lyusupov/SoftRF/software/firmware/binaries/RP2040/README.md

```

$ picotool info -a SoftRF-firmware-v1.0-RP2040.uf2 
File SoftRF-firmware-v1.0-RP2040.uf2:

Program Information
 name:          SoftRF
 version:       1.0
 web site:      https://github.com/lyusupov/SoftRF
 description:   Multifunctional, compatible DIY general aviation proximity awareness system
 binary start:  0x10000000
 binary end:    0x100292c8

Fixed Pin Information
 0:   Console TX
 1:   Console RX
 2:   I2C SDA
 3:   I2C SCL
 4:   GNSS TX
 5:   GNSS RX
 6:   GNSS PPS
 10:  SX1262 SCK
 11:  SX1262 MOSI
 12:  SX1262 MISO
 13:  SX1262 SS
 14:  SX1262 RST
 15:  SX1262 BUSY
 22:  GNSS RST
 25:  RF ANT PWR
 29:  SX1262 DIO1

Build Information
 build date:  Mar 16 2022

```
