lyusupov/SoftRF/software/firmware/binaries/nRF52840/SoftRF/MassStorage/README.md

Suffix|Notes
---|---
.uf2| use this file in conjunction with genuine [**SoftRF Badge** enclosure](https://github.com/lyusupov/SoftRF/tree/master/case/Badge)
-180.uf2| the screen is rotated 180 degrees to fit the LilyGO case for the T-Echo board
