lyusupov/SoftRF/documents/images/2p_xcs_map.jpg

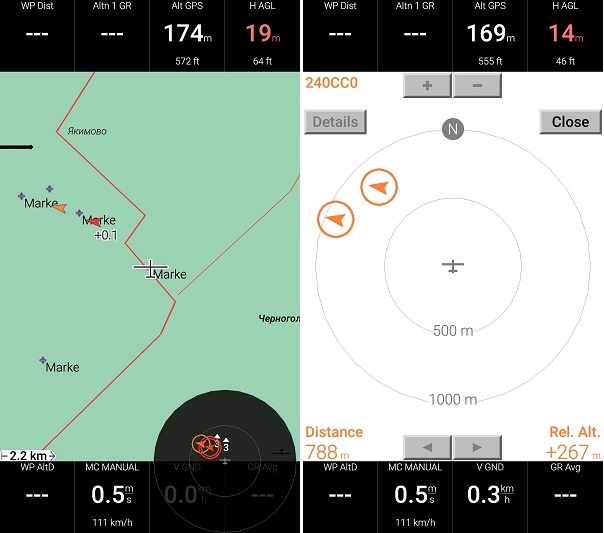
documents/images/2p_xcs_map.jpg
