lyusupov/SoftRF/documents/images/2p_xcs_monitor.jpg

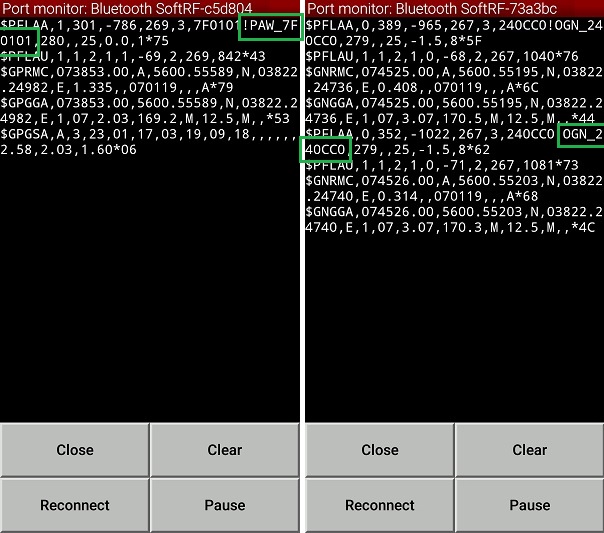
documents/images/2p_xcs_monitor.jpg
