lyusupov/SoftRF/documents/images/2p_xcs_traffic.jpg

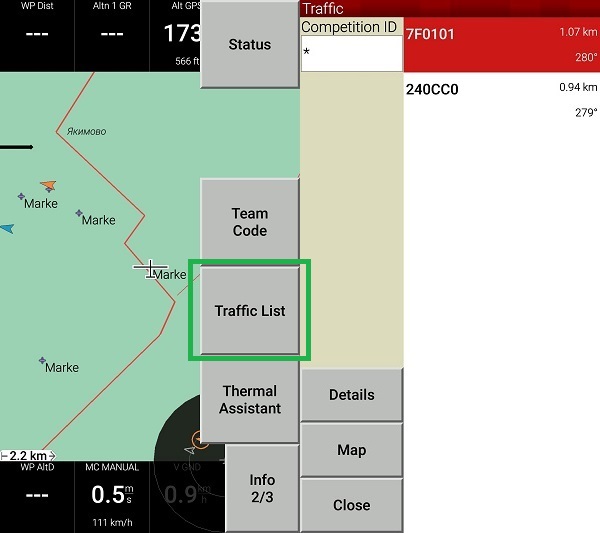
documents/images/2p_xcs_traffic.jpg
