lyusupov/SoftRF/documents/images/Airventure-1.jpg

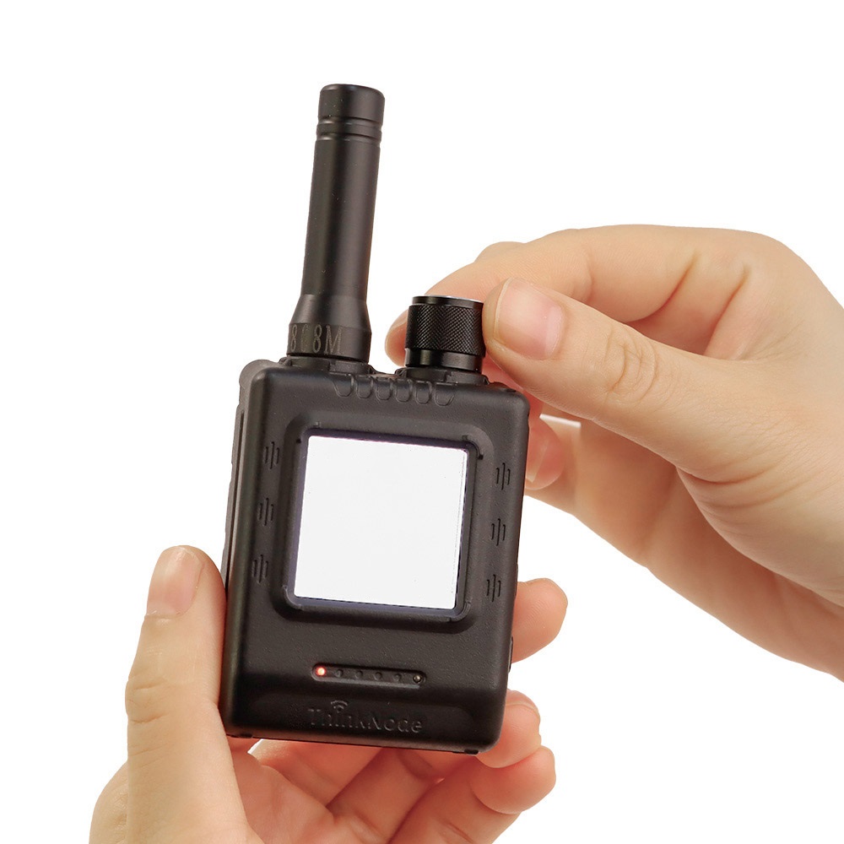
documents/images/Airventure-1.jpg
