lyusupov/SoftRF/documents/images/Airventure-2.jpg

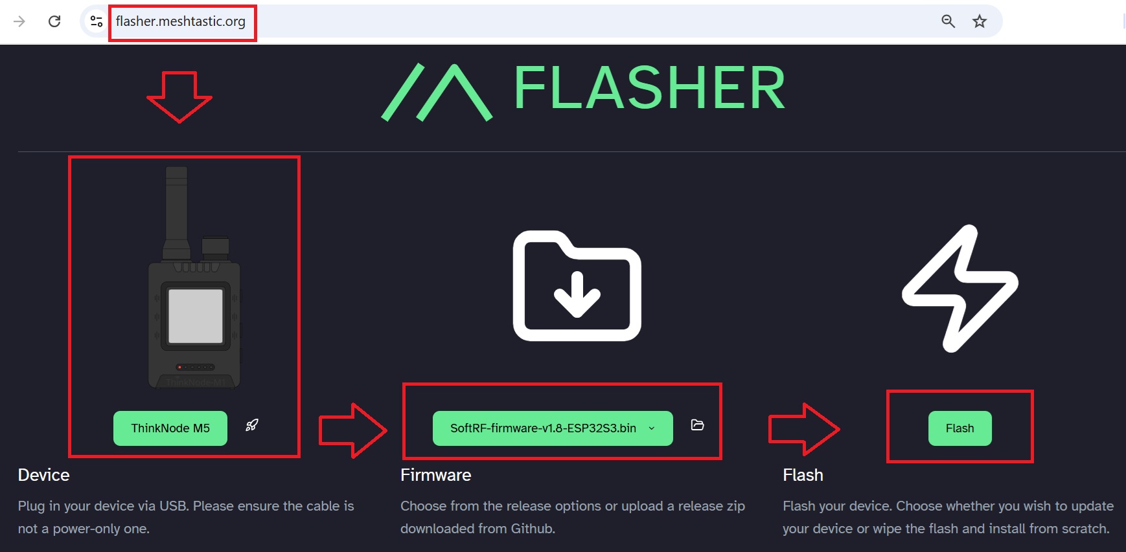
documents/images/Airventure-2.jpg
