lyusupov/SoftRF/documents/images/ant_1.jpg

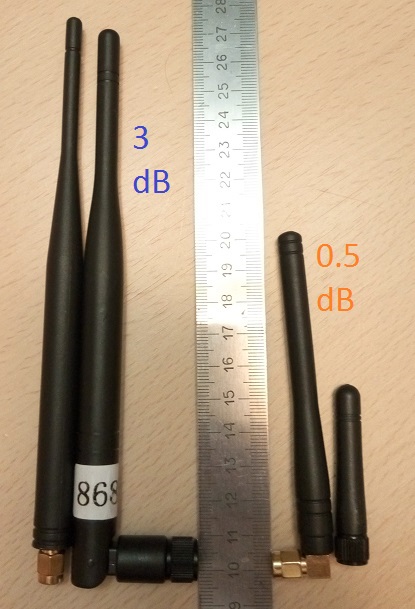
documents/images/ant_1.jpg
