lyusupov/SoftRF/documents/images/ant_2.jpg

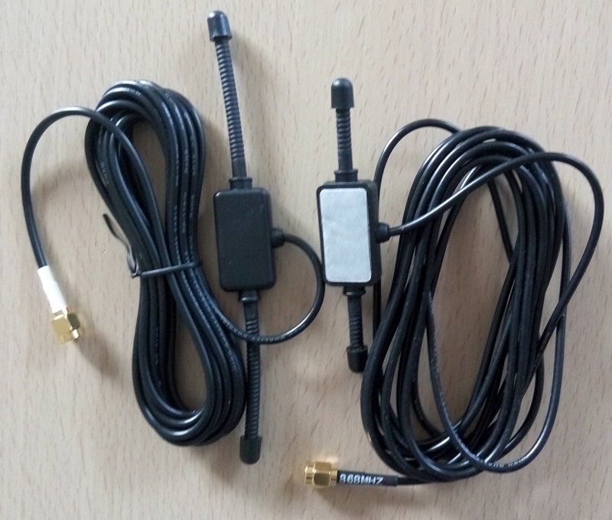
documents/images/ant_2.jpg
