lyusupov/SoftRF/documents/images/aw-snapshot.JPG

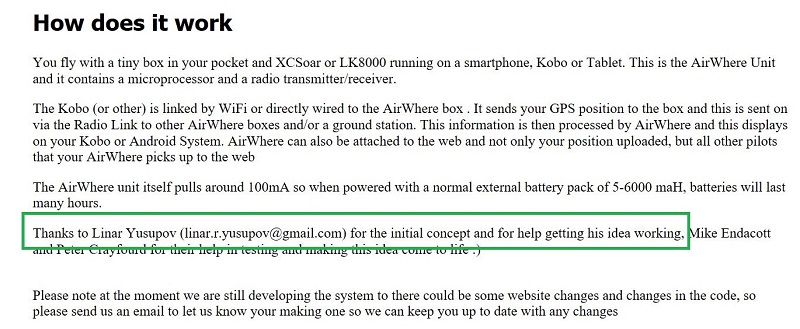
documents/images/aw-snapshot.JPG
