lyusupov/SoftRF/documents/images/BFF-1.jpg

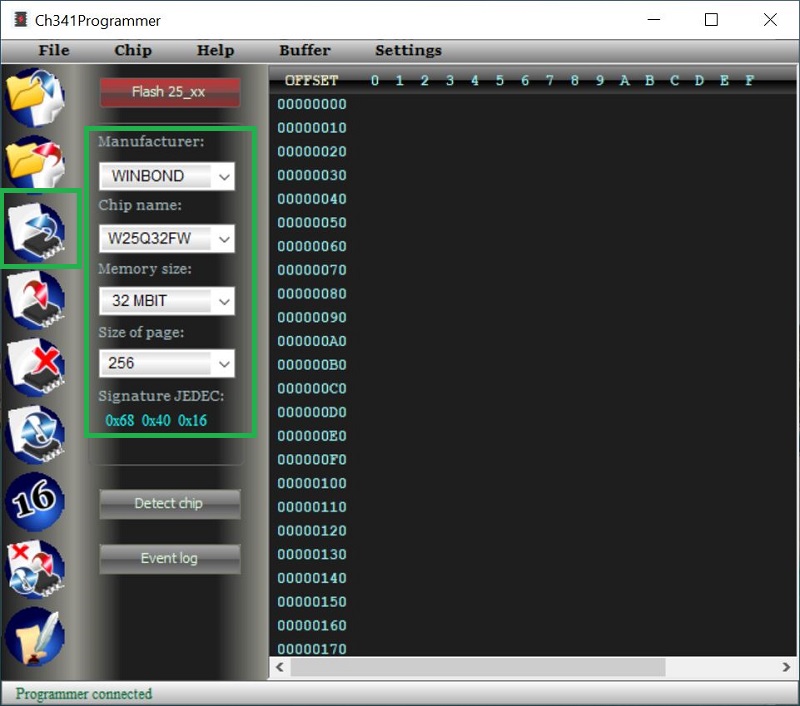
documents/images/BFF-1.jpg
