lyusupov/SoftRF/documents/images/BFF-3.jpg

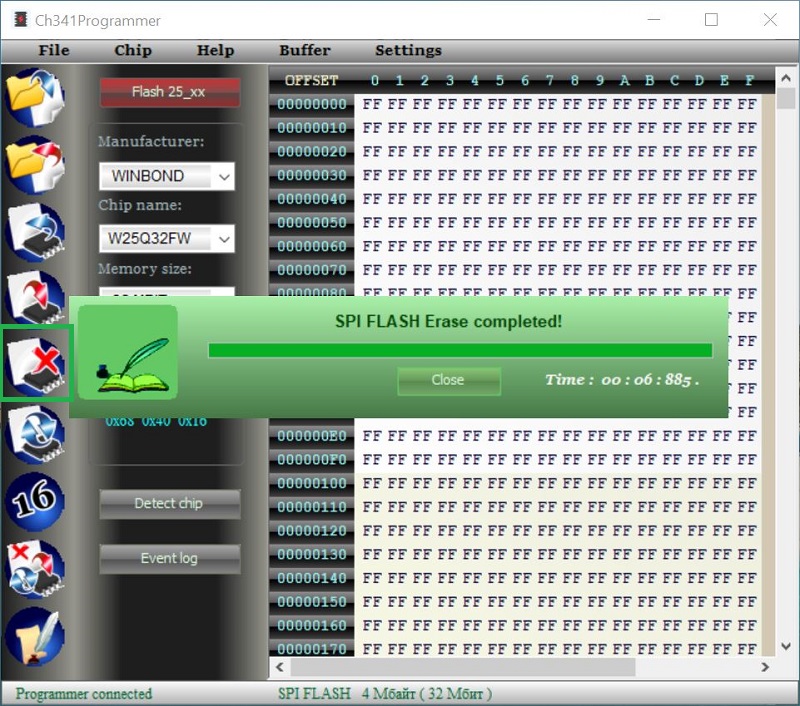
documents/images/BFF-3.jpg
