lyusupov/SoftRF/documents/images/BFF-4.jpg

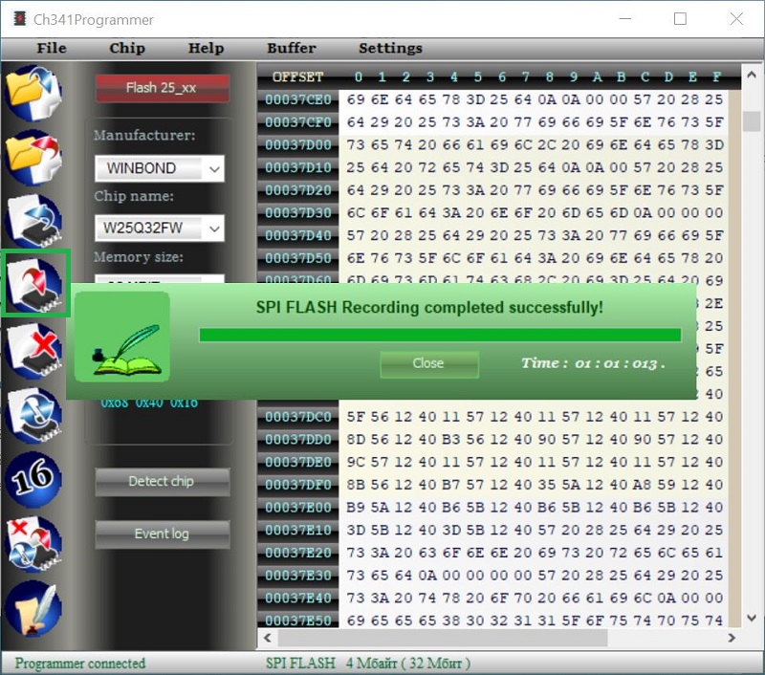
documents/images/BFF-4.jpg
