lyusupov/SoftRF/documents/images/BFF-6.jpg

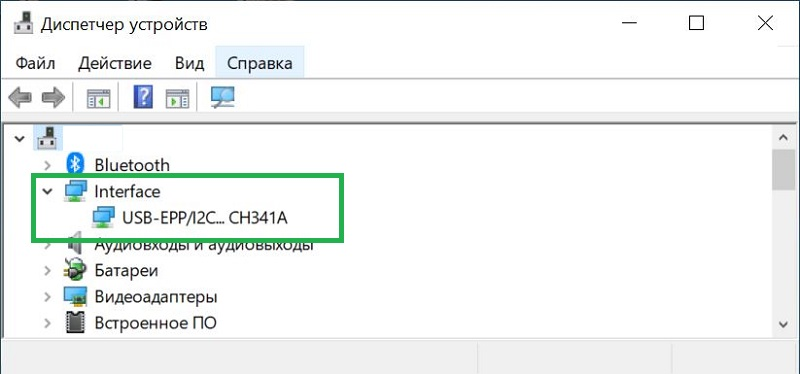
documents/images/BFF-6.jpg
