lyusupov/SoftRF/documents/images/BFF-7.jpg

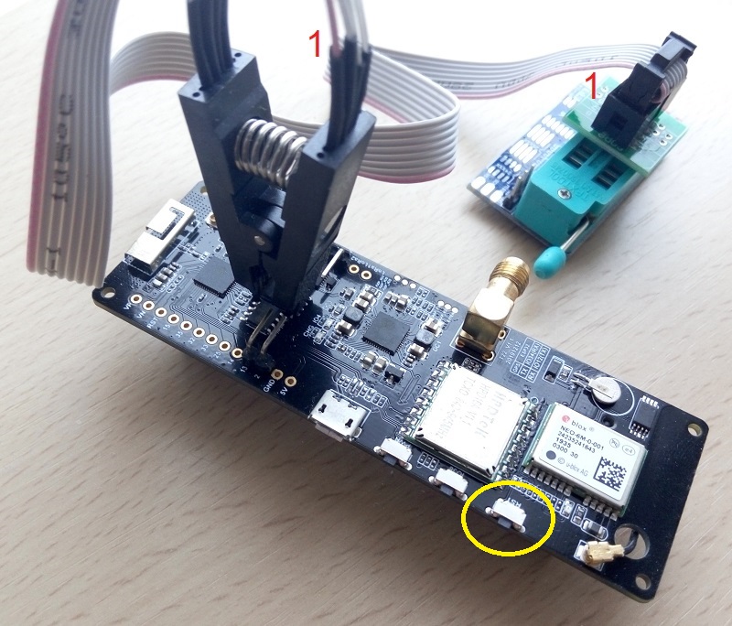
documents/images/BFF-7.jpg
