lyusupov/SoftRF/documents/images/bom/epaper-hat.jpg

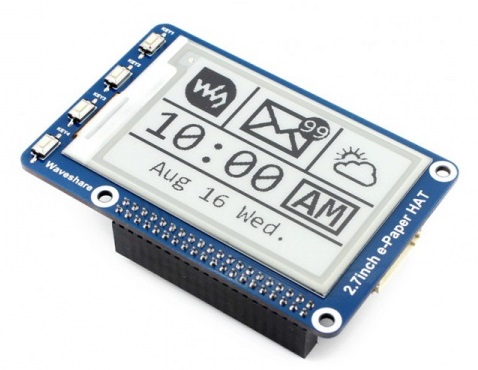
documents/images/bom/epaper-hat.jpg
