lyusupov/SoftRF/documents/images/bom/wspicoepaper27.jpg

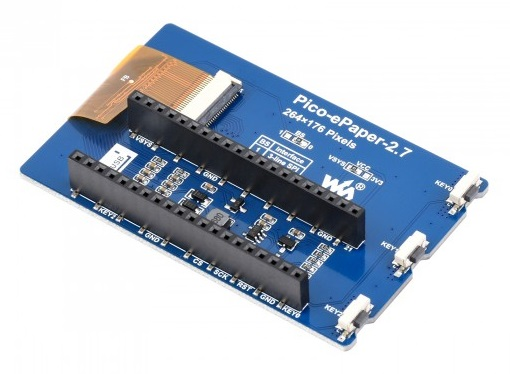
documents/images/bom/wspicoepaper27.jpg
