lyusupov/SoftRF/documents/images/Bracelet-4.jpg

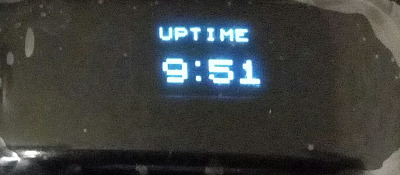
documents/images/Bracelet-4.jpg
