lyusupov/SoftRF/documents/images/Card3-2.jpg

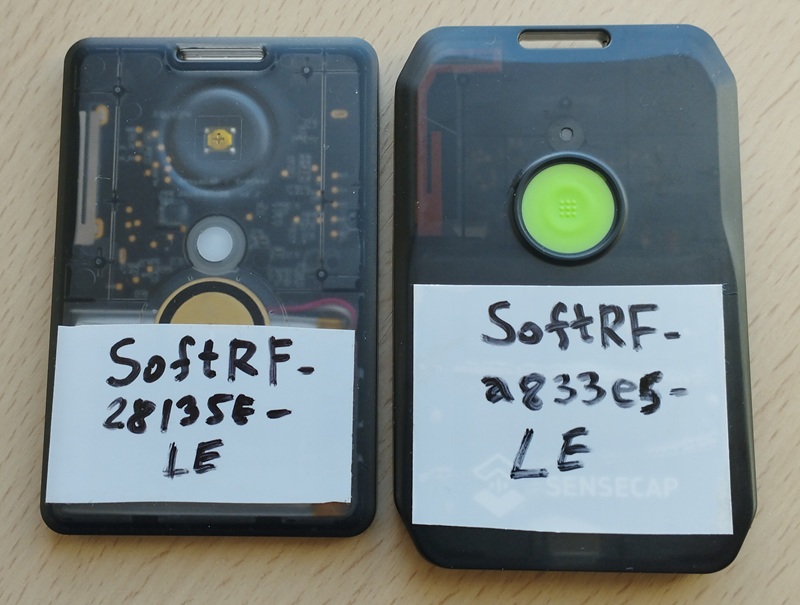
documents/images/Card3-2.jpg
