lyusupov/SoftRF/documents/images/Card3-3.jpg

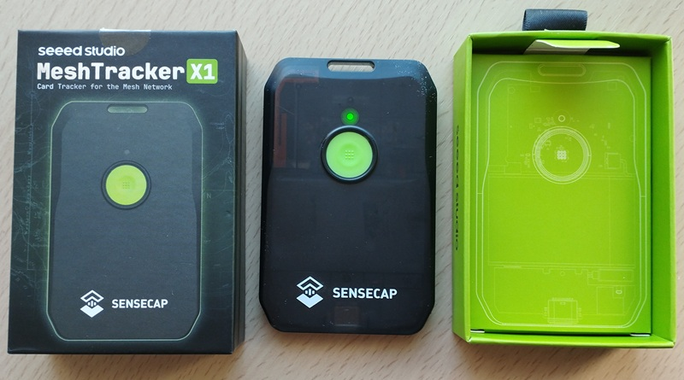
documents/images/Card3-3.jpg
