lyusupov/SoftRF/documents/images/Card-2.png

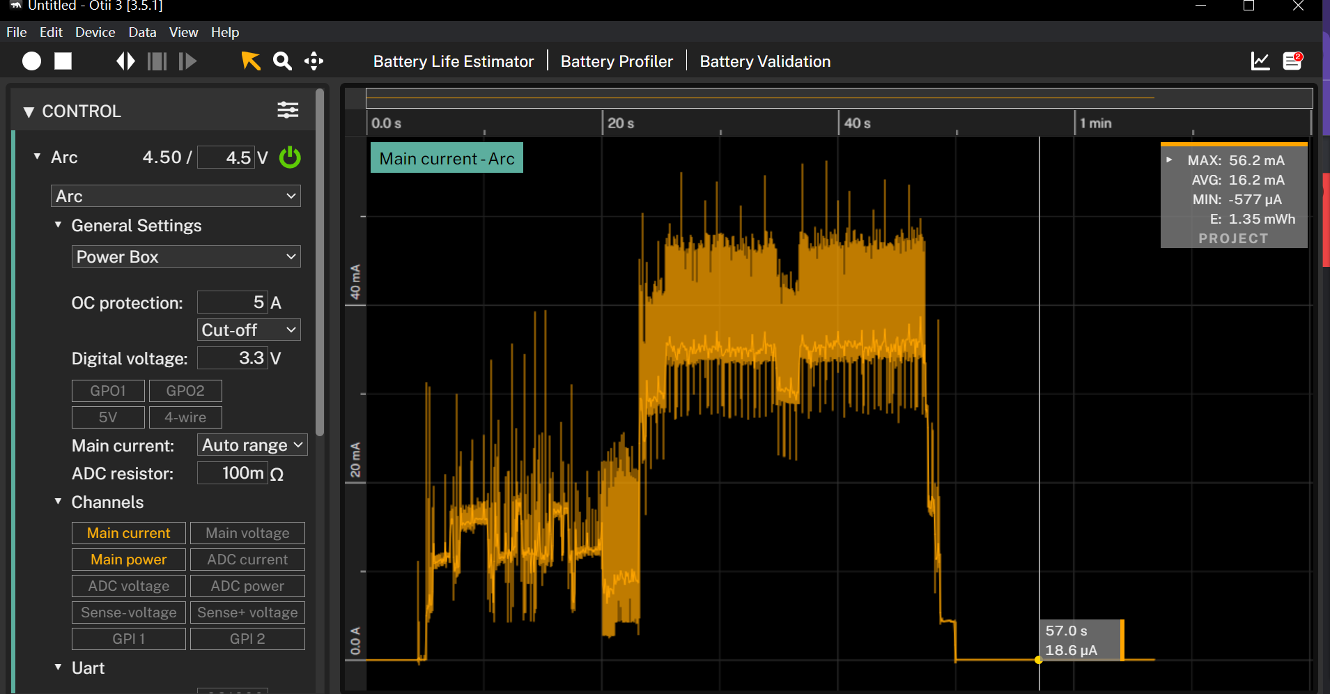
documents/images/Card-2.png
