lyusupov/SoftRF/documents/images/Card-3.jpg

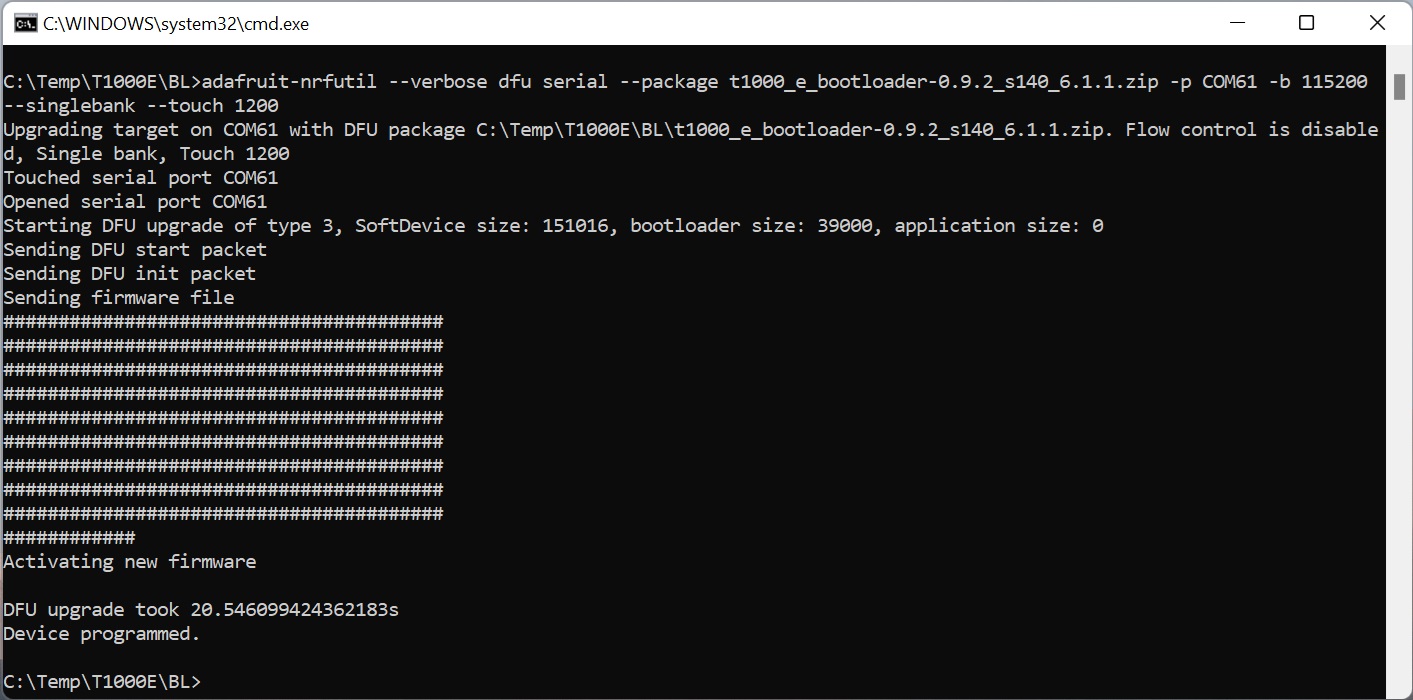
documents/images/Card-3.jpg
