lyusupov/SoftRF/documents/images/Card-7.jpg

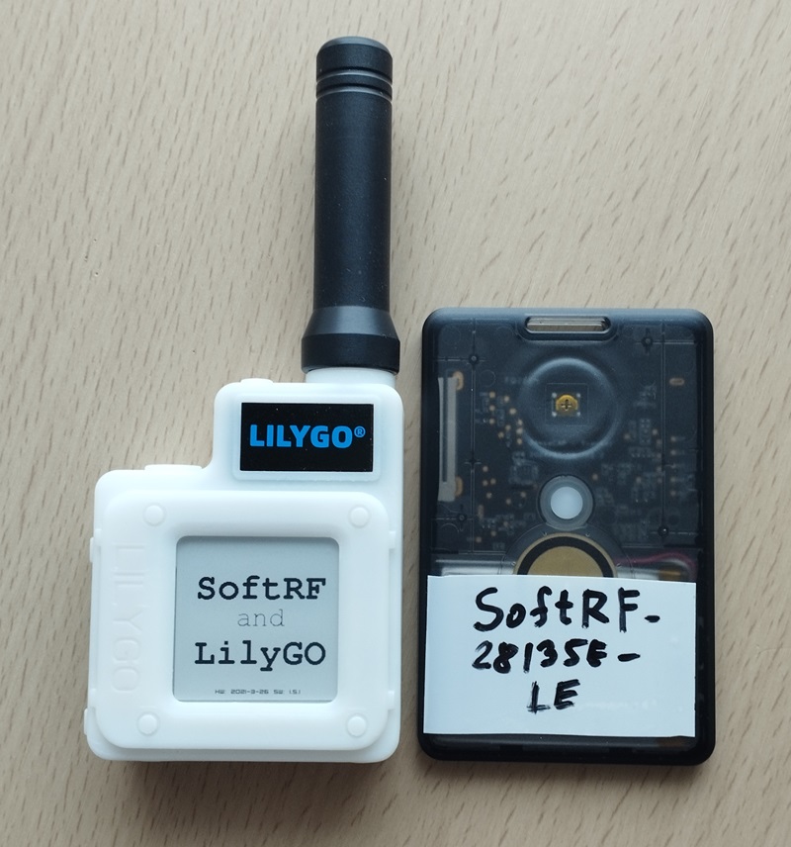
documents/images/Card-7.jpg
