lyusupov/SoftRF/documents/images/Card-8.jpg

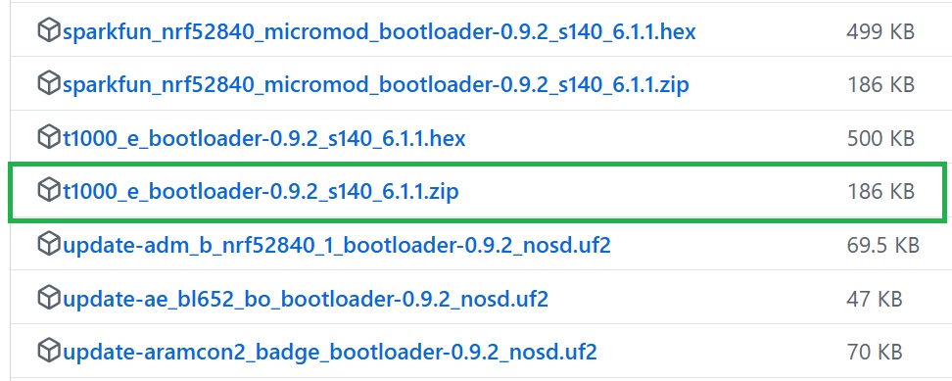
documents/images/Card-8.jpg
