lyusupov/SoftRF/documents/images/Card-10.jpg

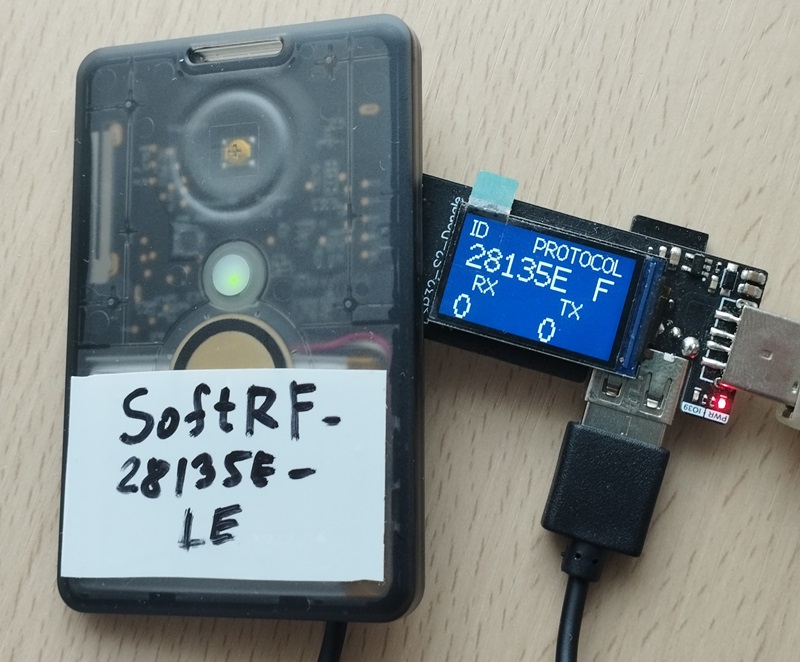
documents/images/Card-10.jpg
