lyusupov/SoftRF/documents/images/Cozy-4.jpg

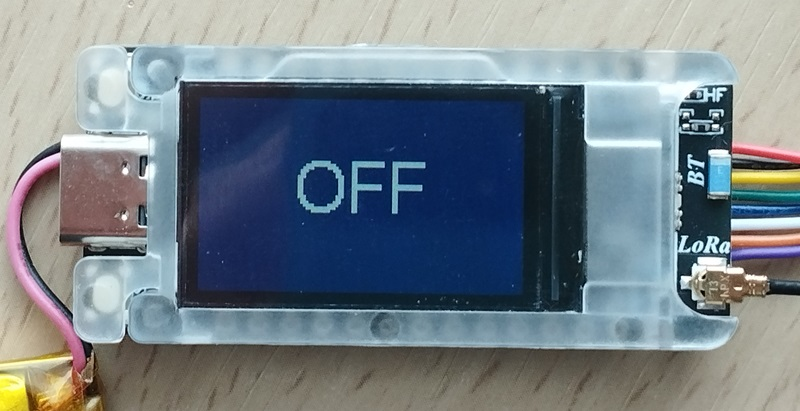
documents/images/Cozy-4.jpg
