lyusupov/SoftRF/documents/images/dump1090_TXTUI.JPG

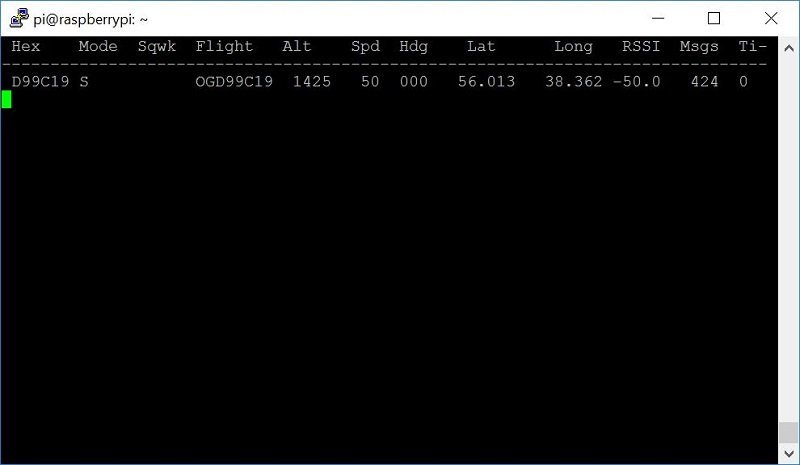
documents/images/dump1090_TXTUI.JPG
