lyusupov/SoftRF/documents/images/duo-1.jpg

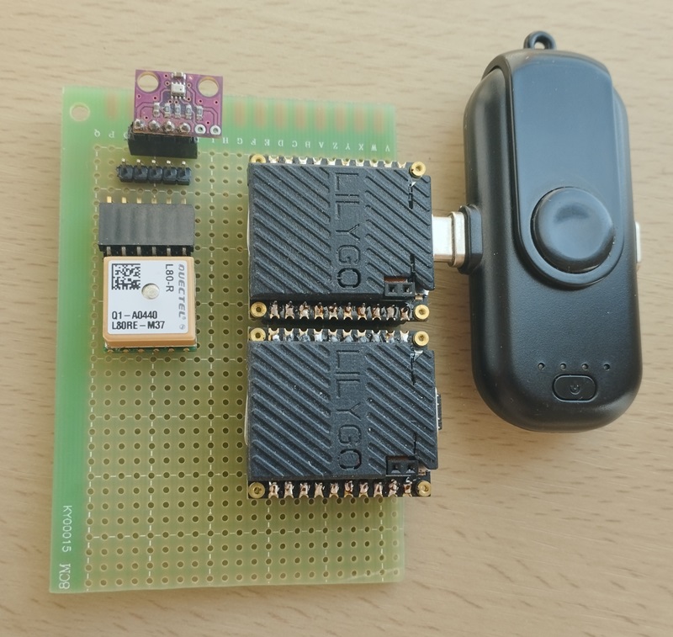
documents/images/duo-1.jpg
