lyusupov/SoftRF/documents/images/duo-4.jpg

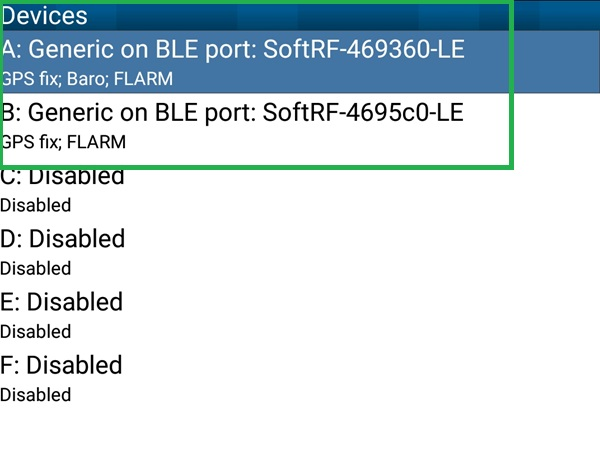
documents/images/duo-4.jpg
