lyusupov/SoftRF/documents/images/ES-10.jpg

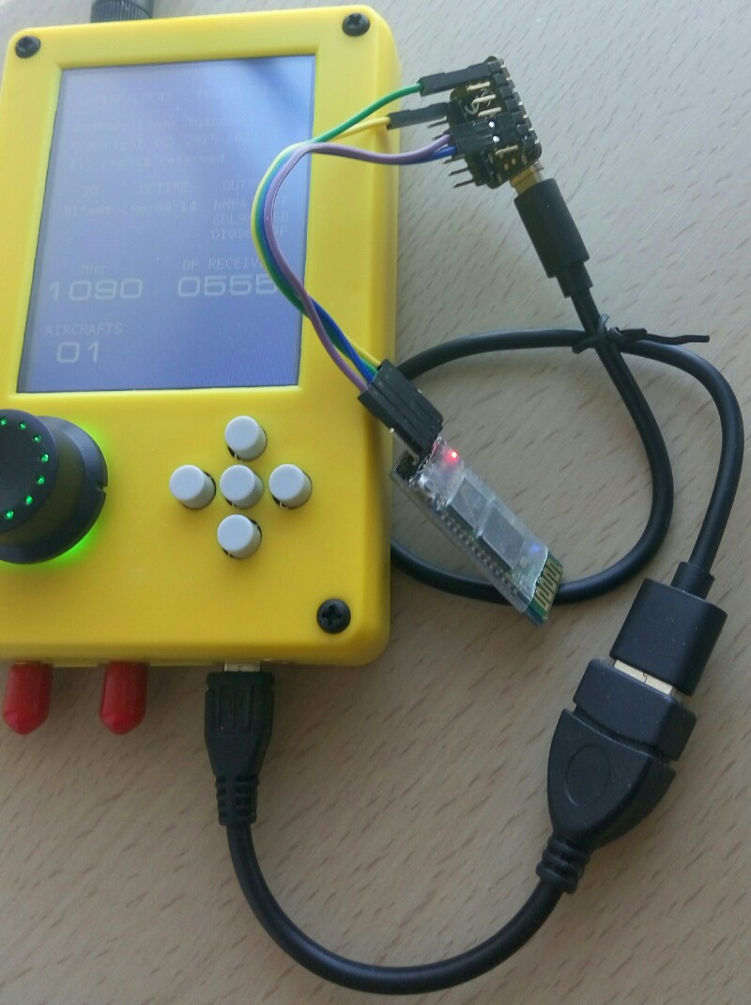
documents/images/ES-10.jpg
