lyusupov/SoftRF/documents/images/ES-11.jpg

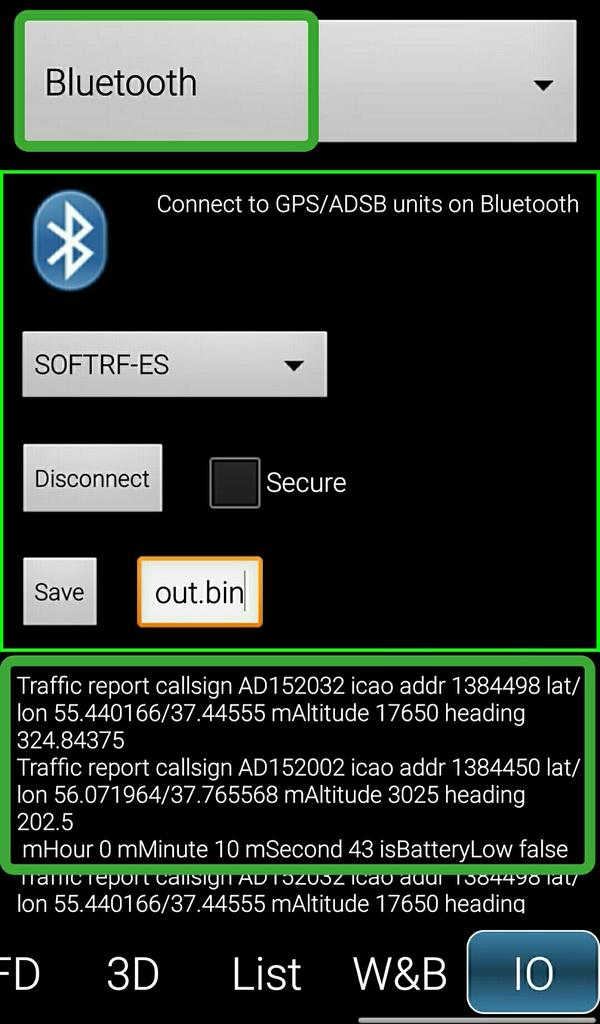
documents/images/ES-11.jpg
