lyusupov/SoftRF/documents/images/ES-12.jpg

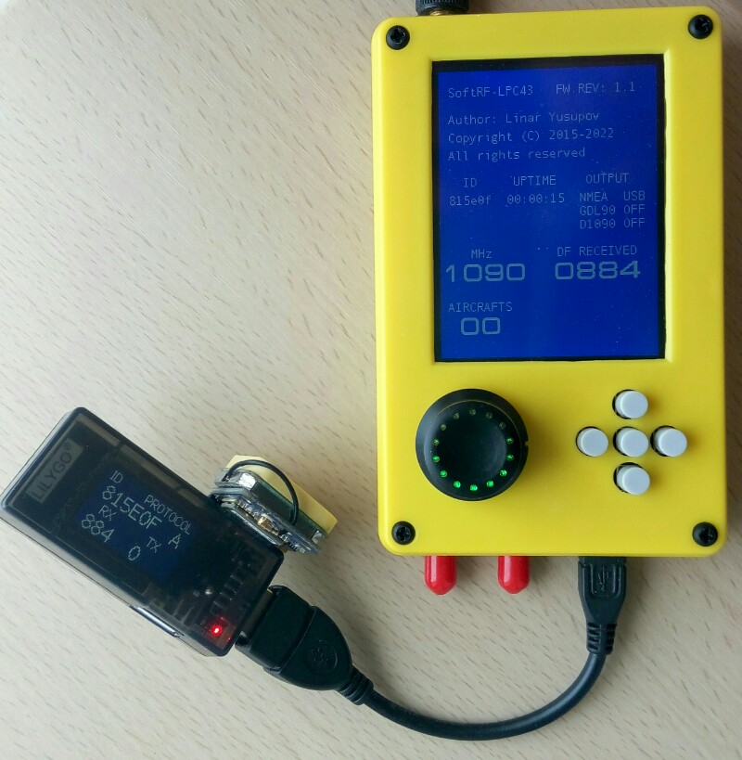
documents/images/ES-12.jpg
