lyusupov/SoftRF/documents/images/ESP32-NODEMCU-ADAPTER-1.jpg

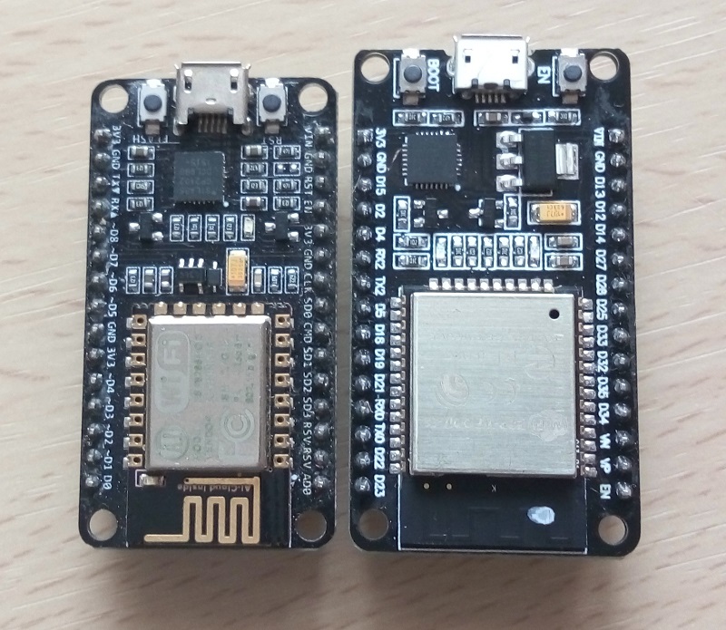
documents/images/ESP32-NODEMCU-ADAPTER-1.jpg
