lyusupov/SoftRF/documents/images/ESP32-NODEMCU-ADAPTER-5.jpg

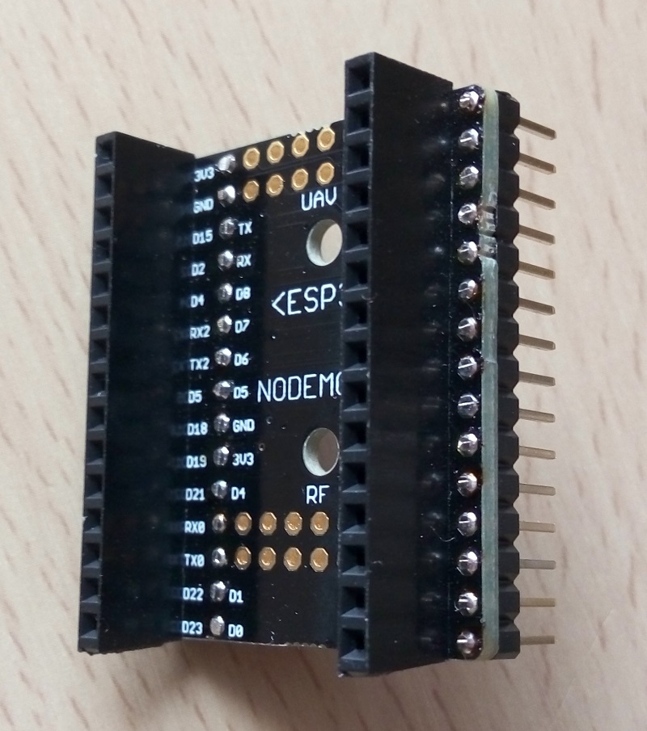
documents/images/ESP32-NODEMCU-ADAPTER-5.jpg
