lyusupov/SoftRF/documents/images/ESP32-NODEMCU-ADAPTER-6.jpg

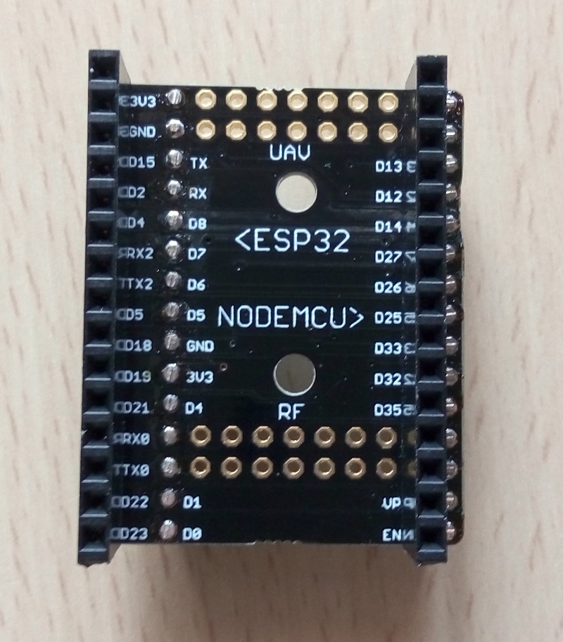
documents/images/ESP32-NODEMCU-ADAPTER-6.jpg
