lyusupov/SoftRF/documents/images/ESP32-NODEMCU-ADAPTER-13.jpg

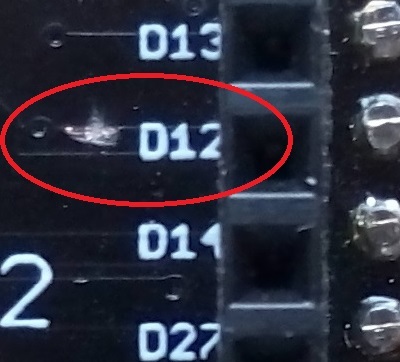
documents/images/ESP32-NODEMCU-ADAPTER-13.jpg
