lyusupov/SoftRF/documents/images/ESP32-NODEMCU-ADAPTER-14.jpg

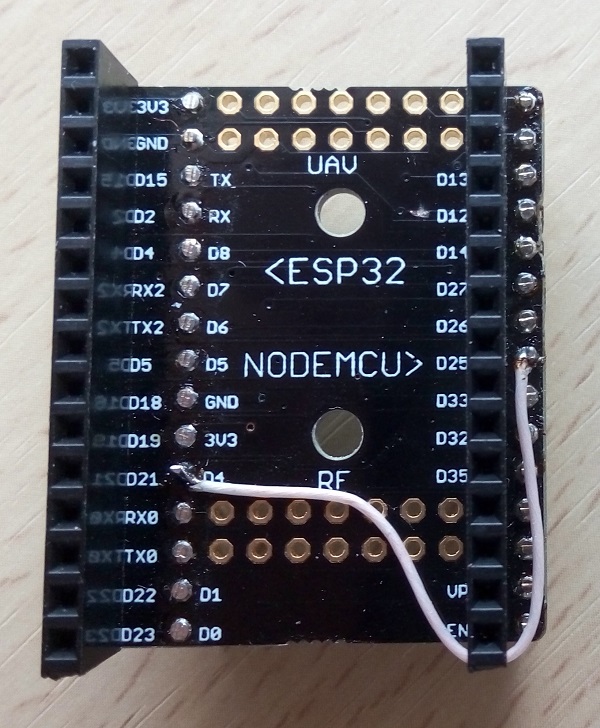
documents/images/ESP32-NODEMCU-ADAPTER-14.jpg
