lyusupov/SoftRF/documents/images/ESP32-NODEMCU-ADAPTER-16.jpg

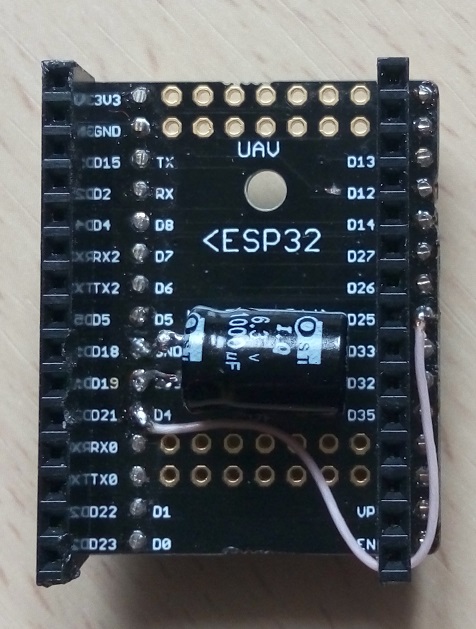
documents/images/ESP32-NODEMCU-ADAPTER-16.jpg
