lyusupov/SoftRF/documents/images/ESP32-NODEMCU-ADAPTER-PCB.JPG

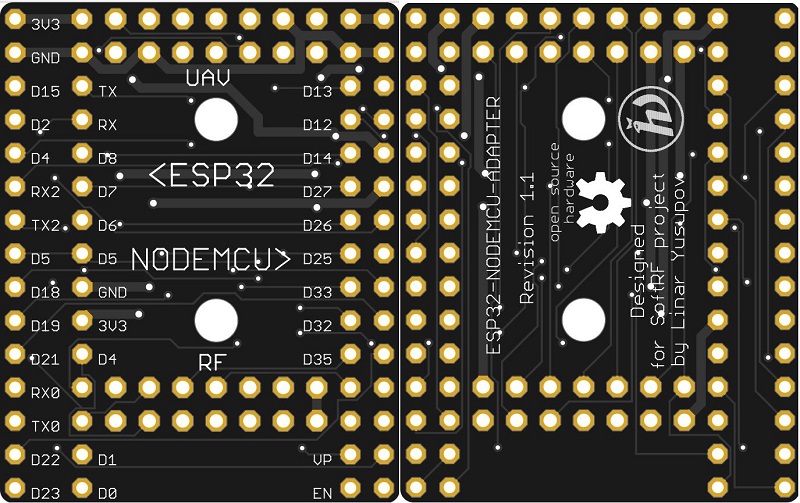
documents/images/ESP32-NODEMCU-ADAPTER-PCB.JPG
