lyusupov/SoftRF/documents/images/ESP32_WIFI_CALIB.jpg

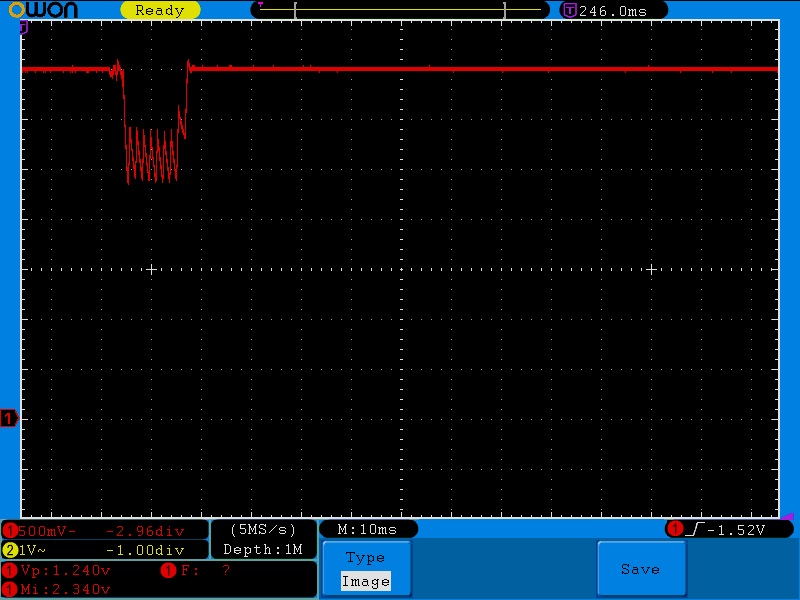
documents/images/ESP32_WIFI_CALIB.jpg
