lyusupov/SoftRF/documents/images/frontview_camera.jpg

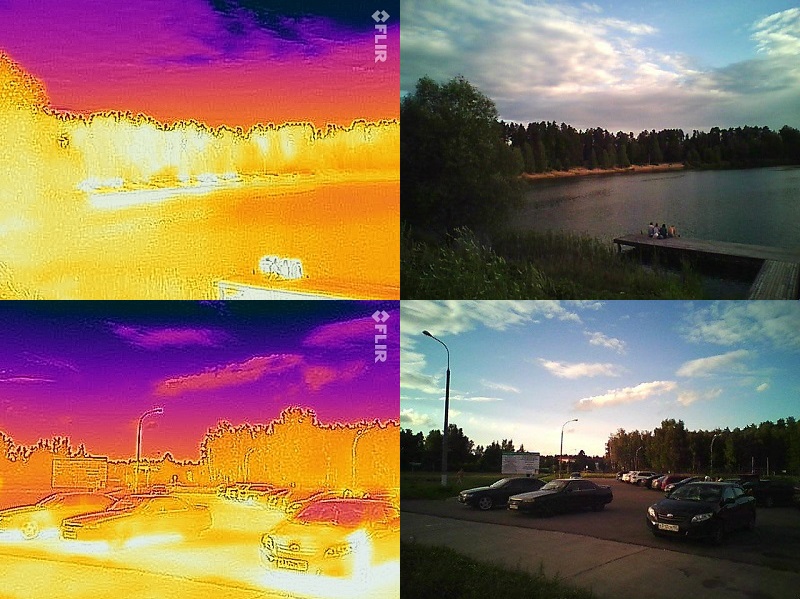
documents/images/frontview_camera.jpg
