lyusupov/SoftRF/documents/images/Gizmo-3.jpg

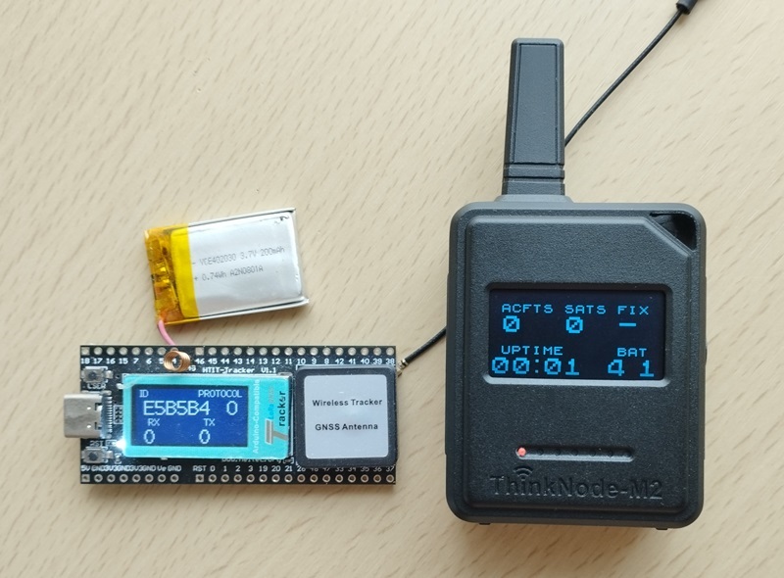
documents/images/Gizmo-3.jpg
