lyusupov/SoftRF/documents/images/GKRCH-868.JPG

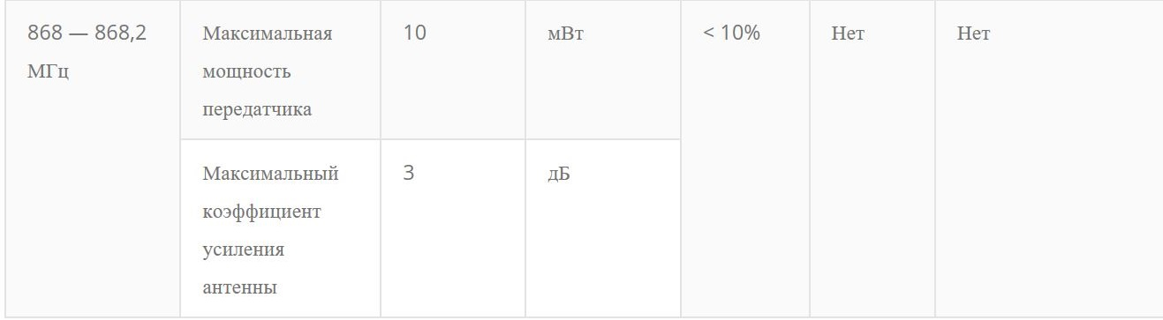
documents/images/GKRCH-868.JPG
