lyusupov/SoftRF/documents/images/ham-2.jpg

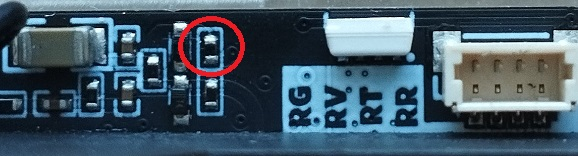
documents/images/ham-2.jpg
