lyusupov/SoftRF/documents/images/ham-4.jpg

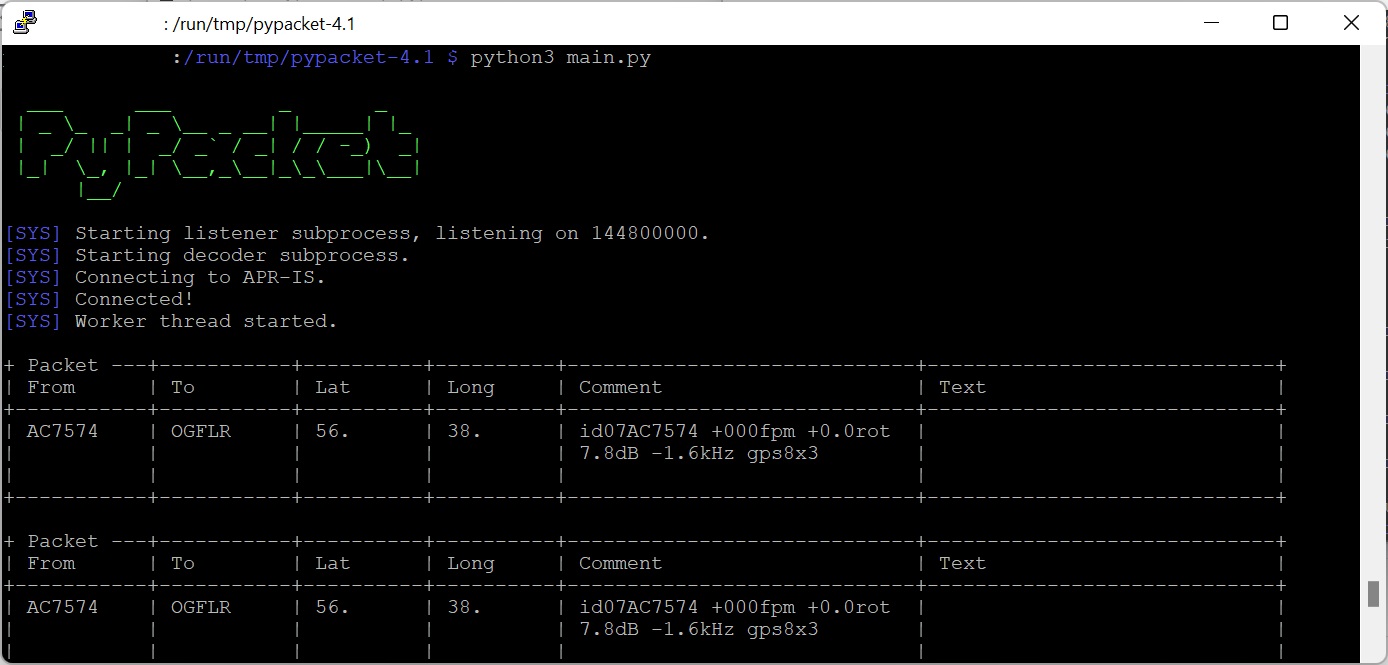
documents/images/ham-4.jpg
