lyusupov/SoftRF/documents/images/ham-5.jpg

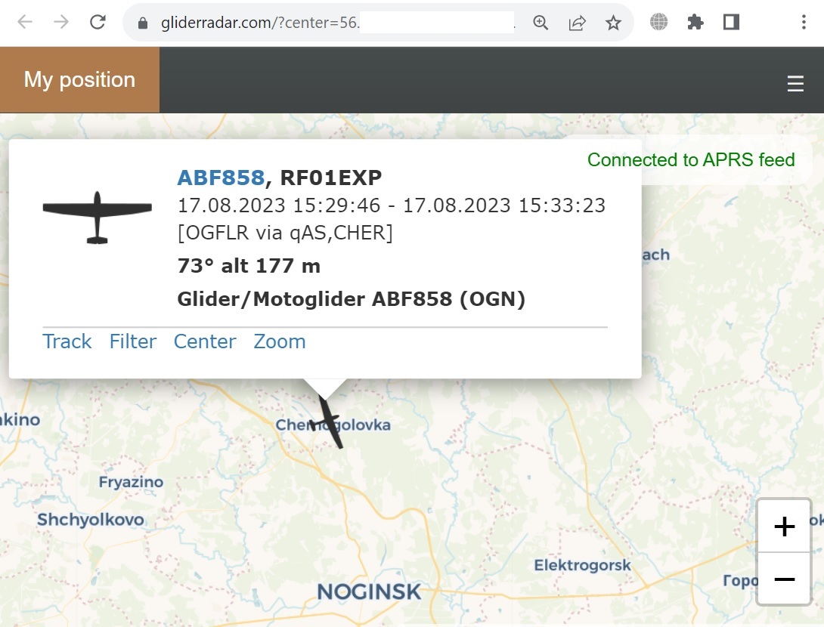
documents/images/ham-5.jpg
