lyusupov/SoftRF/documents/images/ham-10.jpg

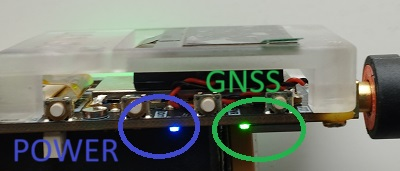
documents/images/ham-10.jpg
