lyusupov/SoftRF/documents/images/ham-12.jpg

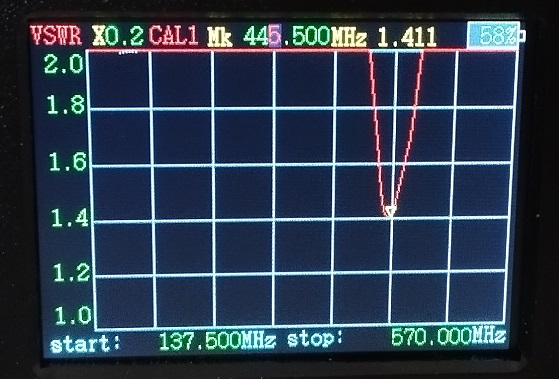
documents/images/ham-12.jpg
