lyusupov/SoftRF/documents/images/ham-20.jpg

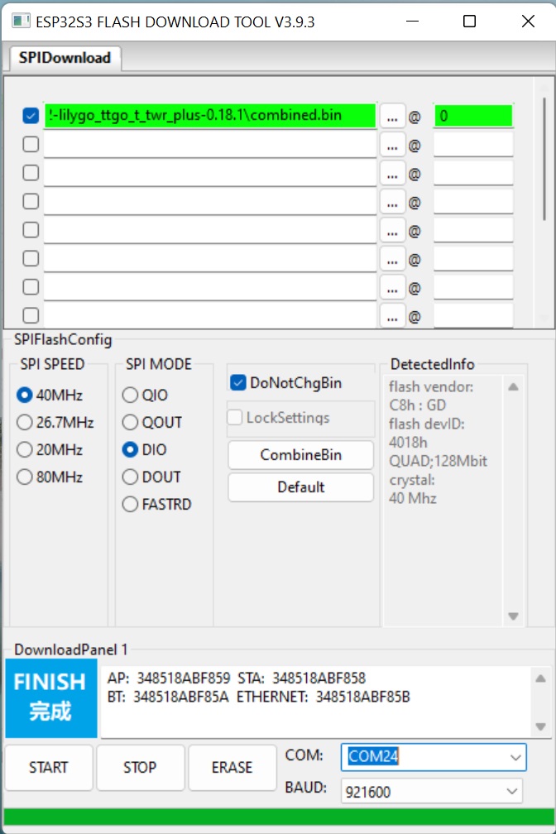
documents/images/ham-20.jpg
