lyusupov/SoftRF/documents/images/ham-29.jpg

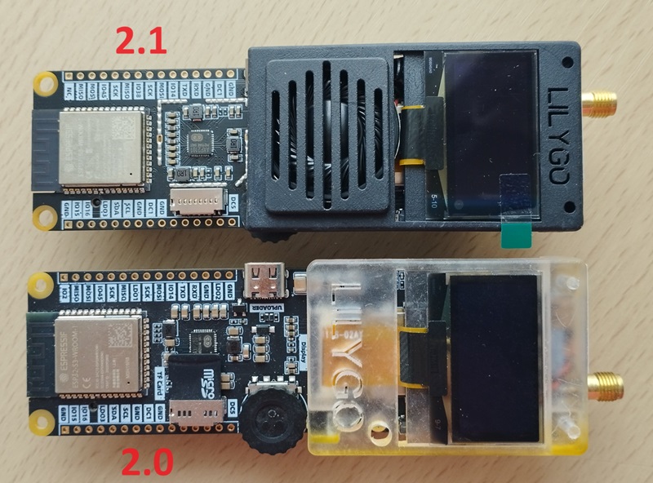
documents/images/ham-29.jpg
