lyusupov/SoftRF/documents/images/Handheld-1.jpg

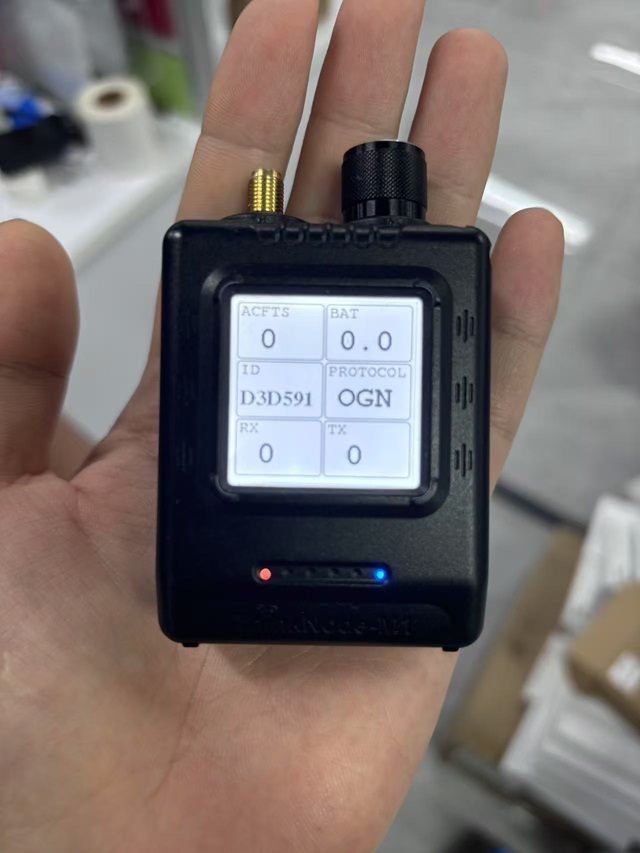
documents/images/Handheld-1.jpg
