lyusupov/SoftRF/documents/images/Handheld-2.jpg

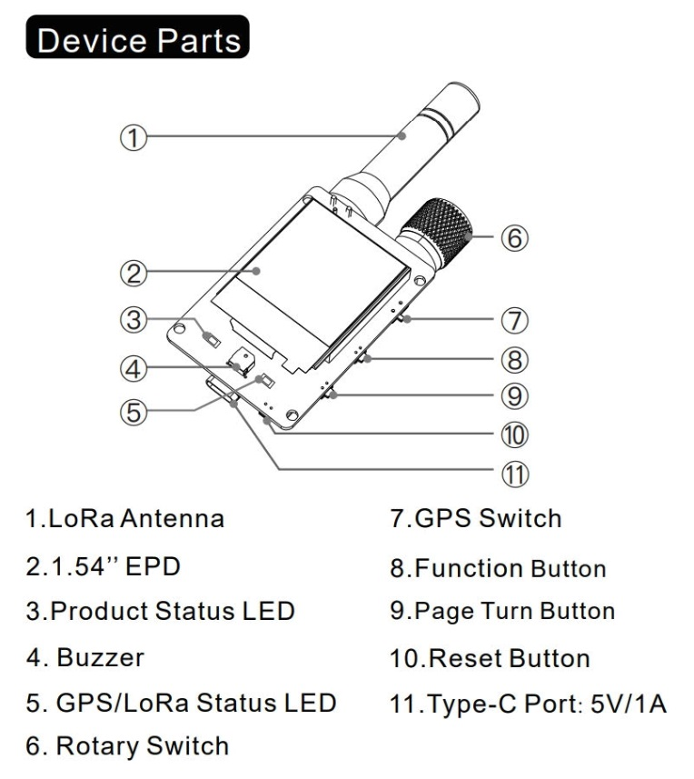
documents/images/Handheld-2.jpg
