lyusupov/SoftRF/documents/images/Handheld-6.jpg

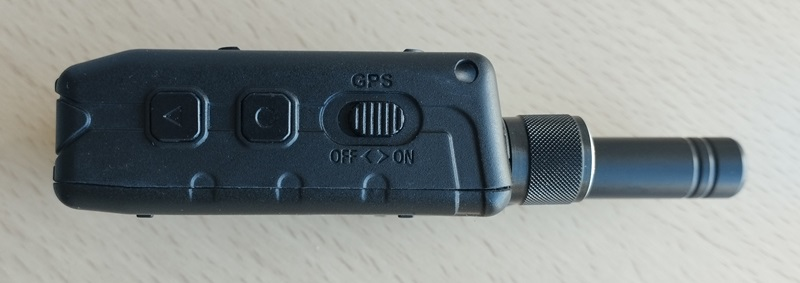
documents/images/Handheld-6.jpg
