lyusupov/SoftRF/documents/images/Labubu-1.jpg

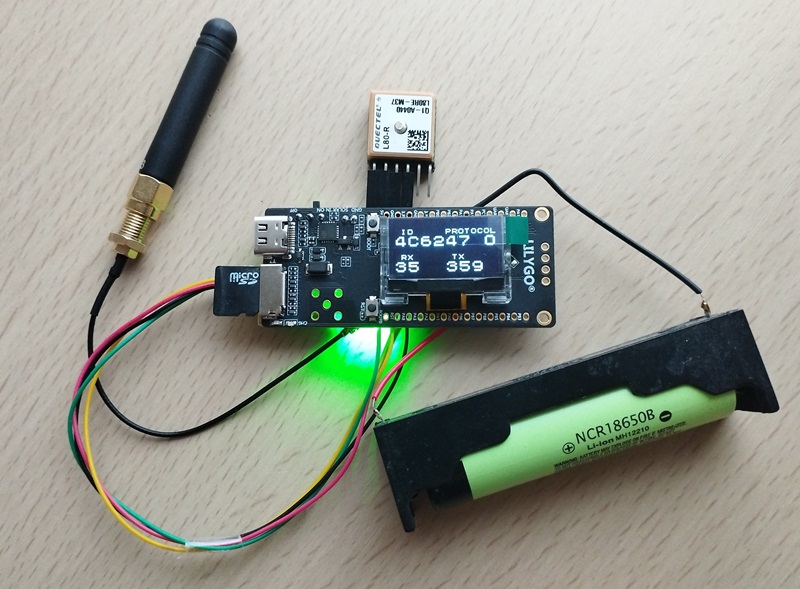
documents/images/Labubu-1.jpg
