lyusupov/SoftRF/documents/images/Lego-2.png

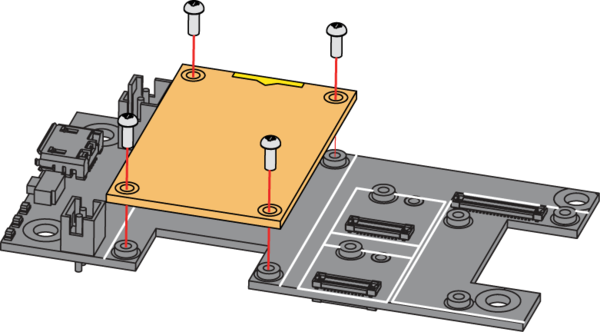
documents/images/Lego-2.png
