lyusupov/SoftRF/documents/images/Lego-4.png

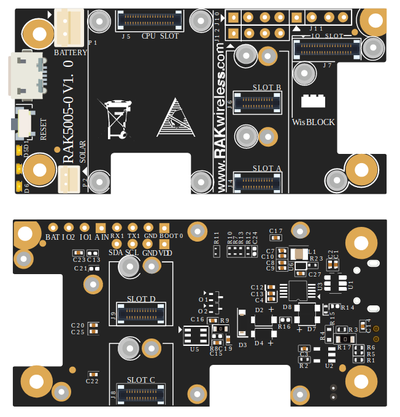
documents/images/Lego-4.png
