lyusupov/SoftRF/documents/images/lk8000.gif

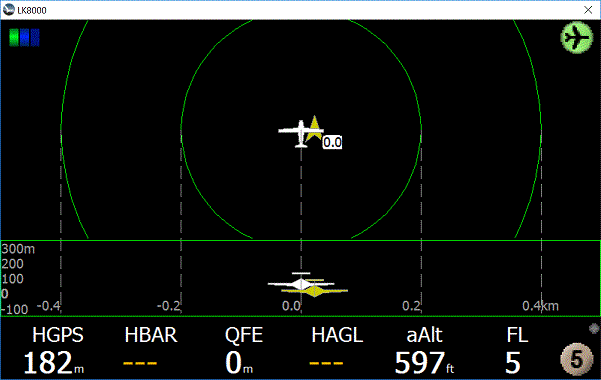
documents/images/lk8000.gif
