lyusupov/SoftRF/documents/images/midi-5.jpg

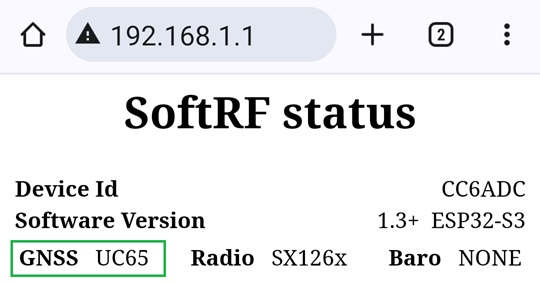
documents/images/midi-5.jpg
