lyusupov/SoftRF/documents/images/midi-7.jpg

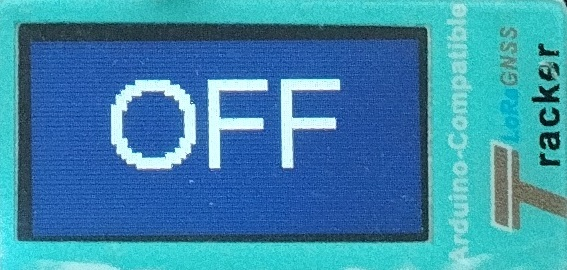
documents/images/midi-7.jpg
