lyusupov/SoftRF/documents/images/Mini-8.jpg

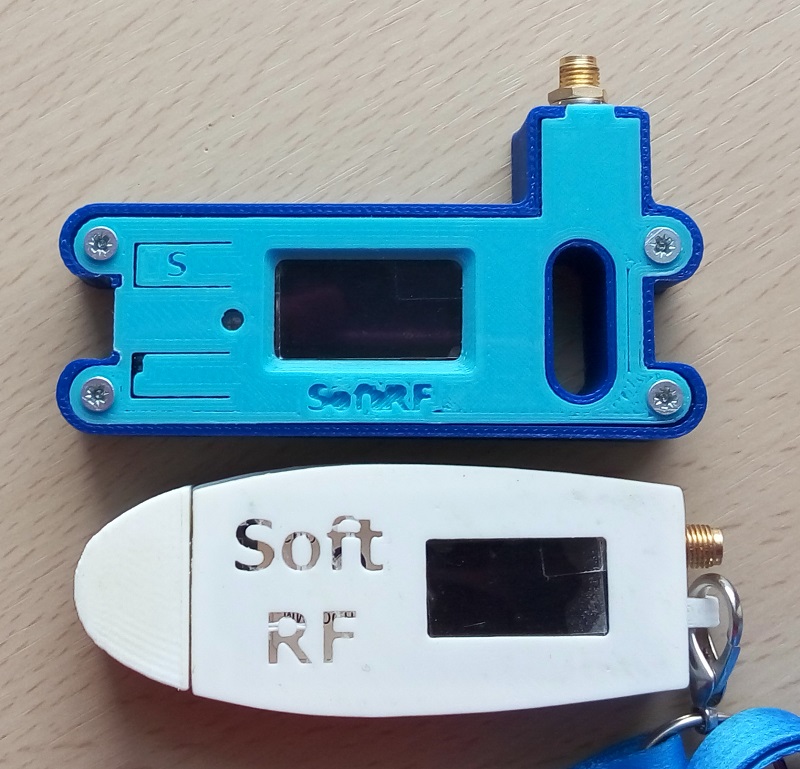
documents/images/Mini-8.jpg
