lyusupov/SoftRF/documents/images/Nano-5.jpg

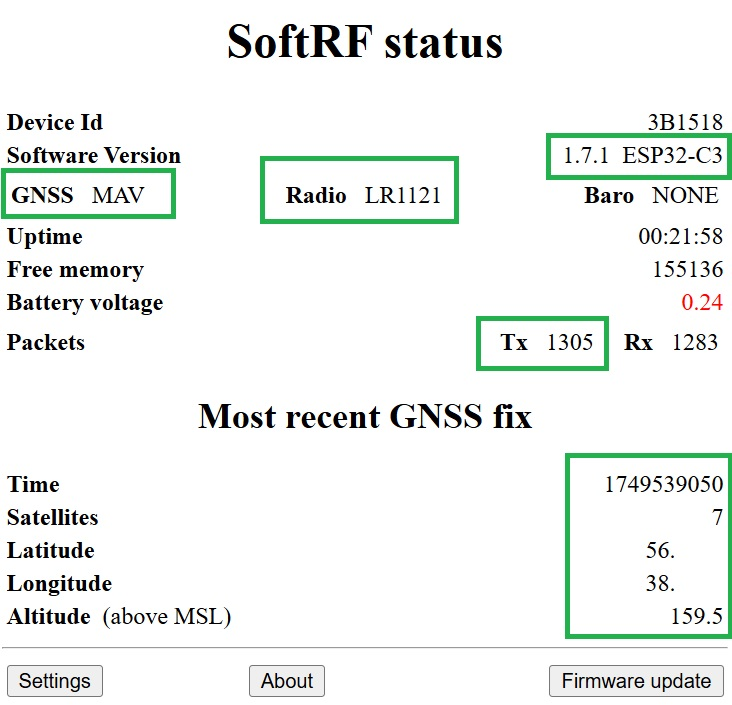
documents/images/Nano-5.jpg
