lyusupov/SoftRF/documents/images/Octave-3.jpg

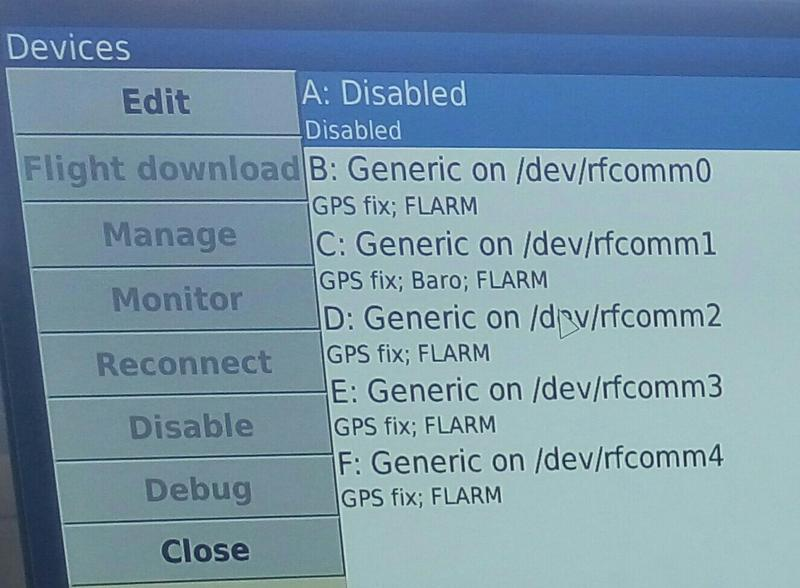
documents/images/Octave-3.jpg
