lyusupov/SoftRF/documents/images/ogn_3.jpg

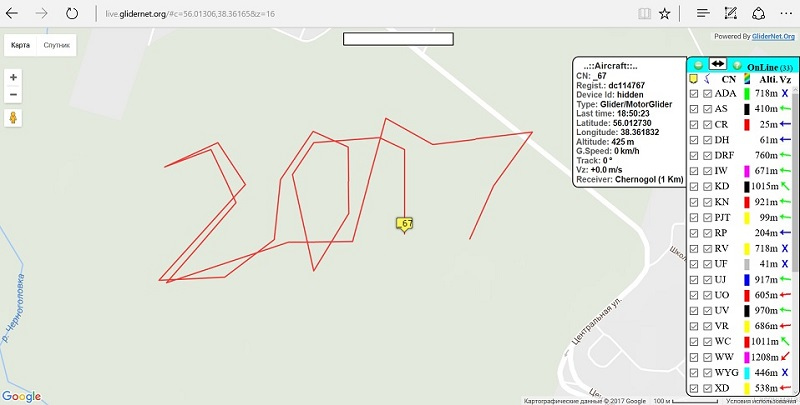
documents/images/ogn_3.jpg
