lyusupov/SoftRF/documents/images/pcb_2.jpg

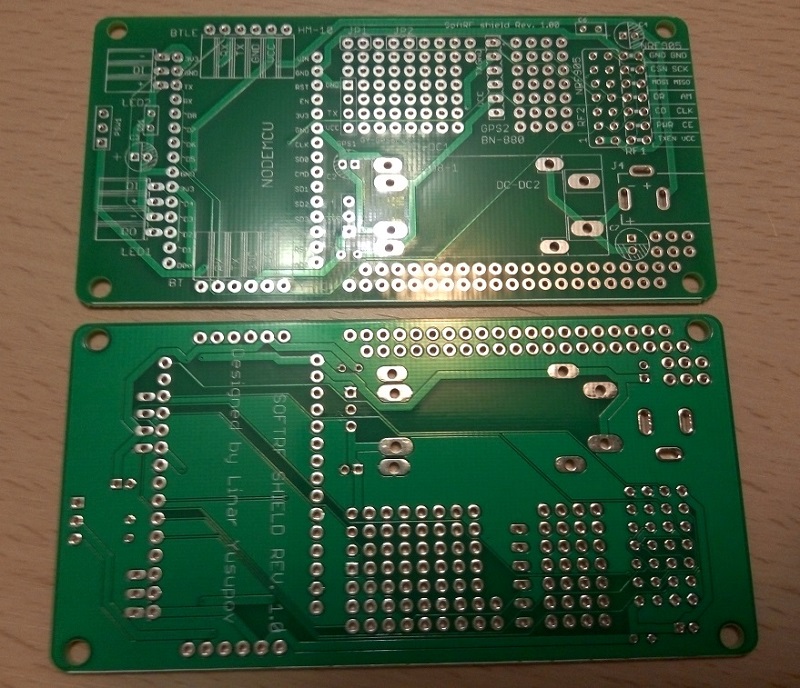
documents/images/pcb_2.jpg
