lyusupov/SoftRF/documents/images/poligon_1.gif

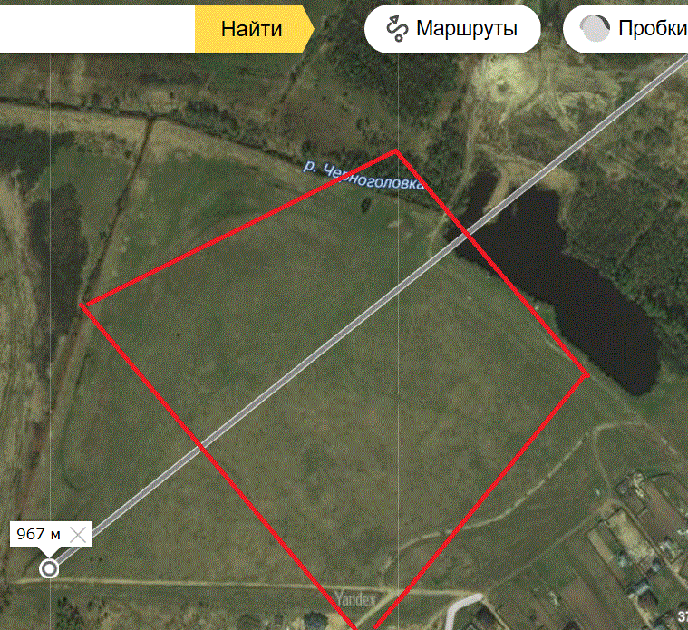
documents/images/poligon_1.gif
