lyusupov/SoftRF/documents/images/Prime2_fsgp2019_2.jpg

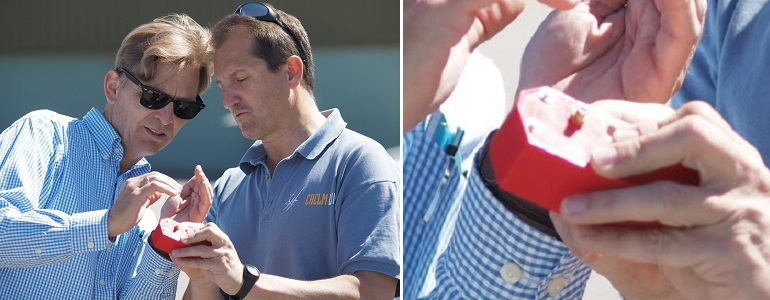
documents/images/Prime2_fsgp2019_2.jpg
