lyusupov/SoftRF/documents/images/Prime2_LR2021_2.jpg

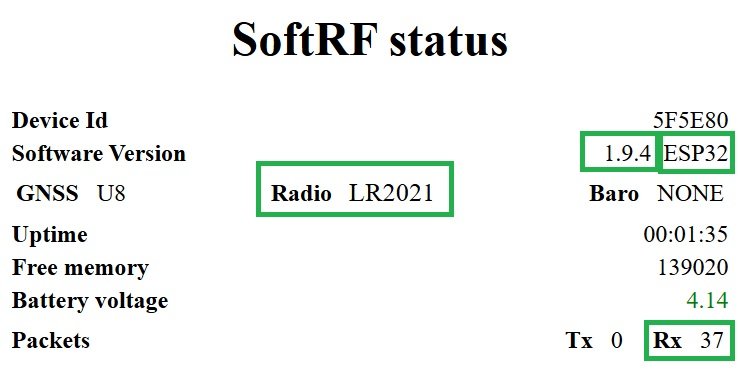
documents/images/Prime2_LR2021_2.jpg
