lyusupov/SoftRF/documents/images/Prime3-7.jpg

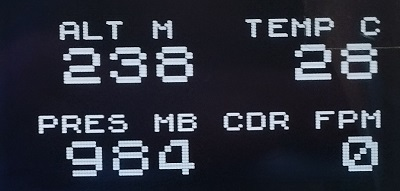
documents/images/Prime3-7.jpg
