lyusupov/SoftRF/documents/images/Prime3-8.jpg

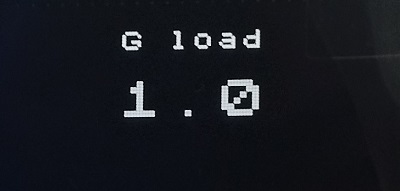
documents/images/Prime3-8.jpg
