lyusupov/SoftRF/documents/images/Prime3-10.jpg

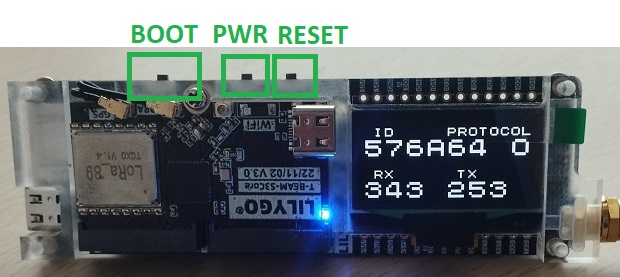
documents/images/Prime3-10.jpg
