lyusupov/SoftRF/documents/images/Prime3-11.jpg

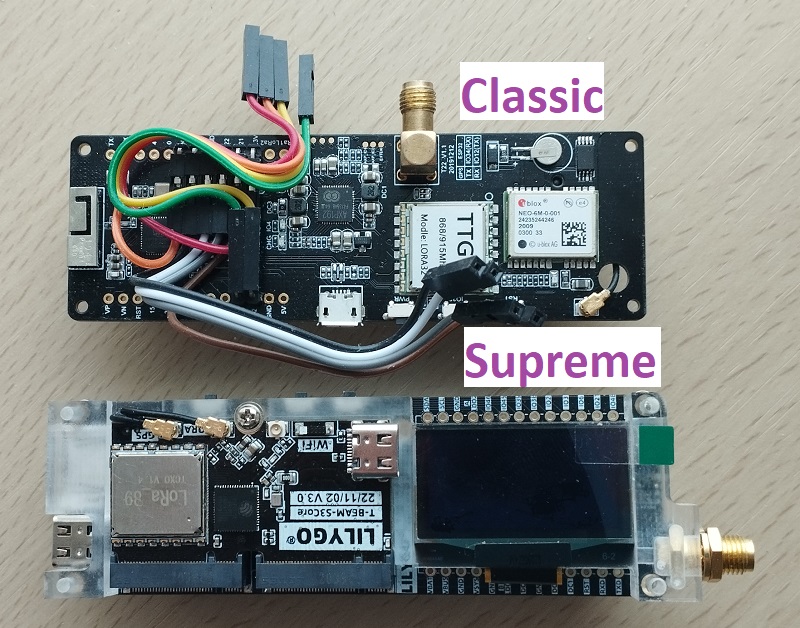
documents/images/Prime3-11.jpg
