lyusupov/SoftRF/documents/images/Prime3-16.jpg

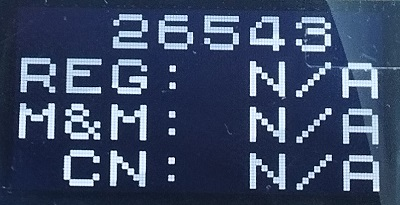
documents/images/Prime3-16.jpg
