lyusupov/SoftRF/documents/images/Prime3-19.jpg

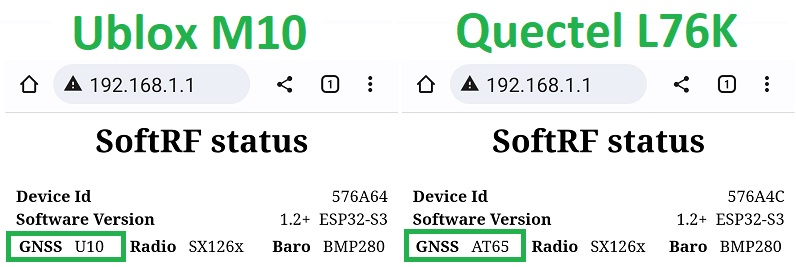
documents/images/Prime3-19.jpg
