lyusupov/SoftRF/documents/images/Prime3-20.jpg

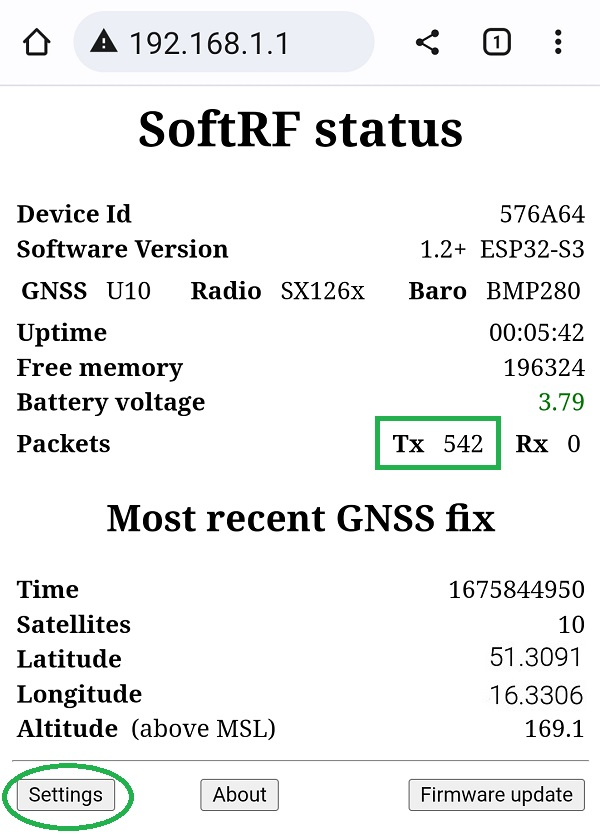
documents/images/Prime3-20.jpg
