lyusupov/SoftRF/documents/images/Prime3-28.jpg

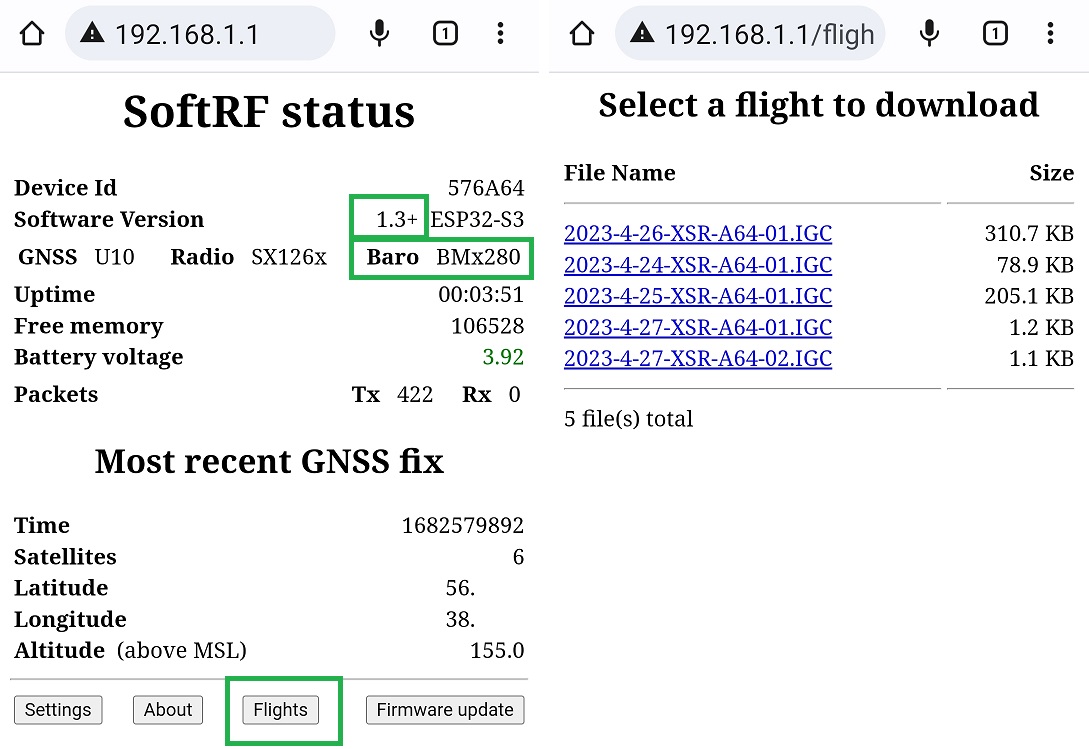
documents/images/Prime3-28.jpg
