lyusupov/SoftRF/documents/images/Prime3-32.jpg

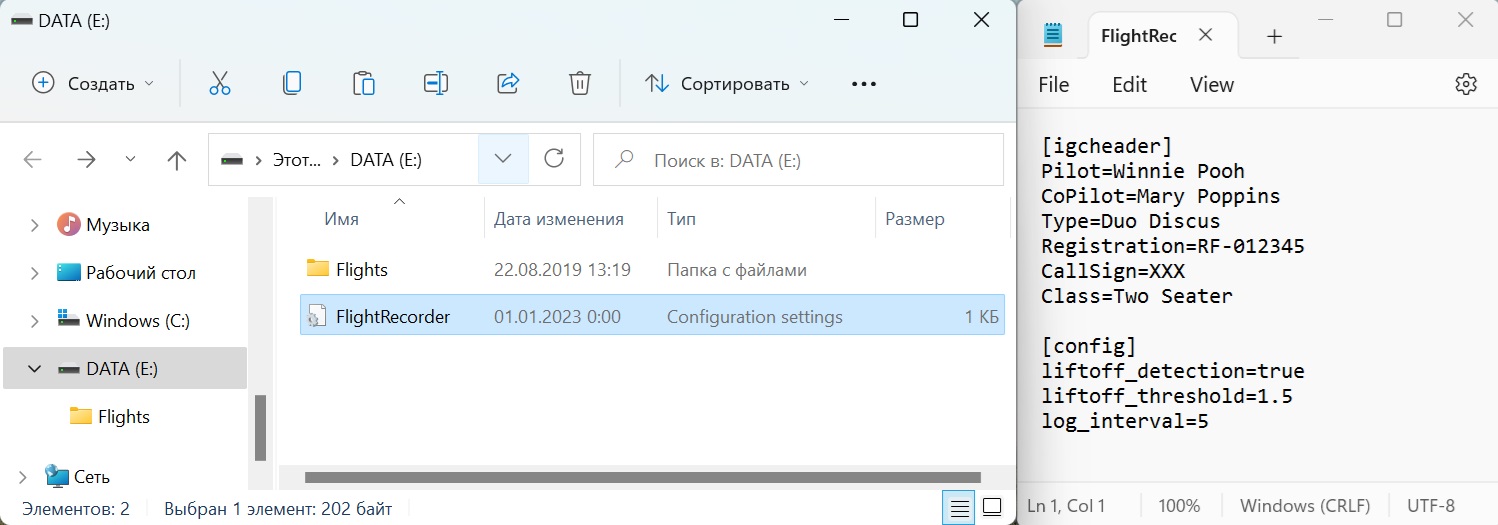
documents/images/Prime3-32.jpg
