lyusupov/SoftRF/documents/images/Retro2-4.jpg

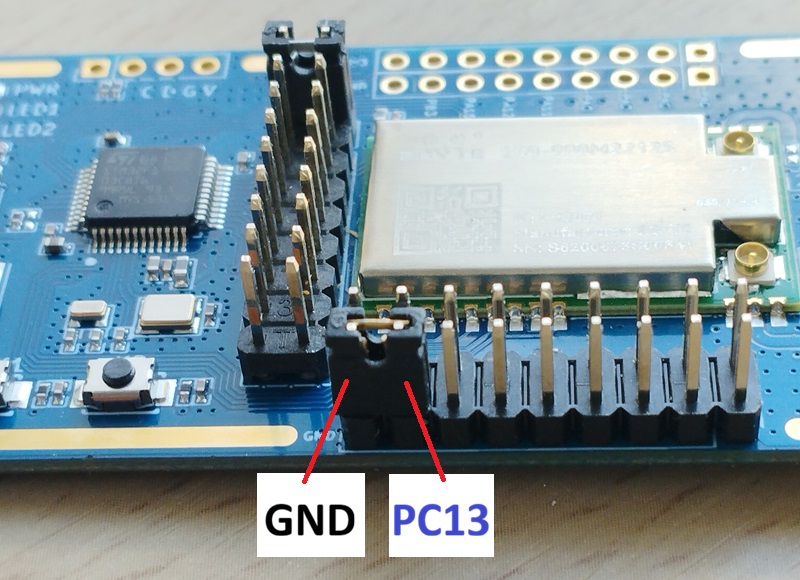
documents/images/Retro2-4.jpg
