lyusupov/SoftRF/documents/images/Retro2-5.jpg

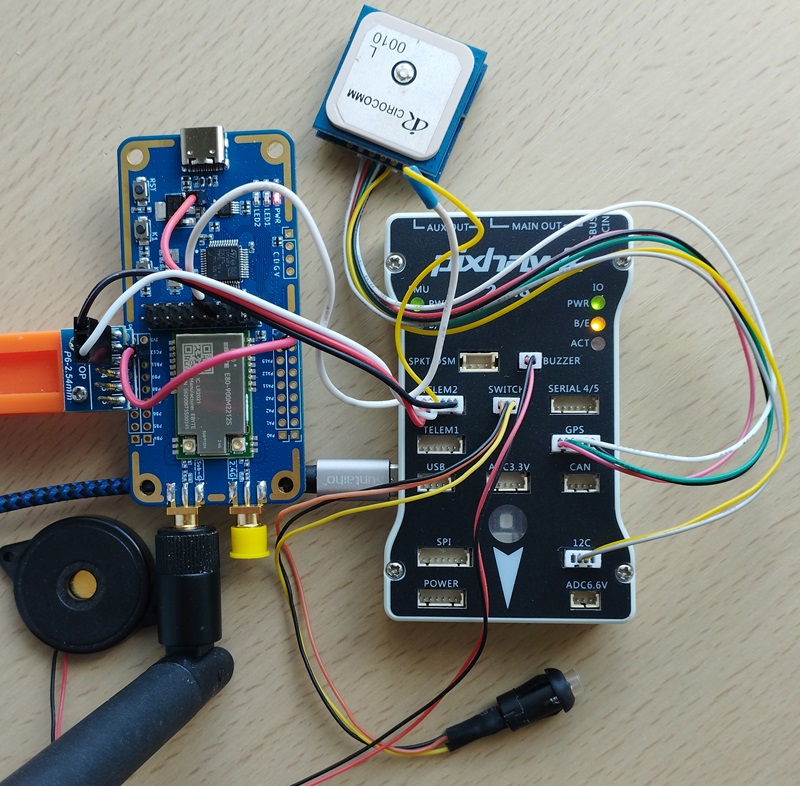
documents/images/Retro2-5.jpg
