lyusupov/SoftRF/documents/images/Retro2-9.jpg

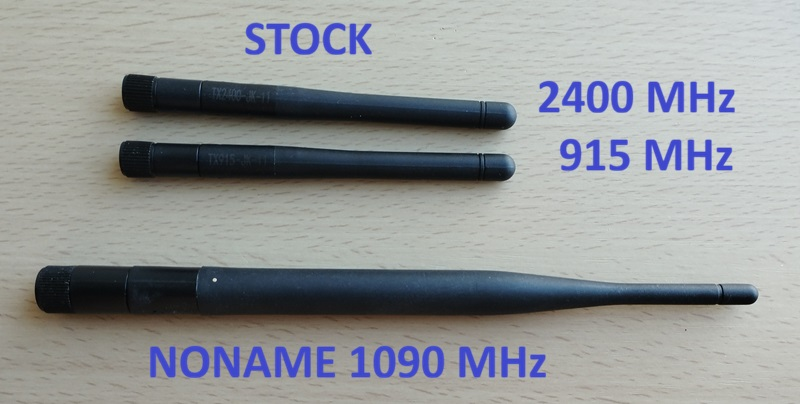
documents/images/Retro2-9.jpg
