lyusupov/SoftRF/documents/images/Retro2-12.jpg

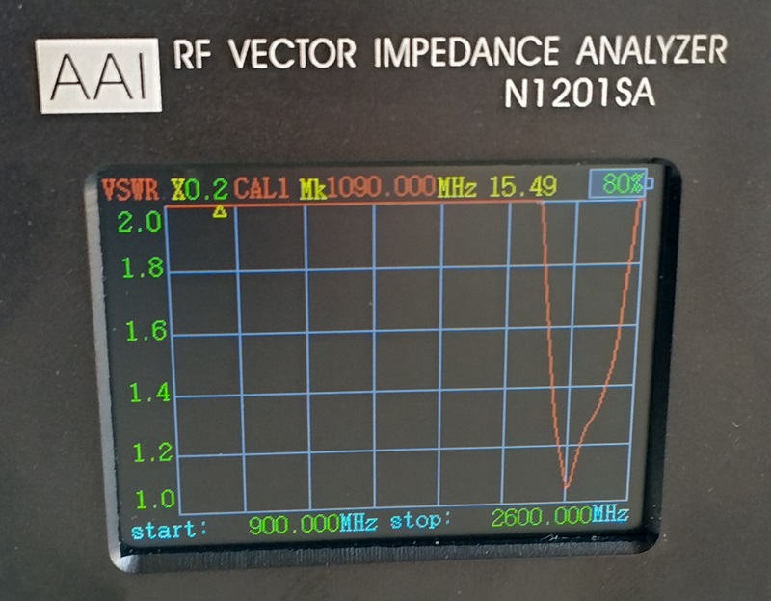
documents/images/Retro2-12.jpg
