lyusupov/SoftRF/documents/images/RPI_SPI.jpg

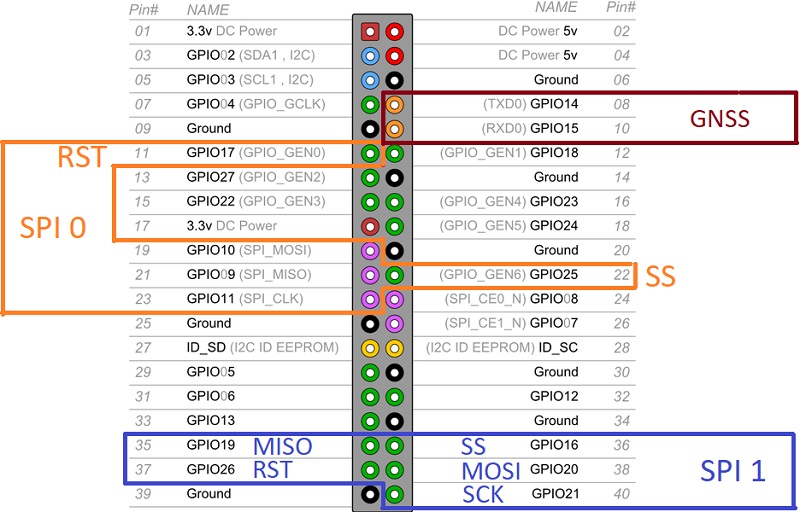
documents/images/RPI_SPI.jpg
