lyusupov/SoftRF/documents/images/Skytraxx_2_fanet.jpg

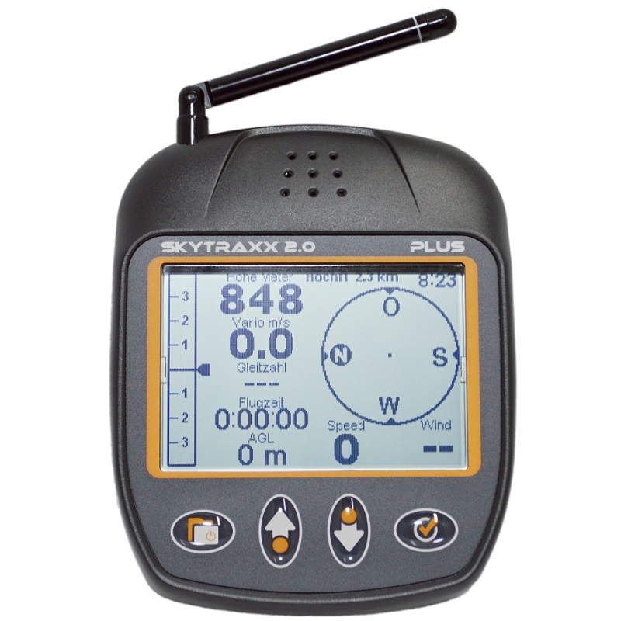
documents/images/Skytraxx_2_fanet.jpg
