lyusupov/SoftRF/documents/images/skyview-2-t5s.jpg

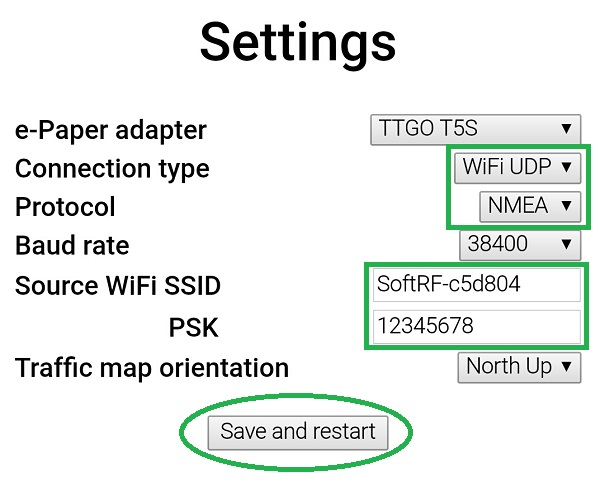
documents/images/skyview-2-t5s.jpg
