lyusupov/SoftRF/documents/images/skyview-11.jpg

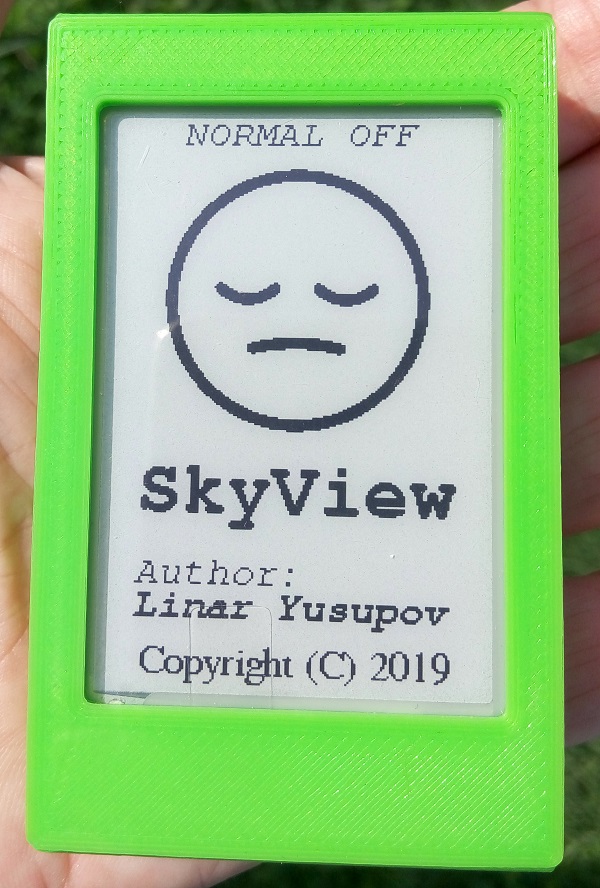
documents/images/skyview-11.jpg
