lyusupov/SoftRF/documents/images/skyview-35.jpg

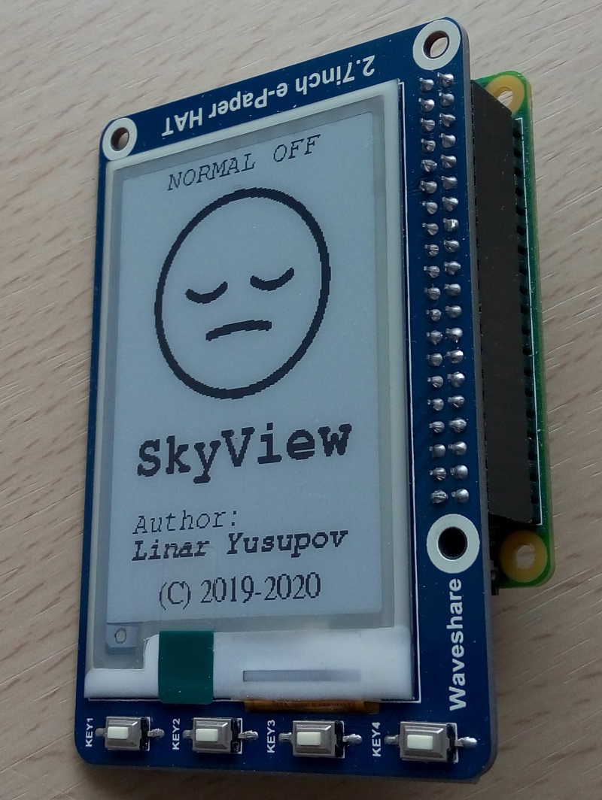
documents/images/skyview-35.jpg
