lyusupov/SoftRF/documents/images/skyview-44.jpg

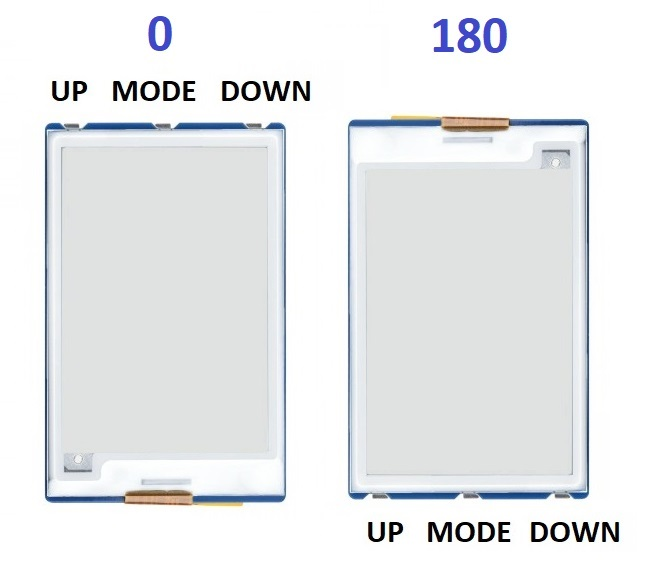
documents/images/skyview-44.jpg
