lyusupov/SoftRF/documents/images/skyview-51.jpg

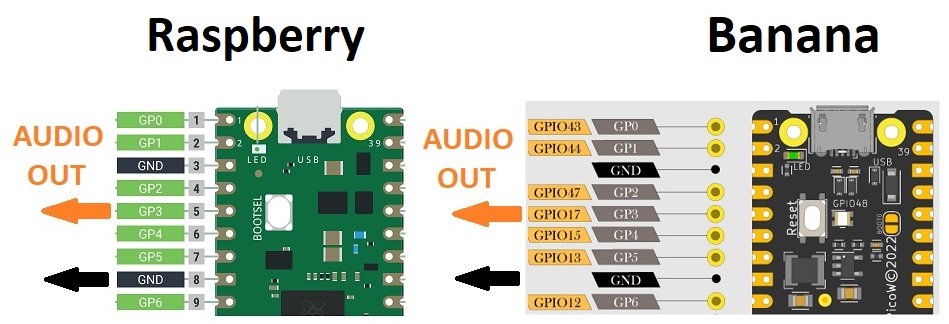
documents/images/skyview-51.jpg
