lyusupov/SoftRF/documents/images/skyview-53.jpg

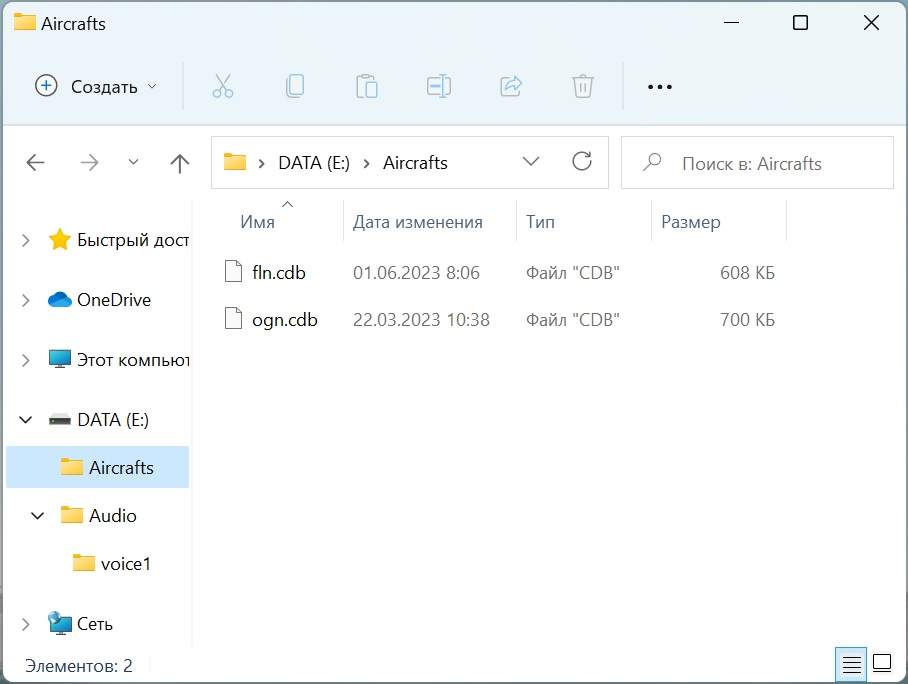
documents/images/skyview-53.jpg
