lyusupov/SoftRF/documents/images/skywatch-1.jpg

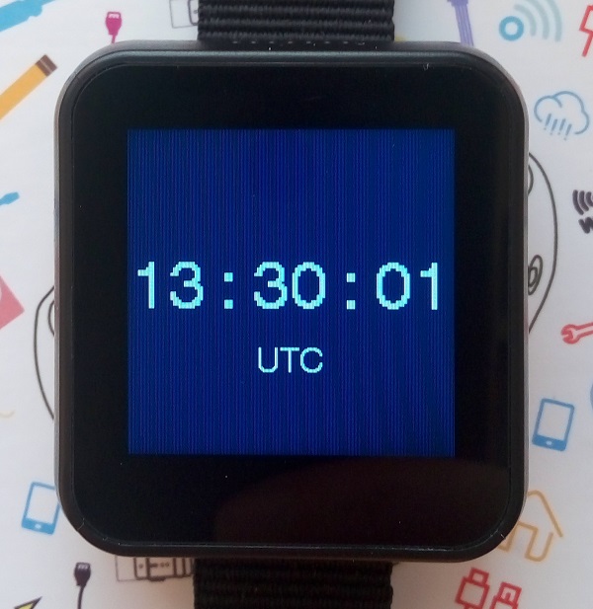
documents/images/skywatch-1.jpg
