lyusupov/SoftRF/documents/images/SoftRF-Case-v5-Exterior-3dBi.jpg

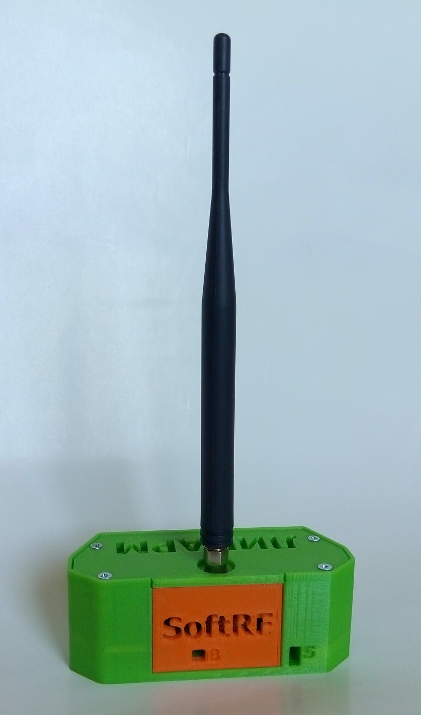
documents/images/SoftRF-Case-v5-Exterior-3dBi.jpg
