lyusupov/SoftRF/documents/images/SoftRF-LoRa-upgrade-1.jpg

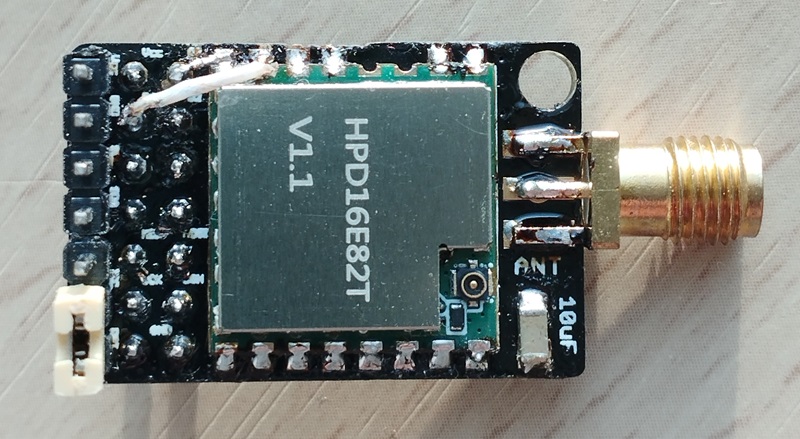
documents/images/SoftRF-LoRa-upgrade-1.jpg
