lyusupov/SoftRF/documents/images/SoftRF-UAT-4.jpg

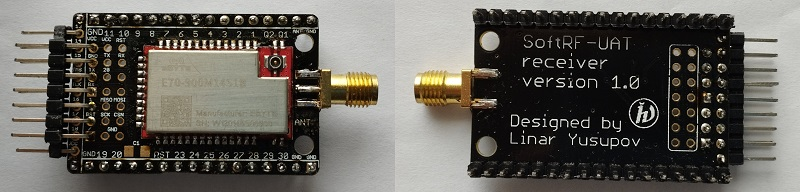
documents/images/SoftRF-UAT-4.jpg
