lyusupov/SoftRF/documents/images/softrf_prime_Philip_Döring_screenshot.png

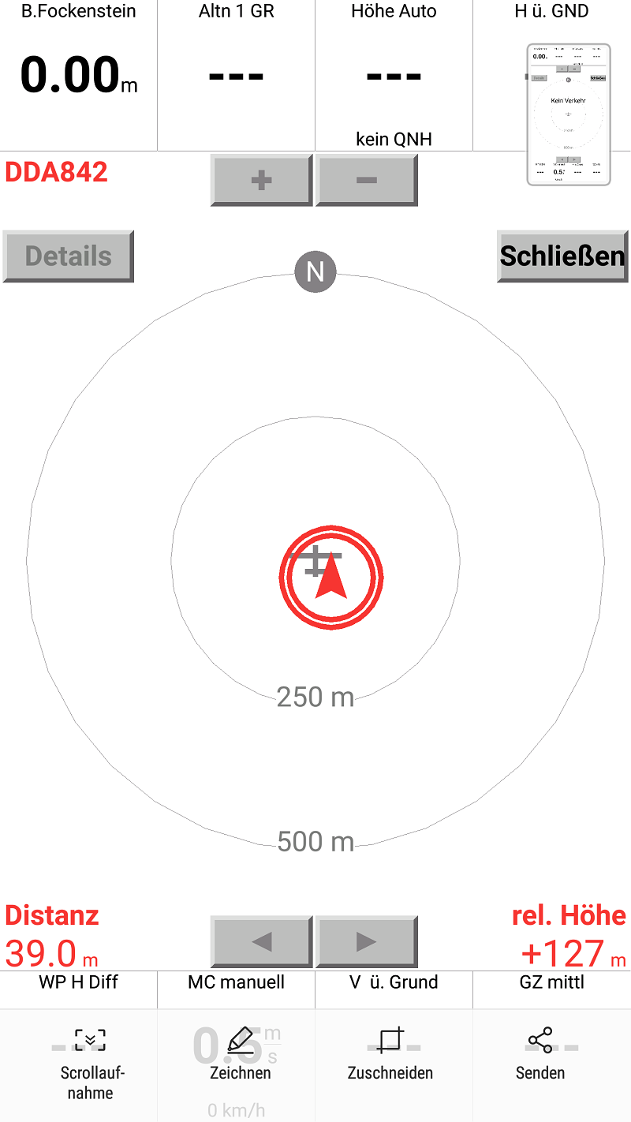
documents/images/softrf_prime_Philip_Döring_screenshot.png
