lyusupov/SoftRF/documents/images/SoftRF_Tool-1.jpg

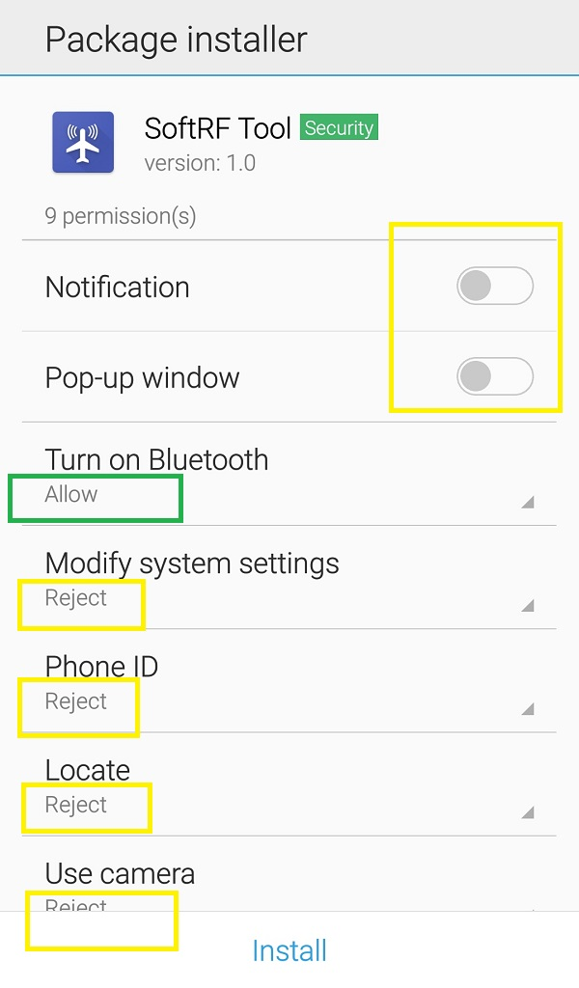
documents/images/SoftRF_Tool-1.jpg
