lyusupov/SoftRF/documents/images/SoftRF_Tool-5.jpg

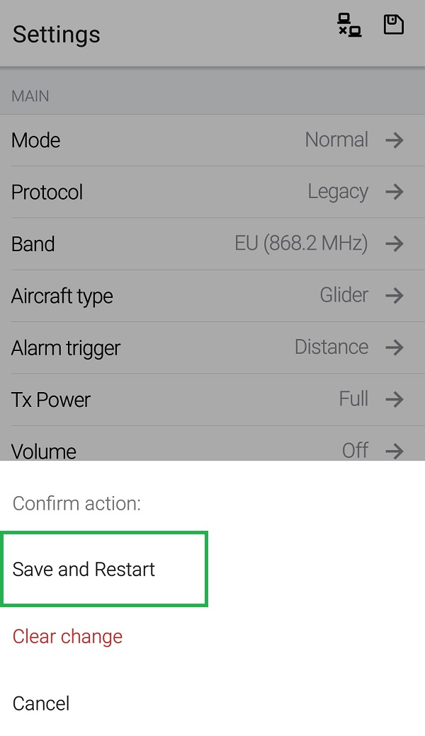
documents/images/SoftRF_Tool-5.jpg
