lyusupov/SoftRF/documents/images/software-mix.jpg

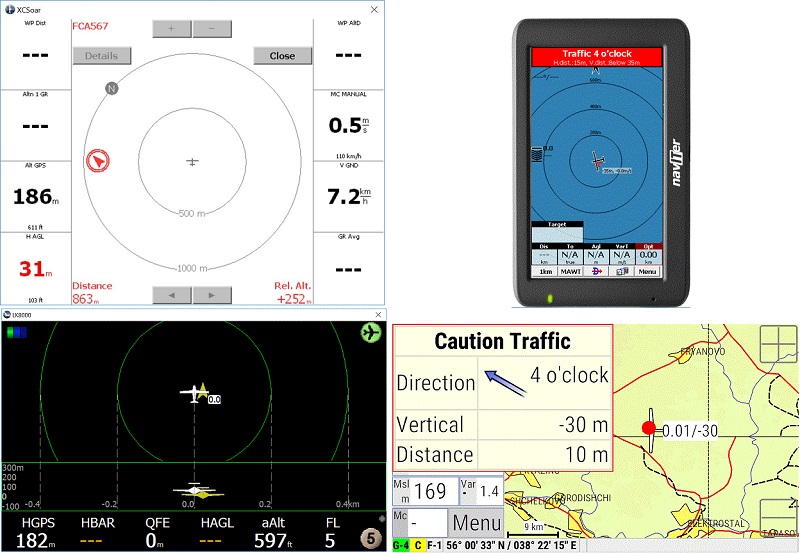
documents/images/software-mix.jpg
