lyusupov/SoftRF/documents/images/Solaris-1.jpg

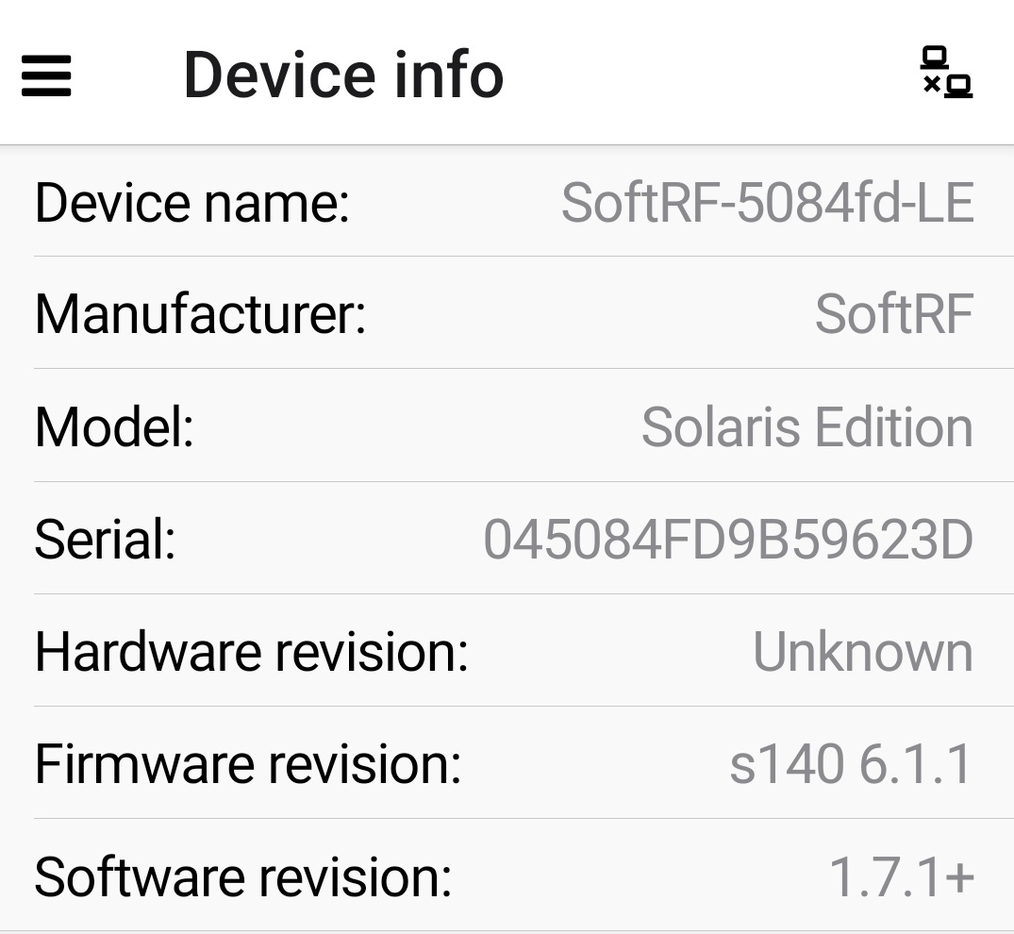
documents/images/Solaris-1.jpg
