lyusupov/SoftRF/documents/images/Standalone-ESP32P4-1.jpg

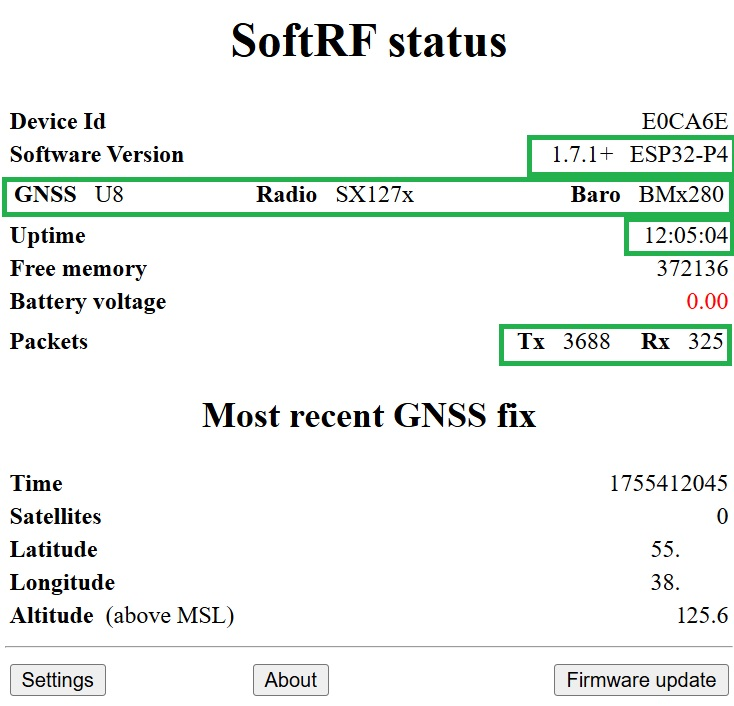
documents/images/Standalone-ESP32P4-1.jpg
