lyusupov/SoftRF/documents/images/Standalone-ESP32P4-2.jpg

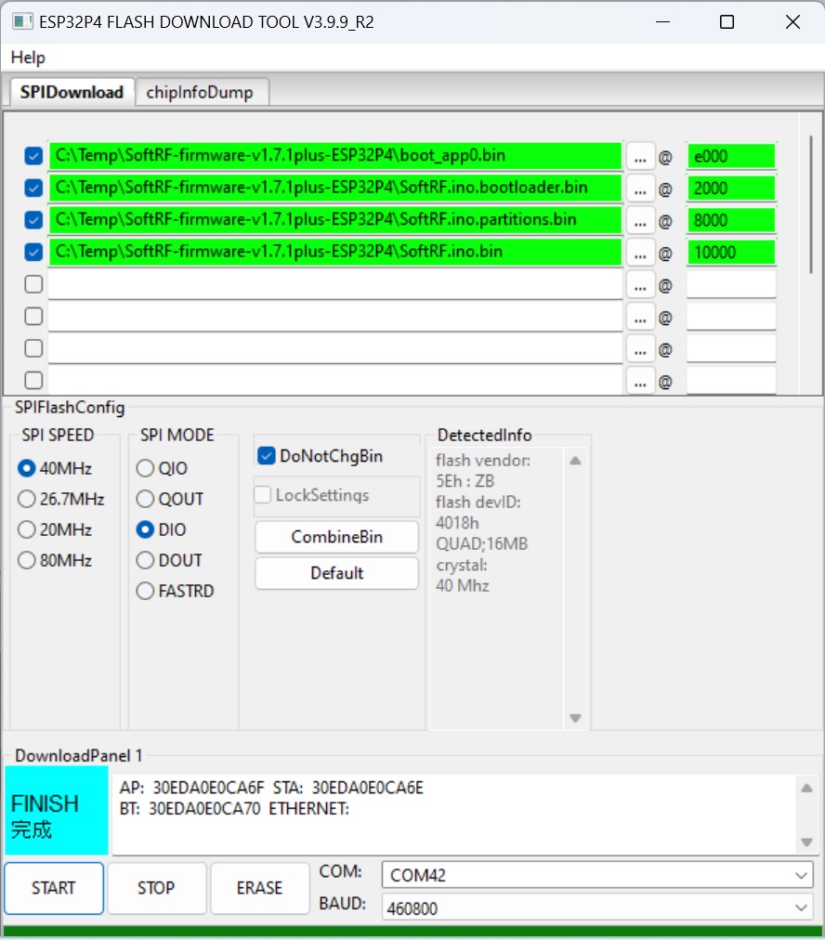
documents/images/Standalone-ESP32P4-2.jpg
