lyusupov/SoftRF/documents/images/stratux-1.jpg

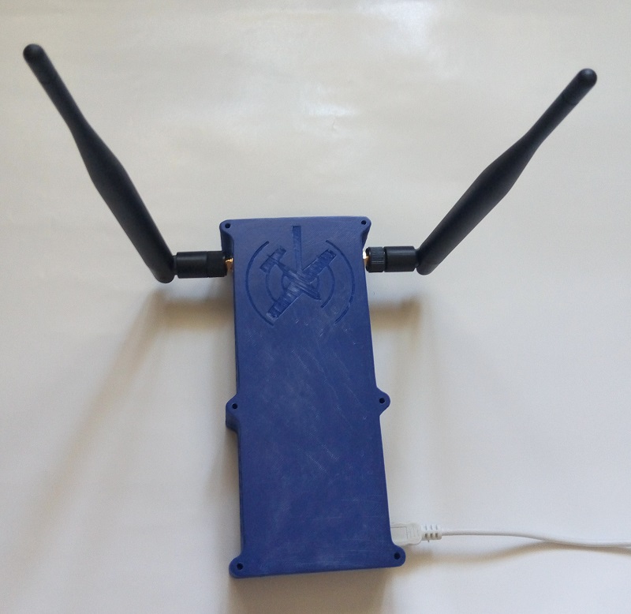
documents/images/stratux-1.jpg
