lyusupov/SoftRF/documents/images/t-echo-ant-1.jpg

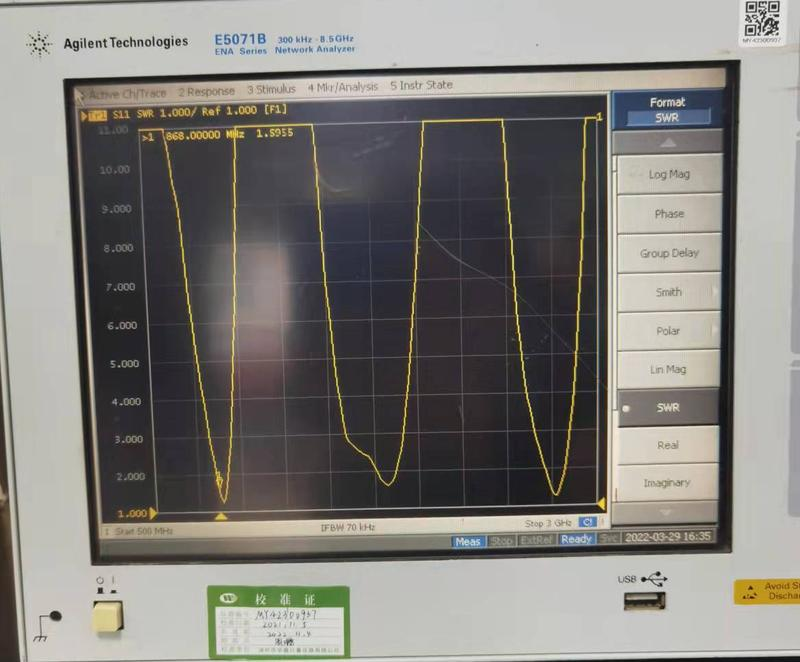
documents/images/t-echo-ant-1.jpg
