lyusupov/SoftRF/documents/images/t-echo-ant-2.jpg

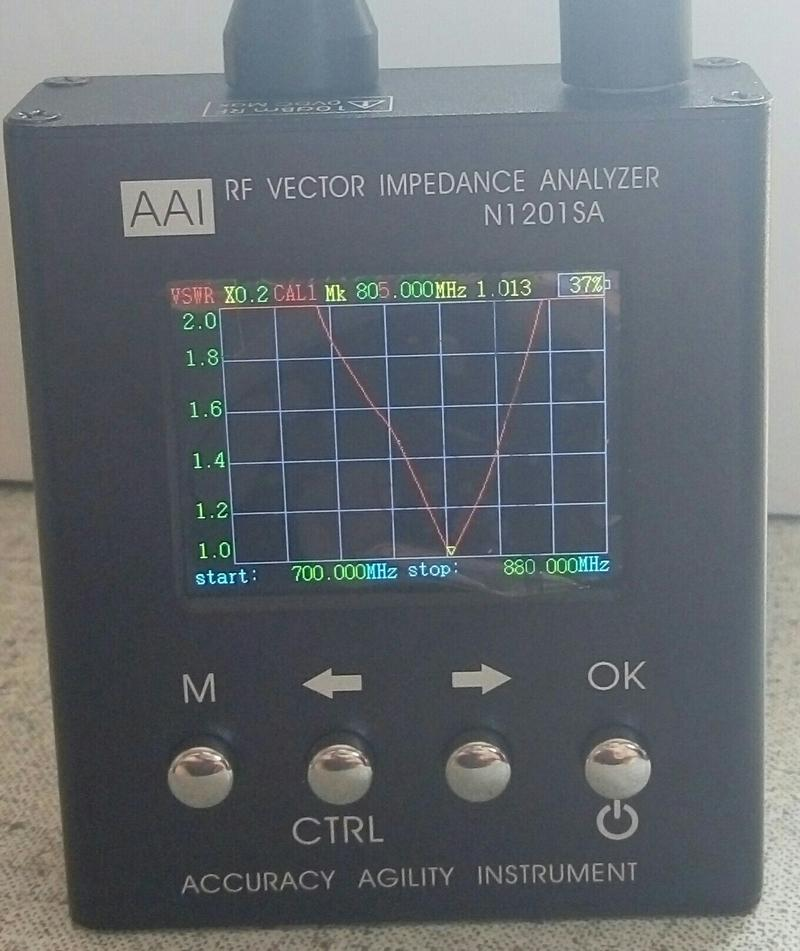
documents/images/t-echo-ant-2.jpg
