lyusupov/SoftRF/documents/images/t-motion-15.jpg

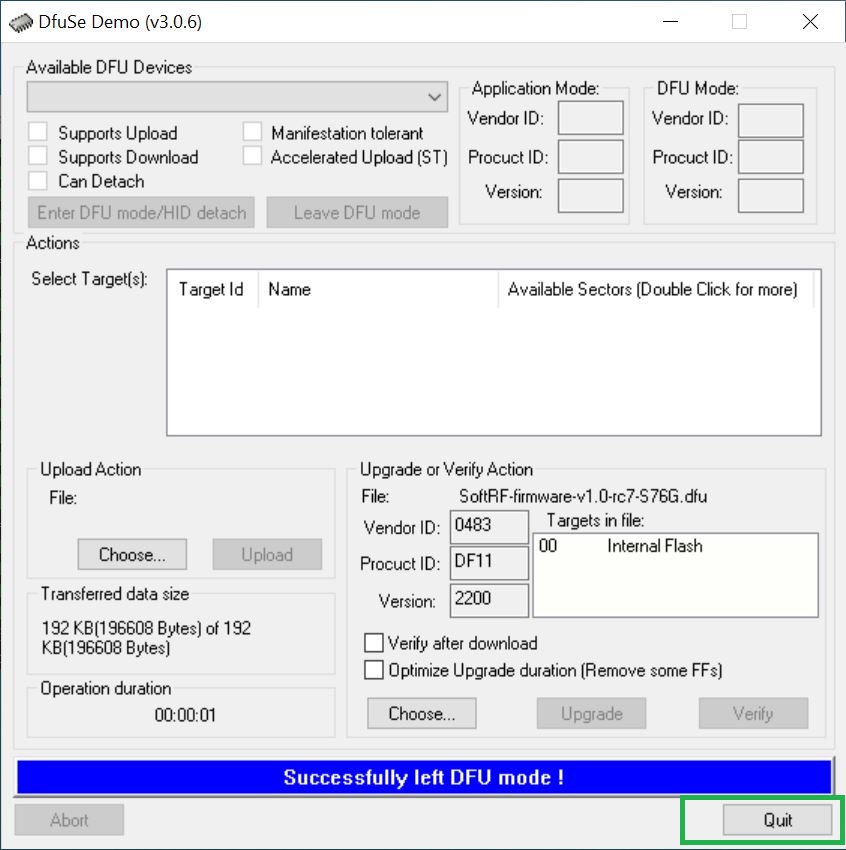
documents/images/t-motion-15.jpg
