lyusupov/SoftRF/documents/images/T-SX-1262.jpg

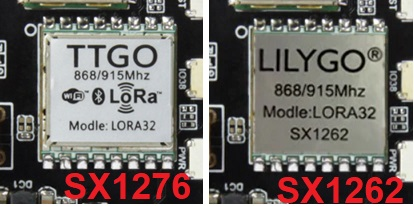
documents/images/T-SX-1262.jpg
