lyusupov/SoftRF/documents/images/ttgo-t5s-rear.jpg

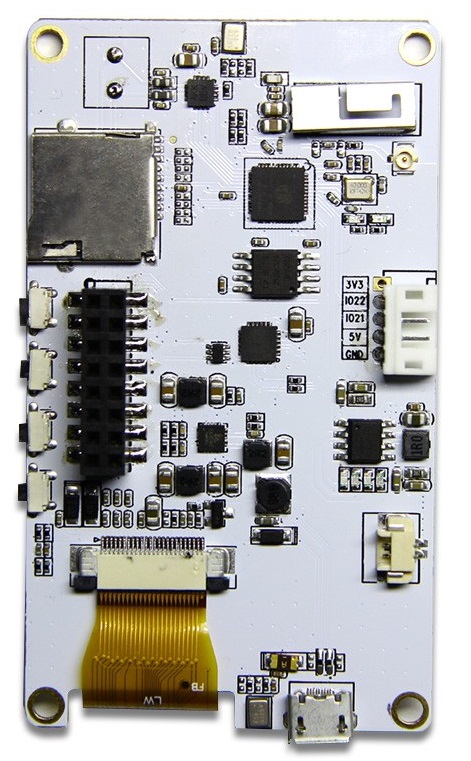
documents/images/ttgo-t5s-rear.jpg
