lyusupov/SoftRF/documents/images/TTGO_TBeam_1.jpg

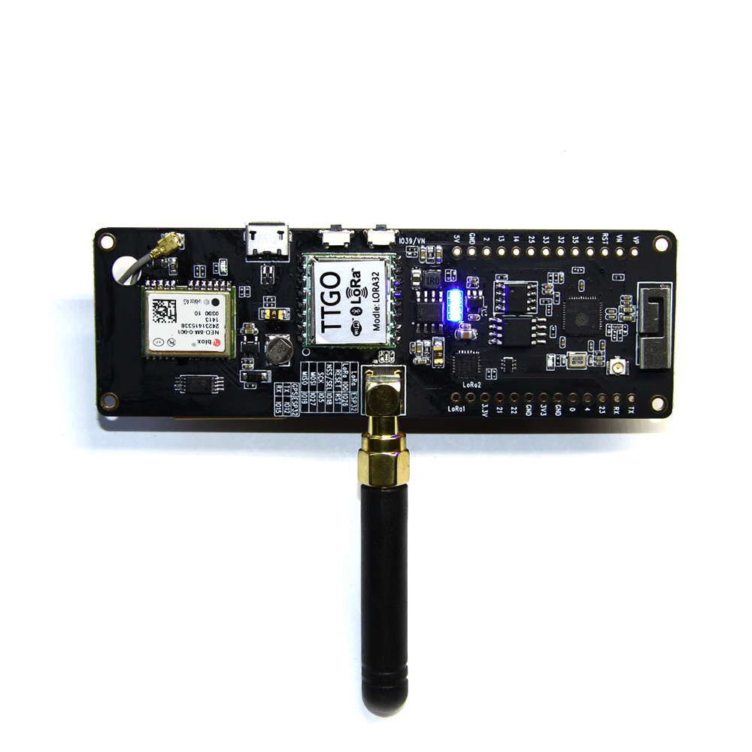
documents/images/TTGO_TBeam_1.jpg
