lyusupov/SoftRF/documents/images/TTGO_TBeam_2_sm.jpg

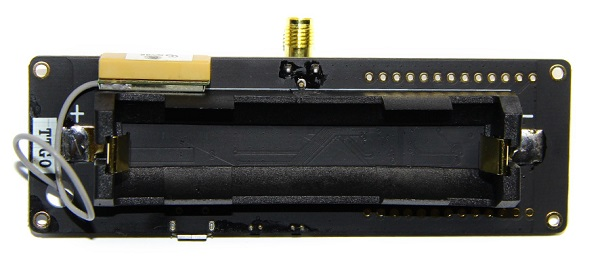
documents/images/TTGO_TBeam_2_sm.jpg
