lyusupov/SoftRF/documents/images/uat-normal-3.jpg

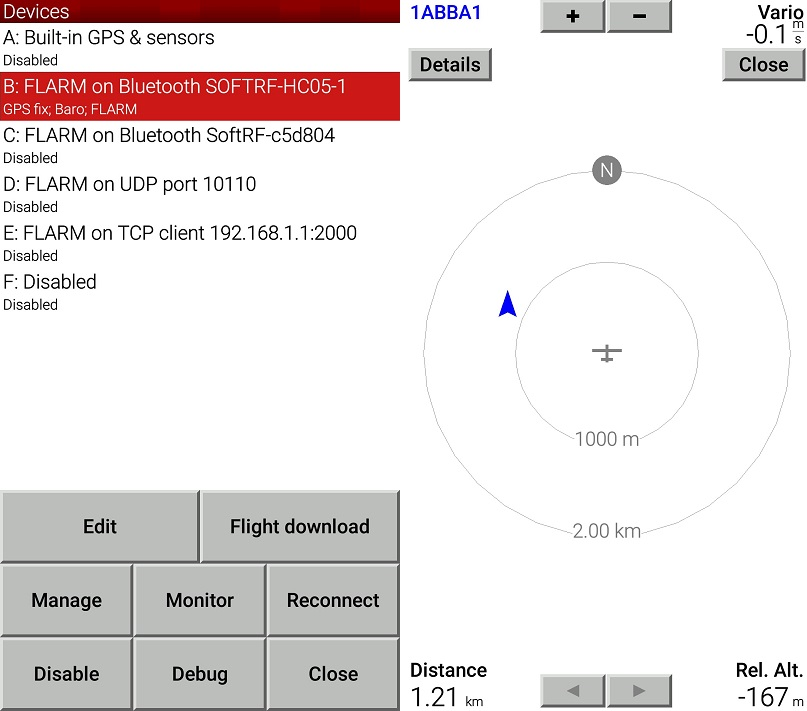
documents/images/uat-normal-3.jpg
