lyusupov/SoftRF/documents/images/uat-normal-4.jpg

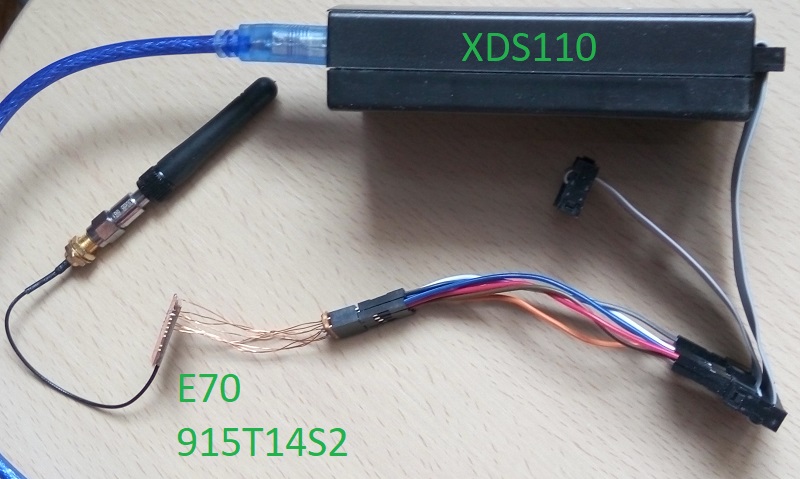
documents/images/uat-normal-4.jpg
