lyusupov/SoftRF/documents/images/Uni-fw-1.jpg

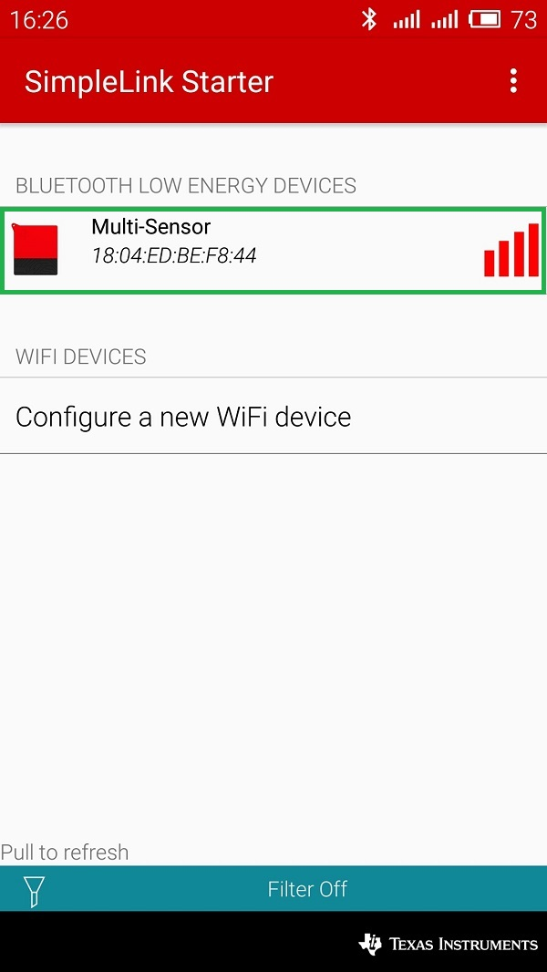
documents/images/Uni-fw-1.jpg
