lyusupov/SoftRF/documents/images/Uni-fw-7.jpg

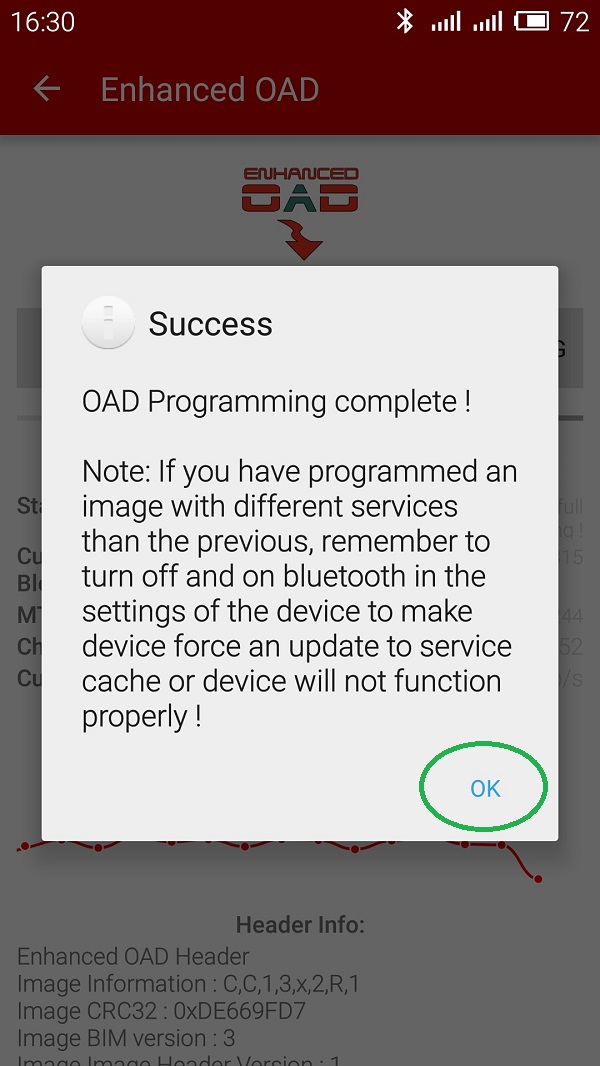
documents/images/Uni-fw-7.jpg
