lyusupov/SoftRF/documents/images/Uni-gnss-2.jpg

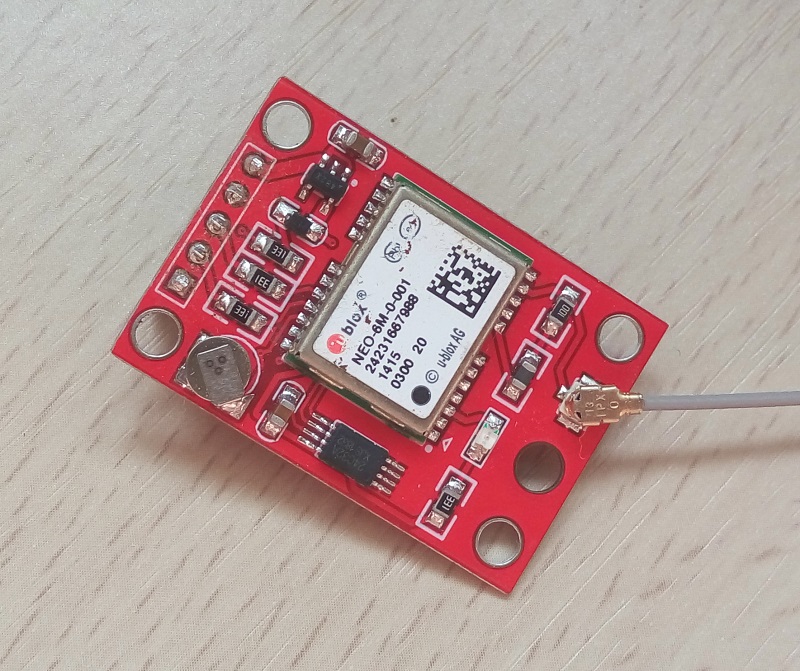
documents/images/Uni-gnss-2.jpg
