lyusupov/SoftRF/documents/images/Uni-gnss-4.jpg

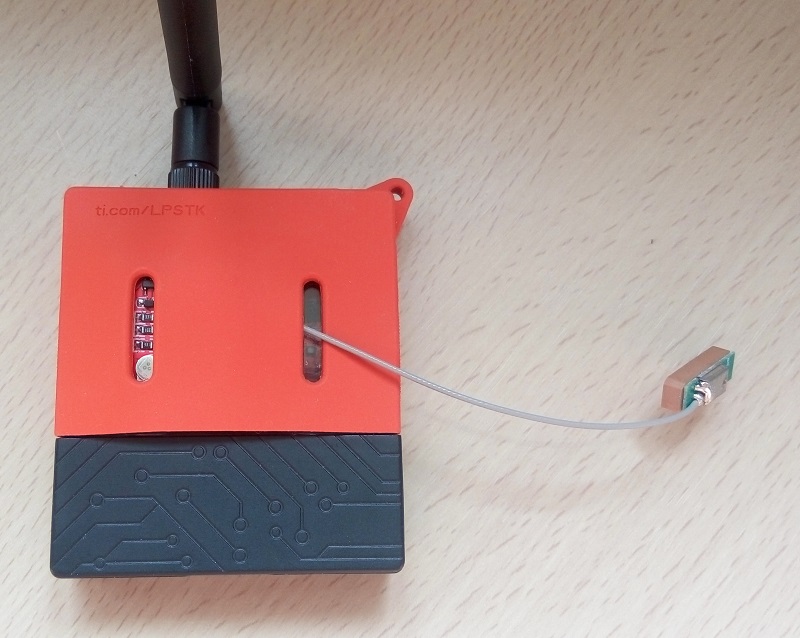
documents/images/Uni-gnss-4.jpg
