lyusupov/SoftRF/documents/images/Uni-gnss-7.jpg

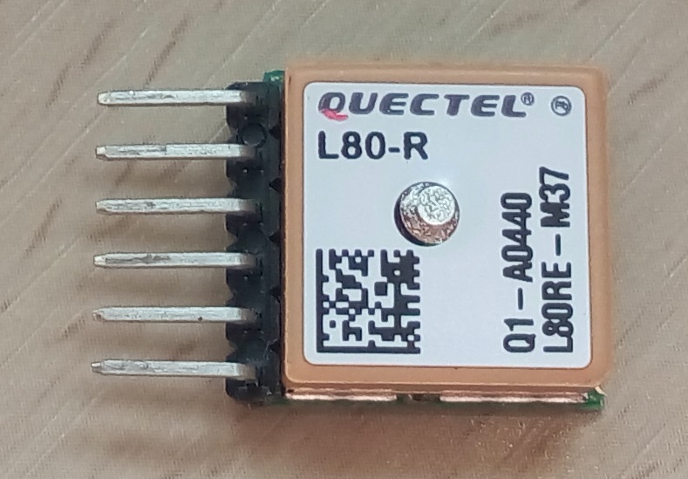
documents/images/Uni-gnss-7.jpg
