lyusupov/SoftRF/documents/images/Uni-gnss-10.jpg

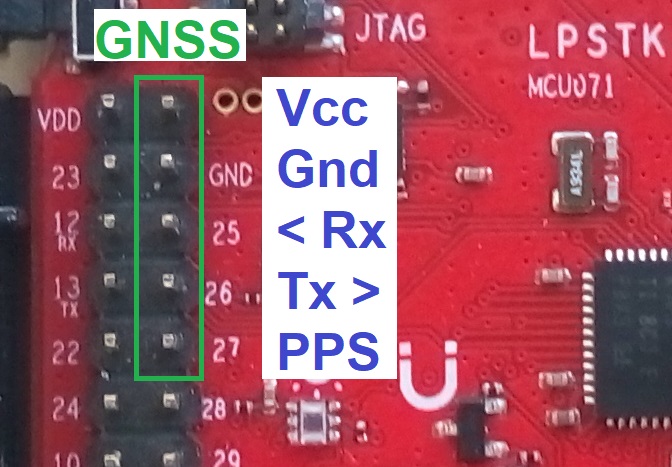
documents/images/Uni-gnss-10.jpg
