lyusupov/SoftRF/documents/images/Uni-LED-rgb.jpg

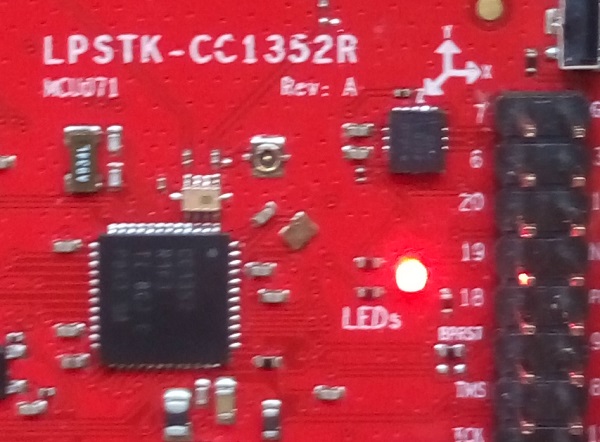
documents/images/Uni-LED-rgb.jpg
