lyusupov/SoftRF/documents/images/Uni-wires-1.jpg

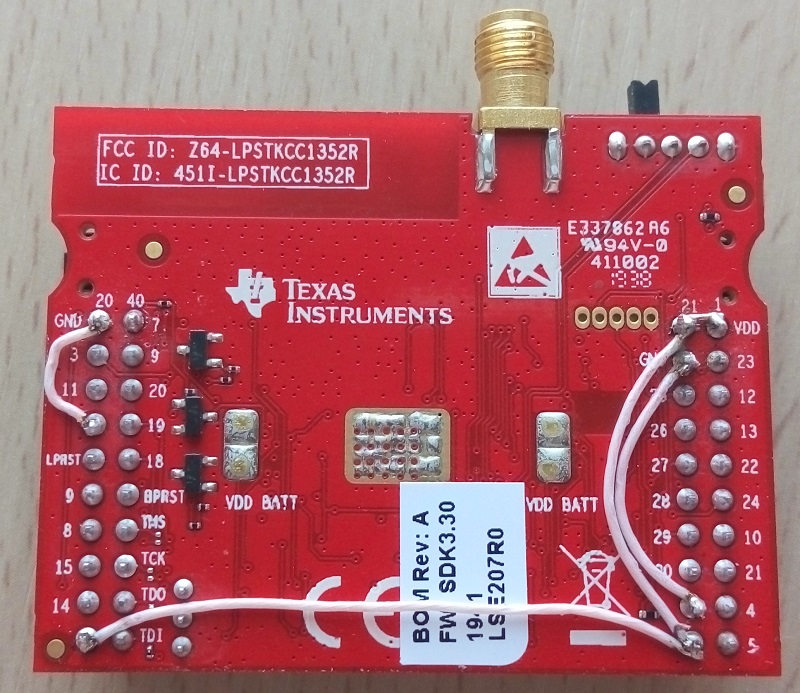
documents/images/Uni-wires-1.jpg
