lyusupov/SoftRF/documents/images/USB-Bluetooth-1.jpg

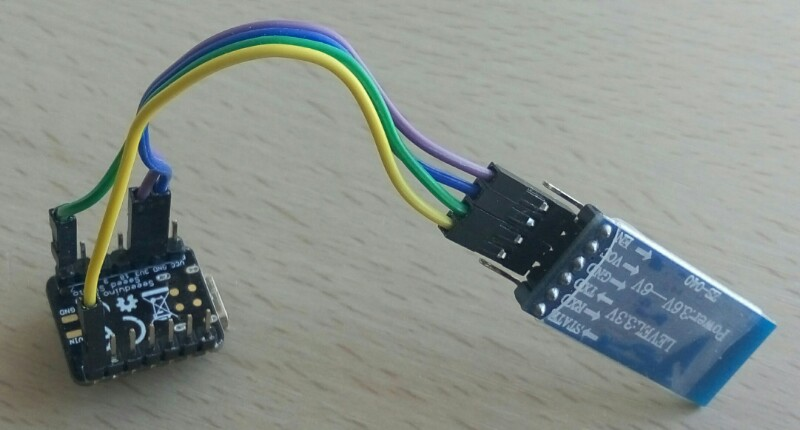
documents/images/USB-Bluetooth-1.jpg
