lyusupov/SoftRF/documents/images/WebTop-4.jpg

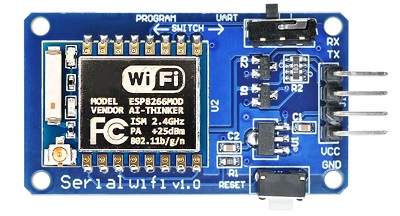
documents/images/WebTop-4.jpg
