lyusupov/SoftRF/documents/images/WebTop-14.jpg

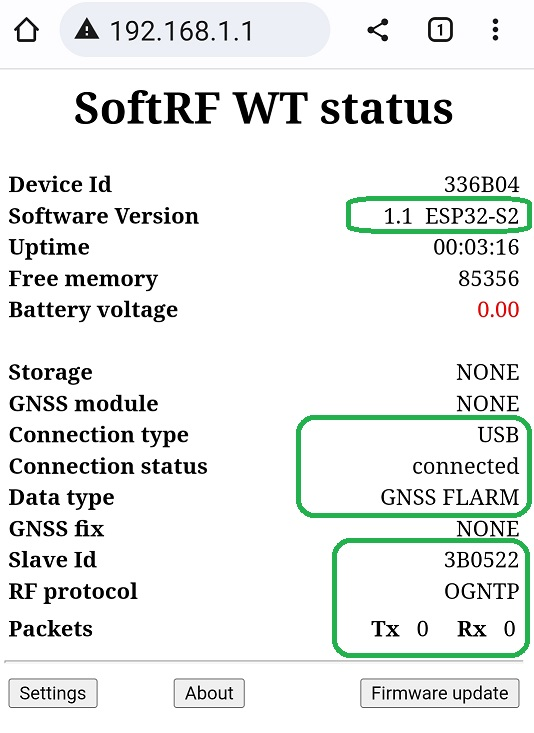
documents/images/WebTop-14.jpg
