lyusupov/SoftRF/documents/images/WebTop-16.jpg

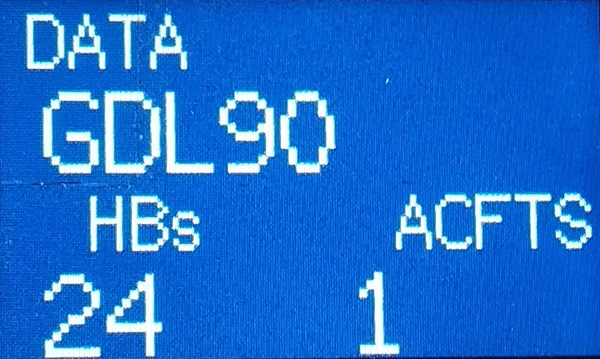
documents/images/WebTop-16.jpg
