lyusupov/SoftRF/documents/images/webupdate-10.jpg

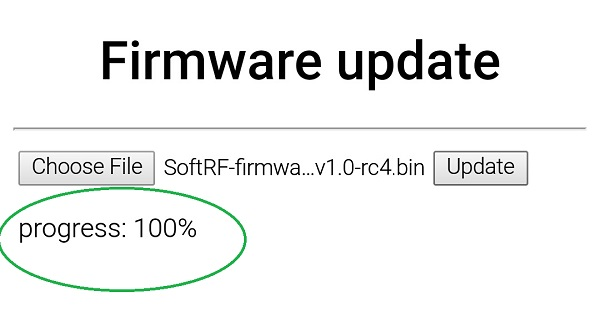
documents/images/webupdate-10.jpg
