lyusupov/SoftRF/hardware/SoftRF-LoRa-schematics-rev1.1.png

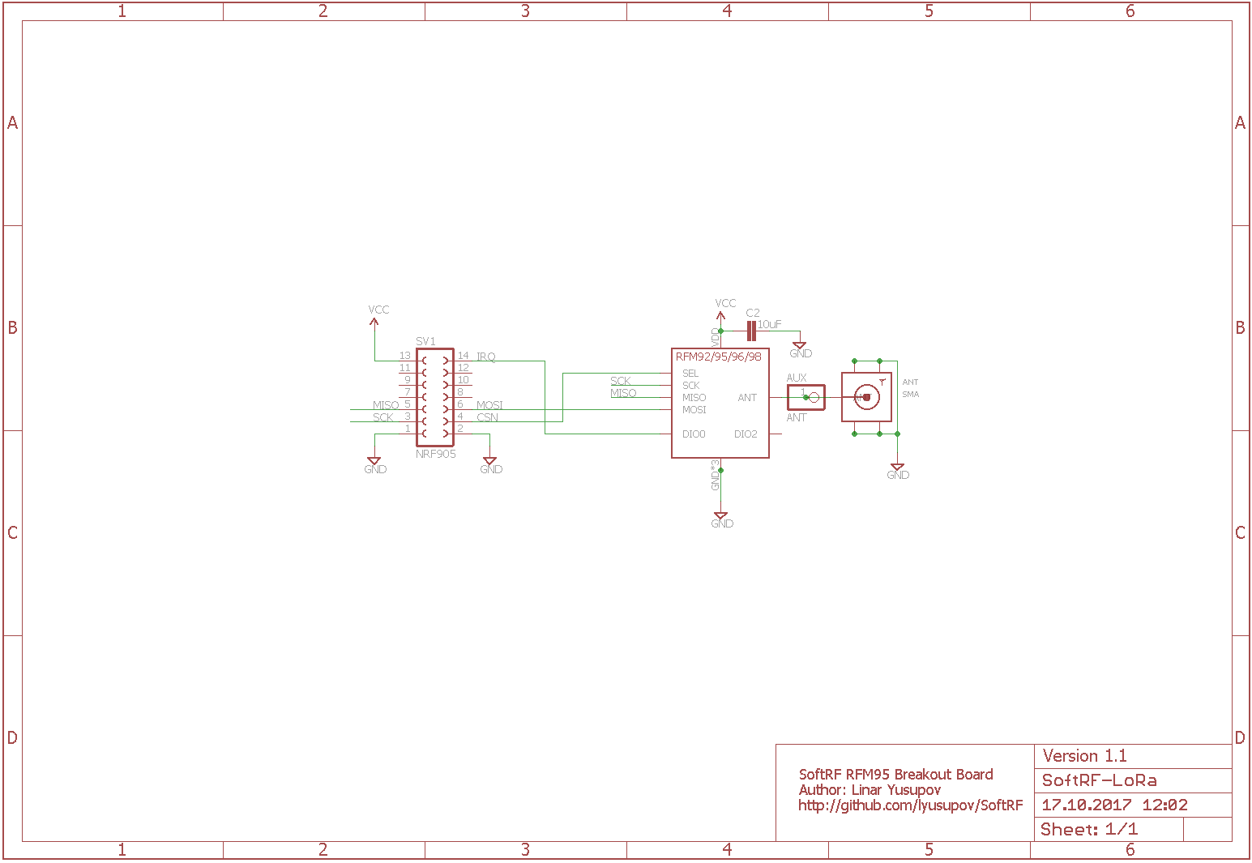
hardware/SoftRF-LoRa-schematics-rev1.1.png
