lyusupov/SoftRF/hardware/SoftRF-LoRa-schematics-rev1.2.png

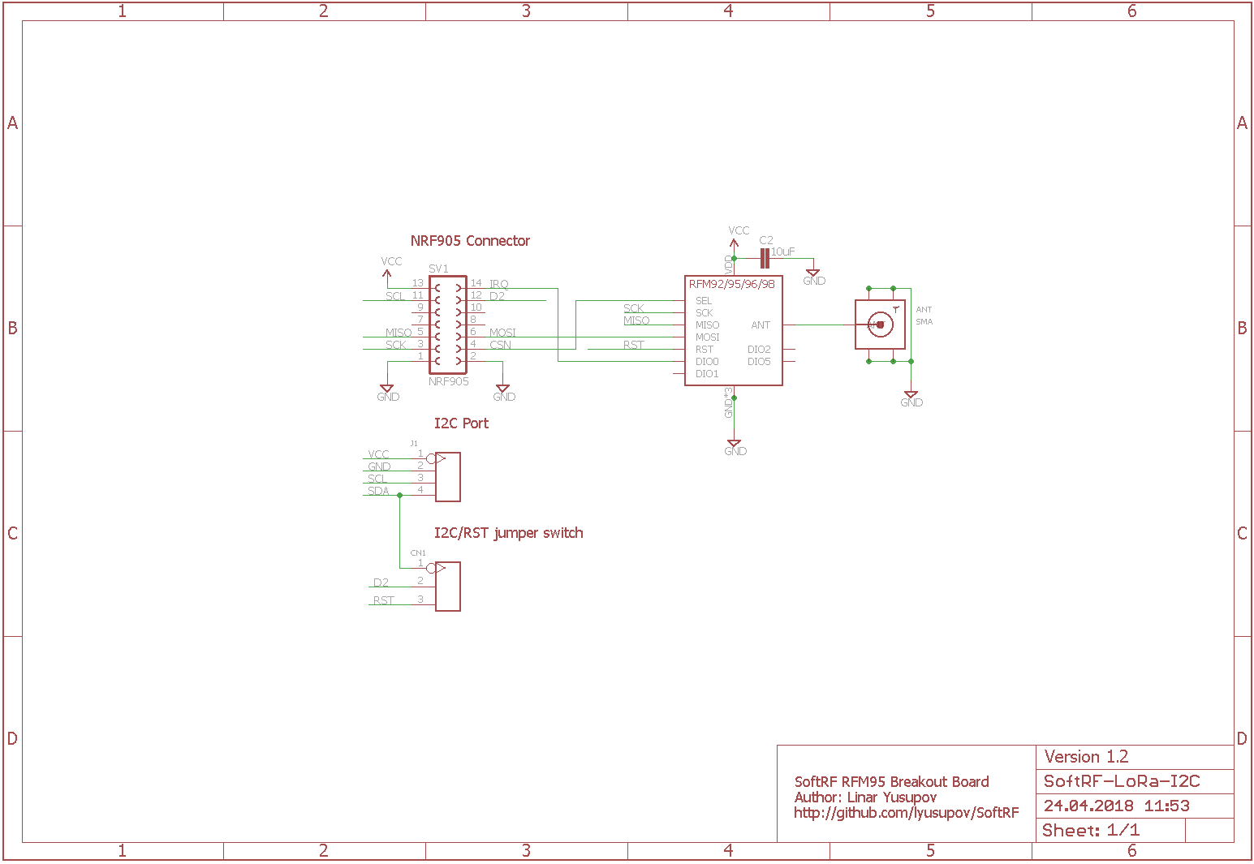
hardware/SoftRF-LoRa-schematics-rev1.2.png
