lyusupov/SoftRF/documents/images/bom/4ph1mm254mm.jpg

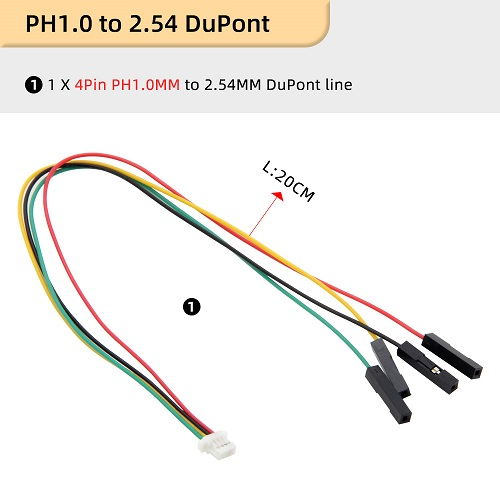
documents/images/bom/4ph1mm254mm.jpg
