lyusupov/SoftRF/documents/images/bom/8led.jpg

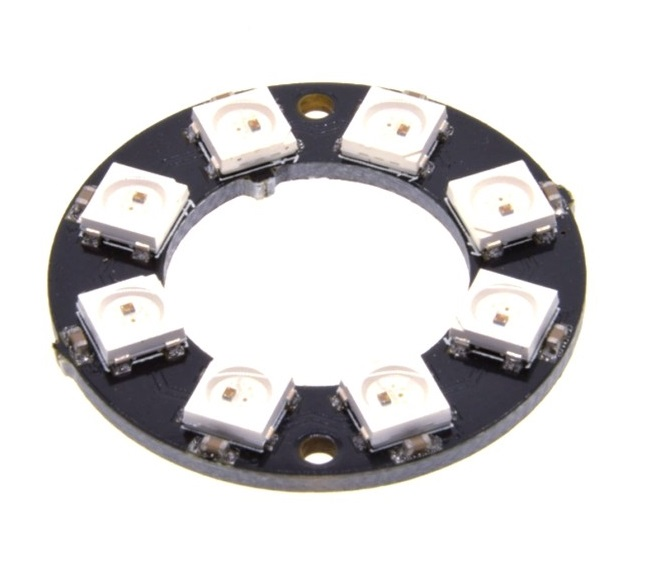
documents/images/bom/8led.jpg
