lyusupov/SoftRF/documents/images/bom/10led.jpg

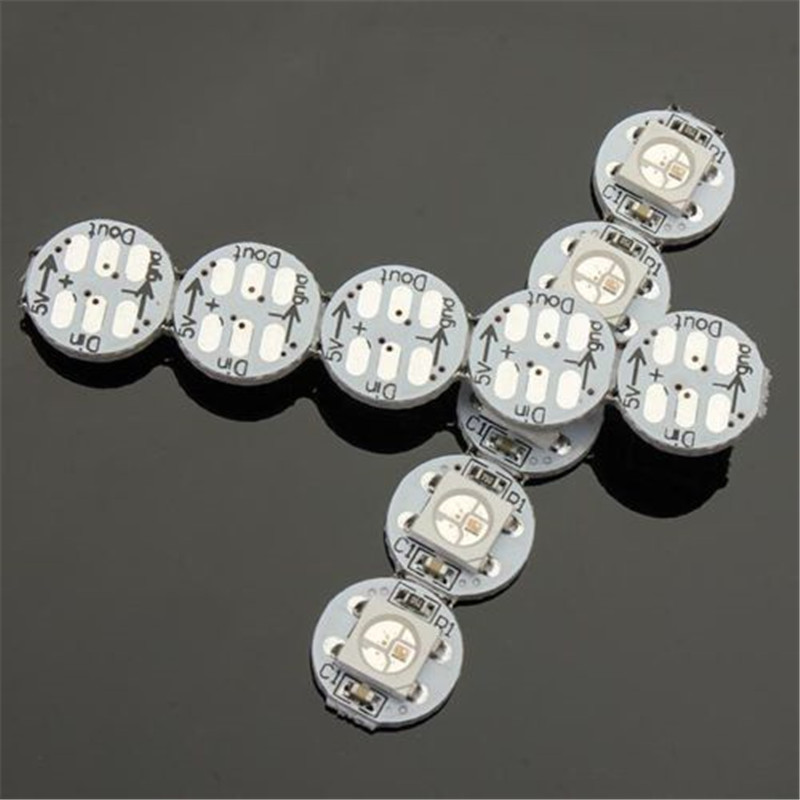
documents/images/bom/10led.jpg
