lyusupov/SoftRF/documents/images/bom/40DuPont.jpg

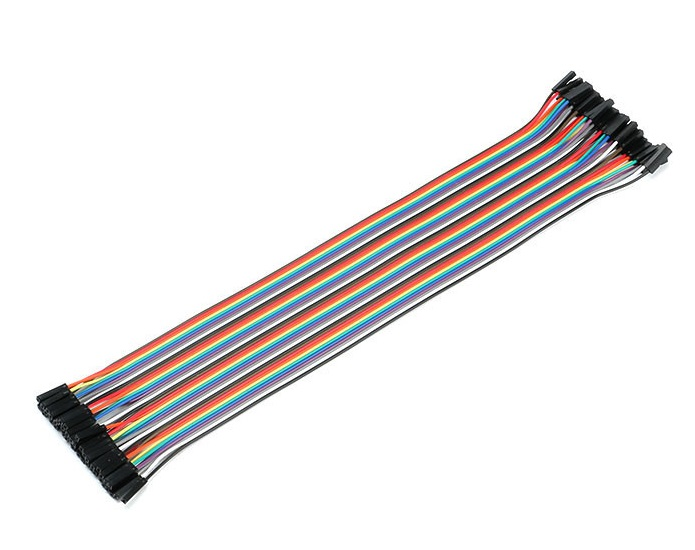
documents/images/bom/40DuPont.jpg
