lyusupov/SoftRF/documents/images/bom/ant1.jpg

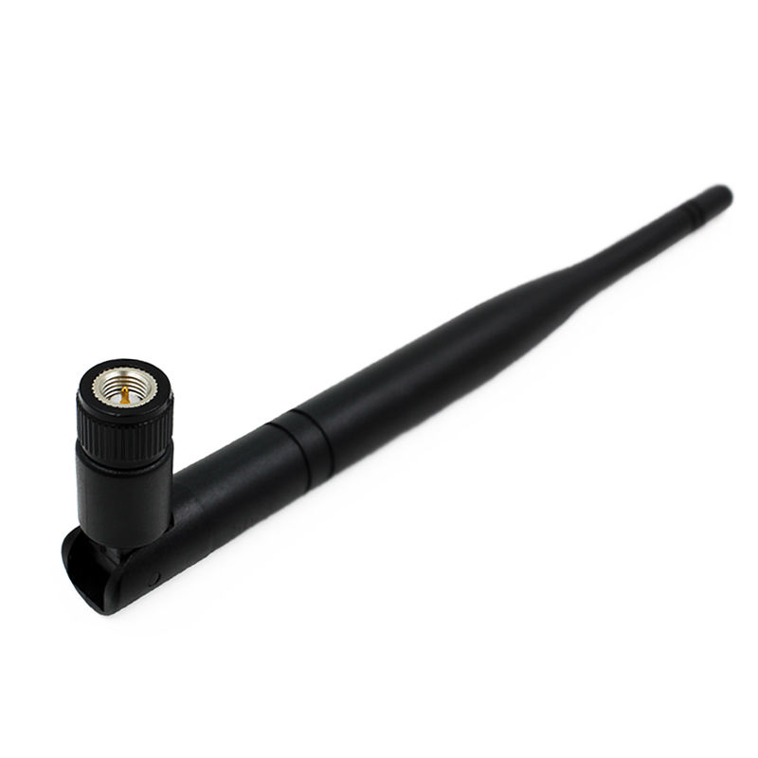
documents/images/bom/ant1.jpg
