lyusupov/SoftRF/documents/images/bom/ant2.jpg

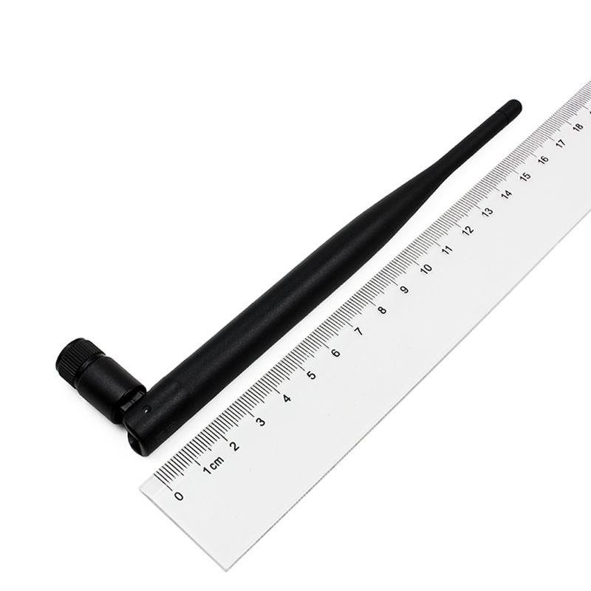
documents/images/bom/ant2.jpg
