lyusupov/SoftRF/documents/images/bom/ant_868_2.jpg

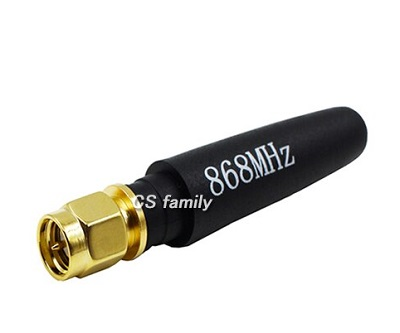
documents/images/bom/ant_868_2.jpg
