lyusupov/SoftRF/documents/images/bom/arduino_m0.jpg

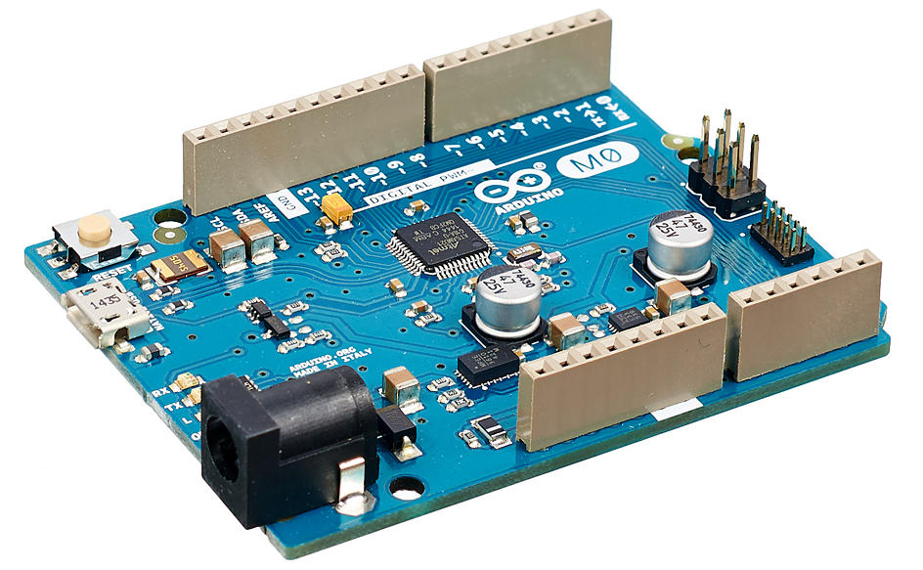
documents/images/bom/arduino_m0.jpg
