lyusupov/SoftRF/documents/images/bom/bathold.jpg

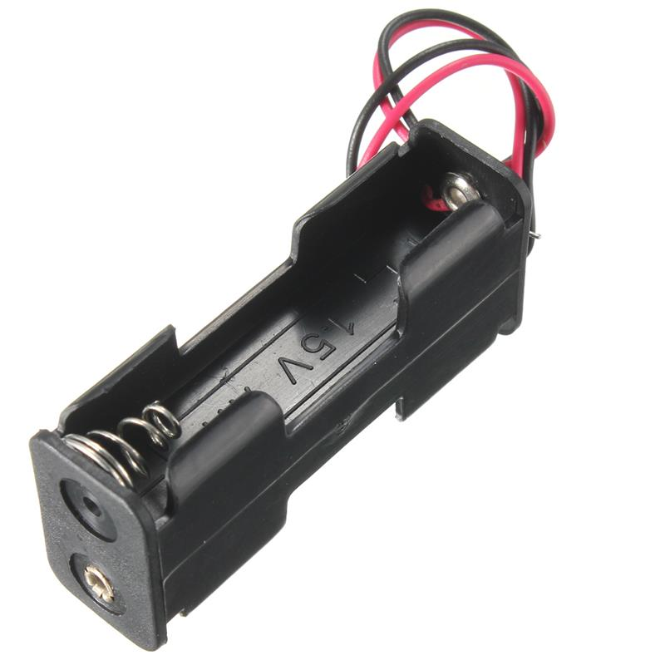
documents/images/bom/bathold.jpg
