lyusupov/SoftRF/documents/images/bom/bmp-280.jpg

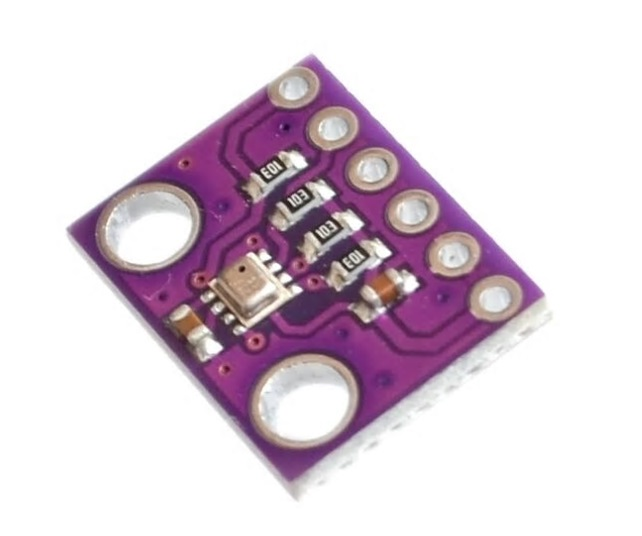
documents/images/bom/bmp-280.jpg
