lyusupov/SoftRF/documents/images/bom/bn880.jpg

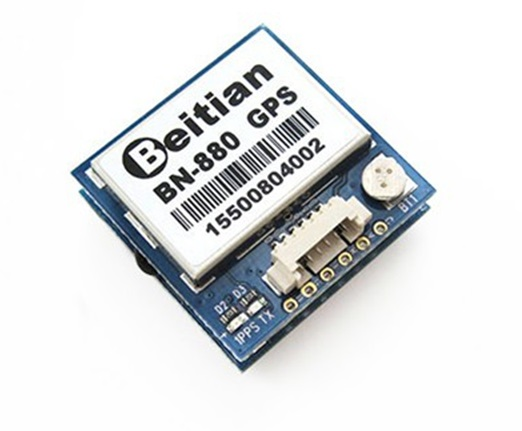
documents/images/bom/bn880.jpg
