lyusupov/SoftRF/documents/images/bom/BPI-PicoW-S3.jpg

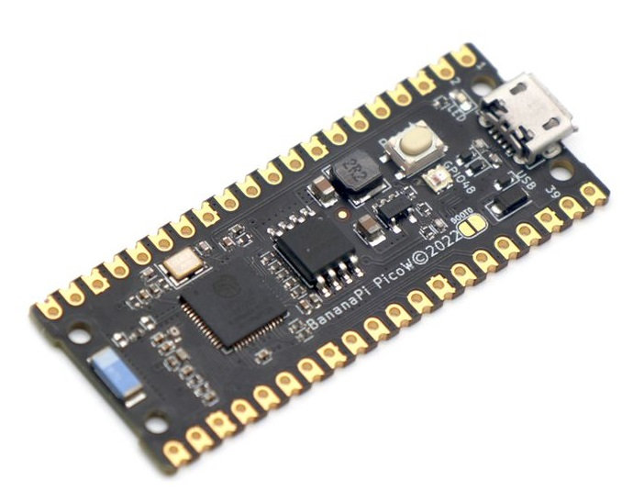
documents/images/bom/BPI-PicoW-S3.jpg
