lyusupov/SoftRF/documents/images/bom/buzzer.jpg

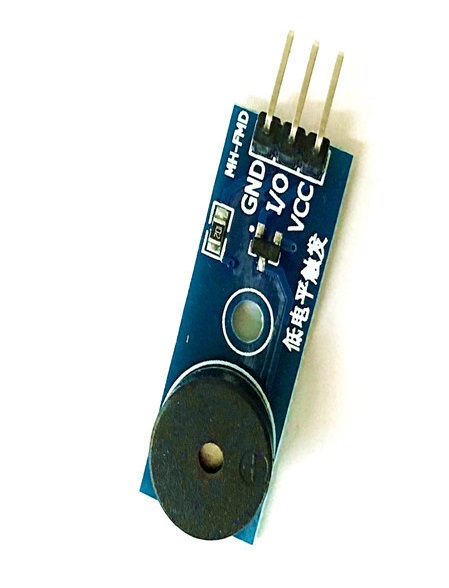
documents/images/bom/buzzer.jpg
