lyusupov/SoftRF/documents/images/bom/C22.jpg

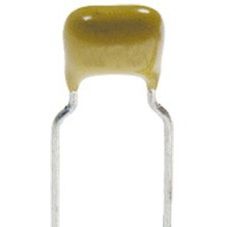
documents/images/bom/C22.jpg
