lyusupov/SoftRF/documents/images/bom/C100.jpg

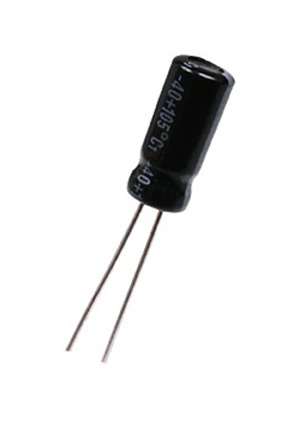
documents/images/bom/C100.jpg
