lyusupov/SoftRF/documents/images/bom/ch341a-clip.jpg

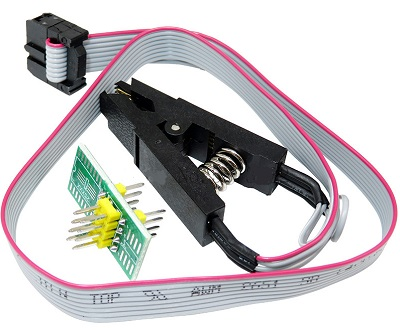
documents/images/bom/ch341a-clip.jpg
