lyusupov/SoftRF/documents/images/bom/ch341a.jpg

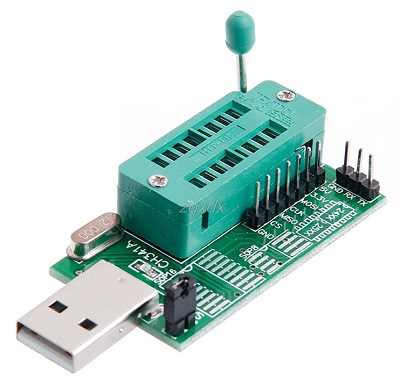
documents/images/bom/ch341a.jpg
