lyusupov/SoftRF/documents/images/bom/cp2102-2.jpg

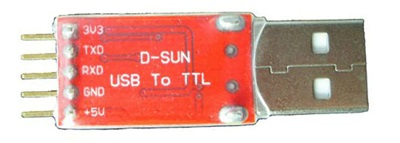
documents/images/bom/cp2102-2.jpg
