lyusupov/SoftRF/documents/images/bom/cp2102.jpg

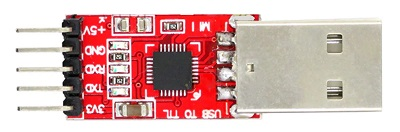
documents/images/bom/cp2102.jpg
