lyusupov/SoftRF/documents/images/bom/CubeCell-GPS.jpg

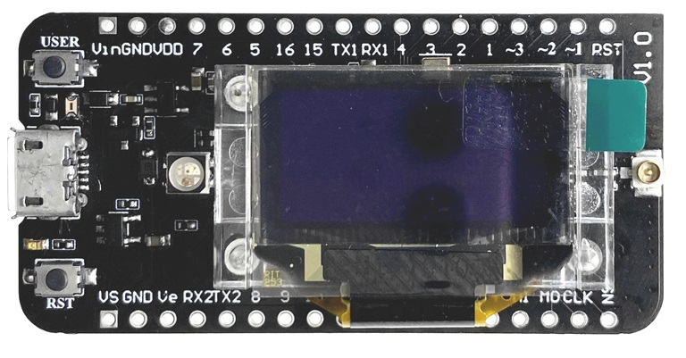
documents/images/bom/CubeCell-GPS.jpg
