lyusupov/SoftRF/documents/images/bom/dcjack.jpg

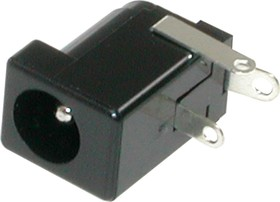
documents/images/bom/dcjack.jpg
