lyusupov/SoftRF/documents/images/bom/decoupler-mount.jpg

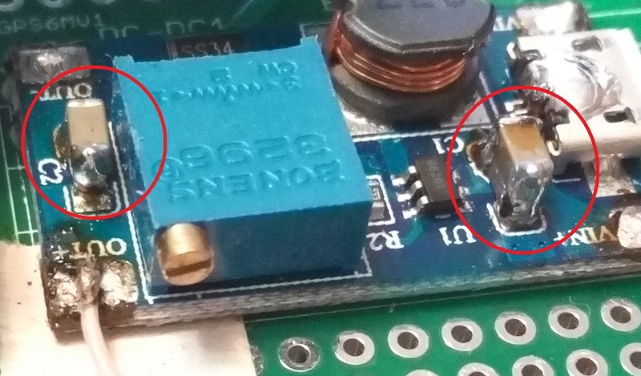
documents/images/bom/decoupler-mount.jpg
