lyusupov/SoftRF/documents/images/bom/esp-01.jpg

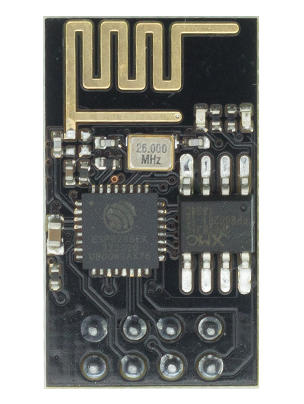
documents/images/bom/esp-01.jpg
