lyusupov/SoftRF/documents/images/bom/esp-c3-12f.jpg

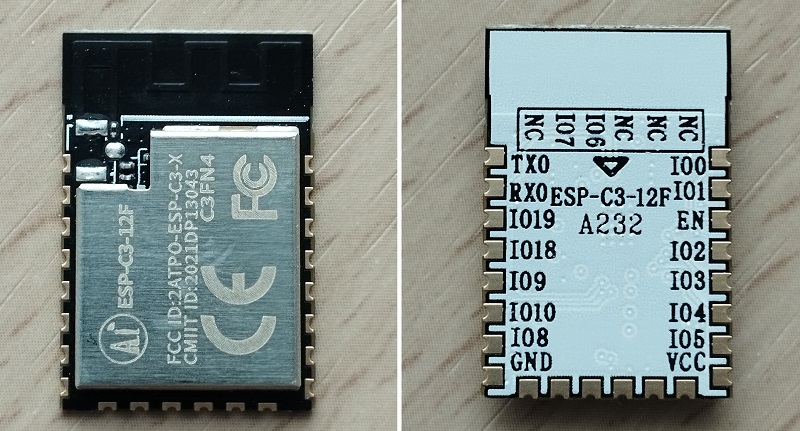
documents/images/bom/esp-c3-12f.jpg
