lyusupov/SoftRF/documents/images/bom/f1x4.jpg

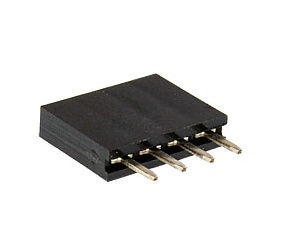
documents/images/bom/f1x4.jpg
