lyusupov/SoftRF/documents/images/bom/f1x6.jpg

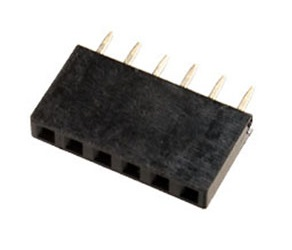
documents/images/bom/f1x6.jpg
