lyusupov/SoftRF/documents/images/bom/f2x7.jpg

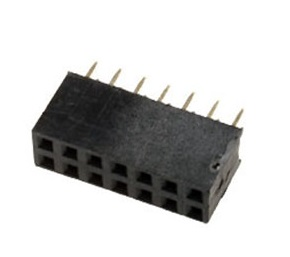
documents/images/bom/f2x7.jpg
