lyusupov/SoftRF/documents/images/bom/fa1x3.jpg

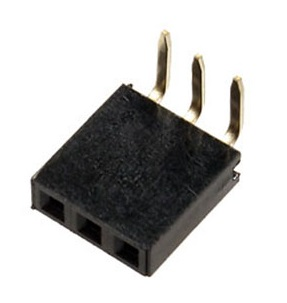
documents/images/bom/fa1x3.jpg
