lyusupov/SoftRF/documents/images/bom/fa1x4.jpg

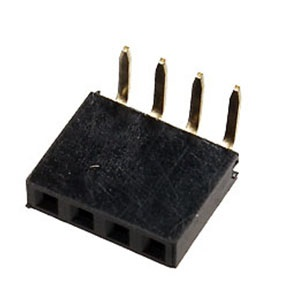
documents/images/bom/fa1x4.jpg
