lyusupov/SoftRF/documents/images/bom/fa1x6.jpg

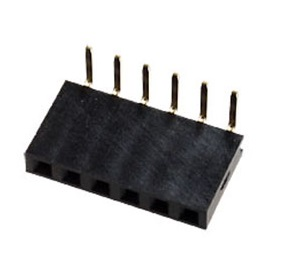
documents/images/bom/fa1x6.jpg
