lyusupov/SoftRF/documents/images/bom/fa2x7.jpg

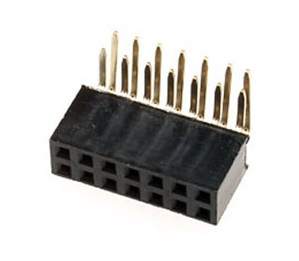
documents/images/bom/fa2x7.jpg
