lyusupov/SoftRF/documents/images/bom/foamtape.jpg

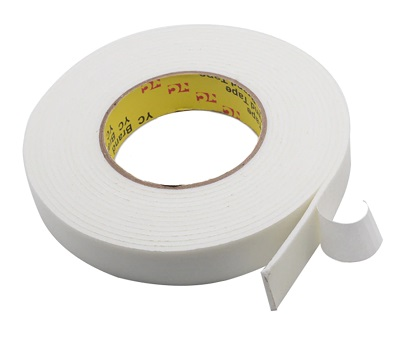
documents/images/bom/foamtape.jpg
