lyusupov/SoftRF/documents/images/bom/gnss-antenna.jpg

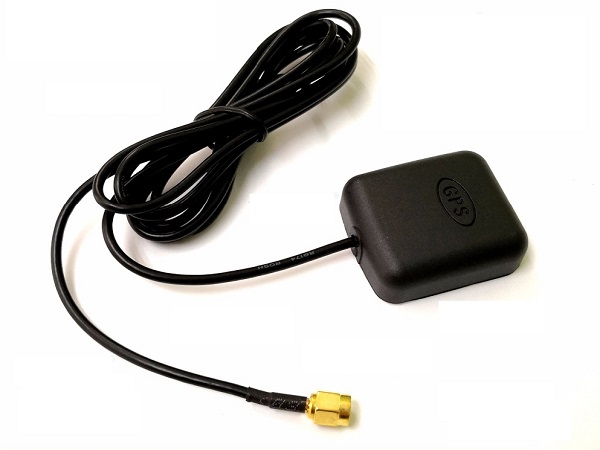
documents/images/bom/gnss-antenna.jpg
