lyusupov/SoftRF/documents/images/bom/gpio_module.jpg

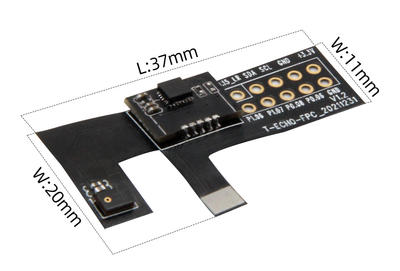
documents/images/bom/gpio_module.jpg
