lyusupov/SoftRF/documents/images/bom/Hackrf_One.jpg

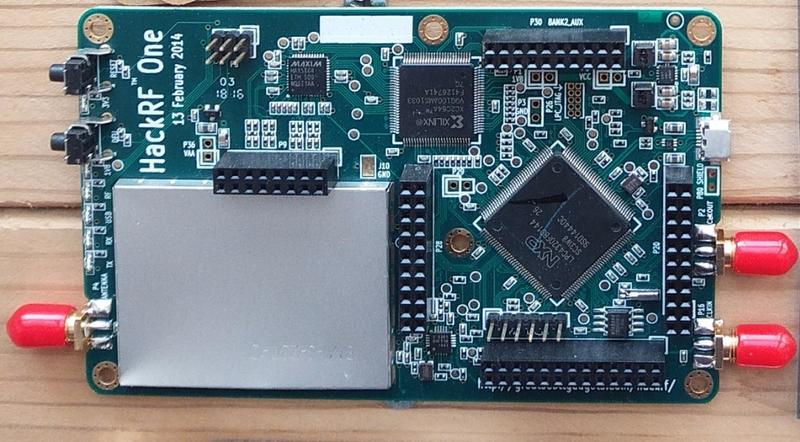
documents/images/bom/Hackrf_One.jpg
