lyusupov/SoftRF/documents/images/bom/hc05.jpg

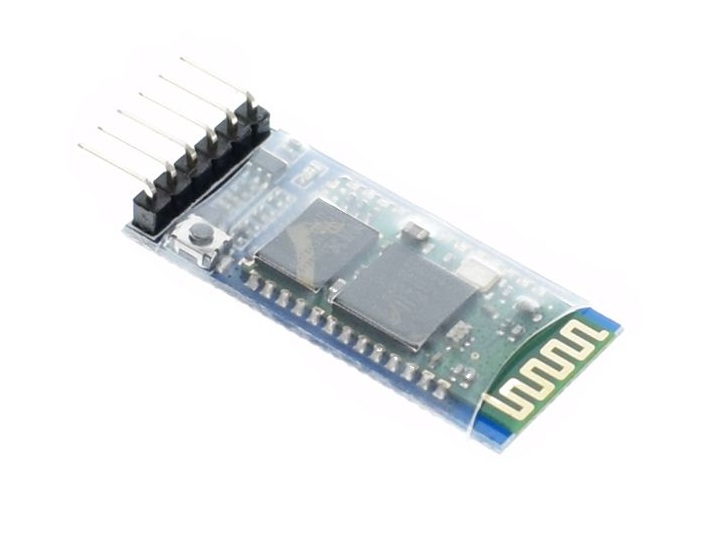
documents/images/bom/hc05.jpg
