lyusupov/SoftRF/documents/images/bom/hm10.jpg

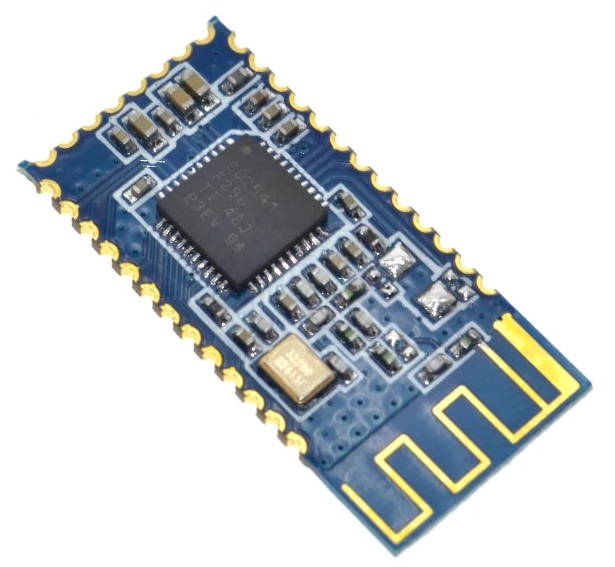
documents/images/bom/hm10.jpg
