lyusupov/SoftRF/documents/images/bom/hw819.jpg

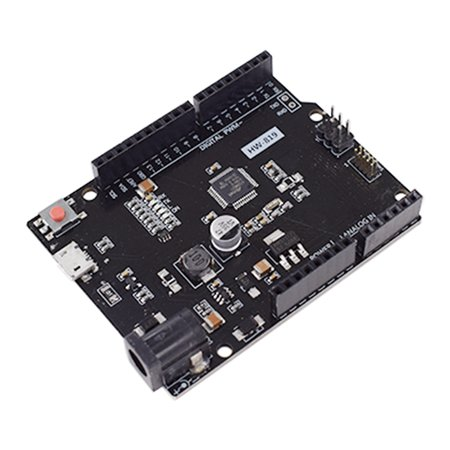
documents/images/bom/hw819.jpg
