lyusupov/SoftRF/documents/images/bom/JST125-602248.jpg

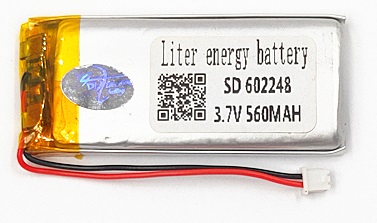
documents/images/bom/JST125-602248.jpg
