lyusupov/SoftRF/documents/images/bom/lipo803040.jpg

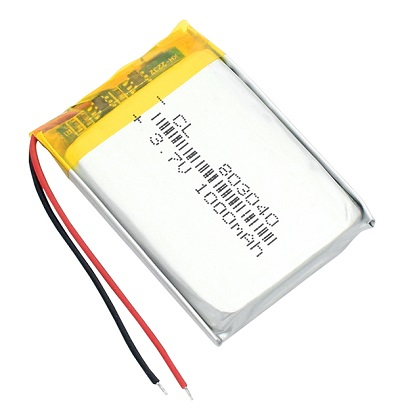
documents/images/bom/lipo803040.jpg
