lyusupov/SoftRF/documents/images/bom/Lora_GPS_Shield_1.jpg

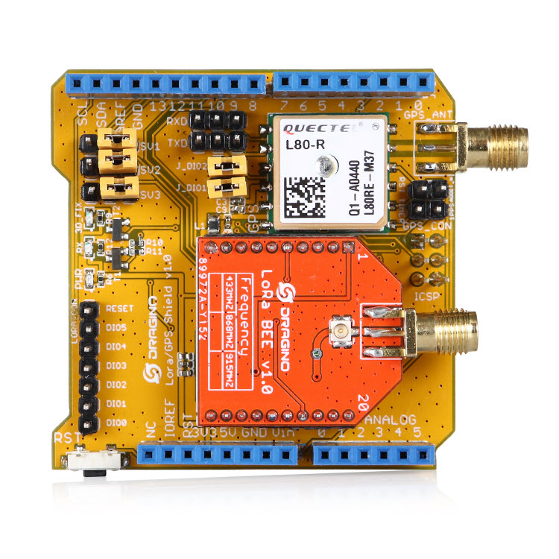
documents/images/bom/Lora_GPS_Shield_1.jpg
