lyusupov/SoftRF/documents/images/bom/m40.jpg

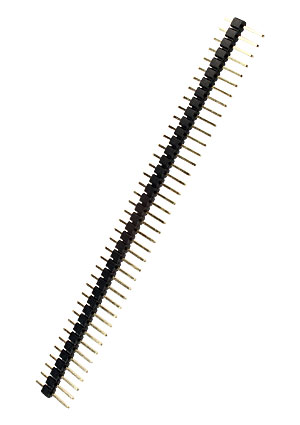
documents/images/bom/m40.jpg
