lyusupov/SoftRF/documents/images/bom/ma40.jpg

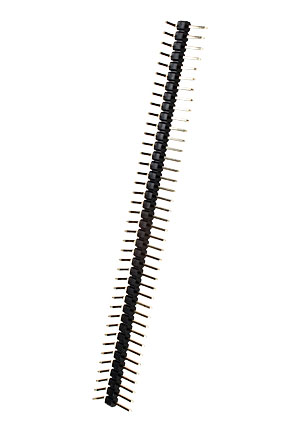
documents/images/bom/ma40.jpg
