lyusupov/SoftRF/documents/images/bom/max3232.jpg

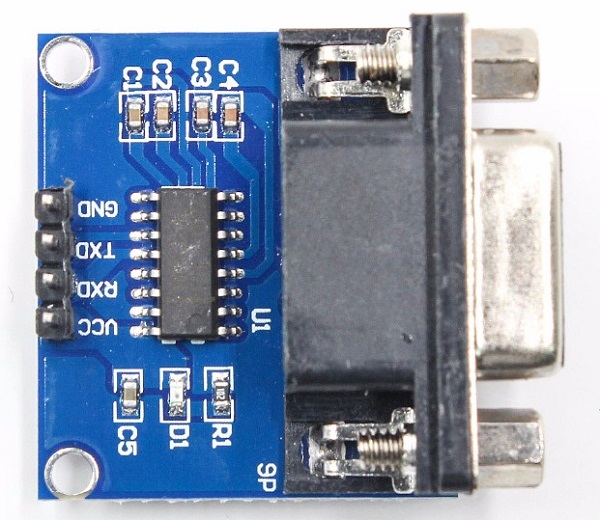
documents/images/bom/max3232.jpg
