lyusupov/SoftRF/documents/images/bom/mhf3.jpg

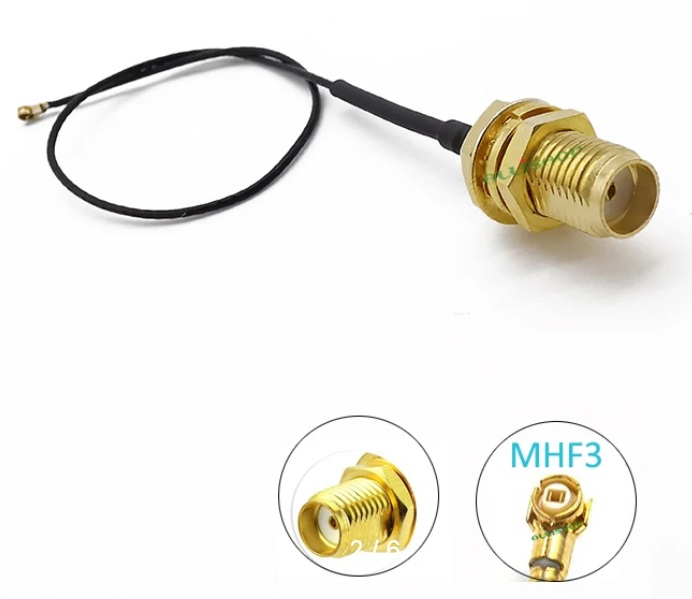
documents/images/bom/mhf3.jpg
