lyusupov/SoftRF/documents/images/bom/microSD.jpg

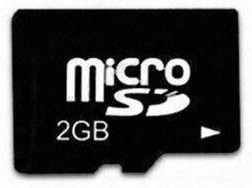
documents/images/bom/microSD.jpg
