lyusupov/SoftRF/documents/images/bom/mt3608.jpg

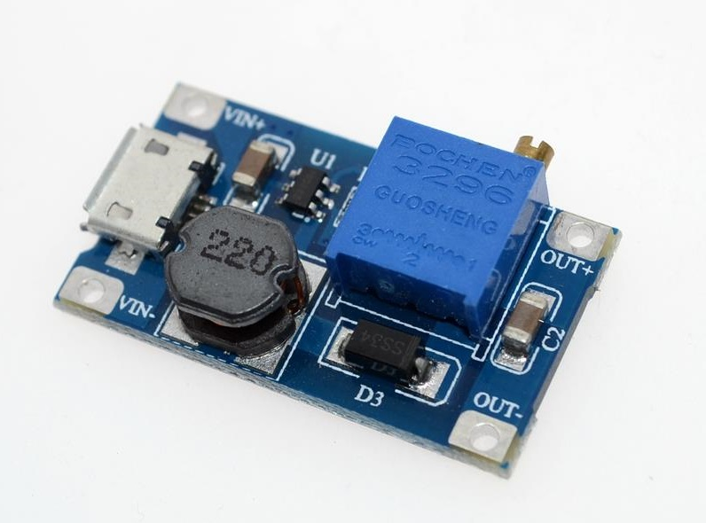
documents/images/bom/mt3608.jpg
