lyusupov/SoftRF/documents/images/bom/musb-typec.jpg

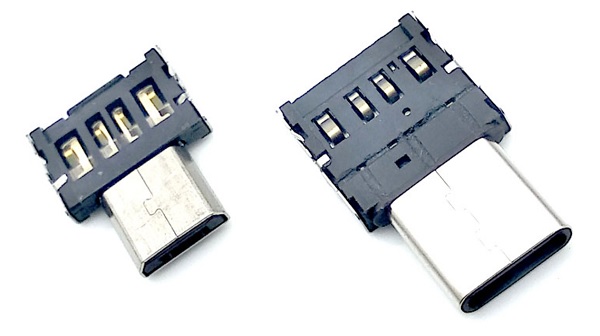
documents/images/bom/musb-typec.jpg
