lyusupov/SoftRF/documents/images/bom/Ni-Zn.jpg

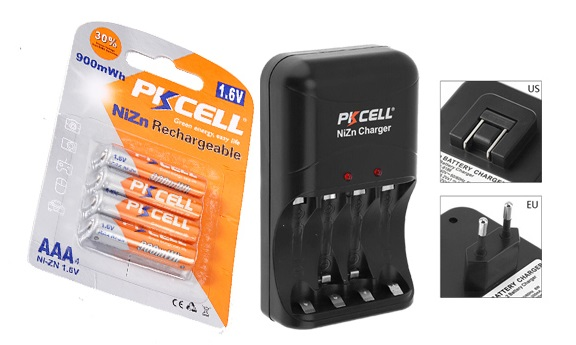
documents/images/bom/Ni-Zn.jpg
