lyusupov/SoftRF/documents/images/bom/nodemcu.jpg

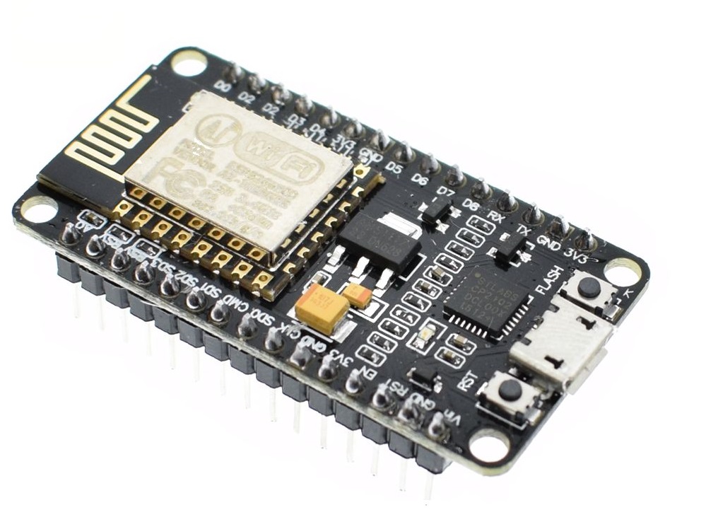
documents/images/bom/nodemcu.jpg
