lyusupov/SoftRF/documents/images/bom/oled-096.jpg

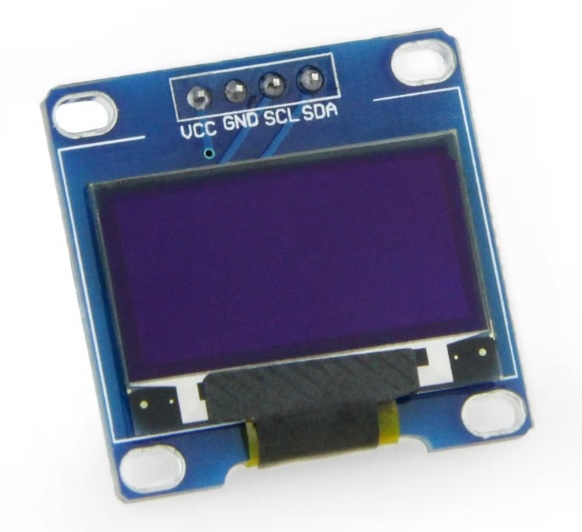
documents/images/bom/oled-096.jpg
