lyusupov/SoftRF/documents/images/bom/pico-ups-b-2.jpg

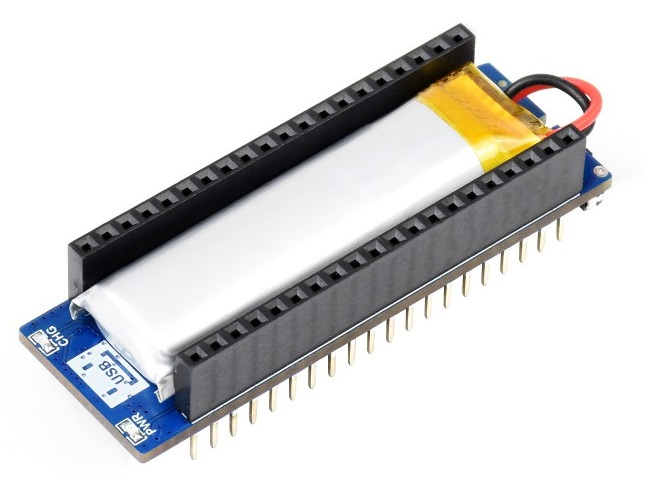
documents/images/bom/pico-ups-b-2.jpg
