lyusupov/SoftRF/documents/images/bom/picowh.jpg

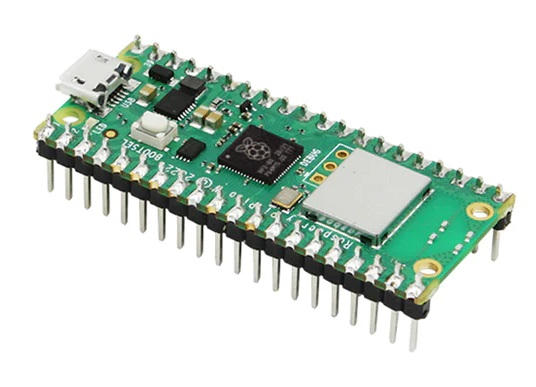
documents/images/bom/picowh.jpg
