lyusupov/SoftRF/documents/images/bom/pld14.jpg

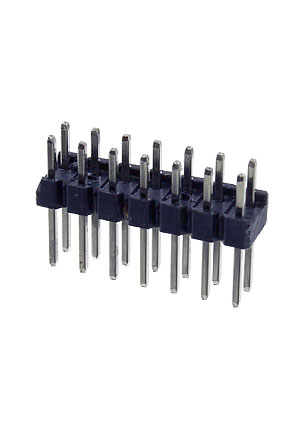
documents/images/bom/pld14.jpg
