lyusupov/SoftRF/documents/images/bom/PortaPack_H2.jpg

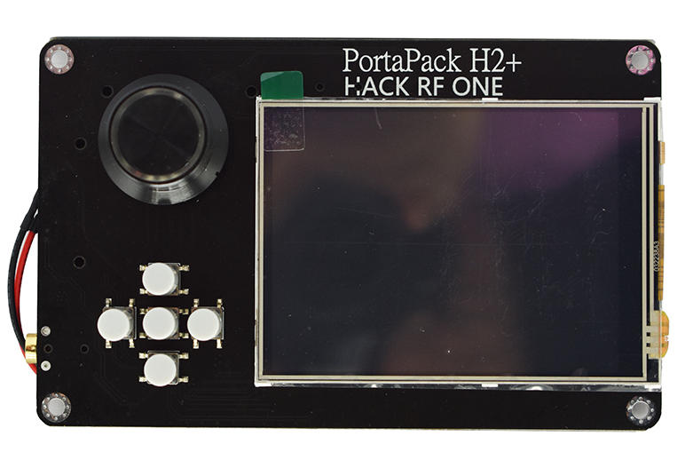
documents/images/bom/PortaPack_H2.jpg
