lyusupov/SoftRF/documents/images/bom/protopcb.jpg

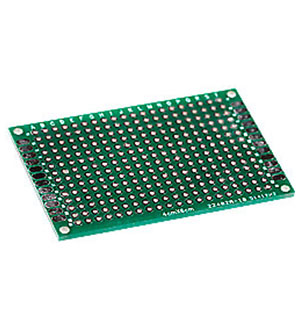
documents/images/bom/protopcb.jpg
