lyusupov/SoftRF/documents/images/bom/rfm95-868.jpg

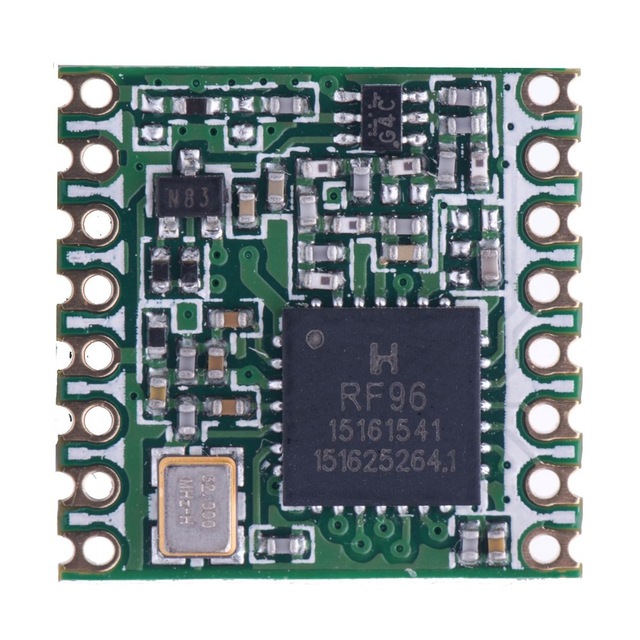
documents/images/bom/rfm95-868.jpg
