lyusupov/SoftRF/documents/images/bom/rfm95w-nrf905-1-0.jpg

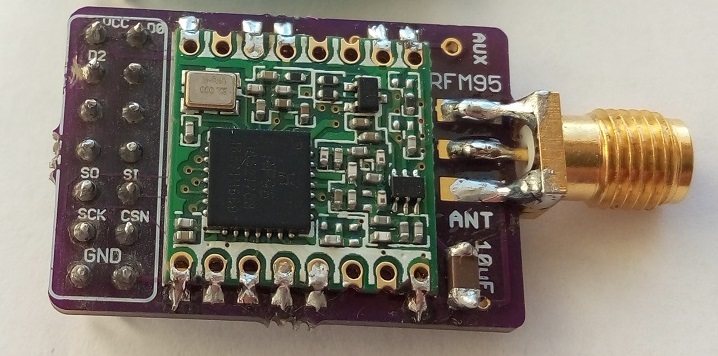
documents/images/bom/rfm95w-nrf905-1-0.jpg
