lyusupov/SoftRF/documents/images/bom/samsung-18650.jpg

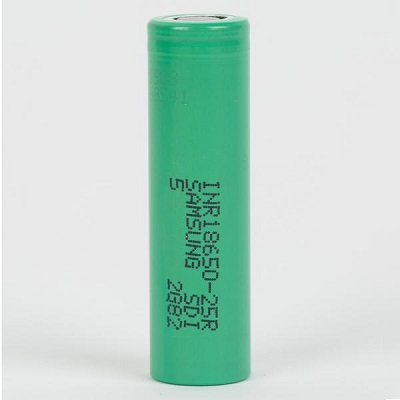
documents/images/bom/samsung-18650.jpg
