lyusupov/SoftRF/documents/images/bom/SMA-IPEX.jpg

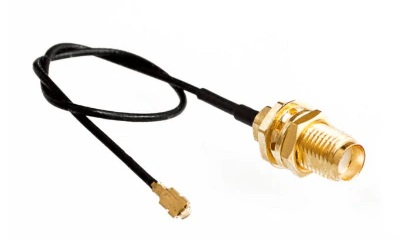
documents/images/bom/SMA-IPEX.jpg
