lyusupov/SoftRF/documents/images/bom/sma-khd.jpg

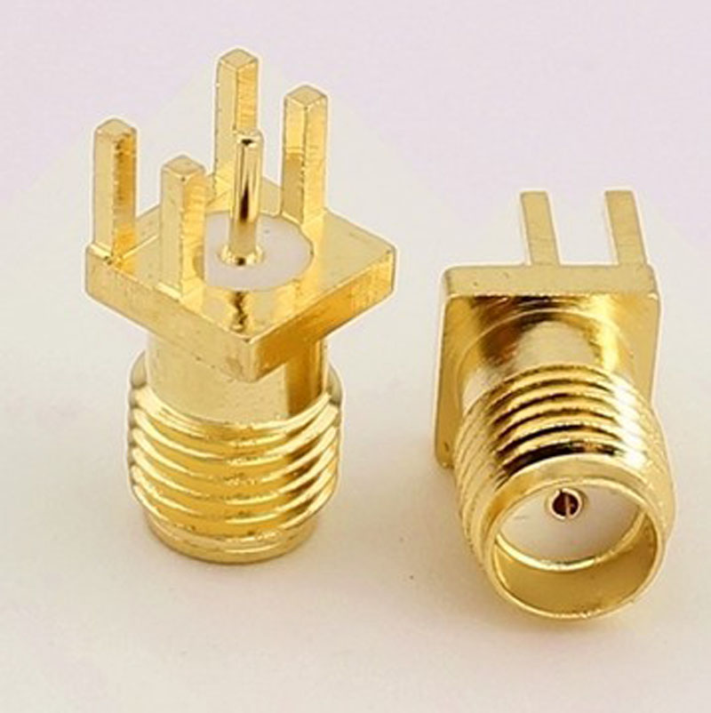
documents/images/bom/sma-khd.jpg
