lyusupov/SoftRF/documents/images/bom/switch.jpg

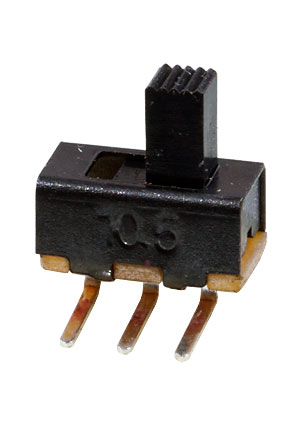
documents/images/bom/switch.jpg
