lyusupov/SoftRF/documents/images/bom/t3c6-1.jpg

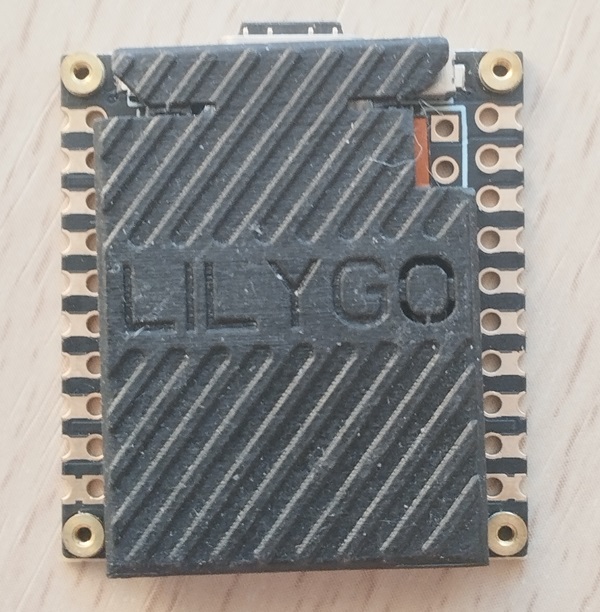
documents/images/bom/t3c6-1.jpg
