lyusupov/SoftRF/documents/images/bom/t3c6-2.jpg

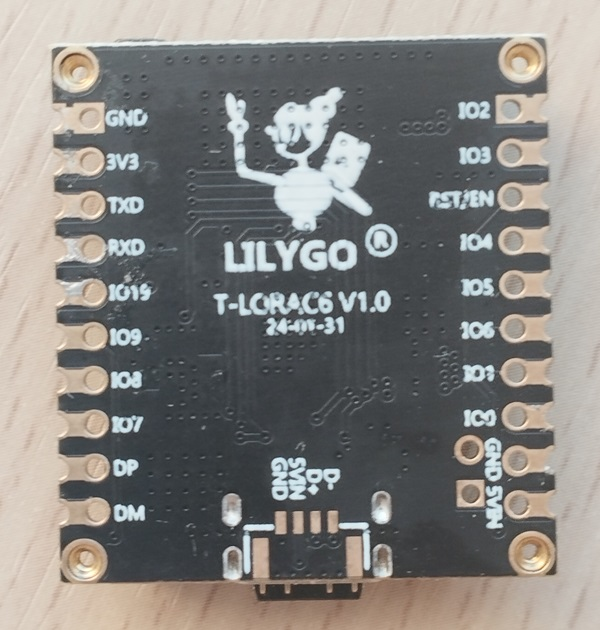
documents/images/bom/t3c6-2.jpg
