lyusupov/SoftRF/documents/images/bom/t3c6-3.jpg

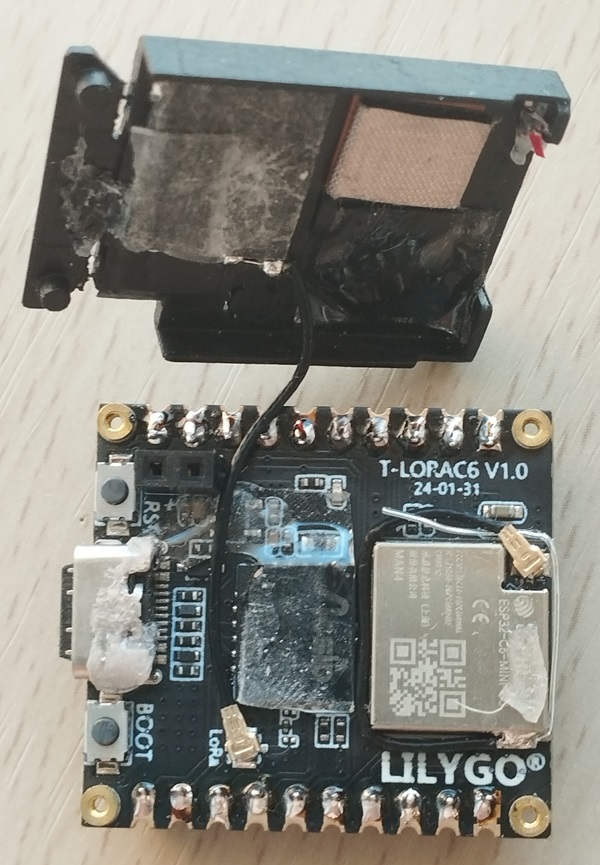
documents/images/bom/t3c6-3.jpg
