lyusupov/SoftRF/documents/images/bom/t-dongle-1.jpg

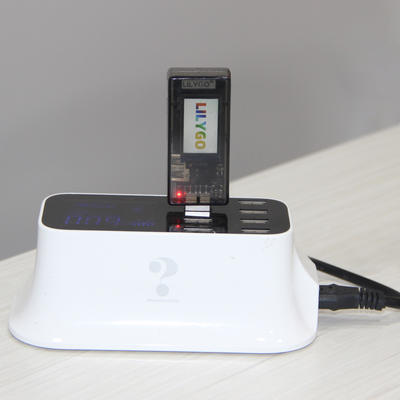
documents/images/bom/t-dongle-1.jpg
