lyusupov/SoftRF/documents/images/bom/t-dongle-2.jpg

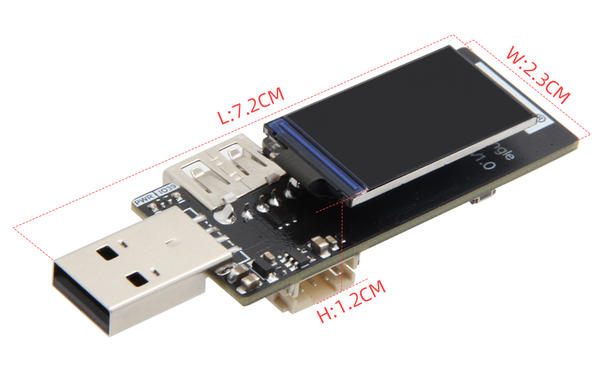
documents/images/bom/t-dongle-2.jpg
