lyusupov/SoftRF/documents/images/bom/t-dongle-4.jpg

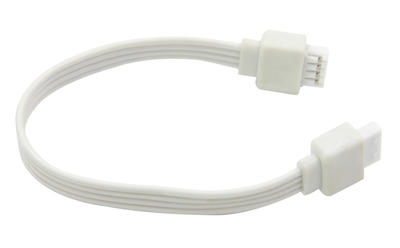
documents/images/bom/t-dongle-4.jpg
