lyusupov/SoftRF/documents/images/bom/t-echo-1.jpg

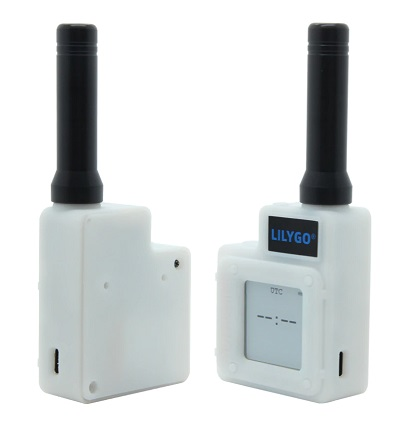
documents/images/bom/t-echo-1.jpg
