lyusupov/SoftRF/documents/images/bom/t-echo-2.jpg

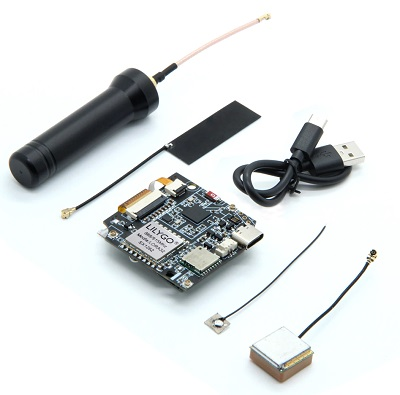
documents/images/bom/t-echo-2.jpg
