lyusupov/SoftRF/documents/images/bom/t-echo-3.jpg

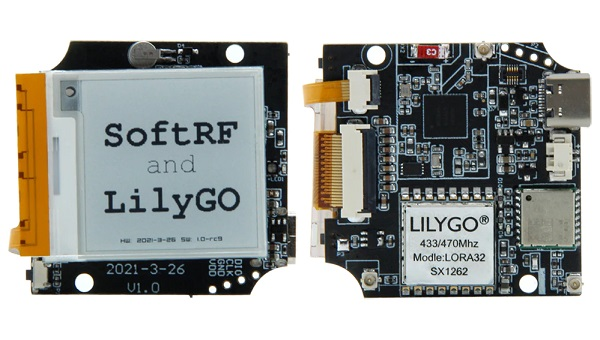
documents/images/bom/t-echo-3.jpg
