lyusupov/SoftRF/documents/images/bom/t-motion.jpg

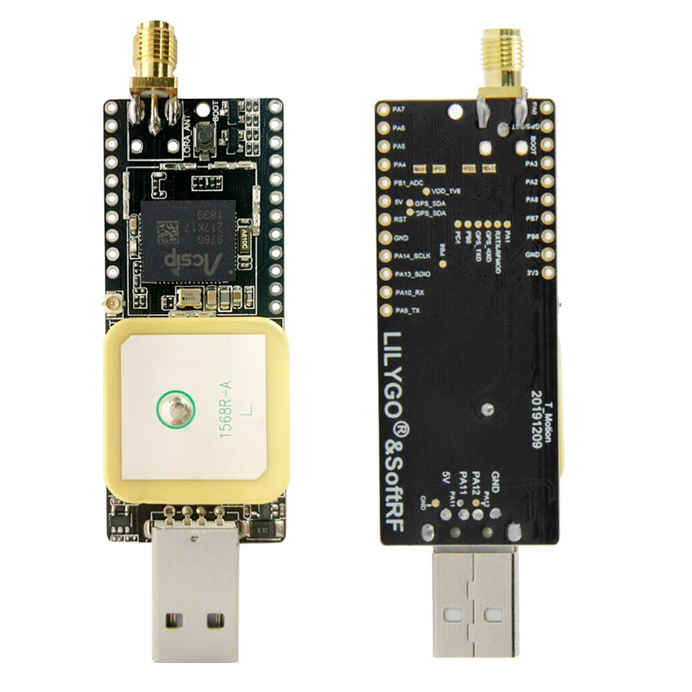
documents/images/bom/t-motion.jpg
