lyusupov/SoftRF/documents/images/bom/tbeam_variants.jpg

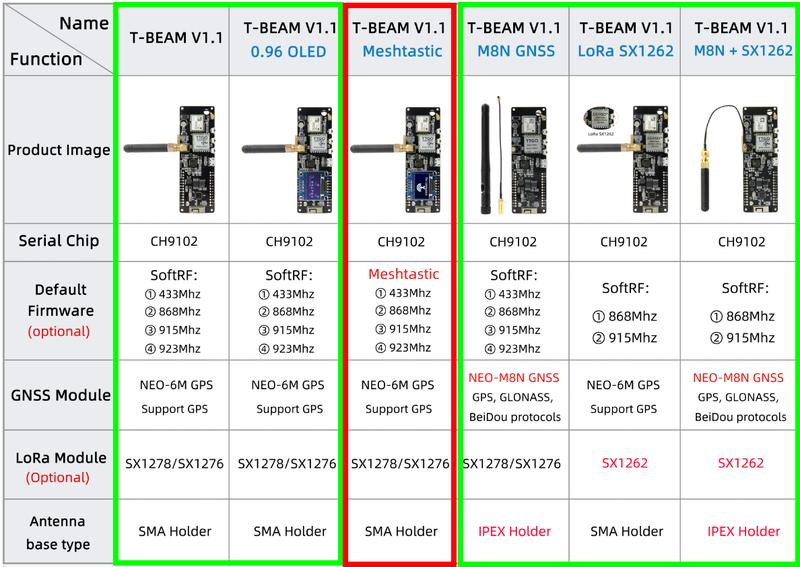
documents/images/bom/tbeam_variants.jpg
