lyusupov/SoftRF/documents/images/bom/ticm-1.jpg

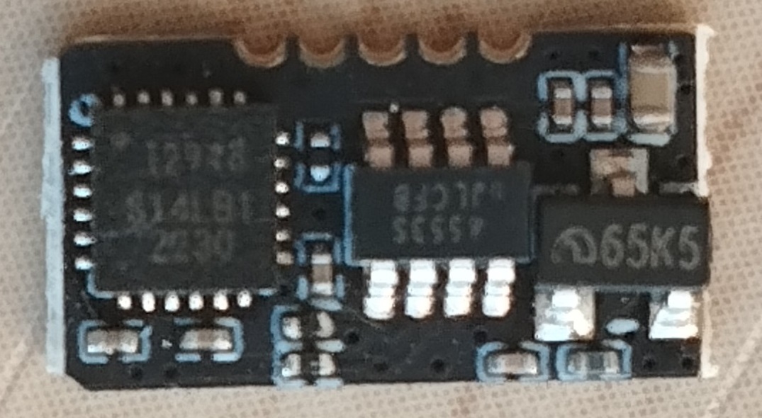
documents/images/bom/ticm-1.jpg
