lyusupov/SoftRF/documents/images/bom/ticm-2.jpg

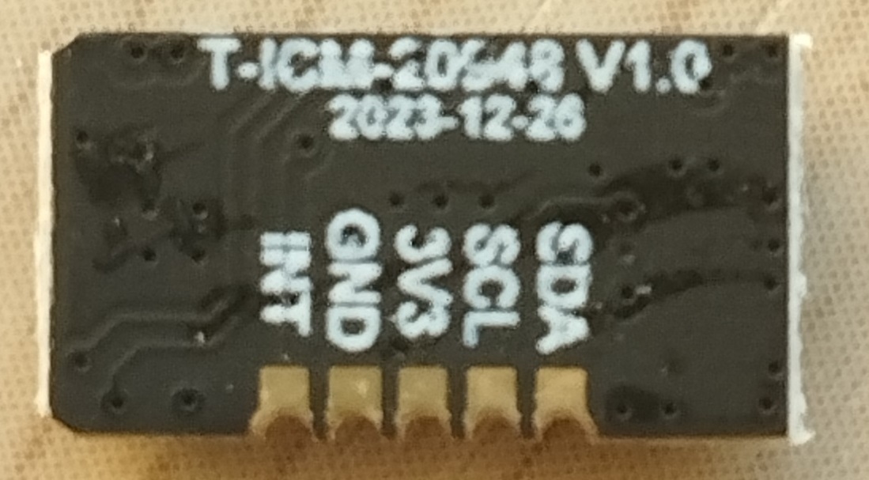
documents/images/bom/ticm-2.jpg
