lyusupov/SoftRF/documents/images/bom/WT0132C6-S5.jpg

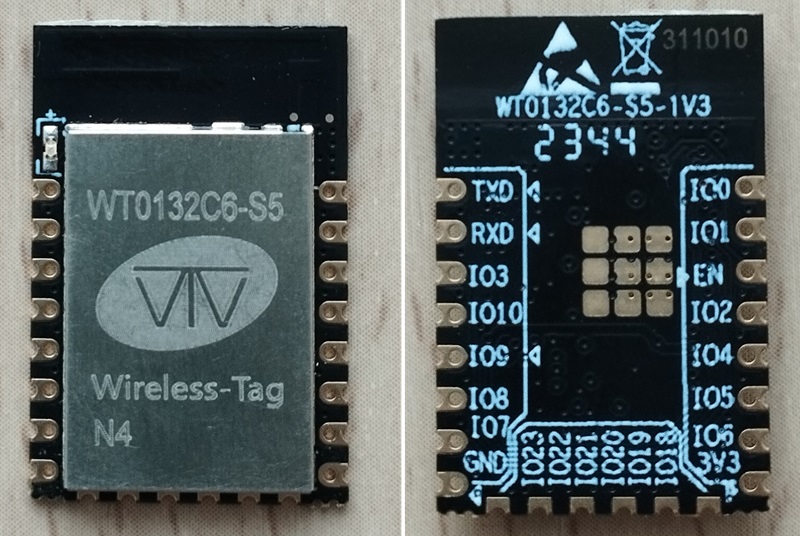
documents/images/bom/WT0132C6-S5.jpg
