lyusupov/SoftRF/documents/images/bom/XIAO-1.jpg

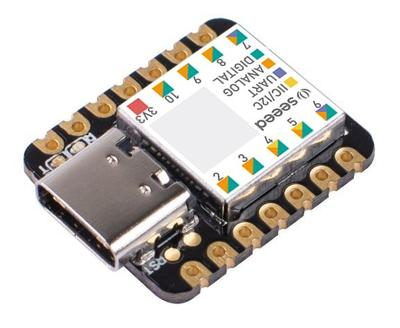
documents/images/bom/XIAO-1.jpg
