lyusupov/SoftRF/case/Dongle/SoftRF-Case-Dongle-Cap-16mm.stl

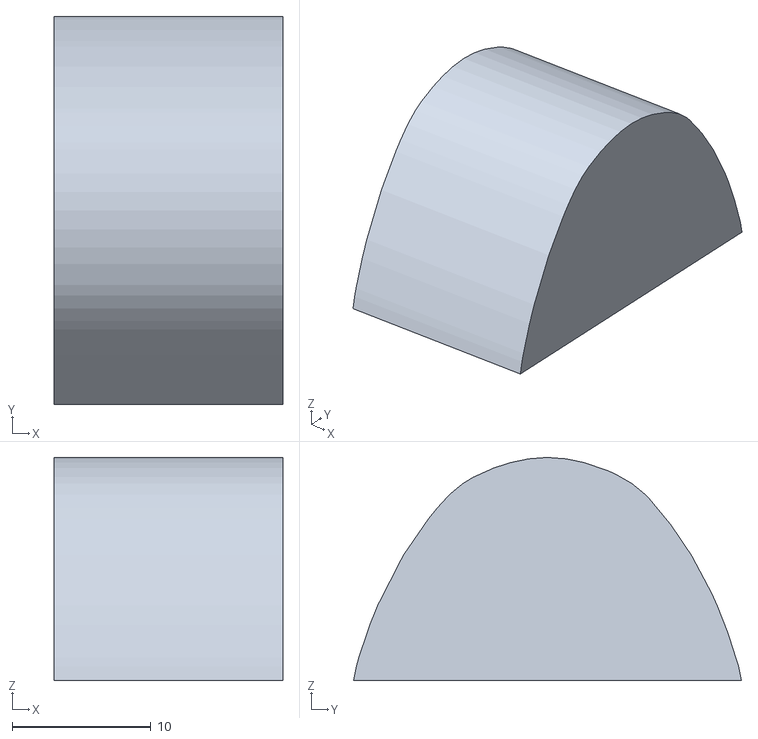
[picture p420: CAD file, 2019-12-11]
case/Dongle/SoftRF-Case-Dongle-Cap-16mm.stl
16.5 x 28.0 x 16.1
