lyusupov/SoftRF/case/Mini/SoftRF-Case-Mini-Lid.stl

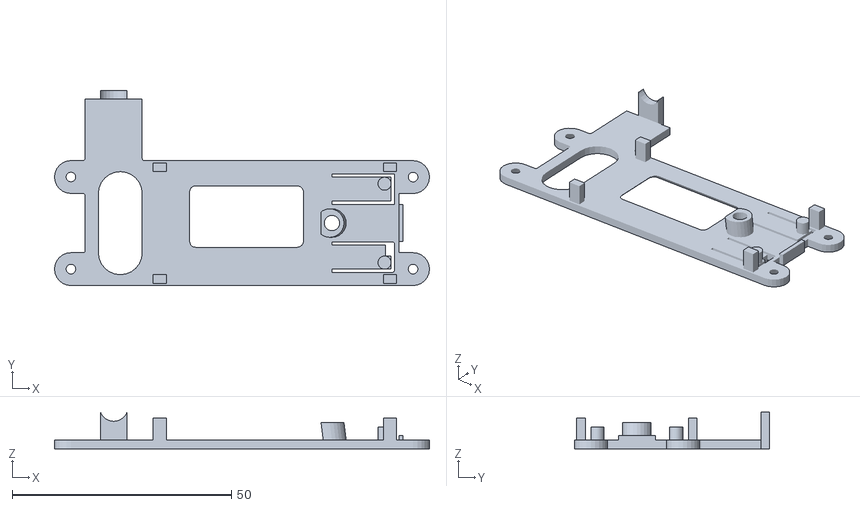
[picture p421: CAD file, 2020-11-10]
case/Mini/SoftRF-Case-Mini-Lid.stl
85.5 x 44.5 x 8.32
