lyusupov/SoftRF/case/Dongle/SoftRF-Case-Dongle-Battery-Body.stl

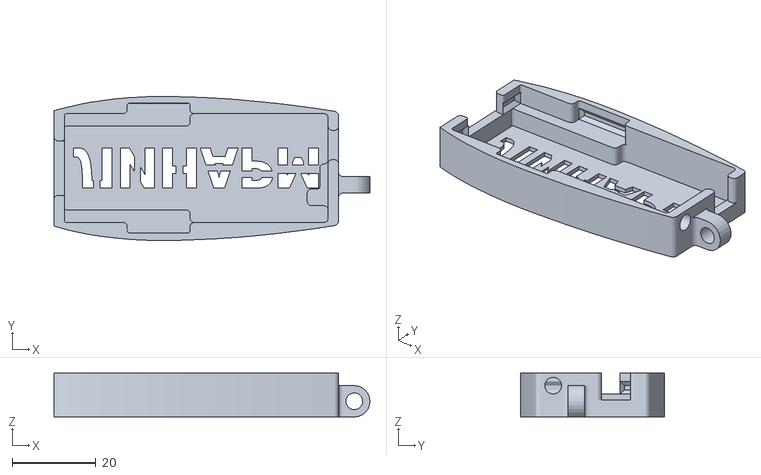
[picture p423: CAD file, 2019-12-09]
case/Dongle/SoftRF-Case-Dongle-Battery-Body.stl
75.5 x 34.4 x 10.5
