lyusupov/SoftRF/case/SkyView/SkyView-Case-EZ-Holder.stl

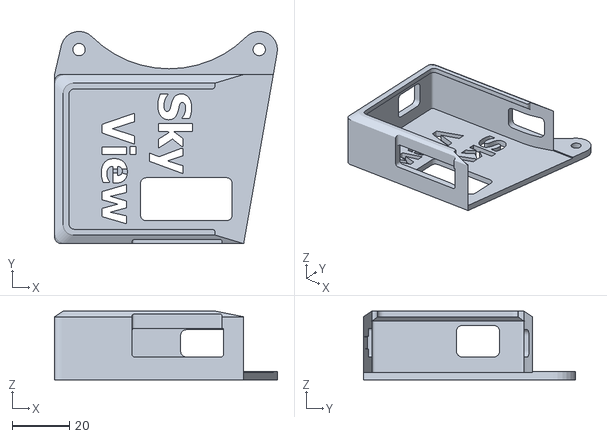
[picture p424: CAD file, 2019-06-07]
case/SkyView/SkyView-Case-EZ-Holder.stl
77.8 x 74.1 x 24.0
