lyusupov/SoftRF/case/Dongle/SoftRF-Case-Dongle-OLED-Lid.stl

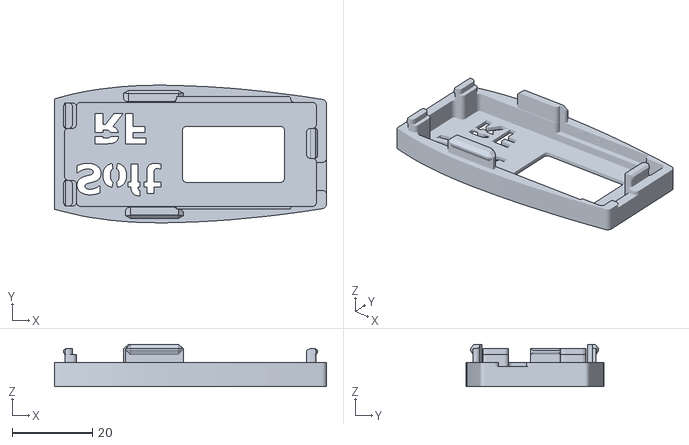
[picture p425: CAD file, 2019-12-09]
case/Dongle/SoftRF-Case-Dongle-OLED-Lid.stl
68.0 x 34.4 x 10.5
