lyusupov/SoftRF/case/SkyView/SkyView-Case-EZ-Speaker-40mm.stl

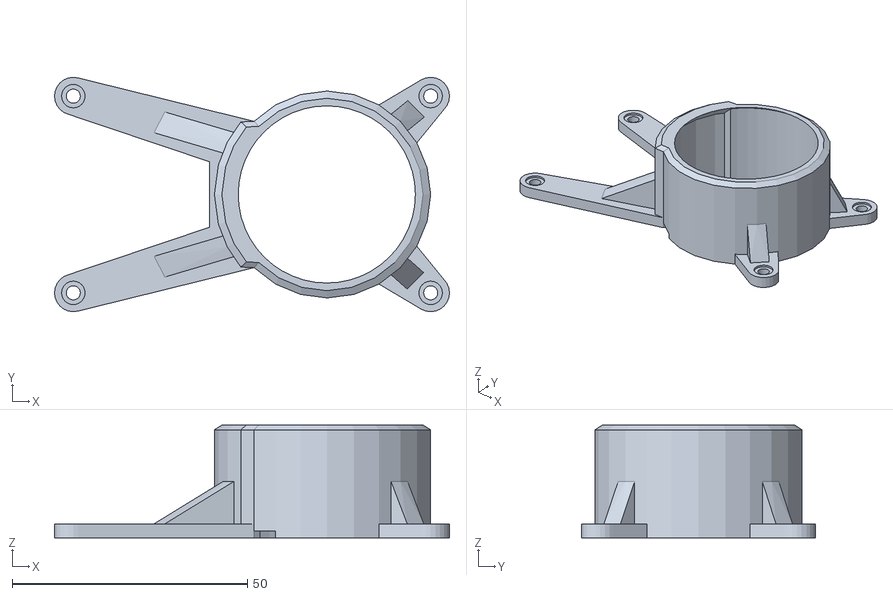
[picture p426: CAD file, 2019-06-06]
case/SkyView/SkyView-Case-EZ-Speaker-40mm.stl
84.0 x 49.8 x 24.0
