lyusupov/SoftRF/case/Dongle/SoftRF-Case-Dongle-Slim-Cap.stl

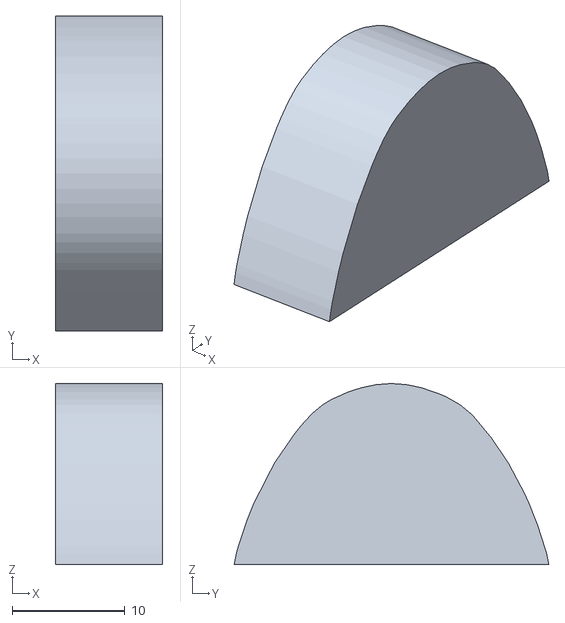
[picture p427: CAD file, 2019-12-03]
case/Dongle/SoftRF-Case-Dongle-Slim-Cap.stl
9.50 x 28.0 x 16.1
