lyusupov/SoftRF/case/SkyView/SkyView-Case-EZ-Face.stl

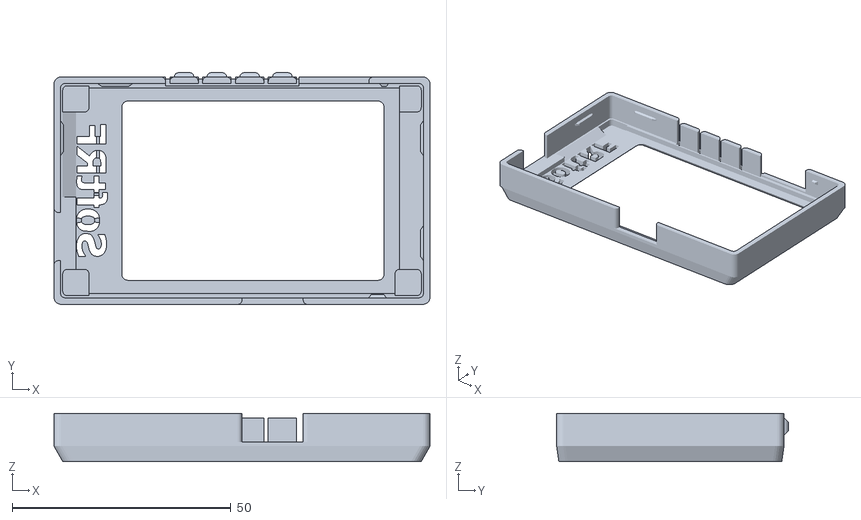
[picture p428: CAD file, 2019-05-20]
case/SkyView/SkyView-Case-EZ-Face.stl
86.0 x 53.0 x 11.0
