lyusupov/SoftRF/case/v5/SoftRF-Case-Prime2-Lid-V08.stl

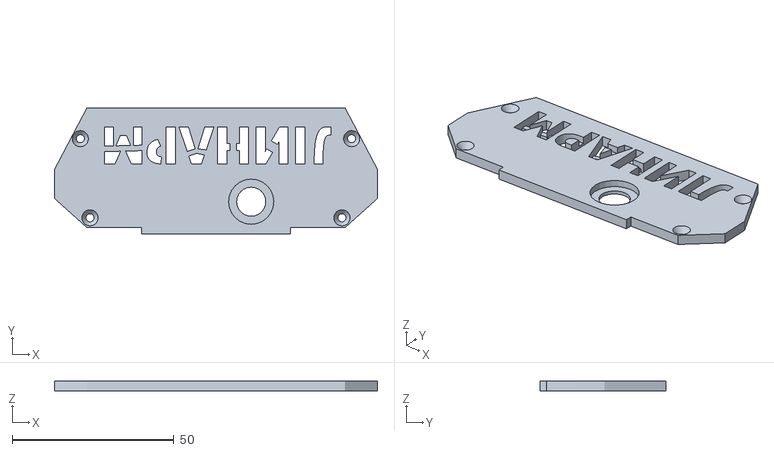
[picture p429: CAD file, 2019-06-27]
case/v5/SoftRF-Case-Prime2-Lid-V08.stl
100.0 x 39.0 x 3.00
