lyusupov/SoftRF/case/Dongle/SoftRF-Case-Dongle-Slim-Body.stl

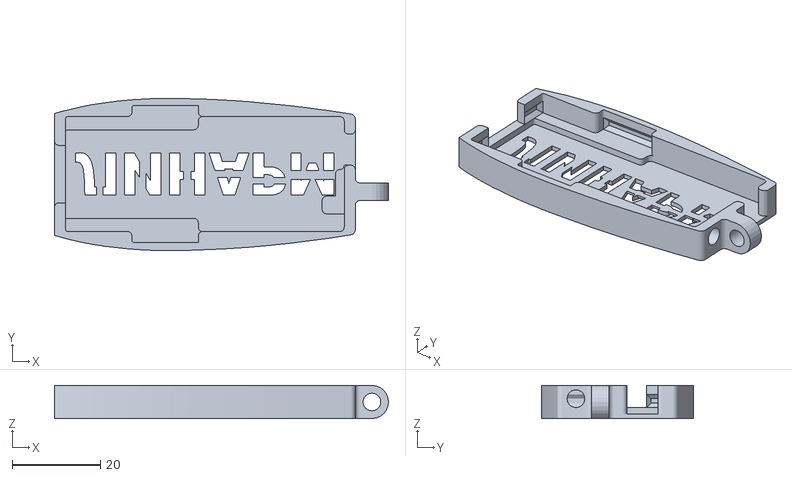
[picture p430: CAD file, 2019-12-03]
case/Dongle/SoftRF-Case-Dongle-Slim-Body.stl
75.5 x 34.4 x 7.50
