lyusupov/SoftRF/case/v5/SoftRF-Case-Prime2-OLED-Front-TTGO.stl

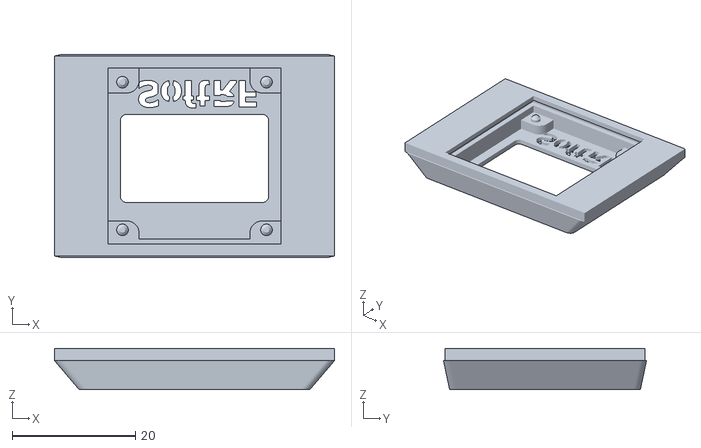
[picture p431: CAD file, 2019-06-27]
case/v5/SoftRF-Case-Prime2-OLED-Front-TTGO.stl
45.5 x 33.0 x 6.70
