lyusupov/SoftRF/case/v5/SoftRF-Case-Prime2-OLED-Rear.stl

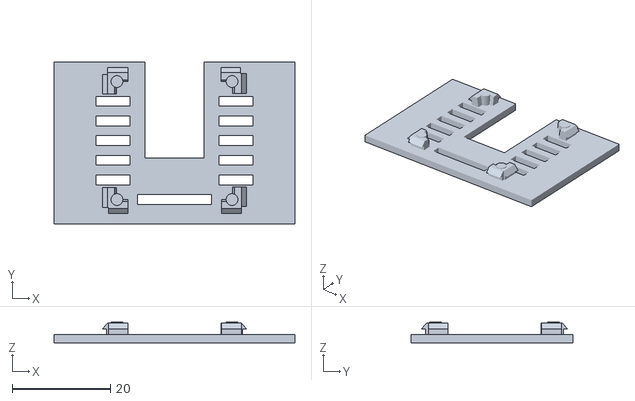
[picture p432: CAD file, 2018-08-16]
case/v5/SoftRF-Case-Prime2-OLED-Rear.stl
49.0 x 33.0 x 4.25
