lyusupov/SoftRF/case/v5/SoftRF-Case-Prime2-OLED-Front.stl

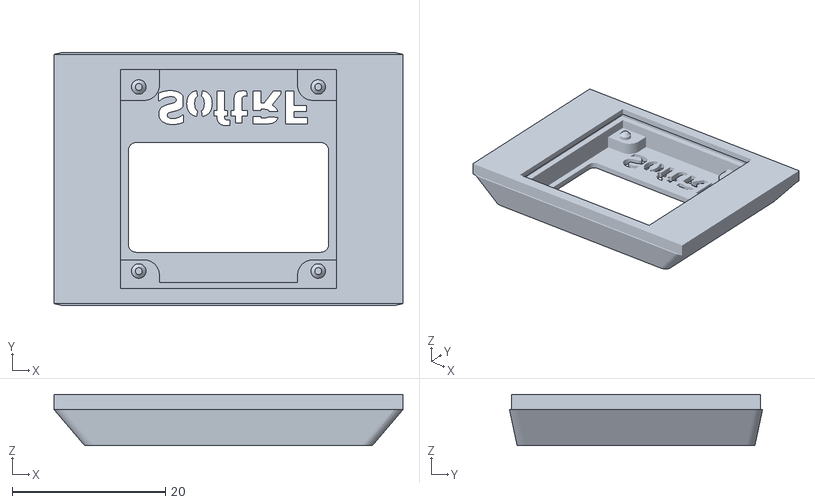
[picture p433: CAD file, 2018-08-16]
case/v5/SoftRF-Case-Prime2-OLED-Front.stl
45.5 x 33.0 x 6.70
