lyusupov/SoftRF/case/v5/SoftRF-Case-Prime2-Face.stl

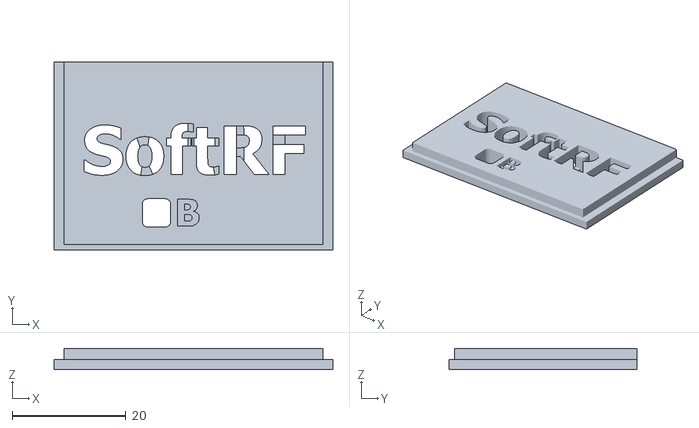
[picture p434: CAD file, 2018-08-08]
case/v5/SoftRF-Case-Prime2-Face.stl
49.0 x 33.0 x 3.75
