lyusupov/SoftRF/documents/images/FANET_testbed.jpg

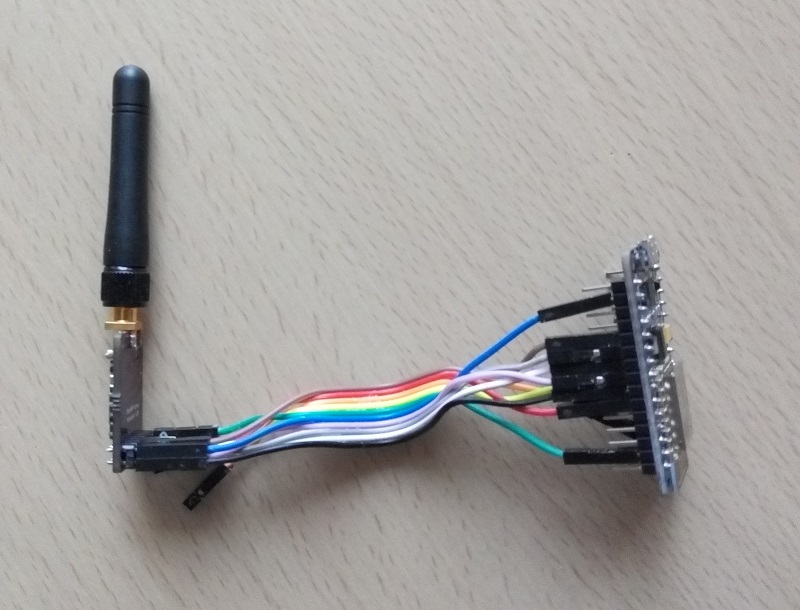
documents/images/FANET_testbed.jpg
