lyusupov/SoftRF/documents/images/Validation_DIY_OGN_tracker.jpg

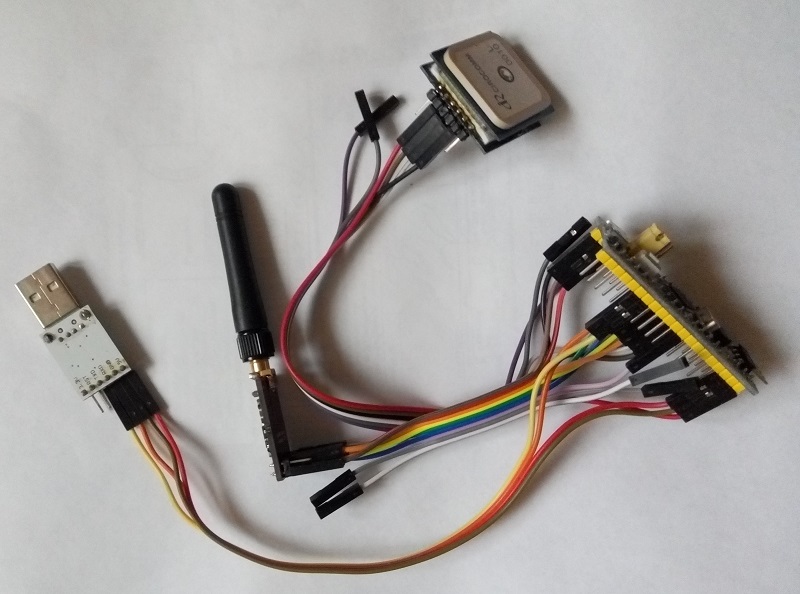
documents/images/Validation_DIY_OGN_tracker.jpg
