lyusupov/SoftRF/documents/images/Validation_DIY_PAW_bridge.jpg

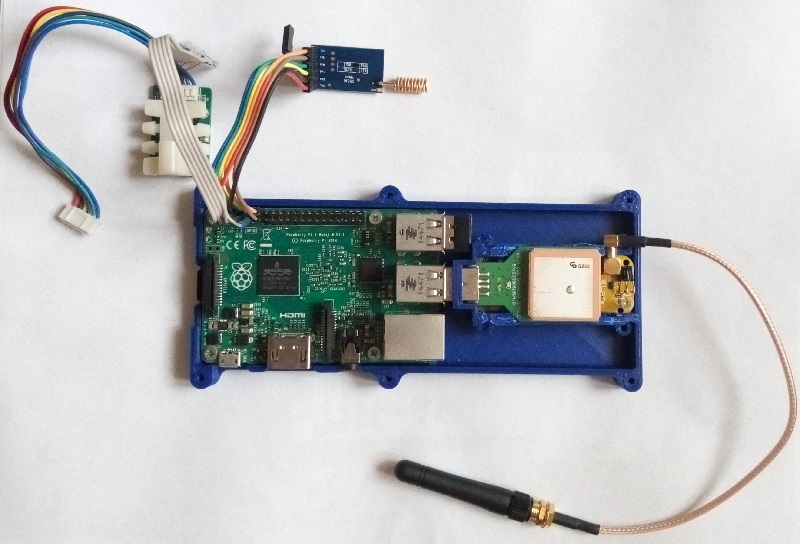
documents/images/Validation_DIY_PAW_bridge.jpg
