lyusupov/SoftRF/documents/images/Validation_FANET_2.JPG

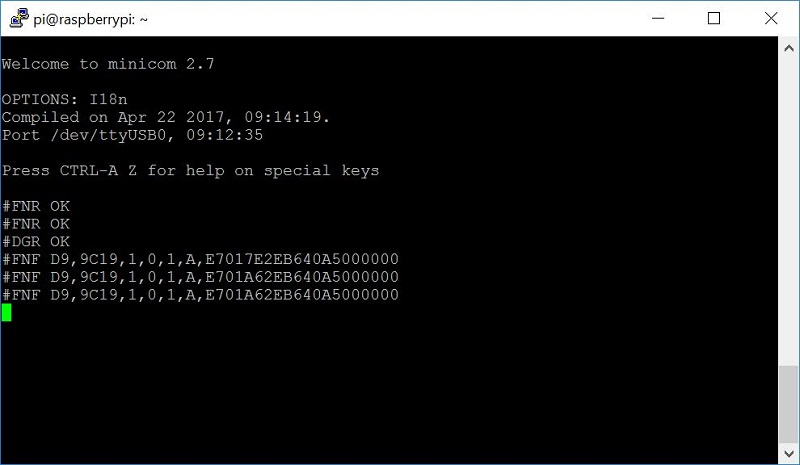
documents/images/Validation_FANET_2.JPG
