lyusupov/SoftRF/documents/images/Validation_FANET_3.JPG

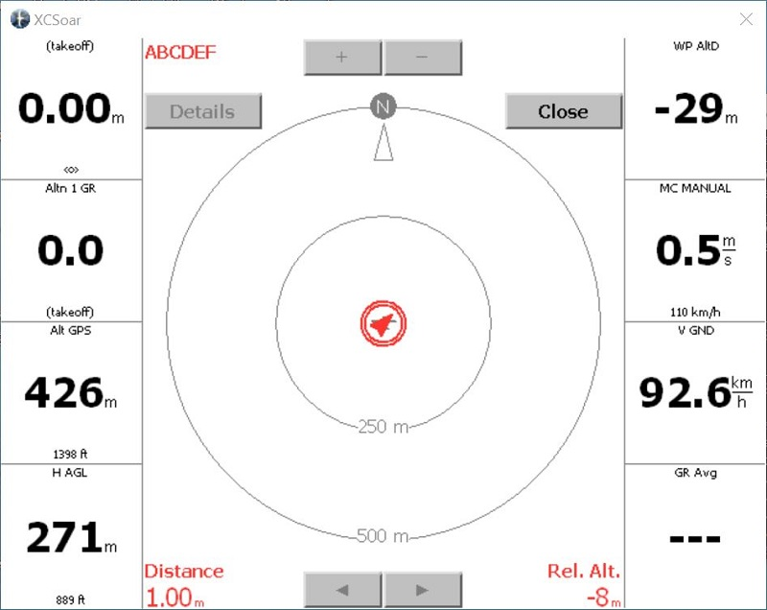
documents/images/Validation_FANET_3.JPG
