lyusupov/SoftRF/documents/images/Validation_OGN_1.JPG

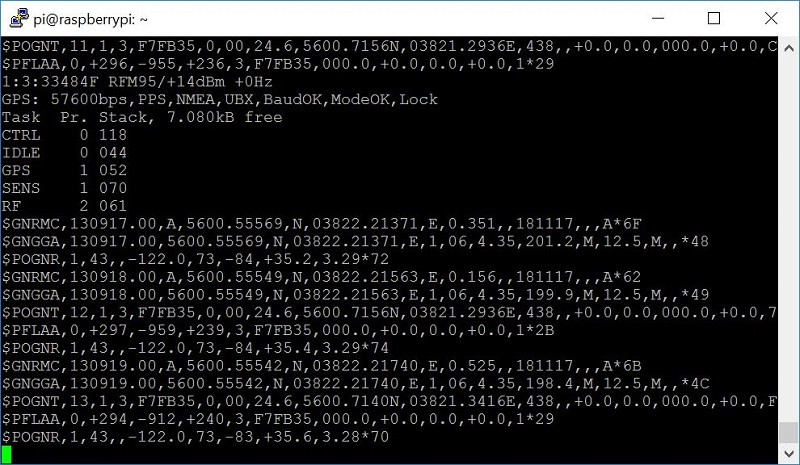
documents/images/Validation_OGN_1.JPG
