lyusupov/SoftRF/documents/images/Validation_OGN_2.JPG

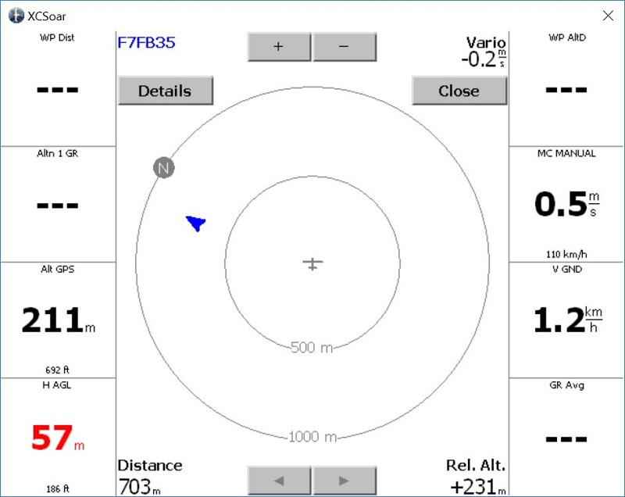
documents/images/Validation_OGN_2.JPG
