lyusupov/SoftRF/documents/images/Validation_OGN_3.jpg

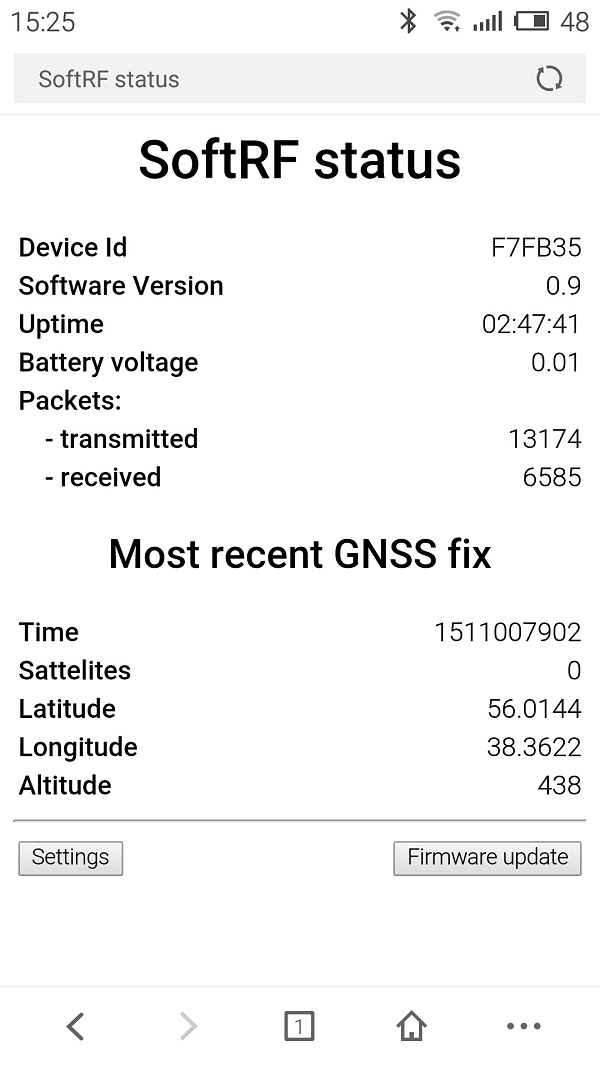
documents/images/Validation_OGN_3.jpg
