lyusupov/SoftRF/documents/images/Validation_OGN_4.jpg

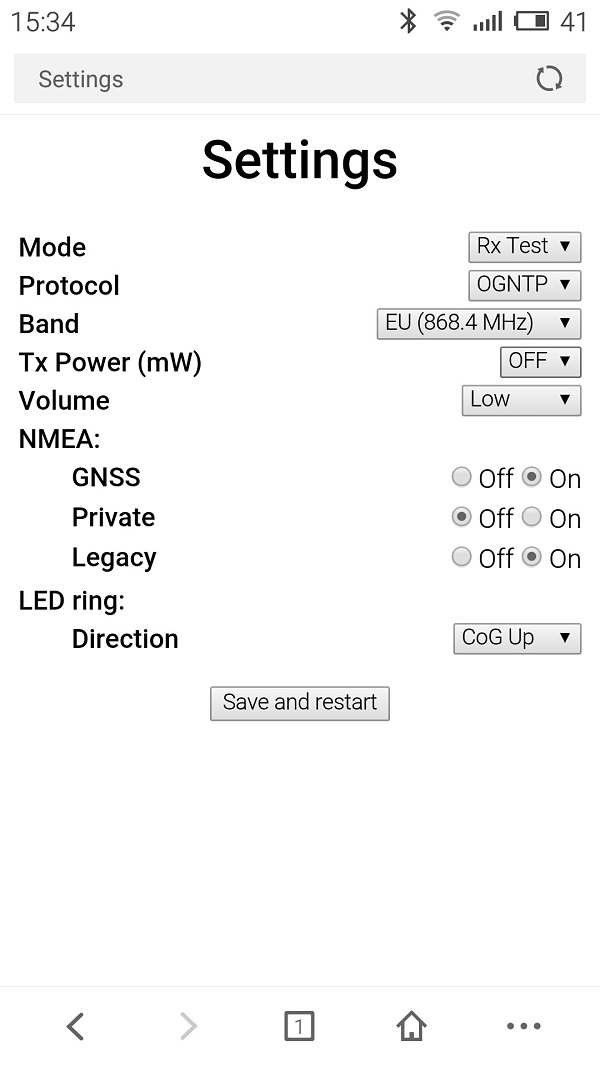
documents/images/Validation_OGN_4.jpg
