lyusupov/SoftRF/documents/images/Validation_OGN_5.jpg

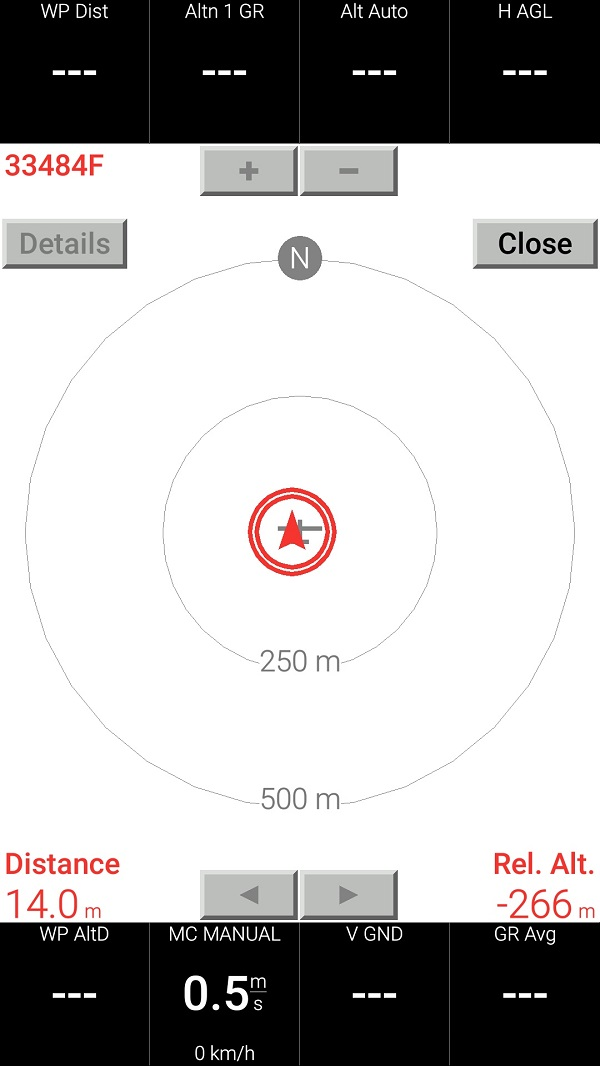
documents/images/Validation_OGN_5.jpg
