lyusupov/SoftRF/documents/images/Validation_PAW_1.JPG

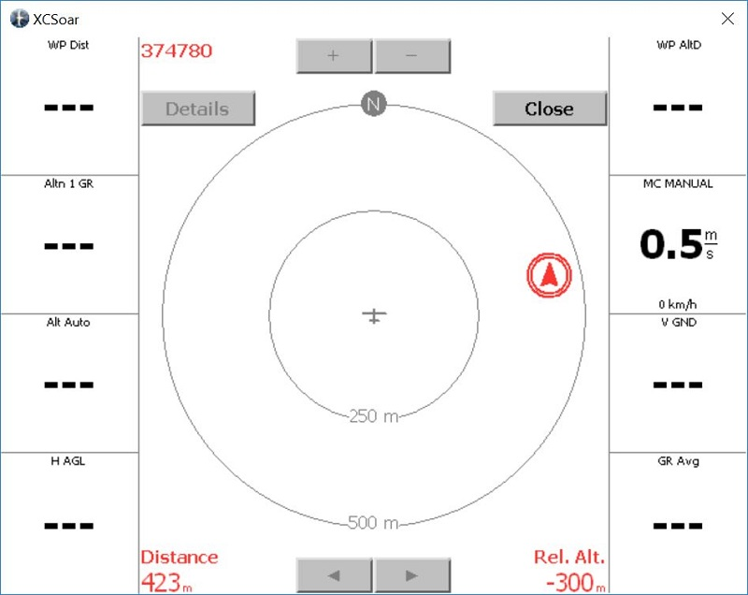
documents/images/Validation_PAW_1.JPG
