lyusupov/SoftRF/documents/images/Validation_PAW_OGN_log.JPG

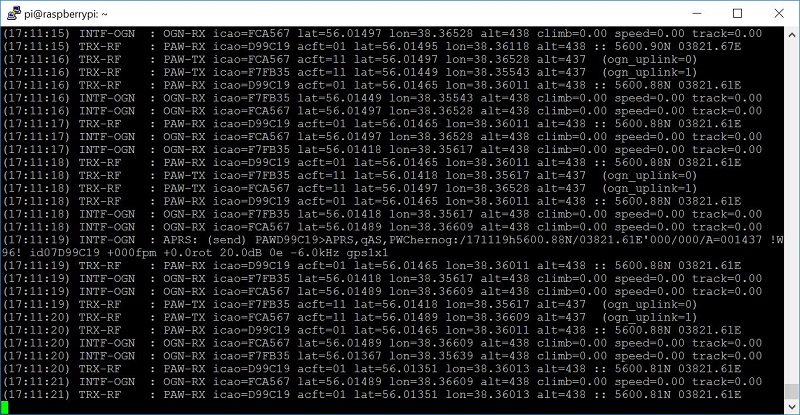
documents/images/Validation_PAW_OGN_log.JPG
