lyusupov/SoftRF/documents/images/Validation_PAW_OGN_status.JPG

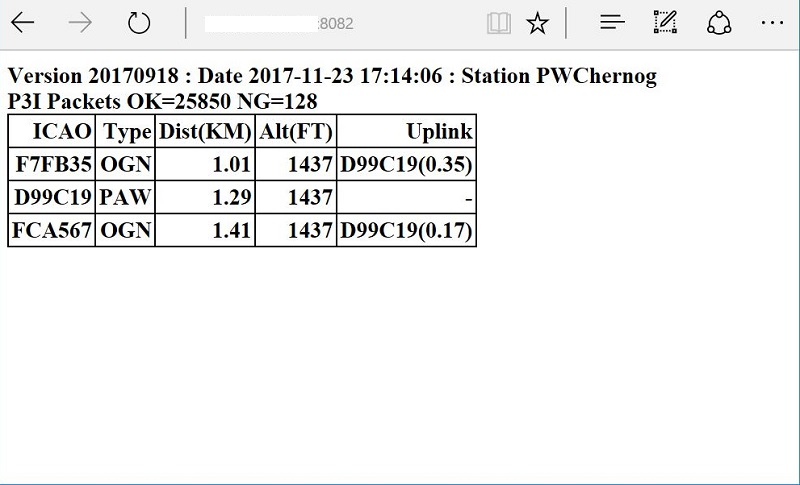
documents/images/Validation_PAW_OGN_status.JPG
