lyusupov/SoftRF/documents/images/Validation_PAW_SKYDEMON.jpg

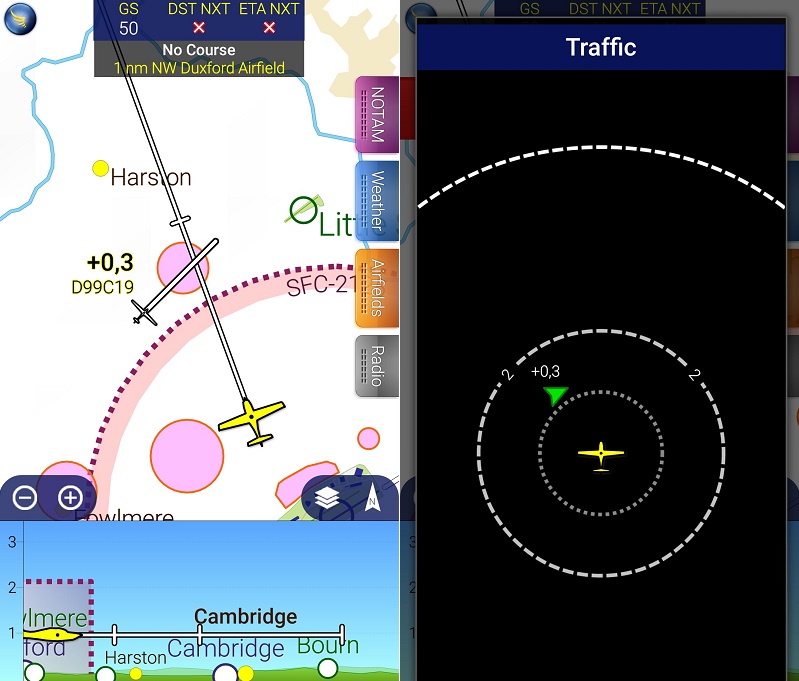
documents/images/Validation_PAW_SKYDEMON.jpg
