lyusupov/SoftRF/documents/images/rfm95w-nrf905-1_1-errata.jpg

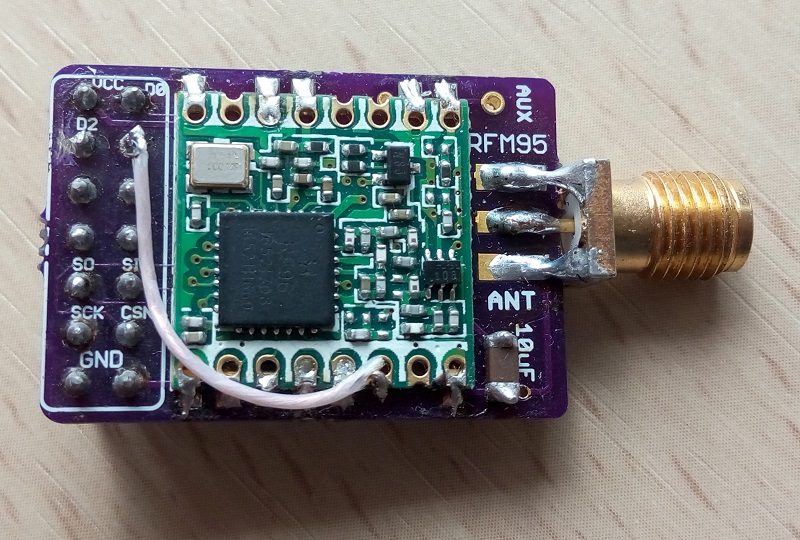
documents/images/rfm95w-nrf905-1_1-errata.jpg
