lyusupov/SoftRF/documents/images/skyview-6-no-fix-t5s.jpg

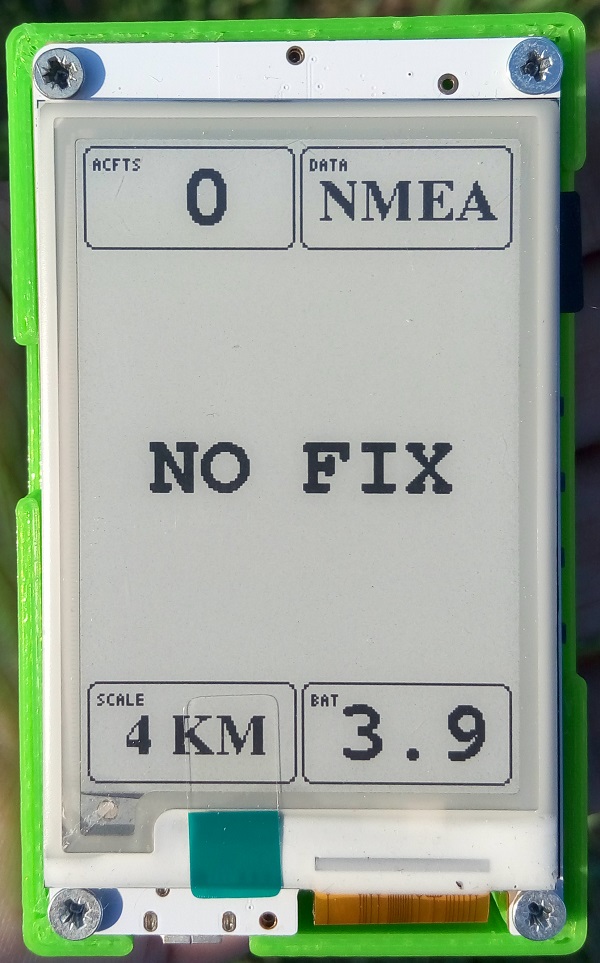
documents/images/skyview-6-no-fix-t5s.jpg
