lyusupov/SoftRF/documents/images/skyview-6-no-fix.jpg

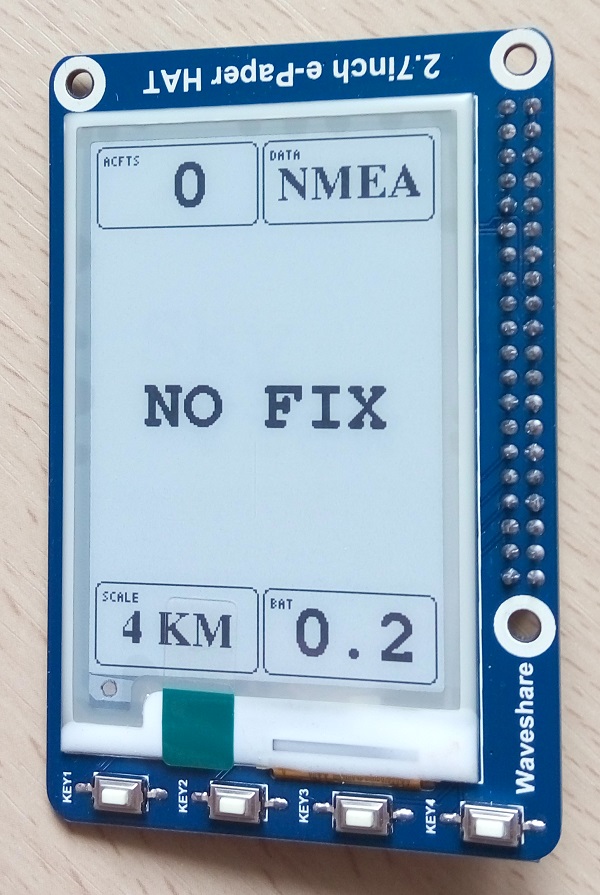
documents/images/skyview-6-no-fix.jpg
