lyusupov/SoftRF/software/firmware/source/SoftRF/src/platform/ESP32.h

/*
 * Platform_ESP32.h
 * Copyright (C) 2018-2026 Linar Yusupov
 *
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
 * You should have received a copy of the GNU General Public License
 * along with this program.  If not, see <http://www.gnu.org/licenses/>.
 */
#if defined(ESP32)

#ifndef PLATFORM_ESP32_H
#define PLATFORM_ESP32_H

#include "sdkconfig.h"

#define USE_WIFI_NINA           false
#define USE_WIFI_CUSTOM         true
#include <WiFi.h>

#include <ESPmDNS.h>
#include <Update.h>
#include <WiFiClient.h>

/* Maximum of tracked flying objects is now SoC-specific constant */
#define MAX_TRACKING_OBJECTS    8

#define DEFAULT_SOFTRF_MODEL    SOFTRF_MODEL_STANDALONE

#define SerialOutput            Serial
#define SoftwareSerial          HardwareSerial
#define Serial_GNSS_In          Serial1
#define Serial_GNSS_Out         Serial_GNSS_In

#if defined(CONFIG_IDF_TARGET_ESP32)
#define UATSerial               Serial2
#elif defined(CONFIG_IDF_TARGET_ESP32S2)
#if ARDUINO_USB_CDC_ON_BOOT
#define UATSerial               Serial0
#undef  SerialOutput
#define SerialOutput            Serial0
#else
#define UATSerial               Serial
#endif /* ARDUINO_USB_CDC_ON_BOOT */
#elif defined(CONFIG_IDF_TARGET_ESP32S3) || defined(CONFIG_IDF_TARGET_ESP32S31)
#define UATSerial               Serial2
#define SA8X8_Serial            Serial2
#if ARDUINO_USB_CDC_ON_BOOT
#undef  SerialOutput
#define SerialOutput            Serial0
#endif /* ARDUINO_USB_CDC_ON_BOOT */
#elif defined(CONFIG_IDF_TARGET_ESP32C2)  || \
      defined(CONFIG_IDF_TARGET_ESP32C3)  || \
      defined(CONFIG_IDF_TARGET_ESP32C5)  || \
      defined(CONFIG_IDF_TARGET_ESP32C6)  || \
      defined(CONFIG_IDF_TARGET_ESP32C61) || \
      defined(CONFIG_IDF_TARGET_ESP32H2)  || \
      defined(CONFIG_IDF_TARGET_ESP32H4)  || \
      defined(CONFIG_IDF_TARGET_ESP32P4)
#if ARDUINO_USB_CDC_ON_BOOT
#define UATSerial               Serial0
#undef  SerialOutput
#define SerialOutput            Serial0
#else
#define UATSerial               Serial
#endif /* ARDUINO_USB_CDC_ON_BOOT */
#else
#error "This ESP32 family build variant is not supported!"
#endif /* CONFIG_IDF_TARGET_ESP32 */

#define EEPROM_commit()         EEPROM.commit()

#define isValidFix()            isValidGNSSFix()

#if defined(ESP_IDF_VERSION_MAJOR) && ESP_IDF_VERSION_MAJOR>=4
#define WIRE_FINI(bus)          { bus.end(); }
#else
#define WIRE_FINI(bus)          { } /* AC 1.0.x has no Wire.end() */
#endif

#define LED_STATE_ON            HIGH  // State when LED is litted

/* Adafruit_NeoPixel still has "flickering" issue of ESP32 caused by 1 ms scheduler */
//#define USE_ADAFRUIT_NEO_LIBRARY

/*
 * NeoPixelBus is already "flickering-free" on ESP32 (with I2S or RMT)
 * but the "Core" needs update onto the most recent one
 */
#if defined(CONFIG_IDF_TARGET_ESP32C2) || defined(CONFIG_IDF_TARGET_ESP32S2)
#define EXCLUDE_LED_RING
#elif !defined(CONFIG_IDF_TARGET_ESP32C3)  && \
      !defined(CONFIG_IDF_TARGET_ESP32C5)  && \
      !defined(CONFIG_IDF_TARGET_ESP32S3)  && \
      !defined(CONFIG_IDF_TARGET_ESP32S31) && \
      !defined(CONFIG_IDF_TARGET_ESP32C6)  && \
      !defined(CONFIG_IDF_TARGET_ESP32C61) && \
      !defined(CONFIG_IDF_TARGET_ESP32H2)  && \
      !defined(CONFIG_IDF_TARGET_ESP32H4)  && \
      !defined(CONFIG_IDF_TARGET_ESP32P4)
#define USE_NEOPIXELBUS_LIBRARY
#else
#define USE_ADAFRUIT_NEO_LIBRARY
#endif /* CONFIG_IDF_TARGET_ESP32C6 */

#if !defined(EXCLUDE_LED_RING)
#if defined(USE_NEOPIXELBUS_LIBRARY)
#include <NeoPixelBus.h>

#define uni_begin()             strip.Begin()
#define uni_show()              strip.Show()
#define uni_setPixelColor(i, c) strip.SetPixelColor(i, c)
#define uni_numPixels()         strip.PixelCount()
#define uni_Color(r,g,b)        RgbColor(r,g,b)
#define color_t                 RgbColor

extern NeoPixelBus<NeoGrbFeature, Neo800KbpsMethod> strip;
#endif /* USE_NEOPIXELBUS_LIBRARY */

#if defined(USE_ADAFRUIT_NEO_LIBRARY)
#include <Adafruit_NeoPixel.h>

#define color_t                 uint32_t
extern Adafruit_NeoPixel *strip;

static inline void uni_begin(void) { if (strip) strip->begin(); }
static inline void uni_show(void)  { if (strip) strip->show();  }
static inline void uni_setPixelColor(uint16_t i, color_t c) {
  if (strip) strip->setPixelColor(i, c);
}
static inline uint16_t uni_numPixels() {
  if (strip) return strip->numPixels(); else return 0;
}
static inline color_t uni_Color(uint8_t r, uint8_t g, uint8_t b) {
  return Adafruit_NeoPixel::Color(r,g,b);
}
#endif /* USE_ADAFRUIT_NEO_LIBRARY */
#endif /* EXCLUDE_LED_RING */

#define LEDC_CHANNEL_BUZZER     0
#define BACKLIGHT_CHANNEL       ((uint8_t)1)
#define LEDC_RESOLUTION_BUZZER  8

/* Peripherals */
#define SOC_GPIO_PIN_GNSS_RX    23
#define SOC_GPIO_PIN_GNSS_TX    12
#define SOC_GPIO_PIN_BATTERY    36

#if defined(CONFIG_IDF_TARGET_ESP32)
#define SOC_GPIO_PIN_LED        25
#elif defined(CONFIG_IDF_TARGET_ESP32S2)
#define SOC_GPIO_PIN_LED        7
#elif defined(CONFIG_IDF_TARGET_ESP32S3) || defined(CONFIG_IDF_TARGET_ESP32S31)
#define SOC_GPIO_PIN_LED        2 /* 48 ? */
#elif defined(CONFIG_IDF_TARGET_ESP32C2)
#define SOC_GPIO_PIN_LED        SOC_UNUSED_PIN /* TBD */
#elif defined(CONFIG_IDF_TARGET_ESP32C3)
#define SOC_GPIO_PIN_LED        19 /* D1 */
#undef  LED_STATE_ON
#define LED_STATE_ON            LOW
#elif defined(CONFIG_IDF_TARGET_ESP32C5)
#define SOC_GPIO_PIN_LED        SOC_UNUSED_PIN /* TBD */
#elif defined(CONFIG_IDF_TARGET_ESP32C6)
#define SOC_GPIO_PIN_LED        3 /* D1 */
#elif defined(CONFIG_IDF_TARGET_ESP32C61)
#define SOC_GPIO_PIN_LED        SOC_UNUSED_PIN /* TBD */
#elif defined(CONFIG_IDF_TARGET_ESP32H2)
#define SOC_GPIO_PIN_LED        SOC_UNUSED_PIN /* TBD */
#elif defined(CONFIG_IDF_TARGET_ESP32H4)
#define SOC_GPIO_PIN_LED        SOC_UNUSED_PIN /* TBD */
#elif defined(CONFIG_IDF_TARGET_ESP32P4)
#define SOC_GPIO_PIN_LED        1
#else
#error "This ESP32 family build variant is not supported!"
#endif

#define SOC_GPIO_PIN_STATUS   (hw_info.model == SOFTRF_MODEL_MIDI      ?\
                                SOC_GPIO_PIN_HELTRK_LED :               \
                               hw_info.model == SOFTRF_MODEL_ECO       ?\
                                SOC_GPIO_PIN_T3C6_LED :                 \
                               hw_info.model == SOFTRF_MODEL_INK       ?\
                                SOC_GPIO_PIN_T3S3_LED :                 \
                               hw_info.model == SOFTRF_MODEL_STANDALONE && \
                               hw_info.revision == STD_EDN_REV_BPICOW  ?\
                                SOC_GPIO_PIN_BPIPW_STATUS :             \
                               hw_info.model == SOFTRF_MODEL_GIZMO     ?\
                                SOC_GPIO_PIN_M2_LED :                   \
                               hw_info.model == SOFTRF_MODEL_PRIME_MK4 ?\
                                SOC_GPIO_PIN_1W_LED :                   \
                               hw_info.model == SOFTRF_MODEL_NANO    && \
                               hw_info.revision == 1                   ?\
                                SOC_GPIO_PIN_ELRS_LED :                 \
                               hw_info.model != SOFTRF_MODEL_PRIME_MK2 ?\
                                SOC_UNUSED_PIN :                        \
                                (hw_info.revision == 2 ?                \
                                  SOC_GPIO_PIN_TBEAM_LED_V02 :          \
                                  (hw_info.revision == 5 ?              \
                                    SOC_GPIO_PIN_TBEAM_LED_V05 :        \
                                    (hw_info.revision == 11 ?           \
                                      SOC_GPIO_PIN_TBEAM_LED_V11 :      \
                                      SOC_UNUSED_PIN))))

#define SOC_GPIO_PIN_GNSS_PPS (hw_info.model == SOFTRF_MODEL_PRIME_MK3 ?  \
                                SOC_GPIO_PIN_S3_GNSS_PPS :                \
                                (hw_info.model == SOFTRF_MODEL_PRIME_MK2 ?\
                                  (hw_info.revision >= 8 ?                \
                                    SOC_GPIO_PIN_TBEAM_V08_PPS :          \
                                    SOC_UNUSED_PIN) :                     \
                                (hw_info.model == SOFTRF_MODEL_PRIME_MK4 ?\
                                  SOC_GPIO_PIN_1W_GNSS_PPS :              \
                                (hw_info.model == SOFTRF_MODEL_MIDI ?     \
                                  SOC_GPIO_PIN_HELTRK_GNSS_PPS :          \
                                (hw_info.model == SOFTRF_MODEL_ECO ?      \
                                  SOC_GPIO_PIN_T3C6_GNSS_PPS :            \
                                (hw_info.model == SOFTRF_MODEL_INK ?      \
                                  SOC_GPIO_PIN_T3S3_GNSS_PPS :            \
                                (hw_info.model == SOFTRF_MODEL_GIZMO ?    \
                                  SOC_GPIO_PIN_M2_GNSS_PPS :              \
                                (hw_info.model == SOFTRF_MODEL_STANDALONE && \
                                 hw_info.revision == STD_EDN_REV_WT99P4C5 ?\
                                  SOC_GPIO_PIN_P4_GNSS_PPS :              \
                                  SOC_UNUSED_PIN))))))))

#define SOC_GPIO_PIN_BUZZER   (hw_info.model == SOFTRF_MODEL_PRIME_MK2 ? \
                                SOC_UNUSED_PIN :                         \
                                (esp32_board == ESP32_DEVKIT    ? 13 :   \
                                (esp32_board == ESP32_C3_DEVKIT ?        \
                                SOC_GPIO_PIN_C3_BUZZER :                 \
                                (esp32_board == ESP32_C6_DEVKIT ?        \
                                SOC_GPIO_PIN_C6_BUZZER :                 \
                                (esp32_board == ESP32_BANANA_PICOW ?     \
                                SOC_GPIO_PIN_BPIPW_BUZZER :              \
                                (esp32_board == ESP32_ELECROW_TN_M2 ?    \
                                SOC_GPIO_PIN_M2_BUZZER :                 \
                                (esp32_board == ESP32_ELECROW_TN_M5 ?    \
                                SOC_GPIO_PIN_M5_BUZZER :                 \
                                (esp32_board == ESP32_P4_WT_DEVKIT ?     \
                                SOC_GPIO_PIN_P4_BUZZER : SOC_UNUSED_PIN))))))))

/* SPI (does match Heltec & TTGO LoRa32 pins mapping) */
#define SOC_GPIO_PIN_MOSI       27
#define SOC_GPIO_PIN_MISO       19
#define SOC_GPIO_PIN_SCK        5
#define SOC_GPIO_PIN_SS         18

/* NRF905 */
#define SOC_GPIO_PIN_TXE        26
#define SOC_GPIO_PIN_CE         2
#define SOC_GPIO_PIN_PWR        14

/* SX1276 [RFM95W] (does match Heltec & TTGO LoRa32 pins mapping) */
#define SOC_GPIO_PIN_RST        14
#define SOC_GPIO_PIN_DIO0       26
#define SOC_GPIO_PIN_SDA        14
#define SOC_GPIO_PIN_SCL        2

#include "iomap/LilyGO_T22.h"
#include "iomap/LilyGO_T3.h"

// Hardware pin definitions for Heltec and TTGO-V1 LoRa-32 Boards with OLED SSD1306 I2C Display
#define HELTEC_OLED_PIN_RST             U8X8_PIN_NONE // 16
#define HELTEC_OLED_PIN_SDA             4
#define HELTEC_OLED_PIN_SCL             15

#include "iomap/LilyGO_TWatch.h"
#include "iomap/LilyGO_T8S2.h"

#define SOC_GPIO_PIN_TDISPLAY_S2_LED    39
#define SOC_GPIO_PIN_TDONGLE_S2_LED     39

#if defined(CONFIG_IDF_TARGET_ESP32S2)
#define LV_HOR_RES                      (135) //Horizontal
#elif defined(CONFIG_IDF_TARGET_ESP32S3) || defined(CONFIG_IDF_TARGET_ESP32S31)
#define LV_HOR_RES                      (80) //Horizontal
#else
#define LV_HOR_RES                      (240) //Horizontal
#endif

#if defined(CONFIG_IDF_TARGET_ESP32S3) || defined(CONFIG_IDF_TARGET_ESP32S31)
#define LV_VER_RES                      (160) //vertical
#else
#define LV_VER_RES                      (240) //vertical
#endif

#include "iomap/LilyGO_TBeam_Supreme.h"

/* ESP32-S3 section 3 (spare pins) */
// 3(S), 21, 39, 45(S), 46(S), 48

// battery voltage (ADC)
#define SOC_GPIO_PIN_S3_BATTERY         3 // (S)

/* auxillary */
// Devkit LEDs, active state - HIGH
#define SOC_GPIO_PIN_S3_LED_RED         5
#define SOC_GPIO_PIN_S3_LED_GREEN       6
#define SOC_GPIO_PIN_S3_LED_BLUE        7
#define SOC_GPIO_PIN_S3_LED_WHITE       38
#define SOC_GPIO_PIN_S3_LED_YELLOW      39

#include "iomap/AiThinker_C3_12F.h"
#include "iomap/LilyGO_TTWR.h"
#include "iomap/Heltec_Tracker.h"
#include "iomap/WT0132C6.h"
#include "iomap/LilyGO_T3C6.h"
#include "iomap/LilyGO_T3S3.h"
#include "iomap/Banana_PicoW.h"
#include "iomap/Elecrow_ThinkNode_M2.h"
#include "iomap/Elecrow_ThinkNode_M5.h"
#if defined(CONFIG_IDF_TARGET_ESP32)
#include "iomap/LilyGO_ELRS.h"
#else
#include "iomap/Generic_ELRS_C3.h"
#endif /* CONFIG_IDF_TARGET_ESP32 */
#include "iomap/Ebyte_EoRa_HUB_900TB.h"
#include "iomap/WT99P4C5.h"
#include "iomap/LilyGO_TDisplay_P4.h"
#include "iomap/LilyGO_TBeam_1W.h"

enum rst_reason {
  REASON_DEFAULT_RST      = 0,  /* normal startup by power on */
  REASON_WDT_RST          = 1,  /* hardware watch dog reset */
  REASON_EXCEPTION_RST    = 2,  /* exception reset, GPIO status won't change */
  REASON_SOFT_WDT_RST     = 3,  /* software watch dog reset, GPIO status won't change */
  REASON_SOFT_RESTART     = 4,  /* software restart ,system_restart , GPIO status won't change */
  REASON_DEEP_SLEEP_AWAKE = 5,  /* wake up from deep-sleep */
  REASON_EXT_SYS_RST      = 6   /* external system reset */
};

enum esp32_board_id {
  ESP32_DEVKIT,
  ESP32_S3_DEVKIT,
  ESP32_S31_DEVKIT,
  ESP32_C2_DEVKIT,
  ESP32_C3_DEVKIT,
  ESP32_C5_DEVKIT,
  ESP32_C6_DEVKIT,
  ESP32_C61_DEVKIT,
  ESP32_H2_DEVKIT,
  ESP32_H4_DEVKIT,
  ESP32_P4_WT_DEVKIT, /* Wireless Tag */
  ESP32_P4_WS_DEVKIT, /* Waveshare or Espressif */
  ESP32_TTGO_V2_OLED,
  ESP32_HELTEC_OLED,
  ESP32_TTGO_T_BEAM,
  ESP32_TTGO_T_BEAM_SUPREME,
  ESP32_TTGO_T_BEAM_1W,
  ESP32_TTGO_T_WATCH,
  ESP32_S2_T8_V1_1,
  ESP32_LILYGO_T_TWR2,
  ESP32_HELTEC_TRACKER,
  ESP32_LILYGO_T3C6,
  ESP32_LILYGO_T3S3_EPD,
  ESP32_LILYGO_T3S3_OLED,
  ESP32_LILYGO_TDISPLAY_P4,
  ESP32_BANANA_PICOW,
  ESP32_ELECROW_TN_M2,
  ESP32_ELECROW_TN_M5,
  ESP32_RADIOMASTER_XR1,
  ESP32_LILYGO_T_ELRS,
  ESP32_EBYTE_HUB_900TB,
};

enum ep_model_id {
	EP_UNKNOWN,
	EP_GDEW027W3,
	EP_GDEY027T91,
	EP_DEPG0213BN,
	EP_GDEH0154D67,
};

/* https://github.com/espressif/usb-pids/blob/main/allocated-pids.txt#L313 */
enum softrf_usb_pid {
  SOFTRF_USB_PID_WEBTOP     = 0x8131,
  SOFTRF_USB_PID_STANDALONE = 0x8132,
  SOFTRF_USB_PID_PRIME_MK3  = 0x8133,
  SOFTRF_USB_PID_UF2_BOOT   = 0x8134,
  SOFTRF_USB_PID_HAM        = 0x818F,
  SOFTRF_USB_PID_MIDI       = 0x81A0,
  SOFTRF_USB_PID_INK        = 0x820A,
  SOFTRF_USB_PID_BANANA     = 0x812B,
  SOFTRF_USB_PID_GIZMO      = 0x82D9,
  SOFTRF_USB_PID_AIRVENTURE = 0x82F9,
  SOFTRF_USB_PID_CONCORDE   = 0x8343,
  SOFTRF_USB_PID_PRIME_MK4  = 0x8366,
};

struct rst_info {
  uint32_t reason;
  uint32_t exccause;
  uint32_t epc1;
  uint32_t epc2;
  uint32_t epc3;
  uint32_t excvaddr;
  uint32_t depc;
};

/* Boya Microelectronics Inc. */
#define BOYA_ID                 0x68
#define BOYA_BY25Q32AL          0x4016

/* ST / SGS/Thomson / Numonyx / XMC(later acquired by Micron) */
#define ST_ID                   0x20
#define XMC_XM25QH32B           0x4016
#define XMC_XM25QH64B           0x4017

/* Zbit Semiconductor, Inc. */
#define ZBIT_ID                 0x5E
#define ZBIT_ZB25VQ32B          0x4016
#define ZBIT_ZB25VQ128A         0x4018

/* Shanghai Fudan Microelectronics Group Co., Ltd. */
#define FMICRO_ID               0xA1
#define FMICRO_FM25Q16          0x4015

#define TBD_ID                  0x46
#define TBD_25Q32               0x4016
#define TBD_25Q128              0x4018

#define MakeFlashId(v,d)        ((v << 16) | d)

#define MPU6886_REG_PWR_MGMT_1  (0x6B)
#define MPU6886_REG_WHOAMI      (0x75)
#define MPU9250_ADDRESS         (0x68)
#define MPU9250_REG_PWR_MGMT_1  (0x6B)
#define MPU9250_REG_WHOAMI      (0x75)

#define PCA9557_ADDRESS         (0x18)

#define XL9535_ADDRESS          (0x20) /* A0 = A1 = A2 = LOW */
#define ICM20948_ADDRESS        (0x68)
#define AW86224_ADDRESS         (0x58)
#define SGM38121_ADDRESS        (0x28)
#define HI8561_ADDRESS          (0x68)
#define GT9895_ADDRESS          (0x5D)
#define OV2710_ADDRESS          (0x36)
#define OV5647_ADDRESS          (0x36)

/* Disable brownout detection (avoid unexpected reset on some boards) */
#define ESP32_DISABLE_BROWNOUT_DETECTOR 0

#define NMEA_TCP_SERVICE
#define USE_NMEALIB
#define USE_OLED
#define EXCLUDE_OLED_049
//#define EXCLUDE_OLED_BARO_PAGE
#define USE_TFT
#define USE_NMEA_CFG
#define USE_BASICMAC
#if defined(CONFIG_IDF_TARGET_ESP32S3) || defined(CONFIG_IDF_TARGET_ESP32S31)

#define USE_SKYVIEW_CFG
#define EXCLUDE_SX1276
#define USE_RADIOLIB
//#define EXCLUDE_LR11XX
//#define EXCLUDE_LR20XX
#define EXCLUDE_CC1101
#define EXCLUDE_SI443X
#define EXCLUDE_SI446X
#define EXCLUDE_SX1231
#define EXCLUDE_SX1280
#define USE_FEM

#elif defined(CONFIG_IDF_TARGET_ESP32C3) || \
      defined(CONFIG_IDF_TARGET_ESP32C5) || \
      defined(CONFIG_IDF_TARGET_ESP32C6) || \
      defined(CONFIG_IDF_TARGET_ESP32C61)
#if ARDUINO_USB_CDC_ON_BOOT
//#define USE_RADIOLIB
#else
#define USE_RADIOLIB
//#define USE_RADIOHEAD
#endif /* ARDUINO_USB_CDC_ON_BOOT */
//#define EXCLUDE_LR11XX
#if defined(USE_RADIOLIB)
#include <BuildOpt.h>
#if RADIOLIB_VERSION_MAJOR <= 7 && RADIOLIB_VERSION_MINOR < 6
#define EXCLUDE_LR20XX
#endif /* RADIOLIB_VERSION */
#endif /* USE_RADIOLIB */
#define EXCLUDE_CC1101
#define EXCLUDE_SI443X
#define EXCLUDE_SI446X
#define EXCLUDE_SX1231
#define EXCLUDE_SX1280

#elif defined(CONFIG_IDF_TARGET_ESP32P4)

#define USE_SKYVIEW_CFG
#define USE_RADIOLIB
//#define EXCLUDE_LR11XX
#if defined(USE_RADIOLIB)
#include <BuildOpt.h>
#if RADIOLIB_VERSION_MAJOR <= 7 && RADIOLIB_VERSION_MINOR < 6
#define EXCLUDE_LR20XX
#endif /* RADIOLIB_VERSION */
#endif /* USE_RADIOLIB */
#define EXCLUDE_CC1101
#define EXCLUDE_SI443X
#define EXCLUDE_SI446X
#define EXCLUDE_SX1231
#define EXCLUDE_SX1280

#endif /* S3 C3 C6 P4 */

#define USE_TIME_SLOTS

/* Experimental */
#define USE_BLE_MIDI
//#define USE_GDL90_MSL
#define USE_OGN_ENCRYPTION
#define ENABLE_PROL
#define ENABLE_ADSL

//#define EXCLUDE_GNSS_UBLOX    /* Neo-6/7/8, M10 */
#define ENABLE_UBLOX_RFS        /* revert factory settings (when necessary)  */
#define EXCLUDE_GNSS_GOKE       /* 'Air530' GK9501 GPS/GLO/BDS (GAL inop.)   */
//#define EXCLUDE_GNSS_AT65     /* L76K, Air530Z */
#define EXCLUDE_GNSS_SONY
#define EXCLUDE_GNSS_MTK
//#define EXCLUDE_GNSS_UC65
#define EXCLUDE_GNSS_AG33

#define EXCLUDE_CC13XX
#define EXCLUDE_SOFTRF_HEARTBEAT
#define EXCLUDE_LK8EX1
//#define EXCLUDE_IMU
//#define EXCLUDE_MAG
#define EXCLUDE_BME680
#define EXCLUDE_BME280AUX
#define EXCLUDE_SPA06

#define EXCLUDE_ETHERNET

#if defined(CONFIG_IDF_TARGET_ESP32)
//#define ENABLE_BT_VOICE
//#define USE_NIMBLE

#define USE_RADIOLIB
#define EXCLUDE_LR11XX
#if defined(USE_RADIOLIB)
#include <BuildOpt.h>
#if RADIOLIB_VERSION_MAJOR <= 7 && RADIOLIB_VERSION_MINOR < 6
#define EXCLUDE_LR20XX
#endif /* RADIOLIB_VERSION */
#endif /* USE_RADIOLIB */
#define EXCLUDE_CC1101
#define EXCLUDE_SI443X
#define EXCLUDE_SI446X
#define EXCLUDE_SX1231
#define EXCLUDE_SX1280

#else

#define EXCLUDE_UATM

#if defined(CONFIG_IDF_TARGET_ESP32S2) || \
    defined(CONFIG_IDF_TARGET_ESP32S3) || \
    defined(CONFIG_IDF_TARGET_ESP32S31)
#define EXCLUDE_NRF905

/* Experimental */
//#define USE_ADAFRUIT_MSC
//#define USE_USB_HOST

#if defined(USE_USB_HOST)
#undef  SOC_GPIO_PIN_T8_S2_CONS_RX
#undef  SOC_GPIO_PIN_T8_S2_CONS_TX
#define SOC_GPIO_PIN_T8_S2_CONS_RX      46 // 43
#define SOC_GPIO_PIN_T8_S2_CONS_TX      45 // 44

/* Experimental */
#define ENABLE_D1090_INPUT

#include <cdc_acm_host.h>

typedef struct {
    bool         connected;
    int          index;
    CdcAcmDevice *device;
} ESP32_USBSerial_device_t;

typedef struct {
    uint16_t   vid;
    uint16_t   pid;
    uint8_t    type;
    uint8_t    model;
    const char *first_name;
    const char *last_name;
} USB_Device_List_t;

extern ESP32_USBSerial_device_t ESP32_USB_Serial;
extern const USB_Device_List_t supported_USB_devices[];

#endif /* USE_USB_HOST */
#elif defined(CONFIG_IDF_TARGET_ESP32C2)  || \
      defined(CONFIG_IDF_TARGET_ESP32C3)  || \
      defined(CONFIG_IDF_TARGET_ESP32C5)  || \
      defined(CONFIG_IDF_TARGET_ESP32C6)  || \
      defined(CONFIG_IDF_TARGET_ESP32C61) || \
      defined(CONFIG_IDF_TARGET_ESP32H2)  || \
      defined(CONFIG_IDF_TARGET_ESP32H4)  || \
      defined(CONFIG_IDF_TARGET_ESP32P4)
#undef USE_OLED
#undef USE_TFT
#if defined(CONFIG_IDF_TARGET_ESP32C2)  || \
    defined(CONFIG_IDF_TARGET_ESP32C5)  || \
    defined(CONFIG_IDF_TARGET_ESP32C6)  || \
    defined(CONFIG_IDF_TARGET_ESP32C61) || \
    defined(CONFIG_IDF_TARGET_ESP32H2)  || \
    defined(CONFIG_IDF_TARGET_ESP32H4)  || \
    defined(CONFIG_IDF_TARGET_ESP32P4)
#define EXCLUDE_EGM96
#define EXCLUDE_TEST_MODE
#define EXCLUDE_WATCHOUT_MODE
#undef USE_NMEALIB
#undef USE_BLE_MIDI
#undef ENABLE_PROL
#if defined(CONFIG_IDF_TARGET_ESP32C5)
//#define EXCLUDE_BLUETOOTH
#define USE_NIMBLE
#define USE_NIMBLE_V2
//#define USE_ARDUINOBLE
#undef EXCLUDE_SOFTRF_HEARTBEAT
#undef EXCLUDE_TEST_MODE
#define USE_NMEALIB
//#define USE_SOFTSPI
#define USE_OLED
#elif defined(CONFIG_IDF_TARGET_ESP32C6)
#define USE_NIMBLE
#define USE_NIMBLE_V2
#else
#define USE_ARDUINOBLE
#endif /* C6 */
#if defined(CONFIG_IDF_TARGET_ESP32P4)
#undef EXCLUDE_ETHERNET
#endif /* P4 */
#endif /* C2 || C6 || H2 || H4 || P4 */
#endif /* SX || CX || H2 || H4 || P4 */
#endif /* CONFIG_IDF_TARGET_ESP32 */

#if defined(CONFIG_IDF_TARGET_ESP32S3) || defined(CONFIG_IDF_TARGET_ESP32S31)
#define EXCLUDE_EGM96
//#undef USE_NMEALIB
#define USE_U10_EXT
#define ENABLE_RECORDER
#define USE_SA8X8
/* Experimental */
#if !defined(ESP_IDF_VERSION_MAJOR) || ESP_IDF_VERSION_MAJOR < 5
#define ENABLE_REMOTE_ID
#endif /* ESP_IDF_VERSION_MAJOR */
//#define EXCLUDE_VOICE_MESSAGE
//#define USE_ARDUINOBLE
#if !defined(ESP_IDF_VERSION_MAJOR) || ESP_IDF_VERSION_MAJOR < 5
#define USE_NIMBLE
//#define USE_NIMBLE_V2
#endif /* ESP_IDF_VERSION_MAJOR */
//#undef USE_BLE_MIDI
#define USE_EPAPER
#define EPD_ASPECT_RATIO_1C1
//#define EPD_ASPECT_RATIO_2C1
#define USE_EPD_TASK
#if defined(EPD_ASPECT_RATIO_2C1)
#define	EPD_POWEROFF		      {}
#endif /* EPD_ASPECT_RATIO_2C1 */
#endif /* S3 */

#if defined(CONFIG_IDF_TARGET_ESP32S2)
#define EXCLUDE_BLUETOOTH
#endif /* S2 */

#if defined(CONFIG_IDF_TARGET_ESP32H2) || defined(CONFIG_IDF_TARGET_ESP32H4)
#define EXCLUDE_WIFI
#undef NMEA_TCP_SERVICE
#endif /* H2 || H4 */

#if defined(CONFIG_IDF_TARGET_ESP32P4)
#define USE_U10_EXT
#define ENABLE_RECORDER
//#define EXCLUDE_BLUETOOTH
#undef USE_ARDUINOBLE
//#define EXCLUDE_WIFI
//#undef NMEA_TCP_SERVICE
//#define EXCLUDE_VOICE_MESSAGE
#define USE_OLED
//#define USE_USB_HOST
//#define USE_LIB_RTLSDR
//#define USE_DSI
#define USE_SENSORLIB_TOUCH
//#define USE_CAMERA
#endif /* P4 */

#define POWER_SAVING_WIFI_TIMEOUT 600000UL /* 10 minutes */

//#define PMK2_SLEEP_MODE 1    // 0.6 mA : esp_deep_sleep_start()
//#define PMK2_SLEEP_MODE 2    // 0.9 mA : axp.setSleep()
#define PMK2_SLEEP_MODE 3      //  60 uA : axp.shutdown()

#if defined(USE_OLED)
#define U8X8_OLED_I2C_BUS_TYPE  U8X8_SSD1306_128X64_NONAME_2ND_HW_I2C
#if defined(CONFIG_IDF_TARGET_ESP32S3) || defined(CONFIG_IDF_TARGET_ESP32S31)
#define ENABLE_OLED_TEXT_PAGE
#endif /* CONFIG_IDF_TARGET_ESP32S3-S31 */
#endif /* USE_OLED */

#if defined(USE_EPAPER)
typedef void EPD_Task_t;

extern const char *Hardware_Rev[];
#endif /* USE_EPAPER */

#if defined(USE_SOFTSPI)
#include <SoftSPI.h>
extern  SoftSPI RadioSPI;
#undef  SPI
#define SPI RadioSPI
#endif /* USE_SOFTSPI */

#if defined(CONFIG_IDF_TARGET_ESP32C3)
extern bool ESP32C3_radio_irq_func(int);
//#define plat_radio_irq_func ESP32C3_radio_irq_func
//#undef USE_BASICMAC
#endif /* C3 */

#if defined(CONFIG_IDF_TARGET_ESP32P4)
extern bool ESP32P4_radio_irq_func(int);
#define plat_radio_irq_func ESP32P4_radio_irq_func
//#undef USE_BASICMAC
#endif /* P4 */

#endif /* PLATFORM_ESP32_H */

#endif /* ESP32 */
