lyusupov/SoftRF/software/firmware/source/SoftRF/src/driver/radio/radiolib.cpp

/*
 * radiolib.cpp
 * Copyright (C) 2024-2026 Linar Yusupov
 *
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
 * You should have received a copy of the GNU General Public License
 * along with this program.  If not, see <http://www.gnu.org/licenses/>.
 */

#include "../RF.h"

#if defined(USE_RADIOLIB)

#include "../EEPROM.h"
#include "../Battery.h"

#include <manchester.h>

#if defined(RASPBERRY_PI) || defined(LUCKFOX_LYRA)
#include <hal/RPi/PiHal.h>
#endif // RASPBERRY_PI

#ifndef RadioSPI
#define RadioSPI        SPI
#endif

Module *mod;

const rf_proto_desc_t *rl_protocol = &ogntp_proto_desc;

#define RADIOLIB_MAX_DATA_LENGTH    128

typedef struct
{
  uint8_t len;
  uint8_t payload[RADIOLIB_MAX_DATA_LENGTH];
} RadioLib_DataPacket;

static RadioLib_DataPacket RL_txPacket;
static RadioLib_DataPacket RL_rxPacket;

extern size_t RF_tx_size;

#if !defined(USE_BASICMAC)
static const SPISettings probe_settings(1000000UL, MSBFIRST, SPI_MODE0);

static void hal_spi_select (int on) {

#if defined(SPI_HAS_TRANSACTION)
    if (on)
        RadioSPI.beginTransaction(probe_settings);
    else
        RadioSPI.endTransaction();
#endif

    //Serial.println(val?">>":"<<");
    digitalWrite(lmic_pins.nss, !on ? HIGH : LOW);
}

// Datasheet defins typical times until busy goes low. Most are < 200us,
// except when waking up from sleep, which typically takes 3500us. Since
// we cannot know here if we are in sleep, we'll have to assume we are.
// Since 3500 is typical, not maximum, wait a bit more than that.
static unsigned long MAX_BUSY_TIME = 5000;

static void hal_pin_busy_wait (void) {
    if (lmic_pins.busy == LMIC_UNUSED_PIN) {
        // TODO: We could probably keep some state so we know the chip
        // is in sleep, since otherwise the delay can be much shorter.
        // Also, all delays after commands (rather than waking up from
        // sleep) are measured from the *end* of the previous SPI
        // transaction, so we could wait shorter if we remember when
        // that was.
        delayMicroseconds(MAX_BUSY_TIME);
    } else {
        unsigned long start = micros();

        while((micros() - start) < MAX_BUSY_TIME && digitalRead(lmic_pins.busy)) /* wait */;
    }
}
#endif /* USE_BASICMAC */

static bool memeqzero(const uint8_t *data, size_t length)
{
	const uint8_t *p = data;
	size_t len;

	/* Check first 16 bytes manually */
	for (len = 0; len < 16; len++) {
		if (!length)
			return true;
		if (*p)
			return false;
		p++;
		length--;
	}

	/* Now we know that's zero, memcmp with self. */
	return memcmp((void *) data, (void *) p, length) == 0;
}

#if !defined(EXCLUDE_LR11XX)

static bool lr1110_probe(void);
static bool lr1121_probe(void);
static void lr11xx_setup(void);
static void lr11xx_channel(int8_t);
static bool lr11xx_receive(void);
static bool lr11xx_transmit(void);
static void lr11xx_shutdown(void);

const rfchip_ops_t lr1110_ops = {
  RF_IC_LR1110,
  "LR1110",
  lr1110_probe,
  lr11xx_setup,
  lr11xx_channel,
  lr11xx_receive,
  lr11xx_transmit,
  lr11xx_shutdown
};

const rfchip_ops_t lr1121_ops = {
  RF_IC_LR1121,
  "LR1121",
  lr1121_probe,
  lr11xx_setup,
  lr11xx_channel,
  lr11xx_receive,
  lr11xx_transmit,
  lr11xx_shutdown
};

#define USE_SX1262      0
#define USE_LR11XX      1

#if USE_SX1262
SX1262  *radio_semtech;
#elif USE_LR11XX
LR11x0  *radio_semtech;
#endif

static int8_t lr112x_channel_prev    = (int8_t) -1;

static volatile bool lr112x_receive_complete = false;

static bool lr112x_receive_active    = false;
static bool lr112x_transmit_complete = false;

#if USE_SX1262

#define CMD_READREGISTER            0x1D
#define REG_LORASYNCWORDLSB         0x0741
#define SX126X_DEF_LORASYNCWORDLSB  0x24

static void sx1262_ReadRegs (uint16_t addr, uint8_t* data, uint8_t len) {
    hal_spi_select(1);
    hal_pin_busy_wait();
    hal_spi(CMD_READREGISTER);
    hal_spi(addr >> 8);
    hal_spi(addr);
    hal_spi(0x00); // NOP
    for (uint8_t i = 0; i < len; i++) {
        data[i] = hal_spi(0x00);
    }
    hal_spi_select(0);
}

static uint8_t sx1262_ReadReg (uint16_t addr) {
    uint8_t val;
    sx1262_ReadRegs(addr, &val, 1);
    return val;
}
#endif /* USE_SX1262 */

#if USE_LR11XX
static void lr11xx_GetVersion (uint8_t* hw, uint8_t* device,
                               uint8_t* major, uint8_t* minor) {
    uint8_t buf[4] = { 0 };

    hal_pin_busy_wait();
    hal_spi_select(1);

    hal_spi((uint8_t)((RADIOLIB_LR11X0_CMD_GET_VERSION & 0xFF00) >> 8));
    hal_spi((uint8_t) (RADIOLIB_LR11X0_CMD_GET_VERSION & 0x00FF));
    hal_spi_select(0);

    hal_pin_busy_wait();
    hal_spi_select(1);

    hal_spi(RADIOLIB_LR11X0_CMD_NOP);
    for (uint8_t i = 0; i < sizeof(buf); i++) {
        buf[i] = hal_spi(0x00);
    }
    hal_spi_select(0);

    if (hw)     { *hw     = buf[0]; }
    if (device) { *device = buf[1]; }
    if (major)  { *major  = buf[2]; }
    if (minor)  { *minor  = buf[3]; }
#if 0
    Serial.print("hw     = "); Serial.println(*hw, HEX);
    Serial.print("device = "); Serial.println(*device, HEX);
    Serial.print("major  = "); Serial.println(*major, HEX);
    Serial.print("minor  = "); Serial.println(*minor, HEX);
#endif
}

static void lr11xx_GetChipEui (uint64_t* eui) {
    uint8_t buf[8] = { 0 };

    hal_pin_busy_wait();
    hal_spi_select(1);

    hal_spi((uint8_t)((RADIOLIB_LR11X0_CMD_GET_CHIP_EUI & 0xFF00) >> 8));
    hal_spi((uint8_t) (RADIOLIB_LR11X0_CMD_GET_CHIP_EUI & 0x00FF));
    hal_spi_select(0);

    hal_pin_busy_wait();
    hal_spi_select(1);

    hal_spi(RADIOLIB_LR11X0_CMD_NOP);
    for (uint8_t i = 0; i < sizeof(buf); i++) {
        buf[i] = hal_spi(0x00);
    }
    hal_spi_select(0);

    if (eui) { memcpy(eui, buf, sizeof(buf)); }
#if 0
    Serial.print("eui = "); Serial.println(*eui, HEX);
#endif
}

#if RADIOLIB_VERSION_MAJOR >= 7 && RADIOLIB_VERSION_MINOR > 1
static uint8_t lr11xx_roundRampTime(uint32_t rampTimeUs) {
  uint8_t regVal;

  // Round up the ramp time to nearest discrete register value
  if(rampTimeUs <= 2) {
    regVal = RADIOLIB_LRXXXX_PA_RAMP_2U;
  } else if(rampTimeUs <= 4) {
    regVal = RADIOLIB_LRXXXX_PA_RAMP_4U;
  } else if(rampTimeUs <= 8) {
    regVal = RADIOLIB_LRXXXX_PA_RAMP_8U;
  } else if(rampTimeUs <= 16) {
    regVal = RADIOLIB_LRXXXX_PA_RAMP_16U;
  } else if(rampTimeUs <= 32) {
    regVal = RADIOLIB_LRXXXX_PA_RAMP_32U;
  } else if(rampTimeUs <= 48) {
    regVal = RADIOLIB_LRXXXX_PA_RAMP_48U;
  } else if(rampTimeUs <= 64) {
    regVal = RADIOLIB_LRXXXX_PA_RAMP_64U;
  } else if(rampTimeUs <= 80) {
    regVal = RADIOLIB_LRXXXX_PA_RAMP_80U;
  } else if(rampTimeUs <= 96) {
    regVal = RADIOLIB_LRXXXX_PA_RAMP_96U;
  } else if(rampTimeUs <= 112) {
    regVal = RADIOLIB_LRXXXX_PA_RAMP_112U;
  } else if(rampTimeUs <= 128) {
    regVal = RADIOLIB_LRXXXX_PA_RAMP_128U;
  } else if(rampTimeUs <= 144) {
    regVal = RADIOLIB_LRXXXX_PA_RAMP_144U;
  } else if(rampTimeUs <= 160) {
    regVal = RADIOLIB_LRXXXX_PA_RAMP_160U;
  } else if(rampTimeUs <= 176) {
    regVal = RADIOLIB_LRXXXX_PA_RAMP_176U;
  } else if(rampTimeUs <= 192) {
    regVal = RADIOLIB_LRXXXX_PA_RAMP_192U;
  } else if(rampTimeUs <= 208) {
    regVal = RADIOLIB_LRXXXX_PA_RAMP_208U;
  } else if(rampTimeUs <= 240) {
    regVal = RADIOLIB_LRXXXX_PA_RAMP_240U;
  } else if(rampTimeUs <= 272) {
    regVal = RADIOLIB_LRXXXX_PA_RAMP_272U;
  } else {  // 304
    regVal = RADIOLIB_LRXXXX_PA_RAMP_304U;
  }

  return regVal;
}
#endif /* RADIOLIB_VERSION */

static uint64_t lr11xx_eui_be = 0xdeadbeefdeadbeef;

static const uint32_t rfswitch_dio_pins_hpdtek[] = {
    RADIOLIB_LR11X0_DIO5, RADIOLIB_LR11X0_DIO6,
    RADIOLIB_NC, RADIOLIB_NC, RADIOLIB_NC
};

static const Module::RfSwitchMode_t rfswitch_table_hpdtek[] = {
    // mode                  DIO5  DIO6
    { LR11x0::MODE_STBY,   { LOW,  LOW  } },
    { LR11x0::MODE_RX,     { HIGH, LOW  } },
    { LR11x0::MODE_TX,     { LOW,  HIGH } },
    { LR11x0::MODE_TX_HP,  { LOW,  HIGH } },
    { LR11x0::MODE_TX_HF,  { LOW,  LOW  } },
    { LR11x0::MODE_GNSS,   { LOW,  LOW  } },
    { LR11x0::MODE_WIFI,   { LOW,  LOW  } },
    END_OF_MODE_TABLE,
};

/* setDioAsRfSwitch(0x0f, 0x0, 0x09, 0x0B, 0x0A, 0x0, 0x4, 0x0) */
static const uint32_t rfswitch_dio_pins_seeed[] = {
    RADIOLIB_LR11X0_DIO5, RADIOLIB_LR11X0_DIO6,
    RADIOLIB_LR11X0_DIO7, RADIOLIB_LR11X0_DIO8,
    RADIOLIB_NC
};

static const Module::RfSwitchMode_t rfswitch_table_seeed[] = {
    // mode                  DIO5  DIO6  DIO7  DIO8
    { LR11x0::MODE_STBY,   { LOW,  LOW,  LOW,  LOW  } },
    // SKY13373
    { LR11x0::MODE_RX,     { HIGH, LOW,  LOW,  HIGH } },
    { LR11x0::MODE_TX,     { HIGH, HIGH, LOW,  HIGH } },
    { LR11x0::MODE_TX_HP,  { LOW,  HIGH, LOW,  HIGH } },
    { LR11x0::MODE_TX_HF,  { LOW,  LOW,  LOW,  LOW  } },
    // BGA524N6
    { LR11x0::MODE_GNSS,   { LOW,  LOW,  HIGH, LOW  } },
    // LC
    { LR11x0::MODE_WIFI,   { LOW,  LOW,  LOW,  LOW  } },
    END_OF_MODE_TABLE,
};

/* setDioAsRfSwitch(0x07, 0x0, 0x02, 0x03, 0x01, 0x0, 0x4, 0x0) */
static const uint32_t rfswitch_dio_pins_ebyte[] = {
    RADIOLIB_LR11X0_DIO5, RADIOLIB_LR11X0_DIO6, RADIOLIB_LR11X0_DIO7,
    RADIOLIB_NC, RADIOLIB_NC
};

static const Module::RfSwitchMode_t rfswitch_table_ebyte[] = {
    // mode                  DIO5  DIO6  DIO7
    { LR11x0::MODE_STBY,   { LOW,  LOW,  LOW  } },
    { LR11x0::MODE_RX,     { LOW,  HIGH, LOW  } },
    { LR11x0::MODE_TX,     { HIGH, HIGH, LOW  } },
    { LR11x0::MODE_TX_HP,  { HIGH, LOW,  LOW  } },
    { LR11x0::MODE_TX_HF,  { LOW,  LOW,  LOW  } },
    { LR11x0::MODE_GNSS,   { LOW,  LOW,  HIGH } },
    { LR11x0::MODE_WIFI,   { LOW,  LOW,  LOW  } },
    END_OF_MODE_TABLE,
};

/* setDioAsRfSwitch(0x0F, 0x0, 0x0C, 0x08, 0x08, 0x6, 0x0, 0x5) */
static const uint32_t rfswitch_dio_pins_radiomaster[] = {
    RADIOLIB_LR11X0_DIO5, RADIOLIB_LR11X0_DIO6,
    RADIOLIB_LR11X0_DIO7, RADIOLIB_LR11X0_DIO8,
    RADIOLIB_NC
};

static const Module::RfSwitchMode_t rfswitch_table_radiomaster[] = {
    // mode                  DIO5  DIO6  DIO7  DIO8
    { LR11x0::MODE_STBY,   { LOW,  LOW,  LOW,  LOW  } },
    // SKY13373 ( V1-DIO7 V2-DIO8 )
    { LR11x0::MODE_RX,     { LOW,  LOW,  HIGH, HIGH } },
    { LR11x0::MODE_TX,     { LOW,  LOW,  LOW,  HIGH } },
    { LR11x0::MODE_TX_HP,  { LOW,  LOW,  LOW,  HIGH } },
    // AT2401C ( RXEN-DIO5 TXEN-DIO6 )
    { LR11x0::MODE_TX_HF,  { LOW,  HIGH, HIGH, LOW  } },
    { LR11x0::MODE_GNSS,   { LOW,  LOW,  LOW,  LOW  } },
    { LR11x0::MODE_WIFI,   { HIGH, LOW,  HIGH, LOW  } },
    END_OF_MODE_TABLE,
};

static const uint32_t rfswitch_dio_pins_elecrow[] = {
    RADIOLIB_LR11X0_DIO5, RADIOLIB_LR11X0_DIO6,
    RADIOLIB_NC, RADIOLIB_NC, RADIOLIB_NC
};

static const Module::RfSwitchMode_t rfswitch_table_elecrow[] = {
    // mode                  DIO5  DIO6
    { LR11x0::MODE_STBY,   { LOW,  LOW  } },
    { LR11x0::MODE_RX,     { HIGH, LOW  } },
    { LR11x0::MODE_TX,     { HIGH, HIGH } },
    { LR11x0::MODE_TX_HP,  { LOW,  HIGH } },
    { LR11x0::MODE_TX_HF,  { LOW,  LOW  } },
    { LR11x0::MODE_GNSS,   { LOW,  LOW  } },
    { LR11x0::MODE_WIFI,   { LOW,  LOW  } },
    END_OF_MODE_TABLE,
};

static const uint32_t rfswitch_dio_pins_lilygo[] = {
    RADIOLIB_LR11X0_DIO5, RADIOLIB_LR11X0_DIO6,
    10 /* SOC_GPIO_PIN_ELRS_HF_RX */, 14 /* SOC_GPIO_PIN_ELRS_HF_TX */,
    RADIOLIB_NC
};

static const Module::RfSwitchMode_t rfswitch_table_lilygo[] = {
    // mode                  DIO5  DIO6  HF_RX HF_TX
    { LR11x0::MODE_STBY,   { LOW,  LOW,  LOW,  LOW  } },
    { LR11x0::MODE_RX,     { LOW,  HIGH, HIGH, LOW  } },
    { LR11x0::MODE_TX,     { HIGH, LOW,  LOW,  LOW  } },
    { LR11x0::MODE_TX_HP,  { HIGH, LOW,  LOW,  LOW  } },
    { LR11x0::MODE_TX_HF,  { LOW,  LOW,  LOW,  HIGH } },
    { LR11x0::MODE_GNSS,   { LOW,  LOW,  LOW,  LOW  } },
    { LR11x0::MODE_WIFI,   { LOW,  LOW,  LOW,  LOW  } },
    END_OF_MODE_TABLE,
};

static const uint32_t rfswitch_dio_pins_XY16EXP33[] = {
    RADIOLIB_LR11X0_DIO5, RADIOLIB_LR11X0_DIO6,
    RADIOLIB_LR11X0_DIO7, RADIOLIB_LR11X0_DIO8,
    RADIOLIB_NC
};

static const Module::RfSwitchMode_t rfswitch_table_XY16EXP33_sub1g[] = {
    // mode                  DIO5 DIO6 DIO7 DIO8
    { LR11x0::MODE_STBY,   { LOW, LOW, LOW, LOW  } },
    { LR11x0::MODE_TX,     { LOW, LOW, LOW, LOW  } },
    { LR11x0::MODE_RX,     { LOW, LOW, LOW, LOW  } },
    { LR11x0::MODE_TX_HP,  { LOW, LOW, LOW, HIGH } }, // Sub-1G DIO8 SET HIGH
    { LR11x0::MODE_TX_HF,  { LOW, LOW, LOW, LOW  } },
    { LR11x0::MODE_GNSS,   { LOW, LOW, LOW, HIGH } },
    { LR11x0::MODE_WIFI,   { LOW, LOW, LOW, HIGH } },
    END_OF_MODE_TABLE,
};

static const Module::RfSwitchMode_t rfswitch_table_XY16EXP33_2g4[] = {
    // mode                  DIO5 DIO6  DIO7  DIO8
    { LR11x0::MODE_STBY,   { LOW, LOW,  LOW,  LOW } },
    { LR11x0::MODE_TX,     { LOW, LOW,  LOW,  LOW } },
    { LR11x0::MODE_RX,     { LOW, LOW,  LOW,  LOW } },
    { LR11x0::MODE_TX_HP,  { LOW, LOW,  LOW,  LOW } },
    { LR11x0::MODE_TX_HF,  { LOW, LOW,  HIGH, LOW } }, // 2.4G TX DIO7 SET HIGH
    { LR11x0::MODE_GNSS,   { LOW, LOW,  LOW,  LOW } },
    { LR11x0::MODE_WIFI,   { LOW, HIGH, LOW,  LOW } }, // 2.4G RX DIO6 SET HIGH
    END_OF_MODE_TABLE,
};
#endif /* USE_LR11XX */

// this function is called when a complete packet
// is received by the module
// IMPORTANT: this function MUST be 'void' type
//            and MUST NOT have any arguments!
#if defined(ESP8266) || defined(ESP32)
  ICACHE_RAM_ATTR
#endif
void lr112x_receive_handler(void) {
  lr112x_receive_complete = true;
}

static bool lr1110_probe()
{
#if USE_SX1262
  return false;
#endif
#if USE_LR11XX
  u1_t device, device_reset;
  u1_t hw, major, minor;

  SoC->SPI_begin();

  lmic_hal_init (nullptr);

  // manually reset radio
  hal_pin_rst(0); // drive RST pin low
  hal_waitUntil(os_getTime()+ms2osticks(1)); // wait >100us

  lr11xx_GetVersion(&hw, &device_reset, &major, &minor);

  hal_pin_rst(2); // configure RST pin floating!
  hal_waitUntil(os_getTime()+ms2osticks(300)); // wait 300 ms

  lr11xx_GetVersion(&hw, &device, &major, &minor);

  pinMode(lmic_pins.nss, INPUT);
  RadioSPI.end();

  if (device == RADIOLIB_LR11X0_DEVICE_LR1110) {

    if (device_reset == RADIOLIB_LR11X0_DEVICE_LR1110) {
      RF_SX12XX_RST_is_connected = false;
    }
#if 0
    char buf[8];
    snprintf(buf, sizeof(buf), "%d.%d", major, minor);
    Serial.print("INFO: LR1110 base FW version ");
    Serial.println(buf);
#endif
    return true;
  } else {
    return false;
  }
#endif
}

static bool lr1121_probe()
{
#if USE_SX1262
  u1_t v, v_reset;

  SoC->SPI_begin();

  lmic_hal_init (nullptr);

  // manually reset radio
  hal_pin_rst(0); // drive RST pin low
  hal_waitUntil(os_getTime()+ms2osticks(1)); // wait >100us

  v_reset = sx1262_ReadReg(REG_LORASYNCWORDLSB);

  hal_pin_rst(2); // configure RST pin floating!
  hal_waitUntil(os_getTime()+ms2osticks(5)); // wait 5ms

  v = sx1262_ReadReg(REG_LORASYNCWORDLSB);

  pinMode(lmic_pins.nss, INPUT);
  RadioSPI.end();

  u1_t fanet_sw_lsb = ((fanet_proto_desc.syncword[0]  & 0x0F) << 4) | 0x04;
  if (v == SX126X_DEF_LORASYNCWORDLSB || v == fanet_sw_lsb) {

    if (v_reset == SX126X_DEF_LORASYNCWORDLSB || v_reset == fanet_sw_lsb) {
      RF_SX12XX_RST_is_connected = false;
    }

    return true;
  } else {
    return false;
  }
#endif

#if USE_LR11XX
  u1_t device, device_reset;
  u1_t hw, major, minor;

  SoC->SPI_begin();

  lmic_hal_init (nullptr);

  // manually reset radio
  hal_pin_rst(0); // drive RST pin low
  hal_waitUntil(os_getTime()+ms2osticks(1)); // wait >100us

  lr11xx_GetVersion(&hw, &device_reset, &major, &minor);

  hal_pin_rst(2); // configure RST pin floating!
  hal_waitUntil(os_getTime()+ms2osticks(300)); // wait 300 ms

  lr11xx_GetVersion(&hw, &device, &major, &minor);

  if (device != 0x00 && device != 0xFF) {
    lr11xx_GetChipEui(&lr11xx_eui_be);
  }

  pinMode(lmic_pins.nss, INPUT);
  RadioSPI.end();

  if (device == RADIOLIB_LR11X0_DEVICE_LR1121) {

    if (device_reset == RADIOLIB_LR11X0_DEVICE_LR1121) {
      RF_SX12XX_RST_is_connected = false;
    }
#if 0
    char buf[8];
    snprintf(buf, sizeof(buf), "%d.%d", major, minor);
    Serial.print("INFO: LR1121 base FW version ");
    Serial.println(buf);
#endif
    return true;
  } else {
    return false;
  }
#endif
}

static void lr11xx_channel(int8_t channel)
{
  if (channel != -1 && channel != lr112x_channel_prev) {
    uint32_t frequency = RF_FreqPlan.getChanFrequency((uint8_t) channel);
    int8_t fc = settings->freq_corr;

    if (settings->rf_protocol == RF_PROTOCOL_LEGACY) {
      nRF905_band_t nrf_band;
      uint32_t nrf_freq_resolution;

      nrf_band = (frequency >= 844800000UL ? NRF905_BAND_868 : NRF905_BAND_433);
      nrf_freq_resolution = (nrf_band == NRF905_BAND_433 ? 100000UL : 200000UL);
      frequency -= (frequency % nrf_freq_resolution);
    }

    if (fc > 30) {
      fc = 30;
    } else if (fc < -30) {
      fc = -30;
    };

    int rl_state = radio_semtech->setFrequency((frequency + (fc * 1000)) / 1000000.0);

#if RADIOLIB_DEBUG_BASIC
    if (rl_state == RADIOLIB_ERR_INVALID_FREQUENCY) {
      Serial.println(F("[LR11XX] Selected frequency is invalid for this module!"));
      while (true) { delay(10); }
    }
#endif

    lr112x_channel_prev = channel;
    /* restart Rx upon a channel switch */
    lr112x_receive_active = false;
  }
}

#if defined(RASPBERRY_PI) || defined(LUCKFOX_LYRA)
PiHal *RadioLib_HAL = NULL;
#endif // RASPBERRY_PI

static void lr11xx_setup()
{
  int rl_state;

  SoC->SPI_begin();

  uint32_t irq  = lmic_pins.dio[0] == LMIC_UNUSED_PIN ?
                  RADIOLIB_NC : lmic_pins.dio[0];
  uint32_t busy = lmic_pins.busy == LMIC_UNUSED_PIN ?
                  RADIOLIB_NC : lmic_pins.busy;

#if defined(RASPBERRY_PI) || defined(LUCKFOX_LYRA)

  // deinit LGPIO resources for PiHal to re-acquire them
  lgpio_fini();

#if defined(USE_SPI1)
  RadioLib_HAL = new PiHal(0, 2000000, 1); // use SPI bus #1, channel 0
#else
  RadioLib_HAL = new PiHal(0);             // use SPI bus #0, channel 0
#endif /* USE_SPI1 */

  mod   = new Module(RadioLib_HAL, lmic_pins.nss, irq, lmic_pins.rst, busy);
#else
  mod   = new Module(lmic_pins.nss, irq, lmic_pins.rst, busy, RadioSPI);
#endif // RASPBERRY_PI

#if USE_SX1262
  bool high = false;
  radio_semtech = new SX1262(mod);
#endif
#if USE_LR11XX
  switch (rf_chip->type)
  {
  case RF_IC_LR1110:
    radio_semtech = new LR1110(mod);
    break;
  case RF_IC_LR1121:
  default:
    radio_semtech = new LR1121(mod);
    break;
  }
#endif

  switch (settings->rf_protocol)
  {
  case RF_PROTOCOL_OGNTP:
    rl_protocol     = &ogntp_proto_desc;
    protocol_encode = &ogntp_encode;
    protocol_decode = &ogntp_decode;
    break;
  case RF_PROTOCOL_P3I:
    rl_protocol     = &p3i_proto_desc;
    protocol_encode = &p3i_encode;
    protocol_decode = &p3i_decode;
    break;
  case RF_PROTOCOL_FANET:
    rl_protocol     = &fanet_proto_desc;
    protocol_encode = &fanet_encode;
    protocol_decode = &fanet_decode;
    break;
#if defined(ENABLE_PROL)
  case RF_PROTOCOL_APRS:
    rl_protocol     = &prol_proto_desc;
    protocol_encode = &aprs_encode;
    protocol_decode = &aprs_decode;
    break;
#endif /* ENABLE_PROL */
#if defined(ENABLE_ADSL)
  case RF_PROTOCOL_ADSL_860:
    rl_protocol     = &adsl_proto_desc;
    protocol_encode = &adsl_encode;
    protocol_decode = &adsl_decode;
    break;
#endif /* ENABLE_ADSL */
  case RF_PROTOCOL_LEGACY:
  default:
    rl_protocol     = &legacy_proto_desc;
    protocol_encode = &legacy_encode;
    protocol_decode = &legacy_decode;
    /*
     * Enforce legacy protocol setting for LR11XX
     * if other value (UAT) left in EEPROM from other (UATM) radio
     */
    settings->rf_protocol = RF_PROTOCOL_LEGACY;
    break;
  }

  RF_FreqPlan.setPlan(settings->band, settings->rf_protocol);

#if USE_LR11XX
  float Vtcxo;
  uint64_t eui_le = __builtin_bswap64(lr11xx_eui_be);

  /*
   *  Product/Module  |   IC   |       EUI          | Use case
   *  ----------------+--------+--------------------+-----------
   *  HPDTeK HPD-16E  | LR1121 | 0x0016c001f0182465 | Standalone
   *  HPDTeK HPD-16E  | LR1121 | 0x0016c001f01824af | Badge
   *  HPDTeK HPD-16E  | LR1121 | 0x0016c001f018276a | Prime Mk3
   *  Seeed T1000-E   | LR1110 | 0x0016c001f03a86ab | Card
   *  Ebyte E80       | LR1121 | 0x0016c001f047ac30 | Academy
   *  RadioMaster XR1 | LR1121 | 0x0016c001f09aa1b7 | Nano
   *  Elecrow TN-M3   | LR1110 | 0x0016c001f00f0b12 | Pocket
   */

  switch (hw_info.model)
  {
  case SOFTRF_MODEL_STANDALONE:
  case SOFTRF_MODEL_ACADEMY:
  case SOFTRF_MODEL_RASPBERRY:
    if (hw_info.revision == STD_EDN_REV_EHUB ||
        eui_le           == 0x0016c001f047ac30)
      // Ebyte E80-900M2213S
      // LR1121 TCXO Voltage
      Vtcxo = 1.8;
    else
      // HPDTeK HPD-16E
      // LR1121 TCXO Voltage 2.85~3.15V
      Vtcxo = 3.0;
    break;

  case SOFTRF_MODEL_NANO:
    if (eui_le == 0x0016c001f047ac30) {
      // Ebyte E80-900M2213S
      // LR1121 TCXO Voltage
      Vtcxo = 1.8;
    } else {
      // YL320 XTAL on XR1 V1.0
      Vtcxo = 0.0f;
#if RADIOLIB_VERSION_MAJOR >= 7 && RADIOLIB_VERSION_MINOR < 7
      radio_semtech->XTAL = true;
#endif /* RADIOLIB_VERSION_MINOR */
    }
    break;

  case SOFTRF_MODEL_NEO:
  case SOFTRF_MODEL_BADGE:
  case SOFTRF_MODEL_PRIME_MK3:
  case SOFTRF_MODEL_PRIME_MK4:
    // HPDTeK HPD-16E
    // LR1121 TCXO Voltage 2.85~3.15V
    Vtcxo = 3.0;
    break;

  case SOFTRF_MODEL_POCKET:
    // LR1110 TCXO Voltage
    Vtcxo = 3.3;
    break;

  case SOFTRF_MODEL_CARD:
    // Seeed
    // LR1110 TCXO Voltage
  default:
    Vtcxo = 1.6;
    break;
  }

  uint32_t frequency = RF_FreqPlan.getChanFrequency(0);
  bool high = (frequency > 1000000000) ; /* above 1GHz */
#endif

  float br, fdev, bw;
  switch (rl_protocol->modulation_type)
  {
  case RF_MODULATION_TYPE_LORA:
#if RADIOLIB_DEBUG_BASIC
    Serial.print(F("[LR11XX] Initializing ... "));
#endif

#if USE_SX1262
    rl_state = radio_semtech->begin();    // start LoRa mode (and disable FSK)
#endif
#if USE_LR11XX
    rl_state = radio_semtech->begin(125.0, 9, 7,
                                    RADIOLIB_LR11X0_LORA_SYNC_WORD_PRIVATE,
                                    8, Vtcxo);
#endif

#if RADIOLIB_DEBUG_BASIC
    if (rl_state == RADIOLIB_ERR_NONE) {
      Serial.println(F("success!"));
    } else {
      Serial.print(F("failed, code "));
      Serial.println((int16_t) rl_state);
      while (true) { delay(10); }
    }
#endif

    switch (RF_FreqPlan.Bandwidth)
    {
    case RF_RX_BANDWIDTH_SS_62KHZ:
      bw = high ? 203.125 : 125.0; /* BW_125 */
      break;
    case RF_RX_BANDWIDTH_SS_250KHZ:
      bw = high ? 812.5   : 500.0; /* BW_500 */
      break;
    case RF_RX_BANDWIDTH_SS_125KHZ:
    default:
      bw = high ? 406.25  : 250.0; /* BW_250 */
      break;
    }
#if USE_SX1262
    rl_state = radio_semtech->setBandwidth(bw);
#endif
#if USE_LR11XX
    rl_state = radio_semtech->setBandwidth(bw, high);
#endif

#if RADIOLIB_DEBUG_BASIC
    if (rl_state == RADIOLIB_ERR_INVALID_BANDWIDTH) {
      Serial.println(F("[LR11XX] Selected bandwidth is invalid for this module!"));
      while (true) { delay(10); }
    }
#endif

    switch (rl_protocol->type)
    {
    case RF_PROTOCOL_FANET:
    default:
      rl_state = radio_semtech->setSpreadingFactor(7); /* SF_7 */
      rl_state = radio_semtech->setCodingRate(5);      /* CR_5 */
      break;
    }

    rl_state = radio_semtech->setSyncWord((uint8_t) rl_protocol->syncword[0]);

#if RADIOLIB_DEBUG_BASIC
    if (rl_state == RADIOLIB_ERR_INVALID_SYNC_WORD) {
      Serial.println(F("[LR11XX] Selected sync word is invalid for this module!"));
      while (true) { delay(10); }
    }
#endif

    rl_state = radio_semtech->setPreambleLength(8);
    rl_state = radio_semtech->explicitHeader();
    rl_state = radio_semtech->setCRC(true);

    break;
  case RF_MODULATION_TYPE_2FSK:
  case RF_MODULATION_TYPE_PPM: /* TBD */
  default:

#if USE_SX1262
    rl_state = radio_semtech->beginFSK(); // start FSK mode (and disable LoRa)
#endif
#if USE_LR11XX
#if RADIOLIB_VERSION_MAJOR >= 7 && RADIOLIB_VERSION_MINOR < 7
    rl_state = radio_semtech->beginGFSK(4.8, 5.0, 156.2, 16, Vtcxo);
#else
    radio_semtech->tcxoVoltage = Vtcxo;
    rl_state = radio_semtech->beginGFSK(4.8, 5.0, 156.2, 16);
#endif /* RADIOLIB_VERSION_MINOR */
#endif /* USE_LR11XX */

    switch (rl_protocol->bitrate)
    {
    case RF_BITRATE_38400:
#if USE_SX1262
      br = 38.4;
#endif
#if USE_LR11XX
      br = high ? 125.0 :  38.4; /* SX128x minimum is 125 kbps */
#endif
      break;
    case RF_BITRATE_100KBPS:
    default:
#if USE_SX1262
      br = 100.0;
#endif
#if USE_LR11XX
      br = high ? 125.0 : 100.0; /* SX128x minimum is 125 kbps */
#endif
      break;
    }
    rl_state = radio_semtech->setBitRate(br);

#if RADIOLIB_DEBUG_BASIC
  if (rl_state == RADIOLIB_ERR_INVALID_BIT_RATE) {
    Serial.println(F("[LR11XX] Selected bit rate is invalid for this module!"));
    while (true) { delay(10); }
  } else if (rl_state == RADIOLIB_ERR_INVALID_BIT_RATE_BW_RATIO) {
    Serial.println(F("[LR11XX] Selected bit rate to bandwidth ratio is invalid!"));
    Serial.println(F("[LR11XX] Increase receiver bandwidth to set this bit rate."));
    while (true) { delay(10); }
  }
#endif

    switch (rl_protocol->deviation)
    {
    case RF_FREQUENCY_DEVIATION_10KHZ:
#if USE_SX1262
      fdev = 10.0;
#endif
#if USE_LR11XX
      fdev = high ? 62.5 : 10.0; /* SX128x minimum is 62.5 kHz */
#endif
      break;
    case RF_FREQUENCY_DEVIATION_19_2KHZ:
      fdev = 19.2;
      break;
    case RF_FREQUENCY_DEVIATION_25KHZ:
      fdev = 25.0;
      break;
    case RF_FREQUENCY_DEVIATION_50KHZ:
    case RF_FREQUENCY_DEVIATION_NONE:
    default:
#if USE_SX1262
      fdev = 50.0;
#endif
#if USE_LR11XX
      fdev = high ? 62.5 : 50.0; /* SX128x minimum is 62.5 kHz */
#endif
      break;
    }
    rl_state = radio_semtech->setFrequencyDeviation(fdev);

#if RADIOLIB_DEBUG_BASIC
  if (rl_state == RADIOLIB_ERR_INVALID_FREQUENCY_DEVIATION) {
    Serial.println(F("[LR11XX] Selected frequency deviation is invalid for this module!"));
    while (true) { delay(10); }
  }
#endif

    switch (rl_protocol->bandwidth)
    {
    case RF_RX_BANDWIDTH_SS_50KHZ:
      bw = 117.3;
      break;
    case RF_RX_BANDWIDTH_SS_62KHZ:
      bw = 156.2;
      break;
    case RF_RX_BANDWIDTH_SS_100KHZ:
      bw = 234.3;
      break;
    case RF_RX_BANDWIDTH_SS_166KHZ:
      bw = 312.0;
      break;
    case RF_RX_BANDWIDTH_SS_200KHZ:
    case RF_RX_BANDWIDTH_SS_250KHZ:  /* TBD */
    case RF_RX_BANDWIDTH_SS_1567KHZ: /* TBD */
      bw = 467.0;
      break;
    case RF_RX_BANDWIDTH_SS_125KHZ:
    default:
      bw = 234.3;
      break;
    }
    rl_state = radio_semtech->setRxBandwidth(bw);

    rl_state = radio_semtech->setPreambleLength(rl_protocol->preamble_size * 8);
    rl_state = radio_semtech->setDataShaping(RADIOLIB_SHAPING_0_5);

    switch (rl_protocol->crc_type)
    {
    case RF_CHECKSUM_TYPE_CCITT_FFFF:
    case RF_CHECKSUM_TYPE_CCITT_0000:
    case RF_CHECKSUM_TYPE_CCITT_1D02:
    case RF_CHECKSUM_TYPE_CRC8_107:
    case RF_CHECKSUM_TYPE_RS:
      /* CRC is driven by software */
      rl_state = radio_semtech->setCRC(0, 0);
      break;
    case RF_CHECKSUM_TYPE_GALLAGER:
    case RF_CHECKSUM_TYPE_CRC_MODES:
    case RF_CHECKSUM_TYPE_NONE:
    default:
      rl_state = radio_semtech->setCRC(0, 0);
      break;
    }

    size_t pkt_size = rl_protocol->payload_offset + rl_protocol->payload_size +
                      rl_protocol->crc_size;

    switch (rl_protocol->whitening)
    {
    case RF_WHITENING_MANCHESTER:
      pkt_size += pkt_size;
      break;
    case RF_WHITENING_PN9:
    case RF_WHITENING_NONE:
    case RF_WHITENING_NICERF:
    default:
      break;
    }

    rl_state = radio_semtech->setWhitening(false, 0x0001 /* default SX128x value */);

    rl_state = radio_semtech->fixedPacketLengthMode(pkt_size);

#if USE_LR11XX
    rl_state = radio_semtech->disableAddressFiltering();
#endif /* USE_LR11XX */

    /* Work around premature P3I syncword detection */
    if (rl_protocol->syncword_size == 2) {
      uint8_t preamble = rl_protocol->preamble_type == RF_PREAMBLE_TYPE_AA ?
                         0xAA : 0x55;
      uint8_t sword[4] = { preamble,
                           preamble,
                           rl_protocol->syncword[0],
                           rl_protocol->syncword[1]
                         };
      rl_state = radio_semtech->setSyncWord(sword, 4);
    } else {
      rl_state = radio_semtech->setSyncWord((uint8_t *) rl_protocol->syncword,
                                            (size_t)    rl_protocol->syncword_size);
    }
    break;
  }

#if USE_LR11XX
  if (high) {
    rl_state = radio_semtech->setFrequency(frequency / 1000000.0);

#if RADIOLIB_DEBUG_BASIC
    if (rl_state == RADIOLIB_ERR_INVALID_FREQUENCY) {
      Serial.println(F("[LR11XX] Selected frequency is invalid for this module!"));
      while (true) { delay(10); }
    }
#endif
  }
#endif /* USE_LR11XX */

#if defined(USE_FEM)
  bool has_fem = (hw_info.model == SOFTRF_MODEL_PRIME_MK4) ? true : false;
#endif /* USE_FEM */

  float txpow;

  switch(settings->txpower)
  {
  case RF_TX_POWER_FULL:

    /* Load regional max. EIRP at first */
    txpow = RF_FreqPlan.MaxTxPower;

#if defined(USE_FEM)
    if (has_fem == true) {
      if (txpow > 34)
        txpow = 34;
    } else
#endif /* USE_FEM */
    {
      if (txpow > 22) txpow = 22;

#if 1
      /*
       * Enforce Tx power limit until confirmation
       * that LR11xx is doing well
       * when antenna is not connected
       */
      if (txpow > 17)
        txpow = 17;
#endif

#if USE_LR11XX
      if (high && txpow > 13) txpow = 13;
#endif /* USE_LR11XX */
    }

    break;
  case RF_TX_POWER_OFF:
  case RF_TX_POWER_LOW:
  default:
    txpow = 2;
    break;
  }

#if defined(USE_FEM)
  if (hw_info.model == SOFTRF_MODEL_PRIME_MK4) {
    if (high) {
      txpow -= 34; /* CB5337CX */
      if (txpow > 0 /* 1 ? */ ) txpow = 0 /* 1 ? */;
    } else {
      txpow -= 12; /* HM06S006P */
    }
  }
#endif /* USE_FEM */

#if USE_SX1262
  uint32_t rxe = lmic_pins.rxe == LMIC_UNUSED_PIN ? RADIOLIB_NC : lmic_pins.rxe;
  uint32_t txe = lmic_pins.txe == LMIC_UNUSED_PIN ? RADIOLIB_NC : lmic_pins.txe;
  if (rxe == RADIOLIB_NC && txe == RADIOLIB_NC) {
    rl_state = radio_semtech->setDio2AsRfSwitch();
  } else {
    radio_semtech->setRfSwitchPins(rxe, txe);
  }

  rl_state = radio_semtech->setCurrentLimit(100.0);

  rl_state = radio_semtech->setOutputPower(txpow);
#endif

#if USE_LR11XX
  switch (hw_info.model)
  {
  case SOFTRF_MODEL_CARD:
#if RADIOLIB_VERSION_MAJOR >= 7 && RADIOLIB_VERSION_MINOR > 1
    radio_semtech->setRfSwitchTable(rfswitch_dio_pins_seeed, rfswitch_table_seeed);
    {
      bool useHp = false || (txpow > 14);
      rl_state = radio_semtech->setOutputPower(txpow, useHp, useHp, 0x04, 0x07, lr11xx_roundRampTime(48) - 0x03);
    }
#else
    radio_semtech->setDioAsRfSwitch(0x0f, 0x0, 0x09, 0x0B, 0x0A, 0x0, 0x4, 0x0);
    rl_state = radio_semtech->setOutputPower(txpow, false);
#endif /* RADIOLIB_VERSION_MINOR */
    break;

  case SOFTRF_MODEL_STANDALONE:
  case SOFTRF_MODEL_ACADEMY:
  case SOFTRF_MODEL_RASPBERRY:
    if (hw_info.revision == STD_EDN_REV_EHUB ||
        eui_le           == 0x0016c001f047ac30) {
      /* Ebyte E80-900M2213S */
#if RADIOLIB_VERSION_MAJOR >= 7 && RADIOLIB_VERSION_MINOR > 1
      radio_semtech->setRfSwitchTable(rfswitch_dio_pins_ebyte, rfswitch_table_ebyte);
      {
        uint8_t paSel = 0;
        uint8_t paSupply = 0;
        if (high) {
          paSel = 2;
        } else if (false || (txpow > 14)) {
          paSel = 1;
          paSupply = 1;
        }
        rl_state = radio_semtech->setOutputPower(txpow, paSel, paSupply, 0x04, 0x07, lr11xx_roundRampTime(48) - 0x03);
      }
#else
      radio_semtech->setDioAsRfSwitch(0x07, 0x0, 0x02, 0x03, 0x01, 0x0, 0x4, 0x0);
      rl_state = radio_semtech->setOutputPower(txpow, false);
#endif /* RADIOLIB_VERSION_MINOR */
    } else {
      radio_semtech->setRfSwitchTable(rfswitch_dio_pins_hpdtek, rfswitch_table_hpdtek);
#if RADIOLIB_VERSION_MAJOR >= 7 && RADIOLIB_VERSION_MINOR > 1
      {
        uint8_t paSel = 0;
        uint8_t paSupply = 0;
        if (high) {
          paSel = 2;
        } else if (true || (txpow > 14)) {
          paSel = 1;
          paSupply = 1;
        }
        rl_state = radio_semtech->setOutputPower(txpow, paSel, paSupply, 0x04, 0x07, lr11xx_roundRampTime(48) - 0x03);
      }
#else
      rl_state = radio_semtech->setOutputPower(txpow, high ? false : true);
#endif /* RADIOLIB_VERSION_MINOR */
    }
    break;

  case SOFTRF_MODEL_NANO:
    if (eui_le == 0x0016c001f047ac30) {
      /* Ebyte E80-900M2213S */
#if RADIOLIB_VERSION_MAJOR >= 7 && RADIOLIB_VERSION_MINOR > 1
      radio_semtech->setRfSwitchTable(rfswitch_dio_pins_ebyte, rfswitch_table_ebyte);
      {
        uint8_t paSel = 0;
        uint8_t paSupply = 0;
        if (high) {
          paSel = 2;
        } else if (false || (txpow > 14)) {
          paSel = 1;
          paSupply = 1;
        }
        rl_state = radio_semtech->setOutputPower(txpow, paSel, paSupply, 0x04, 0x07, lr11xx_roundRampTime(48) - 0x03);
      }
#else
      radio_semtech->setDioAsRfSwitch(0x07, 0x0, 0x02, 0x03, 0x01, 0x0, 0x4, 0x0);
      rl_state = radio_semtech->setOutputPower(txpow, false);
#endif /* RADIOLIB_VERSION_MINOR */
    } else {
      if (hw_info.revision == 2) {
        /* LilyGO T-Lora Dual LR, a.k.a. LilyGO T-ELRS-LR1121 */
        radio_semtech->setRfSwitchTable(rfswitch_dio_pins_lilygo, rfswitch_table_lilygo);
      } else {
        /* RadioMaster XR1 */
#if 1
        radio_semtech->setRfSwitchTable(rfswitch_dio_pins_radiomaster, rfswitch_table_radiomaster);
#else
        radio_semtech->setDioAsRfSwitch(0x0F, 0x0, 0x0C, 0x08, 0x08, 0x6, 0x0, 0x5);
#endif
      }
#if RADIOLIB_VERSION_MAJOR >= 7 && RADIOLIB_VERSION_MINOR > 1
      {
        uint8_t paSel = 0;
        uint8_t paSupply = 0;
        if (high) {
          paSel = 2;
        } else if (true || (txpow > 14)) {
          paSel = 1;
          paSupply = 1;
        }
        rl_state = radio_semtech->setOutputPower(txpow, paSel, paSupply, 0x04, 0x07, lr11xx_roundRampTime(48) - 0x03);
      }
#else
      rl_state = radio_semtech->setOutputPower(txpow, high ? false : true);
#endif /* RADIOLIB_VERSION_MINOR */
    }
    break;

  case SOFTRF_MODEL_POCKET:
    radio_semtech->setRfSwitchTable(rfswitch_dio_pins_elecrow, rfswitch_table_elecrow);
#if RADIOLIB_VERSION_MAJOR >= 7 && RADIOLIB_VERSION_MINOR > 1
    {
      bool useHp = false || (txpow > 14);
      rl_state = radio_semtech->setOutputPower(txpow, useHp, useHp, 0x04, 0x07, lr11xx_roundRampTime(48) - 0x03);
    }
#else
    rl_state = radio_semtech->setOutputPower(txpow, false);
#endif /* RADIOLIB_VERSION_MINOR */
    break;

  case SOFTRF_MODEL_PRIME_MK4:
    radio_semtech->setRfSwitchTable(rfswitch_dio_pins_XY16EXP33, high ?
                                    rfswitch_table_XY16EXP33_2g4 :
                                    rfswitch_table_XY16EXP33_sub1g);
#if RADIOLIB_VERSION_MAJOR >= 7 && RADIOLIB_VERSION_MINOR > 1
    {
      uint8_t paSel = 0;
      uint8_t paSupply = 0;
      if (high) {
        paSel = 2;
      } else if (true || (txpow > 14)) {
        paSel = 1;
        paSupply = 1;
      }
      rl_state = radio_semtech->setOutputPower(txpow, paSel, paSupply, 0x04, 0x07, lr11xx_roundRampTime(48) - 0x03);
    }
#else
    rl_state = radio_semtech->setOutputPower(txpow, high ? false : true);
#endif /* RADIOLIB_VERSION_MINOR */
    break;

  case SOFTRF_MODEL_NEO:
  case SOFTRF_MODEL_BADGE:
  case SOFTRF_MODEL_PRIME_MK3:
  default:
    radio_semtech->setRfSwitchTable(rfswitch_dio_pins_hpdtek, rfswitch_table_hpdtek);
#if RADIOLIB_VERSION_MAJOR >= 7 && RADIOLIB_VERSION_MINOR > 1
    {
      uint8_t paSel = 0;
      uint8_t paSupply = 0;
      if (high) {
        paSel = 2;
      } else if (true || (txpow > 14)) {
        paSel = 1;
        paSupply = 1;
      }
      rl_state = radio_semtech->setOutputPower(txpow, paSel, paSupply, 0x04, 0x07, lr11xx_roundRampTime(48) - 0x03);
    }
#else
    rl_state = radio_semtech->setOutputPower(txpow, high ? false : true);
#endif /* RADIOLIB_VERSION_MINOR */
    break;
  }
#endif

  rl_state = radio_semtech->setRxBoostedGainMode(true);

  radio_semtech->setPacketReceivedAction(lr112x_receive_handler);
}

static bool lr11xx_receive()
{
  bool success = false;
  int rl_state;

  if (settings->power_save & POWER_SAVE_NORECEIVE) {
    return success;
  }

  if (!lr112x_receive_active) {

    rl_state = radio_semtech->startReceive();
    if (rl_state == RADIOLIB_ERR_NONE) {
      lr112x_receive_active = true;
    }
  }

#if defined(plat_radio_irq_func)
  if (mod->getIrq() == RADIOLIB_NC) {
   if (plat_radio_irq_func(mod->getIrq())) {
     lr112x_receive_handler();
   }
  }
#endif /* plat_radio_irq_func */

  if (lr112x_receive_complete == true) {

    RL_rxPacket.len = radio_semtech->getPacketLength();

    if (RL_rxPacket.len > 0) {

      if (RL_rxPacket.len > sizeof(RL_rxPacket.payload)) {
        RL_rxPacket.len = sizeof(RL_rxPacket.payload);
      }

      rl_state = radio_semtech->readData(RL_rxPacket.payload, RL_rxPacket.len);
      lr112x_receive_active = false;

      if (rl_state == RADIOLIB_ERR_NONE &&
         !memeqzero(RL_rxPacket.payload, RL_rxPacket.len)) {
        size_t size = 0;
        uint8_t offset;

        u1_t crc8, pkt_crc8;
        u2_t crc16, pkt_crc16;

        RadioLib_DataPacket *RL_rxPacket_ptr = &RL_rxPacket;

        switch (rl_protocol->crc_type)
        {
        case RF_CHECKSUM_TYPE_GALLAGER:
        case RF_CHECKSUM_TYPE_CRC_MODES:
        case RF_CHECKSUM_TYPE_NONE:
           /* crc16 left not initialized */
          break;
        case RF_CHECKSUM_TYPE_CRC8_107:
          crc8 = 0x71;     /* seed value */
          break;
        case RF_CHECKSUM_TYPE_CCITT_0000:
          crc16 = 0x0000;  /* seed value */
          break;
        case RF_CHECKSUM_TYPE_CCITT_FFFF:
        default:
          crc16 = 0xffff;  /* seed value */
          break;
        }

        switch (rl_protocol->type)
        {
        case RF_PROTOCOL_LEGACY:
          /* take in account NRF905/FLARM "address" bytes */
          crc16 = update_crc_ccitt(crc16, 0x31);
          crc16 = update_crc_ccitt(crc16, 0xFA);
          crc16 = update_crc_ccitt(crc16, 0xB6);
          break;
        case RF_PROTOCOL_P3I:
        case RF_PROTOCOL_OGNTP:
        case RF_PROTOCOL_ADSL_860:
        default:
          break;
        }

        uint8_t i;

        switch (rl_protocol->type)
        {
        case RF_PROTOCOL_P3I:
          offset = rl_protocol->payload_offset;
          for (i = 0; i < rl_protocol->payload_size; i++)
          {
            update_crc8(&crc8, (u1_t)(RL_rxPacket_ptr->payload[i + offset]));
            if (i < sizeof(RxBuffer)) {
              RxBuffer[i] = RL_rxPacket_ptr->payload[i + offset] ^
                            pgm_read_byte(&whitening_pattern[i]);
            }
          }

          pkt_crc8 = RL_rxPacket_ptr->payload[i + offset];

          if (crc8 == pkt_crc8) {
            success = true;
          }
          break;
        case RF_PROTOCOL_FANET:
          offset = rl_protocol->payload_offset;
          size   = rl_protocol->payload_size + rl_protocol->crc_size;
          for (i = 0; i < size; i++)
          {
            if (i < sizeof(RxBuffer)) {
              RxBuffer[i] = RL_rxPacket_ptr->payload[i + offset];
            }
          }
          success = true;
          break;
        case RF_PROTOCOL_OGNTP:
        case RF_PROTOCOL_ADSL_860:
        case RF_PROTOCOL_LEGACY:
        default:
          offset = 0;
          size   = rl_protocol->payload_offset +
                   rl_protocol->payload_size +
                   rl_protocol->payload_size +
                   rl_protocol->crc_size +
                   rl_protocol->crc_size;
          if (RL_rxPacket_ptr->len >= (size + offset)) {
            uint8_t val1, val2;
            for (i = 0; i < size; i++) {
              val1 = pgm_read_byte(&ManchesterDecode[RL_rxPacket_ptr->payload[i + offset]]);
              i++;
              val2 = pgm_read_byte(&ManchesterDecode[RL_rxPacket_ptr->payload[i + offset]]);
              if ((i>>1) < sizeof(RxBuffer)) {
                RxBuffer[i>>1] = ((val1 & 0x0F) << 4) | (val2 & 0x0F);

                if (i < size - (rl_protocol->crc_size + rl_protocol->crc_size)) {
                  switch (rl_protocol->crc_type)
                  {
                  case RF_CHECKSUM_TYPE_GALLAGER:
                  case RF_CHECKSUM_TYPE_CRC_MODES:
                  case RF_CHECKSUM_TYPE_NONE:
                    break;
                  case RF_CHECKSUM_TYPE_CCITT_FFFF:
                  case RF_CHECKSUM_TYPE_CCITT_0000:
                  default:
                    crc16 = update_crc_ccitt(crc16, (u1_t)(RxBuffer[i>>1]));
                    break;
                  }
                }
              }
            }

            size = size>>1;

            switch (rl_protocol->crc_type)
            {
            case RF_CHECKSUM_TYPE_GALLAGER:
              if (LDPC_Check((uint8_t  *) &RxBuffer[0]) == 0) {
                success = true;
              }
              break;
            case RF_CHECKSUM_TYPE_CRC_MODES:
#if defined(ENABLE_ADSL)
              if (ADSL_Packet::checkPI((uint8_t  *) &RxBuffer[0], size) == 0) {
                success = true;
              }
#endif /* ENABLE_ADSL */
              break;
            case RF_CHECKSUM_TYPE_CCITT_FFFF:
            case RF_CHECKSUM_TYPE_CCITT_0000:
              offset = rl_protocol->payload_offset + rl_protocol->payload_size;
              if (offset + 1 < sizeof(RxBuffer)) {
                pkt_crc16 = (RxBuffer[offset] << 8 | RxBuffer[offset+1]);
                if (crc16 == pkt_crc16) {

                  success = true;
                }
              }
              break;
            default:
              break;
            }
          }
          break;
        }

        if (success) {
          RF_last_rssi = radio_semtech->getRSSI();
          rx_packets_counter++;
        }
      }

      memset(RL_rxPacket.payload, 0, sizeof(RL_rxPacket.payload));
#if USE_SX1262 && (RADIOLIB_GODMODE || RADIOLIB_LOW_LEVEL)
      radio_semtech->writeBuffer(RL_rxPacket.payload, RL_rxPacket.len);
      radio_semtech->setBufferBaseAddress();
#endif
      RL_rxPacket.len = 0;
    }

    lr112x_receive_complete = false;
  }

  return success;
}

static bool lr11xx_transmit()
{
  u1_t crc8;
  u2_t crc16;
  u1_t i;

  bool success = false;

  if (RF_tx_size <= 0) {
    return success;
  }

  lr112x_receive_active = false;
  lr112x_transmit_complete = false;

  size_t PayloadLen = 0;

  switch (rl_protocol->crc_type)
  {
  case RF_CHECKSUM_TYPE_GALLAGER:
  case RF_CHECKSUM_TYPE_CRC_MODES:
  case RF_CHECKSUM_TYPE_NONE:
     /* crc16 left not initialized */
    break;
  case RF_CHECKSUM_TYPE_CRC8_107:
    crc8 = 0x71;     /* seed value */
    break;
  case RF_CHECKSUM_TYPE_CCITT_0000:
    crc16 = 0x0000;  /* seed value */
    break;
  case RF_CHECKSUM_TYPE_CCITT_FFFF:
  default:
    crc16 = 0xffff;  /* seed value */
    break;
  }

  switch (rl_protocol->type)
  {
  case RF_PROTOCOL_LEGACY:
    /* take in account NRF905/FLARM "address" bytes */
    crc16 = update_crc_ccitt(crc16, 0x31);
    crc16 = update_crc_ccitt(crc16, 0xFA);
    crc16 = update_crc_ccitt(crc16, 0xB6);
    break;
  case RF_PROTOCOL_P3I:
    /* insert Net ID */
    RL_txPacket.payload[PayloadLen++] = (u1_t) ((rl_protocol->net_id >> 24) & 0x000000FF);
    RL_txPacket.payload[PayloadLen++] = (u1_t) ((rl_protocol->net_id >> 16) & 0x000000FF);
    RL_txPacket.payload[PayloadLen++] = (u1_t) ((rl_protocol->net_id >>  8) & 0x000000FF);
    RL_txPacket.payload[PayloadLen++] = (u1_t) ((rl_protocol->net_id >>  0) & 0x000000FF);
    /* insert byte with payload size */
    RL_txPacket.payload[PayloadLen++] = rl_protocol->payload_size;

    /* insert byte with CRC-8 seed value when necessary */
    if (rl_protocol->crc_type == RF_CHECKSUM_TYPE_CRC8_107) {
      RL_txPacket.payload[PayloadLen++] = crc8;
    }

    break;
  case RF_PROTOCOL_OGNTP:
  case RF_PROTOCOL_ADSL_860:
  default:
    break;
  }

  for (i=0; i < RF_tx_size; i++) {

    switch (rl_protocol->whitening)
    {
    case RF_WHITENING_NICERF:
      RL_txPacket.payload[PayloadLen] = TxBuffer[i] ^ pgm_read_byte(&whitening_pattern[i]);
      break;
    case RF_WHITENING_MANCHESTER:
      RL_txPacket.payload[PayloadLen] = pgm_read_byte(&ManchesterEncode[(TxBuffer[i] >> 4) & 0x0F]);
      PayloadLen++;
      RL_txPacket.payload[PayloadLen] = pgm_read_byte(&ManchesterEncode[(TxBuffer[i]     ) & 0x0F]);
      break;
    case RF_WHITENING_NONE:
    default:
      RL_txPacket.payload[PayloadLen] = TxBuffer[i];
      break;
    }

    switch (rl_protocol->crc_type)
    {
    case RF_CHECKSUM_TYPE_GALLAGER:
    case RF_CHECKSUM_TYPE_CRC_MODES:
    case RF_CHECKSUM_TYPE_NONE:
      break;
    case RF_CHECKSUM_TYPE_CRC8_107:
      update_crc8(&crc8, (u1_t)(RL_txPacket.payload[PayloadLen]));
      break;
    case RF_CHECKSUM_TYPE_CCITT_FFFF:
    case RF_CHECKSUM_TYPE_CCITT_0000:
    default:
      if (rl_protocol->whitening == RF_WHITENING_MANCHESTER) {
        crc16 = update_crc_ccitt(crc16, (u1_t)(TxBuffer[i]));
      } else {
        crc16 = update_crc_ccitt(crc16, (u1_t)(RL_txPacket.payload[PayloadLen]));
      }
      break;
    }

    PayloadLen++;
  }

  switch (rl_protocol->crc_type)
  {
  case RF_CHECKSUM_TYPE_GALLAGER:
  case RF_CHECKSUM_TYPE_CRC_MODES:
  case RF_CHECKSUM_TYPE_NONE:
    break;
  case RF_CHECKSUM_TYPE_CRC8_107:
    RL_txPacket.payload[PayloadLen++] = crc8;
    break;
  case RF_CHECKSUM_TYPE_CCITT_FFFF:
  case RF_CHECKSUM_TYPE_CCITT_0000:
  default:
    if (rl_protocol->whitening == RF_WHITENING_MANCHESTER) {
      RL_txPacket.payload[PayloadLen++] = pgm_read_byte(&ManchesterEncode[(((crc16 >>  8) & 0xFF) >> 4) & 0x0F]);
      RL_txPacket.payload[PayloadLen++] = pgm_read_byte(&ManchesterEncode[(((crc16 >>  8) & 0xFF)     ) & 0x0F]);
      RL_txPacket.payload[PayloadLen++] = pgm_read_byte(&ManchesterEncode[(((crc16      ) & 0xFF) >> 4) & 0x0F]);
      RL_txPacket.payload[PayloadLen++] = pgm_read_byte(&ManchesterEncode[(((crc16      ) & 0xFF)     ) & 0x0F]);
      PayloadLen++;
    } else {
      RL_txPacket.payload[PayloadLen++] = (crc16 >>  8) & 0xFF;
      RL_txPacket.payload[PayloadLen++] = (crc16      ) & 0xFF;
    }
    break;
  }

  RL_txPacket.len = PayloadLen;

  int rl_state;

#if defined(plat_radio_irq_func)
  if (mod->getIrq() == RADIOLIB_NC) {
    RadioLibTime_t timeout = radio_semtech->getTimeOnAir(RL_txPacket.len);

#if USE_SX1262
    // calculate timeout (5ms + 500 % of expected time-on-air)
    timeout = 5000 + (timeout * 5);
#endif
#if USE_LR11XX
    if (rl_protocol->modulation_type == RF_MODULATION_TYPE_LORA) {
      // calculate timeout (150% of expected time-on-air)
      timeout = (timeout * 3) / 2;
    } else {
      // calculate timeout (500% of expected time-on-air)
      timeout = timeout * 5;
    }
#endif
    RADIOLIB_DEBUG_BASIC_PRINTLN("Timeout in %lu us", timeout);

    rl_state = radio_semtech->startTransmit((uint8_t *) &RL_txPacket.payload, (size_t) RL_txPacket.len);
    RADIOLIB_ASSERT(rl_state);

    RadioLibTime_t start = mod->hal->micros();
    while (!plat_radio_irq_func(mod->getIrq())) {
      mod->hal->yield();
      if (mod->hal->micros() - start > timeout) {
        radio_semtech->finishTransmit();
        rl_state = RADIOLIB_ERR_TX_TIMEOUT;
        break;
      }
    }

    if (rl_state != RADIOLIB_ERR_TX_TIMEOUT) {
      rl_state = radio_semtech->finishTransmit();
    }
  } else
#endif /* plat_radio_irq_func */
  {
    rl_state = radio_semtech->transmit((uint8_t *) &RL_txPacket.payload, (size_t) RL_txPacket.len);
  }

  if (rl_state == RADIOLIB_ERR_NONE) {

    success = true;

    memset(RL_txPacket.payload, 0, sizeof(RL_txPacket.payload));
#if USE_SX1262 && (RADIOLIB_GODMODE || RADIOLIB_LOW_LEVEL)
    radio_semtech->setBufferBaseAddress();
    radio_semtech->writeBuffer(RL_txPacket.payload, RL_txPacket.len);
    radio_semtech->setBufferBaseAddress();
#endif

#if 0
    // the packet was successfully transmitted
    Serial.println(F("success!"));

    // print measured data rate
    Serial.print(F("[LR11XX] Datarate:\t"));
    Serial.print((unsigned int) radio_semtech->getDataRate());
    Serial.println(F(" bps"));

  } else if (rl_state == RADIOLIB_ERR_PACKET_TOO_LONG) {
    // the supplied packet was longer than 256 bytes
    Serial.println(F("too long!"));

  } else if (rl_state == RADIOLIB_ERR_TX_TIMEOUT) {
    // timeout occured while transmitting packet
    Serial.println(F("timeout!"));

  } else {
    // some other error occurred
    Serial.print(F("failed, code "));
    Serial.println((int16_t) rl_state);
#endif
  }

  return success;
}

static void lr11xx_shutdown()
{
#if USE_SX1262
  int rl_state = radio_semtech->sleep(false);
#endif

#if USE_LR11XX
  int rl_state = radio_semtech->standby(RADIOLIB_LR11X0_STANDBY_RC);
  rl_state = radio_semtech->setTCXO(0);
  rl_state = radio_semtech->sleep(false, 0);
#endif

  RadioSPI.end();
}
#endif /* EXCLUDE_LR11XX */

#if !defined(EXCLUDE_LR20XX)

#include <fec.h>

/*
 * DF17 Rx optimization method:
 *
 * 0 - without optimization
 * 1 - DF17 sync word
 * 2 - DF17 OOK detection word
 */
#define OPT_DF17 1

static bool lr2021_probe(void);
static void lr20xx_setup(void);
static void lr20xx_channel(int8_t);
static bool lr20xx_receive(void);
static bool lr20xx_transmit(void);
static void lr20xx_shutdown(void);

const rfchip_ops_t lr2021_ops = {
  RF_IC_LR2021,
  "LR2021",
  lr2021_probe,
  lr20xx_setup,
  lr20xx_channel,
  lr20xx_receive,
  lr20xx_transmit,
  lr20xx_shutdown
};

LR2021  *radio_g4;

static int8_t lr20xx_channel_prev    = (int8_t) -1;

static volatile bool lr20xx_receive_complete = false;
static volatile int  lr20xx_receive_cb_count = 0;

static bool lr20xx_receive_active    = false;
static bool lr20xx_transmit_complete = false;

static uint64_t lr20xx_eui_be = 0xdeadbeefdeadbeef;

#if !defined(EXCLUDE_ES1090)
mode_s_t rl_mode_s_state;
#endif /* EXCLUDE_ES1090 */

/* LilyGO T-LR2021 V0.2 */
static const uint32_t rfswitch_dio_pins_MXD8721_V02[] = {
    RADIOLIB_LR2021_DIO5, RADIOLIB_LR2021_DIO6,
    RADIOLIB_NC, RADIOLIB_NC, RADIOLIB_NC
};

static const Module::RfSwitchMode_t rfswitch_table_MXD8721_V02[] = {
    // mode                  DIO5  DIO6
    { LR2021::MODE_STBY,   { LOW,  LOW  } },
    { LR2021::MODE_RX,     { LOW,  HIGH } },
    { LR2021::MODE_TX,     { LOW,  HIGH } },
    { LR2021::MODE_RX_HF,  { HIGH, LOW  } },
    { LR2021::MODE_TX_HF,  { HIGH, LOW  } },
    LR2021::MODE_END_OF_TABLE,
};

/* LilyGO T-LR2021 V0.3 */
static const uint32_t rfswitch_dio_pins_MXD8721_V03[] = {
    RADIOLIB_LR2021_DIO6, RADIOLIB_LR2021_DIO7,
    RADIOLIB_LR2021_DIO8, RADIOLIB_LR2021_DIO10,
    RADIOLIB_NC
};

static const Module::RfSwitchMode_t rfswitch_table_MXD8721_V03[] = {
    // mode                  DIO6  DIO7  DIO8  DIO10
    { LR2021::MODE_STBY,   { LOW,  LOW,  LOW,  LOW  } },
    { LR2021::MODE_RX,     { LOW,  LOW,  HIGH, LOW  } },
    { LR2021::MODE_TX,     { LOW,  LOW,  HIGH, LOW  } },
    { LR2021::MODE_RX_HF,  { HIGH, LOW,  LOW,  HIGH } },
    { LR2021::MODE_TX_HF,  { LOW,  HIGH, LOW,  HIGH } },
    LR2021::MODE_END_OF_TABLE,
};

static const uint32_t rfswitch_dio_pins_XY16E3AXP33[] = {
    RADIOLIB_LR2021_DIO6, RADIOLIB_LR2021_DIO7, RADIOLIB_LR2021_DIO8,
    RADIOLIB_NC, RADIOLIB_NC
};

static const Module::RfSwitchMode_t rfswitch_table_XY16E3AXP33[] = {
    // mode                  DIO6  DIO7  DIO8
    { LR2021::MODE_STBY,   { LOW,  LOW,  LOW  } },
    { LR2021::MODE_RX,     { LOW,  LOW,  LOW  } }, // Sub-1G ALL DIO SET LOW
    { LR2021::MODE_TX,     { LOW,  LOW,  HIGH } }, // Sub-1G DIO8 SET HIGH
    { LR2021::MODE_RX_HF,  { HIGH, LOW,  LOW  } }, // 2.4G RX DIO6 SET HIGH
    { LR2021::MODE_TX_HF,  { LOW,  HIGH, LOW  } }, // 2.4G TX DIO7 SET HIGH
    LR2021::MODE_END_OF_TABLE,
};

static const uint32_t rfswitch_dio_pins_ELRS[] = {
    RADIOLIB_LR2021_DIO5, RADIOLIB_LR2021_DIO6,
    RADIOLIB_LR2021_DIO7, RADIOLIB_LR2021_DIO8,
    RADIOLIB_NC
};

static const Module::RfSwitchMode_t rfswitch_table_ELRS[] = {
    // mode                  DIO5  DIO6  DIO7  DIO8
    { LR2021::MODE_STBY,   { LOW,  LOW,  LOW,  LOW  } },
    { LR2021::MODE_RX,     { LOW,  LOW,  LOW,  HIGH } },
    { LR2021::MODE_TX,     { LOW,  LOW,  HIGH, LOW  } },
    { LR2021::MODE_RX_HF,  { LOW,  HIGH, LOW,  LOW  } },
    { LR2021::MODE_TX_HF,  { HIGH, LOW,  LOW,  LOW  } },
    LR2021::MODE_END_OF_TABLE,
};

static const uint32_t rfswitch_dio_pins_seeed_x1[] = {
    RADIOLIB_NC, RADIOLIB_NC,
    RADIOLIB_NC, RADIOLIB_NC,
    RADIOLIB_NC
};

static const Module::RfSwitchMode_t rfswitch_table_seeed_x1[] = {
    // mode
    { LR2021::MODE_STBY,   { } },
    { LR2021::MODE_RX,     { } },
    { LR2021::MODE_TX,     { } },
    { LR2021::MODE_RX_HF,  { } },
    { LR2021::MODE_TX_HF,  { } },
    LR2021::MODE_END_OF_TABLE,
};

// this function is called when a complete packet
// is received by the module
// IMPORTANT: this function MUST be 'void' type
//            and MUST NOT have any arguments!
#if defined(ESP8266) || defined(ESP32)
  ICACHE_RAM_ATTR
#endif
void lr20xx_receive_handler(void) {
  lr20xx_receive_complete = true;
  lr20xx_receive_cb_count++;
}

static void lr2021_GetVersion (uint8_t* major, uint8_t* minor) {
  uint8_t buf[2] = { 0 };

  hal_pin_busy_wait();
  hal_spi_select(1);

  hal_spi((uint8_t)((RADIOLIB_LR2021_CMD_GET_VERSION & 0xFF00) >> 8));
  hal_spi((uint8_t) (RADIOLIB_LR2021_CMD_GET_VERSION & 0x00FF));
  hal_spi_select(0);

  hal_pin_busy_wait();
  hal_spi_select(1);

  hal_spi(RADIOLIB_LR2021_CMD_NOP);
  hal_spi(RADIOLIB_LR2021_CMD_NOP);
  for (uint8_t i = 0; i < sizeof(buf); i++) {
      buf[i] = hal_spi(0x00);
  }
  hal_spi_select(0);

  if (major)  { *major  = buf[0]; }
  if (minor)  { *minor  = buf[1]; }
#if 0
  Serial.print("major  = "); Serial.println(*major, HEX);
  Serial.print("minor  = "); Serial.println(*minor, HEX);
#endif
}

static bool lr2021_probe()
{
  u1_t major, major_reset, minor;

  SoC->SPI_begin();

  lmic_hal_init (nullptr);

  // manually reset radio
  hal_pin_rst(0); // drive RST pin low
  hal_waitUntil(os_getTime()+ms2osticks(1)); // wait >100us

  lr2021_GetVersion(&major_reset, &minor);

  hal_pin_rst(2); // configure RST pin floating!
  hal_waitUntil(os_getTime()+ms2osticks(300)); // wait 300 ms

  lr2021_GetVersion(&major, &minor);

  pinMode(lmic_pins.nss, INPUT);
  RadioSPI.end();

  if ((major == 0x01 && minor >= 0x18) || /* LR2021:    0x01 0x18 */
      (major == 0x02 && minor == 0x00)) { /* LR2012/22: 0x02 0x00 */

    if (major_reset == 0x01 || major_reset == 0x02) {
      RF_SX12XX_RST_is_connected = false;
    }
#if 0
    char buf[8];
    snprintf(buf, sizeof(buf), "%d.%d", major, minor);
    Serial.print("INFO: LR2021 base FW version ");
    Serial.println(buf);
#endif
    return true;
  } else {
    return false;
  }
}

static void lr20xx_channel(int8_t channel)
{
  if (channel != -1 && channel != lr20xx_channel_prev) {
    uint32_t frequency = RF_FreqPlan.getChanFrequency((uint8_t) channel);
    int8_t fc = settings->freq_corr;

    if (settings->rf_protocol == RF_PROTOCOL_LEGACY) {
      nRF905_band_t nrf_band;
      uint32_t nrf_freq_resolution;

      nrf_band = (frequency >= 844800000UL ? NRF905_BAND_868 : NRF905_BAND_433);
      nrf_freq_resolution = (nrf_band == NRF905_BAND_433 ? 100000UL : 200000UL);
      frequency -= (frequency % nrf_freq_resolution);
    }

    if (fc > 30) {
      fc = 30;
    } else if (fc < -30) {
      fc = -30;
    };

    int rl_state = radio_g4->setFrequency((frequency + (fc * 1000)) / 1000000.0);

#if RADIOLIB_DEBUG_BASIC
    if (rl_state == RADIOLIB_ERR_INVALID_FREQUENCY) {
      Serial.println(F("[LR20XX] Selected frequency is invalid for this module!"));
      while (true) { delay(10); }
    }
#endif

    lr20xx_channel_prev = channel;
    /* restart Rx upon a channel switch */
    lr20xx_receive_active = false;
  }
}

#if defined(RASPBERRY_PI) || defined(LUCKFOX_LYRA)
PiHal *RadioLib_HAL = NULL;
#endif // RASPBERRY_PI

static void lr20xx_setup()
{
  int rl_state;

  SoC->SPI_begin();

  uint32_t irq  = lmic_pins.dio[0] == LMIC_UNUSED_PIN ?
                  RADIOLIB_NC : lmic_pins.dio[0];
  uint32_t busy = lmic_pins.busy == LMIC_UNUSED_PIN ?
                  RADIOLIB_NC : lmic_pins.busy;

#if defined(RASPBERRY_PI) || defined(LUCKFOX_LYRA)

  // deinit LGPIO resources for PiHal to re-acquire them
  lgpio_fini();

#if defined(USE_SPI1)
  RadioLib_HAL = new PiHal(0, 2000000, 1); // use SPI bus #1, channel 0
#else
  RadioLib_HAL = new PiHal(0);             // use SPI bus #0, channel 0
#endif /* USE_SPI1 */

  mod   = new Module(RadioLib_HAL, lmic_pins.nss, irq, lmic_pins.rst, busy);
#else
  mod   = new Module(lmic_pins.nss, irq, lmic_pins.rst, busy, RadioSPI);
#endif // RASPBERRY_PI

  switch (rf_chip->type)
  {
  case RF_IC_LR2021:
  default:
    radio_g4 = new LR2021(mod);
    break;
  }

  switch (settings->rf_protocol)
  {
#if !defined(EXCLUDE_OGNTP)
  case RF_PROTOCOL_OGNTP:
    rl_protocol     = &ogntp_proto_desc;
    protocol_encode = &ogntp_encode;
    protocol_decode = &ogntp_decode;
    break;
#endif /* EXCLUDE_OGNTP */
#if !defined(EXCLUDE_P3I)
  case RF_PROTOCOL_P3I:
    rl_protocol     = &p3i_proto_desc;
    protocol_encode = &p3i_encode;
    protocol_decode = &p3i_decode;
    break;
#endif /* EXCLUDE_P3I */
#if !defined(EXCLUDE_FANET)
  case RF_PROTOCOL_FANET:
    rl_protocol     = &fanet_proto_desc;
    protocol_encode = &fanet_encode;
    protocol_decode = &fanet_decode;
    break;
#endif /* EXCLUDE_FANET */
#if !defined(EXCLUDE_ES1090)
  case RF_PROTOCOL_ADSB_1090:
    rl_protocol     = &es1090_proto_desc;
    protocol_encode = NULL;
    protocol_decode = NULL;

    mode_s_init(&rl_mode_s_state);
    break;
#endif /* EXCLUDE_ES1090 */
#if !defined(EXCLUDE_UAT978)
  case RF_PROTOCOL_ADSB_UAT:
    rl_protocol     = &uat978_proto_desc;
    protocol_encode = &uat978_encode;
    protocol_decode = &uat978_decode;

    init_fec();
    break;
#endif /* EXCLUDE_UAT978 */
#if defined(ENABLE_PROL)
  case RF_PROTOCOL_APRS:
    rl_protocol     = &prol_proto_desc;
    protocol_encode = &aprs_encode;
    protocol_decode = &aprs_decode;
    break;
#endif /* ENABLE_PROL */
#if defined(ENABLE_ADSL)
  case RF_PROTOCOL_ADSL_860:
    rl_protocol     = &adsl_proto_desc;
    protocol_encode = &adsl_encode;
    protocol_decode = &adsl_decode;
    break;
#endif /* ENABLE_ADSL */
  case RF_PROTOCOL_LEGACY:
  default:
    rl_protocol     = &legacy_proto_desc;
    protocol_encode = &legacy_encode;
    protocol_decode = &legacy_decode;
    /*
     * Enforce legacy protocol setting for LR20XX
     * if other value (UAT) left in EEPROM from other (UATM) radio
     */
    settings->rf_protocol = RF_PROTOCOL_LEGACY;
    break;
  }

  RF_FreqPlan.setPlan(settings->band, settings->rf_protocol);

  float Vtcxo;
  uint64_t eui_le = __builtin_bswap64(lr20xx_eui_be);

  switch (hw_info.model)
  {
  case SOFTRF_MODEL_ACADEMY:
    if (SoC->getChipId() == 0x36D2512E /* WCH */) {
      radio_g4->irqDioNum = 11; /* DIO11 as IRQ */
      Vtcxo = 0.0; /* TCXO with ext. power */
    } else {
      radio_g4->irqDioNum =  8; /* DIO8 as IRQ on WIO-2021 */
      Vtcxo = 0.0; /* XTAL */
    }
    break;
  case SOFTRF_MODEL_CARD_MK3:
    radio_g4->irqDioNum = 8; /* DIO8 as IRQ on Seeed X1 */
    Vtcxo = 1.6;
    break;
  case SOFTRF_MODEL_CONCORDE:
  case SOFTRF_MODEL_PRIME_MK2:
    radio_g4->irqDioNum = 11; /* LR2021 DIO11 as IRQ on T-LR2021 V0.3 */
    Vtcxo = 0.0; /* TCXO with ext. power */
    break;
  case SOFTRF_MODEL_PRIME_MK4:
    radio_g4->irqDioNum = 11; /* LR2021 DIO11 as IRQ */
    Vtcxo = 3.0;
    break;
  case SOFTRF_MODEL_RETRO_MK2:
    radio_g4->irqDioNum =  9; /* DIO9 as IRQ on Ebyte E80-900MBL-02 */
    Vtcxo = 2.2;
    break;
  case SOFTRF_MODEL_NANO_MK2:
    radio_g4->irqDioNum =  9; /* DIO9 as IRQ */
    Vtcxo = 3.3;
    break;
  default:
    radio_g4->irqDioNum = 11; /* LR2021 DIO11 as IRQ */
    Vtcxo = 1.6;
    break;
  }

  uint32_t frequency = RF_FreqPlan.getChanFrequency(0);
  bool high = (frequency >= 1500000000) ; /* above 1.5 GHz */

  float br, fdev, bw;
  switch (rl_protocol->modulation_type)
  {
#if !defined(EXCLUDE_FANET) || defined(ENABLE_PROL)
  case RF_MODULATION_TYPE_LORA:
#if RADIOLIB_DEBUG_BASIC
    Serial.print(F("[LR20XX] Initializing LoRa ... "));
#endif

    rl_state = radio_g4->begin(434.0, 125.0, 9, 7,
                               RADIOLIB_LR2021_LORA_SYNC_WORD_PRIVATE,
                               10, 8, Vtcxo);

#if RADIOLIB_DEBUG_BASIC
    if (rl_state == RADIOLIB_ERR_NONE) {
      Serial.println(F("success!"));
    } else {
      Serial.print(F("failed, code "));
      Serial.println((int16_t) rl_state);
      while (true) { delay(10); }
    }
#endif

    switch (RF_FreqPlan.Bandwidth)
    {
    case RF_RX_BANDWIDTH_SS_62KHZ:
      bw = high ? 203 : 125.0; /* BW_125 */
      break;
    case RF_RX_BANDWIDTH_SS_250KHZ:
      bw = high ? 812 : 500.0; /* BW_500 */
      break;
    case RF_RX_BANDWIDTH_SS_125KHZ:
    default:
      bw = high ? 406 : 250.0; /* BW_250 */
      break;
    }

    rl_state = radio_g4->setBandwidth(bw);

#if RADIOLIB_DEBUG_BASIC
    if (rl_state == RADIOLIB_ERR_INVALID_BANDWIDTH) {
      Serial.println(F("[LR20XX] Selected bandwidth is invalid for this module!"));
      while (true) { delay(10); }
    }
#endif

    switch (rl_protocol->type)
    {
    case RF_PROTOCOL_FANET:
    default:
      rl_state = radio_g4->setSpreadingFactor(7); /* SF_7 */
      rl_state = radio_g4->setCodingRate(5);      /* CR_5 */
      break;
    }

    rl_state = radio_g4->setSyncWord((uint8_t) rl_protocol->syncword[0]);

#if RADIOLIB_DEBUG_BASIC
    if (rl_state == RADIOLIB_ERR_INVALID_SYNC_WORD) {
      Serial.println(F("[LR20XX] Selected sync word is invalid for this module!"));
      while (true) { delay(10); }
    }
#endif

    rl_state = radio_g4->setPreambleLength(8);
    rl_state = radio_g4->explicitHeader();
    rl_state = radio_g4->setCRC(true);
    break;
#endif /* EXCLUDE_FANET */

#if !defined(EXCLUDE_ES1090)
  case RF_MODULATION_TYPE_PPM:
#if RADIOLIB_DEBUG_BASIC
    Serial.print(F("[LR20XX] Initializing OOK ... "));
#endif

    rl_state = radio_g4->beginOOK(434.0, 4.8, 153.8, 10, 16, Vtcxo);

#if RADIOLIB_DEBUG_BASIC
    if (rl_state == RADIOLIB_ERR_NONE) {
      Serial.println(F("success!"));
    } else {
      Serial.print(F("failed, code "));
      Serial.println((int16_t) rl_state);
      while (true) { delay(10); }
    }
#endif

    switch (rl_protocol->bitrate)
    {
    case RF_BITRATE_2000KBPS:
    default:
      br = 2000.0;
      break;
    }
    rl_state = radio_g4->setBitRate(br);

#if RADIOLIB_DEBUG_BASIC
  if (rl_state == RADIOLIB_ERR_INVALID_BIT_RATE) {
    Serial.println(F("[LR20XX] Selected bit rate is invalid for this module!"));
    while (true) { delay(10); }
  } else if (rl_state == RADIOLIB_ERR_INVALID_BIT_RATE_BW_RATIO) {
    Serial.println(F("[LR20XX] Selected bit rate to bandwidth ratio is invalid!"));
    Serial.println(F("[LR20XX] Increase receiver bandwidth to set this bit rate."));
    while (true) { delay(10); }
  }
#endif

    switch (rl_protocol->bandwidth)
    {
    case RF_RX_BANDWIDTH_SS_1567KHZ:
    default:
      bw = 3076.0;
      break;
    }

    rl_state = radio_g4->setRxBandwidth(bw);
    if (rl_protocol->preamble_size > 0) {
      rl_state = radio_g4->setPreambleLength(rl_protocol->preamble_size * 8);
    }
    rl_state = radio_g4->setDataShaping(RADIOLIB_SHAPING_NONE);

    switch (rl_protocol->crc_type)
    {
    case RF_CHECKSUM_TYPE_CRC_MODES:
    default:
      /* CRC is driven by software */
      rl_state = radio_g4->setCRC(0, 0);
//      rl_state = radio_g4->setCRC(3, 0, 0x1FFF409UL, false);
      break;
    }

    {
      size_t pkt_size = rl_protocol->payload_offset +
                        rl_protocol->payload_size   +
                        rl_protocol->crc_size;

#if OPT_DF17 == 0
      switch (rl_protocol->whitening)
      {
      case RF_WHITENING_MANCHESTER:
        {
          uint8_t enc = rl_protocol->payload_type == RF_PAYLOAD_INVERTED ?
                        RADIOLIB_ENCODING_MANCHESTER_INV :
                        RADIOLIB_ENCODING_MANCHESTER;
          rl_state = radio_g4->setEncoding(enc);
        }
        break;
      default:
        rl_state = radio_g4->setEncoding(RADIOLIB_ENCODING_NRZ);
        break;
      }
#endif /* OPT_DF17 == 0 */

#if OPT_DF17 == 1 || OPT_DF17 == 2
      pkt_size += pkt_size;
      pkt_size -= 1;

      rl_state = radio_g4->setEncoding(RADIOLIB_ENCODING_NRZ);
#endif /* OPT_DF17 == 1 | 2 */

      /* whitening is driven by software */
//      rl_state = radio_g4->setWhitening(false);
      rl_state = radio_g4->fixedPacketLengthMode(pkt_size);
    }

#if OPT_DF17 == 0
    rl_state = radio_g4->setSyncWord((uint8_t *) rl_protocol->syncword,
                                     (size_t)    rl_protocol->syncword_size);
    rl_state = radio_g4->ookDetector(0x0285, 16, 0, false, false, 0);
    rl_state = radio_g4->setGain(13);
#endif /* OPT_DF17 == 0 */

#if OPT_DF17 == 1
    {
      uint8_t df17_sync_word[1] = { 0x95 };
      rl_state = radio_g4->setSyncWord(df17_sync_word, sizeof(df17_sync_word));
      rl_state = radio_g4->ookDetector(0x0285, 16, 0, false, false, 0);
      rl_state = radio_g4->setGain(0);
    }
#endif /* OPT_DF17 == 1 */

#if OPT_DF17 == 2
    rl_state = radio_g4->setSyncWord((uint8_t *) rl_protocol->syncword,
                                     (size_t)    rl_protocol->syncword_size);
    rl_state = radio_g4->ookDetector(0xa902, 16, 0, false, false, 0);
    rl_state = radio_g4->setGain(0);
#endif /* OPT_DF17 == 2 */

    rl_state = radio_g4->setOokDetectionThreshold(-80); /* TODO */
    break;
#endif /* EXCLUDE_ES1090 */

  case RF_MODULATION_TYPE_2FSK:
  default:
#if RADIOLIB_DEBUG_BASIC
    Serial.print(F("[LR20XX] Initializing GFSK ... "));
#endif

    rl_state = radio_g4->beginGFSK(434.0, 4.8, 5.0, 153.8, 10, 16, Vtcxo);

#if RADIOLIB_DEBUG_BASIC
    if (rl_state == RADIOLIB_ERR_NONE) {
      Serial.println(F("success!"));
    } else {
      Serial.print(F("failed, code "));
      Serial.println((int16_t) rl_state);
      while (true) { delay(10); }
    }
#endif

    switch (rl_protocol->bitrate)
    {
    case RF_BITRATE_38400:
      br = high ? 125.0 :  38.4; /* SX128x minimum is 125 kbps */
      break;
    case RF_BITRATE_1042KBPS:
      br = 1041.667;
      break;
    case RF_BITRATE_100KBPS:
    default:
      br = high ? 125.0 : 100.0; /* SX128x minimum is 125 kbps */
      break;
    }
    rl_state = radio_g4->setBitRate(br);

#if RADIOLIB_DEBUG_BASIC
  if (rl_state == RADIOLIB_ERR_INVALID_BIT_RATE) {
    Serial.println(F("[LR20XX] Selected bit rate is invalid for this module!"));
    while (true) { delay(10); }
  } else if (rl_state == RADIOLIB_ERR_INVALID_BIT_RATE_BW_RATIO) {
    Serial.println(F("[LR20XX] Selected bit rate to bandwidth ratio is invalid!"));
    Serial.println(F("[LR20XX] Increase receiver bandwidth to set this bit rate."));
    while (true) { delay(10); }
  }
#endif

    switch (rl_protocol->deviation)
    {
    case RF_FREQUENCY_DEVIATION_10KHZ:
      fdev = high ? 62.5 : 10.0; /* SX128x minimum is 62.5 kHz */
      break;
    case RF_FREQUENCY_DEVIATION_19_2KHZ:
      fdev = 19.2;
      break;
    case RF_FREQUENCY_DEVIATION_25KHZ:
      fdev = 25.0;
      break;
    case RF_FREQUENCY_DEVIATION_625KHZ:
#if RADIOLIB_CHECK_PARAMS == 1
      fdev = 500.0; /* FDEV = 500.0 kHz is a specified maximum for LR2021 */
#else
      fdev = 625.0;
#endif
      break;
    case RF_FREQUENCY_DEVIATION_50KHZ:
    case RF_FREQUENCY_DEVIATION_NONE:
    default:
      fdev = high ? 62.5 : 50.0; /* SX128x minimum is 62.5 kHz */
      break;
    }
    rl_state = radio_g4->setFrequencyDeviation(fdev);

#if RADIOLIB_DEBUG_BASIC
  if (rl_state == RADIOLIB_ERR_INVALID_FREQUENCY_DEVIATION) {
    Serial.println(F("[LR20XX] Selected frequency deviation is invalid for this module!"));
    while (true) { delay(10); }
  }
#endif

    switch (rl_protocol->bandwidth)
    {
    case RF_RX_BANDWIDTH_SS_50KHZ:
      bw = 119.0;
      break;
    case RF_RX_BANDWIDTH_SS_62KHZ:
      bw = 153.8;
      break;
    case RF_RX_BANDWIDTH_SS_100KHZ:
      bw = 238.1;
      break;
    case RF_RX_BANDWIDTH_SS_166KHZ:
      bw = 370.4;
      break;
    case RF_RX_BANDWIDTH_SS_200KHZ:
      bw = 476.2;
      break;
    case RF_RX_BANDWIDTH_SS_250KHZ:
      bw = 555.6;
      break;
    case RF_RX_BANDWIDTH_SS_1567KHZ:
      bw = 3076.0;
      break;
    case RF_RX_BANDWIDTH_SS_125KHZ:
    default:
      bw = 307.7;
      break;
    }

    rl_state = radio_g4->setRxBandwidth(bw);
    rl_state = radio_g4->setPreambleLength(rl_protocol->preamble_size * 8);
    rl_state = radio_g4->setDataShaping(RADIOLIB_SHAPING_0_5);

    switch (rl_protocol->crc_type)
    {
    case RF_CHECKSUM_TYPE_CCITT_FFFF:
    case RF_CHECKSUM_TYPE_CCITT_0000:
    case RF_CHECKSUM_TYPE_CCITT_1D02:
    case RF_CHECKSUM_TYPE_CRC8_107:
    case RF_CHECKSUM_TYPE_RS:
      /* CRC is driven by software */
      rl_state = radio_g4->setCRC(0, 0);
      break;
    case RF_CHECKSUM_TYPE_GALLAGER:
    case RF_CHECKSUM_TYPE_CRC_MODES:
    case RF_CHECKSUM_TYPE_NONE:
    default:
      rl_state = radio_g4->setCRC(0, 0);
      break;
    }

    size_t pkt_size = rl_protocol->payload_offset + rl_protocol->payload_size +
                      rl_protocol->crc_size;

    switch (rl_protocol->whitening)
    {
    case RF_WHITENING_MANCHESTER:
      pkt_size += pkt_size;
      break;
    case RF_WHITENING_PN9:
    case RF_WHITENING_NONE:
    case RF_WHITENING_NICERF:
    default:
      break;
    }

    rl_state = radio_g4->setWhitening(false, 0x0001 /* default SX128x value */);
    rl_state = radio_g4->disableAddressFiltering();

    /* Work around premature P3I syncword detection */
    if (rl_protocol->syncword_size == 2) {
      uint8_t preamble = rl_protocol->preamble_type == RF_PREAMBLE_TYPE_AA ?
                         0xAA : 0x55;
      uint8_t sword[4] = { preamble,
                           preamble,
                           rl_protocol->syncword[0],
                           rl_protocol->syncword[1]
                         };
      rl_state = radio_g4->setSyncWord(sword, 4);
    } else {
      rl_state = radio_g4->setSyncWord((uint8_t *) rl_protocol->syncword,
                                       (size_t)    rl_protocol->syncword_size);
    }

    rl_state = radio_g4->fixedPacketLengthMode(pkt_size);
    break;
  }

  if (high) {
    rl_state = radio_g4->setFrequency(frequency / 1000000.0);

#if RADIOLIB_DEBUG_BASIC
    if (rl_state == RADIOLIB_ERR_INVALID_FREQUENCY) {
      Serial.println(F("[LR20XX] Selected frequency is invalid for this module!"));
      while (true) { delay(10); }
    }
#endif
  }

#if defined(USE_FEM)
  bool has_fem = (hw_info.model == SOFTRF_MODEL_PRIME_MK4) ? true : false;
#endif /* USE_FEM */

  float txpow = 2;

  switch(settings->txpower)
  {
  case RF_TX_POWER_FULL:

    if (settings->rf_protocol != RF_PROTOCOL_ADSB_1090 &&
        settings->rf_protocol != RF_PROTOCOL_ADSB_UAT) {
      /* Load regional max. EIRP at first */
      txpow = RF_FreqPlan.MaxTxPower;
    }

#if defined(USE_FEM)
    if (has_fem == true) {
      if (txpow > 33)
        txpow = 33;
    } else
#endif /* USE_FEM */
    {
      if (txpow > 22) txpow = 22;

#if 1
      /*
       * Enforce Tx power limit until confirmation
       * that LR20xx is doing well
       * when antenna is not connected
       */
      if (txpow > 17)
        txpow = 17;
#endif

      if (high && txpow > 13) txpow = 13;
    }

    break;
  case RF_TX_POWER_OFF:
  case RF_TX_POWER_LOW:
  default:
    break;
  }

#if defined(USE_FEM)
  if (hw_info.model == SOFTRF_MODEL_PRIME_MK4) {
    if (high) {
      txpow -= 34; /* CB5337CX */
      if (txpow > 8) txpow = 8;
    } else {
      txpow -= 12; /* HM06S006P */
    }
  }
#endif /* USE_FEM */

  switch (hw_info.model)
  {
  case SOFTRF_MODEL_CARD_MK3:
    radio_g4->setRfSwitchTable(rfswitch_dio_pins_seeed_x1,
                               rfswitch_table_seeed_x1);
    break;

  case SOFTRF_MODEL_ACADEMY:
    if (SoC->getChipId() == 0x21A44298 /* 25007 */||
        SoC->getChipId() == 0xFCE0D9E0 /* 25007 */||
        SoC->getChipId() == 0x36D2512E /* WCH */) {
      radio_g4->setRfSwitchTable(rfswitch_dio_pins_MXD8721_V02,
                                 rfswitch_table_MXD8721_V02);
    } else {
      // Wio-LR202x Module @ 868/915M - Switchless design
      // radio_g4->setRfSwitchTable(rfswitch_dio_pins_seeed_wio,
      //                            rfswitch_table_seeed_wio);
    }
    break;

  case SOFTRF_MODEL_PRIME_MK4:
    radio_g4->setRfSwitchTable(rfswitch_dio_pins_XY16E3AXP33,
                               rfswitch_table_XY16E3AXP33);
    break;

  case SOFTRF_MODEL_RETRO_MK2:
    /* TODO: Switchless design ? */
    break;

  case SOFTRF_MODEL_NANO_MK2:
    radio_g4->setRfSwitchTable(rfswitch_dio_pins_ELRS,
                               rfswitch_table_ELRS);
    break;

  case SOFTRF_MODEL_BADGE:
  case SOFTRF_MODEL_PRIME_MK2:
  case SOFTRF_MODEL_PRIME_MK3:
  case SOFTRF_MODEL_CONCORDE:
    radio_g4->setRfSwitchTable(rfswitch_dio_pins_MXD8721_V03,
                               rfswitch_table_MXD8721_V03);
    break;

  default:
    radio_g4->setRfSwitchTable(rfswitch_dio_pins_MXD8721_V02,
                               rfswitch_table_MXD8721_V02);
    break;
  }
  rl_state = radio_g4->setOutputPower(txpow);

  rl_state = radio_g4->setRxBoostedGainMode(high ? RADIOLIB_LR2021_RX_BOOST_HF :
                                                   RADIOLIB_LR2021_RX_BOOST_LF);
  radio_g4->setPacketReceivedAction(lr20xx_receive_handler);
}

#define ES1090_MONITOR_INTERVAL 30000

static unsigned long lr20xx_rx_monitor_marker = 0;
static unsigned long lr20xx_last_rx_marker    = 0;

static bool lr20xx_receive()
{
  bool success = false;
  int rl_state;

  if (settings->power_save & POWER_SAVE_NORECEIVE) {
    return success;
  }

  if (rl_protocol->type     == RF_PROTOCOL_ADSB_1090 &&
      lr20xx_receive_active == true                  &&
      millis() - lr20xx_rx_monitor_marker > ES1090_MONITOR_INTERVAL) {
    if (millis() - lr20xx_last_rx_marker > (ES1090_MONITOR_INTERVAL / 2)) {
      rl_state = radio_g4->finishReceive();
      lr20xx_receive_active = false;
    }
    lr20xx_rx_monitor_marker = millis();
  }

  if (!lr20xx_receive_active) {

    rl_state = radio_g4->startReceive();
    if (rl_state == RADIOLIB_ERR_NONE) {
      lr20xx_receive_active = true;
    }
  }

#if defined(plat_radio_irq_func)
  if (mod->getIrq() == RADIOLIB_NC) {
   if (plat_radio_irq_func(mod->getIrq())) {
     lr20xx_receive_handler();
   }
  }
#endif /* plat_radio_irq_func */

  if (lr20xx_receive_complete == true) {

    lr20xx_receive_complete = false;

//    Serial.print("cb_cnt = "); Serial.println(lr20xx_receive_cb_count);
    lr20xx_receive_cb_count = 0;

    RL_rxPacket.len = radio_g4->getPacketLength();

    if (RL_rxPacket.len > 0) {

      if (RL_rxPacket.len > sizeof(RL_rxPacket.payload)) {
        RL_rxPacket.len = sizeof(RL_rxPacket.payload);
      }

      rl_state = radio_g4->readData(RL_rxPacket.payload, RL_rxPacket.len);
//      lr20xx_receive_active = false;

      if (rl_state == RADIOLIB_ERR_NONE &&
         !memeqzero(RL_rxPacket.payload, RL_rxPacket.len)) {
        size_t size = 0;
        uint8_t offset;

        u1_t crc8, pkt_crc8;
        u2_t crc16, pkt_crc16;

        lr20xx_last_rx_marker = millis();

        RadioLib_DataPacket *RL_rxPacket_ptr = &RL_rxPacket;

        switch (rl_protocol->crc_type)
        {
        case RF_CHECKSUM_TYPE_GALLAGER:
        case RF_CHECKSUM_TYPE_CRC_MODES:
        case RF_CHECKSUM_TYPE_NONE:
           /* crc16 left not initialized */
          break;
        case RF_CHECKSUM_TYPE_CRC8_107:
          crc8 = 0x71;     /* seed value */
          break;
        case RF_CHECKSUM_TYPE_CCITT_0000:
          crc16 = 0x0000;  /* seed value */
          break;
        case RF_CHECKSUM_TYPE_CCITT_FFFF:
        default:
          crc16 = 0xffff;  /* seed value */
          break;
        }

        switch (rl_protocol->type)
        {
        case RF_PROTOCOL_LEGACY:
          /* take in account NRF905/FLARM "address" bytes */
          crc16 = update_crc_ccitt(crc16, 0x31);
          crc16 = update_crc_ccitt(crc16, 0xFA);
          crc16 = update_crc_ccitt(crc16, 0xB6);
          break;
        case RF_PROTOCOL_P3I:
        case RF_PROTOCOL_OGNTP:
        case RF_PROTOCOL_ADSL_860:
        default:
          break;
        }

        uint8_t i;

        switch (rl_protocol->type)
        {
        case RF_PROTOCOL_P3I:
          offset = rl_protocol->payload_offset;
          for (i = 0; i < rl_protocol->payload_size; i++)
          {
            update_crc8(&crc8, (u1_t)(RL_rxPacket_ptr->payload[i + offset]));
            if (i < sizeof(RxBuffer)) {
              RxBuffer[i] = RL_rxPacket_ptr->payload[i + offset] ^
                            pgm_read_byte(&whitening_pattern[i]);
            }
          }

          pkt_crc8 = RL_rxPacket_ptr->payload[i + offset];

          if (crc8 == pkt_crc8) {
            success = true;
          }
          break;

        case RF_PROTOCOL_FANET:
          offset = rl_protocol->payload_offset;
          size   = rl_protocol->payload_size + rl_protocol->crc_size;
          for (i = 0; i < size; i++)
          {
            if (i < sizeof(RxBuffer)) {
              RxBuffer[i] = RL_rxPacket_ptr->payload[i + offset];
            }
          }
          success = true;
          break;

#if !defined(EXCLUDE_ES1090)
        case RF_PROTOCOL_ADSB_1090:
        {
          struct mode_s_msg mm;

#if OPT_DF17 == 0
          mode_s_decode(&rl_mode_s_state, &mm, RL_rxPacket_ptr->payload);
#endif /* OPT_DF17 == 0 */

#if OPT_DF17 == 1 || OPT_DF17 == 2
          uint8_t raw[28] = { 0 };
          uint8_t buf[14] = { 0 };

          raw[0] = 0x95;
          memcpy(raw + 1, RL_rxPacket_ptr->payload, 27);

          uint8_t val1, val2;
          for (int i = 0; i < sizeof(raw); i++) {
            val1 = pgm_read_byte(&ManchesterDecode[raw[i]]);
            i++;
            val2 = pgm_read_byte(&ManchesterDecode[raw[i]]);
            if ((i>>1) < sizeof(buf)) {
              buf[i>>1] = ((~val1 & 0x0F) << 4) | (~val2 & 0x0F);
            }
          }

          mode_s_decode(&rl_mode_s_state, &mm, buf);
#endif /* OPT_DF17 == 1 | 2 */

          if (rl_mode_s_state.check_crc == 0 || mm.crcok) {
#if 0
            Serial.printf("%02d %03d %02x%02x%02x RSSI=%d\r\n",
                          mm.msgtype, mm.msgbits, mm.aa1, mm.aa2, mm.aa3,
                          (int) radio_g4->getRSSI(true));
#endif
            if (mm.msgtype == 17 &&
                ((mm.metype >= 1 && mm.metype <= 4)  ||
                 (mm.metype >= 9 && mm.metype <= 18) ||
                 (mm.metype == 19)) ) {
              size = mm.msgbits >> 3;

              if (size > sizeof(RxBuffer)) {
                size = sizeof(RxBuffer);
              }

              if (size > 0) {
#if OPT_DF17 == 0
                memcpy(RxBuffer, RL_rxPacket_ptr->payload, size);
#endif /* OPT_DF17 == 0 */
#if OPT_DF17 == 1 || OPT_DF17 == 2
                memcpy(RxBuffer, buf, size);
#endif /* OPT_DF17 == 1 | 2 */

                success = true;
              }

              int acfts_in_sight = 0;
              struct mode_s_aircraft *a = rl_mode_s_state.aircrafts;

              while (a) {
                acfts_in_sight++;
                a = a->next;
              }

#if 0
              Serial.print("acfts_in_sight "); Serial.println(acfts_in_sight);
#endif

              if (acfts_in_sight < (4 * MAX_TRACKING_OBJECTS)) {
                interactiveReceiveData(&rl_mode_s_state, &mm);
              }
            }
          }
          break;
        }
#endif /* EXCLUDE_ES1090 */

#if !defined(EXCLUDE_UAT978)
        case RF_PROTOCOL_ADSB_UAT:
          int rs_errors;
          int frame_type;
          frame_type = correct_adsb_frame(RL_rxPacket_ptr->payload, &rs_errors);

          if (frame_type != -1) {

            if (frame_type == 1) {
              size = SHORT_FRAME_DATA_BYTES;
            } else if (frame_type == 2) {
              size = LONG_FRAME_DATA_BYTES;
            }

            if (size > sizeof(RxBuffer)) {
              size = sizeof(RxBuffer);
            }

            if (size > 0) {
              memcpy(RxBuffer, RL_rxPacket_ptr->payload, size);

              success = true;
            }
          }
          break;
#endif /* EXCLUDE_UAT978 */

        case RF_PROTOCOL_OGNTP:
        case RF_PROTOCOL_ADSL_860:
        case RF_PROTOCOL_LEGACY:
        default:
          offset = 0;
          size   = rl_protocol->payload_offset +
                   rl_protocol->payload_size +
                   rl_protocol->payload_size +
                   rl_protocol->crc_size +
                   rl_protocol->crc_size;
          if (RL_rxPacket_ptr->len >= (size + offset)) {
            uint8_t val1, val2;
            for (i = 0; i < size; i++) {
              val1 = pgm_read_byte(&ManchesterDecode[RL_rxPacket_ptr->payload[i + offset]]);
              i++;
              val2 = pgm_read_byte(&ManchesterDecode[RL_rxPacket_ptr->payload[i + offset]]);
              if ((i>>1) < sizeof(RxBuffer)) {
                RxBuffer[i>>1] = ((val1 & 0x0F) << 4) | (val2 & 0x0F);

                if (i < size - (rl_protocol->crc_size + rl_protocol->crc_size)) {
                  switch (rl_protocol->crc_type)
                  {
                  case RF_CHECKSUM_TYPE_GALLAGER:
                  case RF_CHECKSUM_TYPE_CRC_MODES:
                  case RF_CHECKSUM_TYPE_NONE:
                    break;
                  case RF_CHECKSUM_TYPE_CCITT_FFFF:
                  case RF_CHECKSUM_TYPE_CCITT_0000:
                  default:
                    crc16 = update_crc_ccitt(crc16, (u1_t)(RxBuffer[i>>1]));
                    break;
                  }
                }
              }
            }

            size = size>>1;

            switch (rl_protocol->crc_type)
            {
            case RF_CHECKSUM_TYPE_GALLAGER:
#if !defined(EXCLUDE_OGNTP)
              if (LDPC_Check((uint8_t  *) &RxBuffer[0]) == 0) {
                success = true;
              }
#endif /* EXCLUDE_OGNTP */
              break;
            case RF_CHECKSUM_TYPE_CRC_MODES:
#if defined(ENABLE_ADSL)
              if (ADSL_Packet::checkPI((uint8_t  *) &RxBuffer[0], size) == 0) {
                success = true;
              }
#endif /* ENABLE_ADSL */
              break;
            case RF_CHECKSUM_TYPE_CCITT_FFFF:
            case RF_CHECKSUM_TYPE_CCITT_0000:
              offset = rl_protocol->payload_offset + rl_protocol->payload_size;
              if (offset + 1 < sizeof(RxBuffer)) {
                pkt_crc16 = (RxBuffer[offset] << 8 | RxBuffer[offset+1]);
                if (crc16 == pkt_crc16) {

                  success = true;
                }
              }
              break;
            default:
              break;
            }
          }
          break;
        }

        if (success) {
          RF_last_rssi = radio_g4->getRSSI();
          rx_packets_counter++;
        }
      }

      memset(RL_rxPacket.payload, 0, sizeof(RL_rxPacket.payload));

      RL_rxPacket.len = 0;
    }

//    lr20xx_receive_complete = false;
  }

  return success;
}

static bool lr20xx_transmit()
{
  u1_t crc8;
  u2_t crc16;
  u1_t i;

  bool success = false;

  if (RF_tx_size <= 0) {
    return success;
  }

  if (rl_protocol->type == RF_PROTOCOL_ADSB_1090 ||
      rl_protocol->type == RF_PROTOCOL_ADSB_UAT) {
    return false; /* no transmit on 1090 or 978 MHz */
  }

  lr20xx_receive_active = false;
  lr20xx_transmit_complete = false;

  size_t PayloadLen = 0;

  switch (rl_protocol->crc_type)
  {
  case RF_CHECKSUM_TYPE_GALLAGER:
  case RF_CHECKSUM_TYPE_CRC_MODES:
  case RF_CHECKSUM_TYPE_NONE:
     /* crc16 left not initialized */
    break;
  case RF_CHECKSUM_TYPE_CRC8_107:
    crc8 = 0x71;     /* seed value */
    break;
  case RF_CHECKSUM_TYPE_CCITT_0000:
    crc16 = 0x0000;  /* seed value */
    break;
  case RF_CHECKSUM_TYPE_CCITT_FFFF:
  default:
    crc16 = 0xffff;  /* seed value */
    break;
  }

  switch (rl_protocol->type)
  {
  case RF_PROTOCOL_LEGACY:
    /* take in account NRF905/FLARM "address" bytes */
    crc16 = update_crc_ccitt(crc16, 0x31);
    crc16 = update_crc_ccitt(crc16, 0xFA);
    crc16 = update_crc_ccitt(crc16, 0xB6);
    break;
  case RF_PROTOCOL_P3I:
    /* insert Net ID */
    RL_txPacket.payload[PayloadLen++] = (u1_t) ((rl_protocol->net_id >> 24) & 0x000000FF);
    RL_txPacket.payload[PayloadLen++] = (u1_t) ((rl_protocol->net_id >> 16) & 0x000000FF);
    RL_txPacket.payload[PayloadLen++] = (u1_t) ((rl_protocol->net_id >>  8) & 0x000000FF);
    RL_txPacket.payload[PayloadLen++] = (u1_t) ((rl_protocol->net_id >>  0) & 0x000000FF);
    /* insert byte with payload size */
    RL_txPacket.payload[PayloadLen++] = rl_protocol->payload_size;

    /* insert byte with CRC-8 seed value when necessary */
    if (rl_protocol->crc_type == RF_CHECKSUM_TYPE_CRC8_107) {
      RL_txPacket.payload[PayloadLen++] = crc8;
    }

    break;
  case RF_PROTOCOL_OGNTP:
  case RF_PROTOCOL_ADSL_860:
  default:
    break;
  }

  for (i=0; i < RF_tx_size; i++) {

    switch (rl_protocol->whitening)
    {
    case RF_WHITENING_NICERF:
      RL_txPacket.payload[PayloadLen] = TxBuffer[i] ^ pgm_read_byte(&whitening_pattern[i]);
      break;
    case RF_WHITENING_MANCHESTER:
      RL_txPacket.payload[PayloadLen] = pgm_read_byte(&ManchesterEncode[(TxBuffer[i] >> 4) & 0x0F]);
      PayloadLen++;
      RL_txPacket.payload[PayloadLen] = pgm_read_byte(&ManchesterEncode[(TxBuffer[i]     ) & 0x0F]);
      break;
    case RF_WHITENING_NONE:
    default:
      RL_txPacket.payload[PayloadLen] = TxBuffer[i];
      break;
    }

    switch (rl_protocol->crc_type)
    {
    case RF_CHECKSUM_TYPE_GALLAGER:
    case RF_CHECKSUM_TYPE_CRC_MODES:
    case RF_CHECKSUM_TYPE_NONE:
      break;
    case RF_CHECKSUM_TYPE_CRC8_107:
      update_crc8(&crc8, (u1_t)(RL_txPacket.payload[PayloadLen]));
      break;
    case RF_CHECKSUM_TYPE_CCITT_FFFF:
    case RF_CHECKSUM_TYPE_CCITT_0000:
    default:
      if (rl_protocol->whitening == RF_WHITENING_MANCHESTER) {
        crc16 = update_crc_ccitt(crc16, (u1_t)(TxBuffer[i]));
      } else {
        crc16 = update_crc_ccitt(crc16, (u1_t)(RL_txPacket.payload[PayloadLen]));
      }
      break;
    }

    PayloadLen++;
  }

  switch (rl_protocol->crc_type)
  {
  case RF_CHECKSUM_TYPE_GALLAGER:
  case RF_CHECKSUM_TYPE_CRC_MODES:
  case RF_CHECKSUM_TYPE_NONE:
    break;
  case RF_CHECKSUM_TYPE_CRC8_107:
    RL_txPacket.payload[PayloadLen++] = crc8;
    break;
  case RF_CHECKSUM_TYPE_CCITT_FFFF:
  case RF_CHECKSUM_TYPE_CCITT_0000:
  default:
    if (rl_protocol->whitening == RF_WHITENING_MANCHESTER) {
      RL_txPacket.payload[PayloadLen++] = pgm_read_byte(&ManchesterEncode[(((crc16 >>  8) & 0xFF) >> 4) & 0x0F]);
      RL_txPacket.payload[PayloadLen++] = pgm_read_byte(&ManchesterEncode[(((crc16 >>  8) & 0xFF)     ) & 0x0F]);
      RL_txPacket.payload[PayloadLen++] = pgm_read_byte(&ManchesterEncode[(((crc16      ) & 0xFF) >> 4) & 0x0F]);
      RL_txPacket.payload[PayloadLen++] = pgm_read_byte(&ManchesterEncode[(((crc16      ) & 0xFF)     ) & 0x0F]);
      PayloadLen++;
    } else {
      RL_txPacket.payload[PayloadLen++] = (crc16 >>  8) & 0xFF;
      RL_txPacket.payload[PayloadLen++] = (crc16      ) & 0xFF;
    }
    break;
  }

  RL_txPacket.len = PayloadLen;

  int rl_state;

#if defined(plat_radio_irq_func)
  if (mod->getIrq() == RADIOLIB_NC) {
    RadioLibTime_t timeout = radio_g4->getTimeOnAir(RL_txPacket.len);

    if (rl_protocol->modulation_type == RF_MODULATION_TYPE_LORA) {
      // calculate timeout (150% of expected time-on-air)
      timeout = (timeout * 3) / 2;
    } else {
      // calculate timeout (500% of expected time-on-air)
      timeout = timeout * 5;
    }

    RADIOLIB_DEBUG_BASIC_PRINTLN("Timeout in %lu us", timeout);

    rl_state = radio_g4->startTransmit((uint8_t *) &RL_txPacket.payload, (size_t) RL_txPacket.len);
    RADIOLIB_ASSERT(rl_state);

    RadioLibTime_t start = mod->hal->micros();
    while (!plat_radio_irq_func(mod->getIrq())) {
      mod->hal->yield();
      if (mod->hal->micros() - start > timeout) {
        radio_g4->finishTransmit();
        rl_state = RADIOLIB_ERR_TX_TIMEOUT;
        break;
      }
    }

    if (rl_state != RADIOLIB_ERR_TX_TIMEOUT) {
      rl_state = radio_g4->finishTransmit();
    }
  } else
#endif /* plat_radio_irq_func */
  {
    rl_state = radio_g4->transmit((uint8_t *) &RL_txPacket.payload, (size_t) RL_txPacket.len);
  }

  if (rl_state == RADIOLIB_ERR_NONE) {

    success = true;

    memset(RL_txPacket.payload, 0, sizeof(RL_txPacket.payload));

#if 0
    // the packet was successfully transmitted
    Serial.println(F("success!"));

  } else if (rl_state == RADIOLIB_ERR_PACKET_TOO_LONG) {
    // the supplied packet was longer than 256 bytes
    Serial.println(F("too long!"));

  } else if (rl_state == RADIOLIB_ERR_TX_TIMEOUT) {
    // timeout occured while transmitting packet
    Serial.println(F("timeout!"));

  } else {
    // some other error occurred
    Serial.print(F("failed, code "));
    Serial.println((int16_t) rl_state);
#endif
  }

  return success;
}

static void lr20xx_shutdown()
{
  int rl_state = radio_g4->standby(RADIOLIB_LR2021_STANDBY_RC);
  rl_state = radio_g4->setTCXO(0);
  rl_state = radio_g4->sleep(false, 0);

  RadioSPI.end();
}
#endif /* EXCLUDE_LR20XX */

#endif /* USE_RADIOLIB */
