lyusupov/SoftRF/software/firmware/source/SoftRF/src/platform/ESP32.cpp

/*
 * Platform_ESP32.cpp
 * Copyright (C) 2018-2026 Linar Yusupov
 *
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
 * You should have received a copy of the GNU General Public License
 * along with this program.  If not, see <http://www.gnu.org/licenses/>.
 */
#if defined(ESP32)

#include "sdkconfig.h"

#include <SPI.h>
#include <esp_err.h>
#include <esp_wifi.h>
#if !defined(CONFIG_IDF_TARGET_ESP32S2) && !defined(CONFIG_IDF_TARGET_ESP32P4)
#include <esp_bt.h>
#endif /* CONFIG_IDF_TARGET_ESP32S2 */
#if !defined(CONFIG_IDF_TARGET_ESP32C5)  && \
    !defined(CONFIG_IDF_TARGET_ESP32C6)  && \
    !defined(CONFIG_IDF_TARGET_ESP32C61) && \
    !defined(CONFIG_IDF_TARGET_ESP32H2)  && \
    !defined(CONFIG_IDF_TARGET_ESP32H4)  && \
    !defined(CONFIG_IDF_TARGET_ESP32P4)
#include <soc/rtc_cntl_reg.h>
#endif /* CONFIG_IDF_TARGET_ESP32C5 || C6 || H2 || H4 || P4 */
#include <soc/efuse_reg.h>
#include <Wire.h>
#include <rom/rtc.h>
#include <rom/spi_flash.h>
#include <soc/adc_channel.h>
#include <flashchips.h>
#include <axp20x.h>
#define  XPOWERS_CHIP_AXP2102
#include <XPowersLib.h>
#include <pcf8563.h>

#if defined(ESP_IDF_VERSION_MAJOR) && ESP_IDF_VERSION_MAJOR >= 5
#include <esp_mac.h>
#include <esp_flash.h>
#include <esp_wifi_ap_get_sta_list.h>
#endif /* ESP_IDF_VERSION_MAJOR */

#include "../system/SoC.h"

#if defined(USE_NIMBLE)
#include <NimBLEDevice.h>
#else
#if !defined(CONFIG_IDF_TARGET_ESP32S2) && !defined(CONFIG_IDF_TARGET_ESP32P4)
#include <BLEDevice.h>
#endif /* CONFIG_IDF_TARGET_ESP32S2 */
#endif /* USE_NIMBLE */

#include "../system/Time.h"
#include "../driver/Sound.h"
#include "../driver/EEPROM.h"
#include "../driver/RF.h"
#include "../driver/WiFi.h"
#include "../driver/Bluetooth.h"
#include "../driver/LED.h"
#include "../driver/Baro.h"
#include "../driver/Battery.h"
#include "../driver/OLED.h"
#include "../protocol/data/NMEA.h"
#include "../protocol/data/GDL90.h"
#include "../protocol/data/D1090.h"
#if !defined(EXCLUDE_MAVLINK)
#include "../protocol/data/MAVLink.h"
#endif /* EXCLUDE_MAVLINK */
#if defined(ENABLE_REMOTE_ID)
#include "../protocol/radio/RemoteID.h"
#endif /* ENABLE_REMOTE_ID */

#if defined(USE_TFT)
#include <TFT_eSPI.h>
#endif /* USE_TFT */

#include <battery.h>

// SX12xx pin mapping
lmic_pinmap lmic_pins = {
    .nss  = SOC_GPIO_PIN_SS,
    .txe  = LMIC_UNUSED_PIN,
    .rxe  = LMIC_UNUSED_PIN,
    .rst  = SOC_GPIO_PIN_RST,
    .dio  = {LMIC_UNUSED_PIN, LMIC_UNUSED_PIN, LMIC_UNUSED_PIN},
    .busy = SOC_GPIO_PIN_TXE,
    .tcxo = LMIC_UNUSED_PIN,
};

#if !defined(EXCLUDE_LED_RING)
#if defined(USE_NEOPIXELBUS_LIBRARY)
NeoPixelBus<NeoGrbFeature, Neo800KbpsMethod> strip(PIX_NUM, SOC_GPIO_PIN_LED);
#endif /* USE_NEOPIXELBUS_LIBRARY */
#if defined(USE_ADAFRUIT_NEO_LIBRARY)
Adafruit_NeoPixel *strip;
#endif /* USE_ADAFRUIT_NEO_LIBRARY */
#endif /* EXCLUDE_LED_RING */

// #if defined(USE_OLED)
// U8X8_OLED_I2C_BUS_TYPE                u8x8_ttgo   (TTGO_V2_OLED_PIN_RST);
// U8X8_OLED_I2C_BUS_TYPE                u8x8_heltec (HELTEC_OLED_PIN_RST);
// U8X8_SH1106_128X64_NONAME_HW_I2C      u8x8_1_3    (U8X8_PIN_NONE);
// U8X8_SH1106_128X64_NONAME_2ND_HW_I2C  u8x8_elecrow(U8X8_PIN_NONE);
// U8X8_SSD1306_128X64_NONAME_2ND_HW_I2C u8x8_ebyte  (SOC_GPIO_PIN_EHUB_OLED_RST);
// #endif /* USE_OLED */

#if defined(USE_TFT)
static TFT_eSPI *tft = NULL;

void TFT_off()
{
#ifndef ST7735_DRIVER
    tft->writecommand(TFT_DISPOFF);
    tft->writecommand(TFT_SLPIN);
#else
    tft->writecommand(ST7735_DISPOFF);
    tft->writecommand(ST7735_SLPIN);
#endif /* ST7735_DRIVER */
}

void TFT_backlight_adjust(uint8_t level)
{
    ledcWrite(BACKLIGHT_CHANNEL, level);
}

bool TFT_isBacklightOn()
{
    return (bool)ledcRead(BACKLIGHT_CHANNEL);
}

void TFT_backlight_off()
{
    ledcWrite(BACKLIGHT_CHANNEL, 0);
}

void TFT_backlight_on()
{
    ledcWrite(BACKLIGHT_CHANNEL, 250);
}
#endif /* USE_TFT */

#if defined(USE_EPAPER)
#include "../driver/EPD.h"

GxEPD2_GFX *display = NULL;

#if defined(USE_EPD_TASK)
#define EPD_STACK_SZ      (256*6)
static TaskHandle_t EPD_Task_Handle = NULL;
SemaphoreHandle_t Display_Semaphore;
unsigned long TaskInfoTime;
#endif /* USE_EPD_TASK */

const char *Hardware_Rev[] = {
  [0] = "2024-02-28",
  [1] = "1.0",
  [2] = "N/A",
  [3] = "Unknown"
};

static bool screen_saver = false;
#endif /* USE_EPAPER */

#if defined(CONFIG_IDF_TARGET_ESP32)
AXP20X_Class axp_xxx;
#endif /* CONFIG_IDF_TARGET_ESP32 */
XPowersPMU   axp_2xxx;

static int esp32_board = ESP32_DEVKIT; /* default */
static size_t ESP32_Min_AppPart_Size = 0;

static portMUX_TYPE GNSS_PPS_mutex = portMUX_INITIALIZER_UNLOCKED;
static portMUX_TYPE PMU_mutex      = portMUX_INITIALIZER_UNLOCKED;
volatile bool PMU_Irq = false;

static bool GPIO_21_22_are_busy = false;

static union {
  uint8_t efuse_mac[6];
  uint64_t chipmacid;
};

static bool TFT_display_frontpage = false;
static uint32_t prev_tx_packets_counter = 0;
static uint32_t prev_rx_packets_counter = 0;
extern bool loopTaskWDTEnabled;

const char *ESP32SX_Device_Manufacturer = SOFTRF_IDENT;
const char *ESP32SX_Model_Stand   = "Standalone Edition"; /* 303a:8132 */
const char *ESP32S3_Model_Prime3  = "Prime Edition Mk.3"; /* 303a:8133 */
const char *ESP32S3_Model_Ham     = "Ham Edition";        /* 303a:818F */
const char *ESP32S3_Model_Midi    = "Midi Edition";       /* 303a:81A0 */
const char *ESP32S3_Model_Ink     = "Ink Edition";        /* 303a:820A */
const char *ESP32S3_Model_Gizmo   = "Gizmo Edition";      /* 303a:82D9 */
const char *ESP32S3_Model_AirVent = "Airventure Edition"; /* 303a:82F9 */
const char *ESP32P4_Model_Concord = "Concorde Edition";   /* 303a:8343 */
const char *ESP32S3_Model_Prime4  = "Prime Edition Mk.4"; /* 303a:8367 */
const uint16_t ESP32SX_Device_Version = SOFTRF_USB_FW_VERSION;

#if defined(EXCLUDE_WIFI)
// Dummy definition to satisfy build sequence
char UDPpacketBuffer[UDP_PACKET_BUFSIZE];
#endif /* EXCLUDE_WIFI */

#if !defined(EXCLUDE_ETHERNET)
#include <ETH.h>
#include "../driver/Ethernet.h"
#endif /* EXCLUDE_ETHERNET */

#if defined(CONFIG_IDF_TARGET_ESP32S3)  || \
    defined(CONFIG_IDF_TARGET_ESP32S31) || \
    defined(CONFIG_IDF_TARGET_ESP32P4)
//#define SPI_DRIVER_SELECT 3
#include <Adafruit_SPIFlash.h>
#include "../driver/EPD.h"
#include "uCDB.hpp"

#if SOC_SDMMC_IO_POWER_EXTERNAL
#include "esp_ldo_regulator.h"
#endif /* SOC_SDMMC_IO_POWER_EXTERNAL */

SPIClass uSD_SPI(HSPI);
#define  SD_CONFIG SdSpiConfig(uSD_SS_pin, SHARED_SPI, SD_SCK_MHZ(16), &uSD_SPI)
SdFat    uSD;

static bool uSD_is_attached = false;

Adafruit_FlashTransport_ESP32 HWFlashTransport;
Adafruit_SPIFlash QSPIFlash(&HWFlashTransport);

static Adafruit_SPIFlash *SPIFlash = &QSPIFlash;

/// Flash device list count
enum {
  EXTERNAL_FLASH_DEVICE_COUNT
};

/// List of all possible flash devices used by ESP32 boards
static SPIFlash_Device_t possible_devices[] = { };

PCF8563_Class *rtc              = nullptr;
I2CBus        *i2c              = nullptr;

static bool ESP32_has_spiflash  = false;
static bool FATFS_is_mounted    = false;
static bool ADB_is_open         = false;
static bool RTC_sync            = false;
static bool ESP32_has_vff       = false; /* very first fix */

RTC_Date fw_build_date_time     = RTC_Date(__DATE__, __TIME__);

#if CONFIG_TINYUSB_MSC_ENABLED
  #if defined(USE_ADAFRUIT_MSC)
    #include "Adafruit_TinyUSB.h"

    // USB Mass Storage object
    Adafruit_USBD_MSC usb_msc;
  #else
    #include "USBMSC.h"

    // USB Mass Storage object
    USBMSC usb_msc;
  #endif /* USE_ADAFRUIT_MSC */
#endif /* CONFIG_TINYUSB_MSC_ENABLED */

// file system object from SdFat
FatVolume fatfs;

#include "../protocol/data/JSON.h"

#define ESP32_JSON_BUFFER_SIZE  1024

StaticJsonBuffer<ESP32_JSON_BUFFER_SIZE> ESP32_jsonBuffer;

ui_settings_t ui_settings = {
    .units        = UNITS_METRIC,
    .zoom         = ZOOM_MEDIUM,
    .protocol     = PROTOCOL_NMEA,
    .rotate       = ROTATE_0,
    .orientation  = DIRECTION_TRACK_UP,
    .adb          = DB_OGN,
    .idpref       = ID_TYPE,
    .vmode        = VIEW_MODE_STATUS,
    .voice        = VOICE_OFF,
    .aghost       = ANTI_GHOSTING_OFF,
    .filter       = TRAFFIC_FILTER_OFF,
    .team         = 0
};

ui_settings_t *ui;
uCDB<FatVolume, File32> ucdb(fatfs);

#if CONFIG_TINYUSB_MSC_ENABLED
#if defined(USE_ADAFRUIT_MSC)
// Callback invoked when received READ10 command.
// Copy disk's data to buffer (up to bufsize) and
// return number of copied bytes (must be multiple of block size)
static int32_t ESP32_msc_read_cb (uint32_t lba, void* buffer, uint32_t bufsize)
{
  // Note: SPIFLash Bock API: readBlocks/writeBlocks/syncBlocks
  // already include 4K sector caching internally. We don't need to cache it, yahhhh!!
  return SPIFlash->readBlocks(lba, (uint8_t*) buffer, bufsize/512) ? bufsize : -1;
}

// Callback invoked when received WRITE10 command.
// Process data in buffer to disk's storage and
// return number of written bytes (must be multiple of block size)
static int32_t ESP32_msc_write_cb (uint32_t lba, uint8_t* buffer, uint32_t bufsize)
{
  // Note: SPIFLash Bock API: readBlocks/writeBlocks/syncBlocks
  // already include 4K sector caching internally. We don't need to cache it, yahhhh!!
  return SPIFlash->writeBlocks(lba, buffer, bufsize/512) ? bufsize : -1;
}

// Callback invoked when WRITE10 command is completed (status received and accepted by host).
// used to flush any pending cache.
static void ESP32_msc_flush_cb (void)
{
  // sync with flash
  SPIFlash->syncBlocks();

  // clear file system's cache to force refresh
  fatfs.cacheClear();
}

#else

// Callback invoked when received READ10 command.
// Copy disk's data to buffer (up to bufsize) and
// return number of copied bytes (must be multiple of block size)
static int32_t ESP32_msc_read_cb (uint32_t lba, uint32_t offset, void* buffer, uint32_t bufsize)
{
  // Note: SPIFLash Bock API: readBlocks/writeBlocks/syncBlocks
  // already include 4K sector caching internally. We don't need to cache it, yahhhh!!
  return SPIFlash->readBlocks(lba, offset, (uint8_t*) buffer, bufsize/512) ?
         bufsize : -1;
}

// Callback invoked when received WRITE10 command.
// Process data in buffer to disk's storage and
// return number of written bytes (must be multiple of block size)
static int32_t ESP32_msc_write_cb (uint32_t lba, uint32_t offset, uint8_t* buffer, uint32_t bufsize)
{
  // Note: SPIFLash Bock API: readBlocks/writeBlocks/syncBlocks
  // already include 4K sector caching internally. We don't need to cache it, yahhhh!!
  int32_t rval = SPIFlash->writeBlocks(lba, offset, buffer, bufsize/512) ?
                 bufsize : -1;

#if 1
  // sync with flash
  SPIFlash->syncBlocks();

  // clear file system's cache to force refresh
  fatfs.cacheClear();
#endif

  return rval;
}
#endif /* USE_ADAFRUIT_MSC */
#endif /* CONFIG_TINYUSB_MSC_ENABLED */

#if !defined(EXCLUDE_IMU)
#include <SensorQMI8658.hpp>
#include <MPU9250.h>

#define IMU_UPDATE_INTERVAL 500 /* ms */
#define OLED_FLIP_THRESHOLD 0.6

SensorQMI8658 imu_qmi8658;
MPU9250       imu_mpu9250;

static unsigned long IMU_Time_Marker = 0;

#if defined(USE_OLED)
extern int32_t IMU_g_x10;
#endif /* USE_OLED */
#endif /* EXCLUDE_IMU */

#if !defined(EXCLUDE_MAG)
#include <SensorQMC6310.hpp>
#if SENSORLIB_VERSION >= SENSORLIB_VERSION_VAL(0, 4, 1)
#include <SensorQMC6309.hpp>
#endif /* (0, 4, 1) */

#define MAG_UPDATE_INTERVAL 500 /* ms */

SensorQMC6310 mag_qmc6310;
#if SENSORLIB_VERSION >= SENSORLIB_VERSION_VAL(0, 4, 1)
SensorQMC6309 mag_qmc6309;
#endif /* (0, 4, 1) */

static unsigned long MAG_Time_Marker = 0;

#if defined(USE_OLED)
extern int32_t MAG_heading;
#endif /* USE_OLED */
#endif /* EXCLUDE_MAG */

#include "soc/rtc.h"
static uint32_t calibrate_one(rtc_cal_sel_t cal_clk, const char *name)
{
    const uint32_t cal_count = 1000;
    const float factor = (1 << 19) * 1000.0f;
    uint32_t cali_val;
    for (int i = 0; i < 5; ++i) {
        cali_val = rtc_clk_cal(cal_clk, cal_count);
    }
    return cali_val;
}

#define CALIBRATE_ONE(cali_clk) calibrate_one(cali_clk, #cali_clk)

//#define DEBUG_X32K(s) Serial.println(s)
#define DEBUG_X32K(s) {}

static bool ESP32_has_32k_xtal = false;

#include <PCA9557.h>
PCA9557 *pca9557              = nullptr;
bool ESP32_has_gpio_extension = false;

#if defined(USE_NEOPIXELBUS_LIBRARY)
NeoPixelBus<NeoGrbFeature, Neo800KbpsMethod> TWR2_Pixel(1, SOC_GPIO_PIN_TWR2_NEOPIXEL);
#endif /* USE_NEOPIXELBUS_LIBRARY */
#if defined(USE_ADAFRUIT_NEO_LIBRARY)
Adafruit_NeoPixel TWR2_Pixel = Adafruit_NeoPixel(1, SOC_GPIO_PIN_TWR2_NEOPIXEL,
                                                 NEO_GRB + NEO_KHZ800);
#endif /* USE_ADAFRUIT_NEO_LIBRARY */

#if defined(USE_SA8X8)
#include <SA818Controller.h>
#include <AFSK.h>
extern SA818Controller controller;
extern uint32_t Data_Frequency;
extern uint32_t Voice_Frequency;
extern byte     SA8X8_SQL;

extern void sa868_Tx_LED_state(bool);

bool ESP32_R22_workaround = false;
#endif /* USE_SA8X8 */

#if !defined(EXCLUDE_VOICE_MESSAGE)
#if defined(CONFIG_IDF_TARGET_ESP32S3)
#include <driver/i2s.h>
#endif /* CONFIG_IDF_TARGET_ESP32S3 */
#include <AudioFileSourceSdFat.h>
#include <AudioGeneratorWAV.h>
#include <AudioOutputI2S.h>

#define MAX_FILENAME_LEN      64
#define WAV_FILE_PREFIX       "/Audio/"
#define WAV_FILE_SUFFIX       ".wav"

#define VOICE1_SUBDIR         "voice1/"
#define VOICE2_SUBDIR         "voice2/"
#define VOICE3_SUBDIR         "voice3/"

AudioGeneratorWAV    *Audio_Gen;
AudioFileSourceSdFat *Audio_Source;
AudioOutputI2S       *Audio_Sink;

bool playback_inited = false;

static bool play_file(char *filename, void (*func)())
{
  bool rval = false;

  if (Audio_Source->open(filename)) {
    unsigned long Audio_Timemarker = millis();
    Audio_Gen->begin(Audio_Source, Audio_Sink);

    bool wdt_status = loopTaskWDTEnabled;

    if (wdt_status) {
      disableLoopWDT();
    }

    while (Audio_Gen->loop()) {
      // feedLoopWDT();
      if (func) { (*func)(); }

      if (millis() - Audio_Timemarker > 30000) {
        Audio_Gen->stop();
        Serial.println("ERROR: Audio timeout. Playback aborted.");
        Serial.flush();
      }
    }

    if (wdt_status) {
      enableLoopWDT();
    }

    rval = true;
  }

  return rval;
}
#endif /* EXCLUDE_VOICE_MESSAGE */

#if defined(CONFIG_IDF_TARGET_ESP32P4)
#include "esp_check.h"
#include "es8311.h"

#define EXAMPLE_SAMPLE_RATE     11025
#define EXAMPLE_VOICE_VOLUME    75 // 0 - 100
#define EXAMPLE_MIC_GAIN        (es8311_mic_gain_t)(3) // 0 - 7

const char *TAG_ES83 = "esp32p4_i2s_es8311";

esp_err_t es8311_codec_init(const unsigned int i2c_num) {
    es8311_handle_t es_handle = es8311_create(i2c_num, ES8311_ADDRRES_0);
    ESP_RETURN_ON_FALSE(es_handle, ESP_FAIL, TAG_ES83, "es8311 create failed");
    const es8311_clock_config_t es_clk = {
        .mclk_inverted = false,
        .sclk_inverted = false,
        .mclk_from_mclk_pin = true,
        .mclk_frequency = EXAMPLE_SAMPLE_RATE * 256,
        .sample_frequency = EXAMPLE_SAMPLE_RATE
    };

    ESP_ERROR_CHECK(es8311_init(es_handle, &es_clk, ES8311_RESOLUTION_16, ES8311_RESOLUTION_16));
    ESP_RETURN_ON_ERROR(es8311_sample_frequency_config(es_handle, es_clk.mclk_frequency, es_clk.sample_frequency), TAG_ES83, "set es8311 sample frequency failed");
    ESP_RETURN_ON_ERROR(es8311_microphone_config(es_handle, false), TAG_ES83, "set es8311 microphone failed");

    ESP_RETURN_ON_ERROR(es8311_voice_volume_set(es_handle, EXAMPLE_VOICE_VOLUME, NULL), TAG_ES83, "set es8311 volume failed");
    ESP_RETURN_ON_ERROR(es8311_microphone_gain_set(es_handle, EXAMPLE_MIC_GAIN), TAG_ES83, "set es8311 microphone gain failed");
    return ESP_OK;
}

#include <SensorLib_Version.h>
#if SENSORLIB_VERSION == SENSORLIB_VERSION_VAL(0, 3, 1)
#include <ExtensionIOXL9555.hpp>
#endif /* (0, 3, 1) */
#if SENSORLIB_VERSION >= SENSORLIB_VERSION_VAL(0, 4, 0)
#include "IoExpanderXL9555.hpp"

#define ExtensionIOXL9555 IoExpanderXL9555
#endif /* (0, 4, 0) */
#include <GaugeBQ27220.hpp>
#include <ICM_20948.h>
#include <TouchDrvGT911.hpp>
#if SENSORLIB_VERSION >= SENSORLIB_VERSION_VAL(0, 4, 1)
#include <HapticDrivers.hpp>
#endif /* (0, 4, 1) */

#if defined(TDP4_ES8311_IIC) && TDP4_ES8311_IIC == 2
TwoWire Wire2 = TwoWire(2);
#endif /* TDP4_ES8311_IIC */

ExtensionIOXL9555 *xl9535 = nullptr;
GaugeBQ27220      bq_27220;
ICM_20948_I2C     imu_icm20948;
#if SENSORLIB_VERSION >= SENSORLIB_VERSION_VAL(0, 4, 1)
HapticDriver_AW86224 vibra;
#endif /* (0, 4, 1) */

static bool ESP32_has_vibra = false;

#include "../driver/GNSS.h"
#if defined(USE_DSI)
#include "../driver/DSI.h"
#endif /* USE_DSI */

#define SGM38121_REG_CHIP_REV      0x00
#define SGM38121_REG_DISCH         0x02
#define SGM38121_REG_DVDD1_VOUT    0x03
#define SGM38121_REG_DVDD2_VOUT    0x04
#define SGM38121_REG_AVDD1_VOUT    0x05
#define SGM38121_REG_AVDD2_VOUT    0x06
#define SGM38121_REG_FUNCTION      0x07
#define SGM38121_REG_SEQ_DVDD      0x0A
#define SGM38121_REG_SEQ_AVDD      0x0B
#define SGM38121_REG_ENABLE        0x0E
#define SGM38121_REG_SEQ_CTRL      0x0F

#define SGM38121_ENABLE_DVDD1_BIT  BIT0
#define SGM38121_ENABLE_DVDD2_BIT  BIT1
#define SGM38121_ENABLE_AVDD1_BIT  BIT2
#define SGM38121_ENABLE_AVDD2_BIT  BIT3

static bool sgm38121_read_reg(TwoWire *wire, uint8_t reg, uint8_t *value)
{
    wire->beginTransmission(SGM38121_ADDRESS);
    wire->write(reg);
    if (wire->endTransmission(false) != 0)
        return false;
    if (wire->requestFrom(SGM38121_ADDRESS, 1) != 1)
        return false;
    *value = wire->read();
    return true;
}

static bool sgm38121_write_reg(TwoWire *wire, uint8_t reg, uint8_t value)
{
    wire->beginTransmission(SGM38121_ADDRESS);
    wire->write(reg);
    wire->write(value);
    return wire->endTransmission() == 0;
}

static int sgm38121_decode_dvdd_mv(uint8_t reg_value)
{
    if (reg_value < 0x03 || reg_value > 0x7D) {
        return -1;
    }
    return 504 + (reg_value * 8);
}

static int sgm38121_decode_avdd_mv(uint8_t reg_value)
{
    if (reg_value < 0x0F) {
        return -1;
    }
    return 1384 + (reg_value * 8);
}

static uint8_t sgm38121_encode_dvdd_mv_rounded(int target_mv, int *actual_mv)
{
    int clamped_mv = target_mv;
    if (clamped_mv < 528) {
        clamped_mv = 528;
    }
    if (clamped_mv > 1504) {
        clamped_mv = 1504;
    }

    int reg_value = (clamped_mv - 504 /* + 4*/ ) / 8;
    if (reg_value < 0x0F) {
        reg_value = 0x0F;
    }
    if (reg_value > 0xFF) {
        reg_value = 0xFF;
    }

    if (actual_mv) {
        *actual_mv = sgm38121_decode_dvdd_mv((uint8_t)reg_value);
    }
    return (uint8_t)reg_value;
}

static uint8_t sgm38121_encode_avdd_mv_rounded(int target_mv, int *actual_mv)
{
    int clamped_mv = target_mv;
    if (clamped_mv < 1504) {
        clamped_mv = 1504;
    }
    if (clamped_mv > 3424) {
        clamped_mv = 3424;
    }

    int reg_value = (clamped_mv - 1384 /* + 4*/) / 8;
    if (reg_value < 0x0F) {
        reg_value = 0x0F;
    }
    if (reg_value > 0xFF) {
        reg_value = 0xFF;
    }

    if (actual_mv) {
        *actual_mv = sgm38121_decode_avdd_mv((uint8_t)reg_value);
    }
    return (uint8_t)reg_value;
}

#if defined(USE_CAMERA)
#include <ESP32CSI_Vision.h>

ESP32P4_Camera cam;
ESP32P4_MjpegServer stream;
#endif /* USE_CAMERA */
#endif /* CONFIG_IDF_TARGET_ESP32P4 */
#endif /* CONFIG_IDF_TARGET_ESP32S3-P4 */

#if defined(CONFIG_IDF_TARGET_ESP32C3) || defined(CONFIG_IDF_TARGET_ESP32)
#if defined(USE_NEOPIXELBUS_LIBRARY)
NeoPixelBus<NeoGrbFeature, Neo800KbpsMethod> XR1_Pixel(1, SOC_GPIO_PIN_ELRS_PIXEL);
#endif /* USE_NEOPIXELBUS_LIBRARY */
#if defined(USE_ADAFRUIT_NEO_LIBRARY)
Adafruit_NeoPixel XR1_Pixel = Adafruit_NeoPixel(1, SOC_GPIO_PIN_ELRS_PIXEL,
                                                NEO_GRB + NEO_KHZ800);
#endif /* USE_ADAFRUIT_NEO_LIBRARY */
#endif /* CONFIG_IDF_TARGET_ESP32C3 */

#if CONFIG_TINYUSB_ENABLED && \
    (defined(CONFIG_IDF_TARGET_ESP32S2)  || \
     defined(CONFIG_IDF_TARGET_ESP32S3)  || \
     defined(CONFIG_IDF_TARGET_ESP32S31) || \
     defined(CONFIG_IDF_TARGET_ESP32P4))
#include <USB.h>
#if defined(CONFIG_IDF_TARGET_ESP32P4)
#ifndef USB_VID
#define USB_VID 0x303A
#endif
#ifndef USB_PID
#define USB_PID 0x1001
#endif
#endif /* CONFIG_IDF_TARGET_ESP32P4 */
#endif /* CONFIG_TINYUSB_ENABLED */

#if defined(ENABLE_D1090_INPUT)
#include <mode-s.h>

mode_s_t state;
#endif /* ENABLE_D1090_INPUT */

static void IRAM_ATTR ESP32_PMU_Interrupt_handler() {
  portENTER_CRITICAL_ISR(&PMU_mutex);
  PMU_Irq = true;
  portEXIT_CRITICAL_ISR(&PMU_mutex);
}

static uint32_t ESP32_getFlashId()
{
  return g_rom_flashchip.device_id;
}

#if defined(CORE_DEBUG_LEVEL) && CORE_DEBUG_LEVEL>0 && !defined(TAG_MAC)
#define TAG_MAC "MAC"
#endif

static void ESP32_setup()
{
#if !defined(SOFTRF_ADDRESS)

  esp_err_t ret = ESP_OK;
  uint8_t null_mac[6] = {0};

#if defined(CONFIG_IDF_TARGET_ESP32C5)  || \
    defined(CONFIG_IDF_TARGET_ESP32C6)  || \
    defined(CONFIG_IDF_TARGET_ESP32C61) || \
    defined(CONFIG_IDF_TARGET_ESP32H2)  || \
    defined(CONFIG_IDF_TARGET_ESP32H4)
  ret = esp_read_mac(efuse_mac, ESP_MAC_WIFI_STA);
  if (ret != ESP_OK) {
#else
  ret = esp_efuse_mac_get_custom(efuse_mac);
  if (ret != ESP_OK) {
      ESP_LOGE(TAG_MAC, "Get base MAC address from BLK3 of EFUSE error (%s)", esp_err_to_name(ret));
    /* If get custom base MAC address error, the application developer can decide what to do:
     * abort or use the default base MAC address which is stored in BLK0 of EFUSE by doing
     * nothing.
     */
#endif /* CONFIG_IDF_TARGET_ESP32C5 || C6 || H2 || H4 */
    ESP_LOGI(TAG_MAC, "Use base MAC address which is stored in BLK0 of EFUSE");
    chipmacid = ESP.getEfuseMac();
  } else {
    if (memcmp(efuse_mac, null_mac, 6) == 0) {
      ESP_LOGI(TAG_MAC, "Use base MAC address which is stored in BLK0 of EFUSE");
      chipmacid = ESP.getEfuseMac();
    }
  }
#endif /* SOFTRF_ADDRESS */

#if ESP32_DISABLE_BROWNOUT_DETECTOR
  WRITE_PERI_REG(RTC_CNTL_BROWN_OUT_REG, 0);
#endif

#if defined(ESP_IDF_VERSION_MAJOR) && ESP_IDF_VERSION_MAJOR >= 5
  size_t flash_size;
  esp_flash_get_size(NULL, (uint32_t *) &flash_size);
#else
  size_t flash_size = spi_flash_get_chip_size();
#endif /* ESP_IDF_VERSION_MAJOR */

  size_t min_app_size = flash_size;

  esp_partition_iterator_t it;
  const esp_partition_t *part;

  it = esp_partition_find(ESP_PARTITION_TYPE_APP, ESP_PARTITION_SUBTYPE_ANY, NULL);
  if (it) {
    do {
      part = esp_partition_get(it);
      if (part->subtype == ESP_PARTITION_SUBTYPE_APP_FACTORY) {
        continue;
      }
      if (part->size < min_app_size) {
        min_app_size = part->size;
      }
    } while (it = esp_partition_next(it));

    if (it) esp_partition_iterator_release(it);
  }

  if (min_app_size && (min_app_size != flash_size)) {
    ESP32_Min_AppPart_Size = min_app_size;
  }

  uint32_t flash_id = ESP32_getFlashId();

  /*
   *    Board             |   Module         |  Flash memory IC
   *  --------------------+------------------+--------------------
   *  DoIt ESP32          | WROOM            | GIGADEVICE_GD25Q32
   *  TTGO T3  V2.0       | PICO-D4 IC       | GIGADEVICE_GD25Q32
   *  TTGO T3  V2.1.6     | PICO-D4 IC       | GIGADEVICE_GD25Q32
   *  TTGO T22 V06        |                  | WINBOND_NEX_W25Q32_V
   *  TTGO T22 V08        |                  | WINBOND_NEX_W25Q32_V
   *  TTGO T22 V11        |                  | BOYA_BY25Q32AL
   *  TTGO T22 V12        |                  | WINBOND_NEX_W25Q32_V
   *  TTGO T8  V1.8       | WROVER           | GIGADEVICE_GD25LQ32
   *  TTGO T8 S2 V1.1     |                  | WINBOND_NEX_W25Q32_V
   *  TTGO T5S V1.9       |                  | WINBOND_NEX_W25Q32_V
   *  TTGO T5S V2.8       |                  | BOYA_BY25Q32AL
   *  TTGO T5  4.7        | WROVER-E         | XMC_XM25QH128C
   *  TTGO T-Watch        |                  | WINBOND_NEX_W25Q128_V
   *  Ai-T NodeMCU-S3     | ESP-S3-12K       | GIGADEVICE_GD25Q64C
   *  TTGO T-Dongle       |                  | BOYA_BY25Q32AL
   *  TTGO S3 Core        |                  | GIGADEVICE_GD25Q64C
   *  TTGO T-01C3         |                  | BOYA_BY25Q32AL
   *                      | ESP-C3-12F       | XMC_XM25QH32B
   *  LilyGO T-TWR        | WROOM-1-N16R8    | GIGADEVICE_GD25Q128
   *  Heltec Tracker      |                  | GIGADEVICE_GD25Q64
   *                      | WT0132C6-S5      | ZBIT_ZB25VQ32B
   *  LilyGO T3-C6        | ESP32-C6-MINI    | XMC_XM25QH32B
   *  LilyGO T3-S3-EP     | ESP32-S3-MINI    | XMC_XM25QH32B
   *  LilyGO T3-S3-OL     | ESP32-S3FH4R2    |
   *  Elecrow TN-M2       | ESP32-S3-N4R8    | ZBIT_ZB25VQ32B
   *  RadioMaster XR1     | ESP32-C3 (QFN32) | XMC_XM25QH32B
   *  RadioMaster XR1     |                  | 0x464016 (TBD)
   *  Elecrow TN-M5       | ESP32-S3-N4R8    | 0x464016 (TBD)
   *  Ebyte EoRa-HUB      | ESP32-S3FH4R2    |
   *  WT99P4C5-S1 CPU     | WT0132P4-A1      | ZBIT_ZB25VQ128ASIG
   *  WT99P4C5-S1 NCU     | ESP32-C5-WROOM-1 | XMC_XM25QH64B
   *  LilyGO T-Display P4 |                  | GIGADEVICE_GD25Q128
   *  LilyGO T-Beam 1W    | WROOM-1-N16R8    | 0x464018 (TBD)
   *  Meshnology W12      | ESP32-S3R8       | WINBOND_NEX_W25Q128_V
   */

  if (psramFound()) {
    switch (flash_id)
    {
    case MakeFlashId(GIGADEVICE_ID, GIGADEVICE_GD25LQ32):
      /* ESP32-WROVER module with ESP32-NODEMCU-ADAPTER */
      hw_info.model = SOFTRF_MODEL_STANDALONE;
      break;
    case MakeFlashId(WINBOND_NEX_ID, WINBOND_NEX_W25Q128_V):
      hw_info.model = SOFTRF_MODEL_SKYWATCH;
      break;
#if defined(CONFIG_IDF_TARGET_ESP32)
    case MakeFlashId(WINBOND_NEX_ID, WINBOND_NEX_W25Q32_V):
    case MakeFlashId(BOYA_ID, BOYA_BY25Q32AL):
    default:
      hw_info.model = SOFTRF_MODEL_PRIME_MK2;
#elif defined(CONFIG_IDF_TARGET_ESP32S2)
    default:
      esp32_board   = ESP32_S2_T8_V1_1;
#elif defined(CONFIG_IDF_TARGET_ESP32S3) || defined(CONFIG_IDF_TARGET_ESP32S31)
    case MakeFlashId(GIGADEVICE_ID, GIGADEVICE_GD25Q128):
    case MakeFlashId(TBD_ID, TBD_25Q128):
      /* specific to psram_type=opi enabled custom build */
      hw_info.model = SOFTRF_MODEL_HAM;
      break;
    case MakeFlashId(ST_ID, XMC_XM25QH32B):
      esp32_board = ESP32_LILYGO_T3S3_EPD; /* ESP32-S3-MINI-1U ESP32-S3FH4R2 */
      break;
    case MakeFlashId(WINBOND_NEX_ID, WINBOND_NEX_W25Q64_V):
      esp32_board   = ESP32_BANANA_PICOW;
      break;
    /* Both Ai-Thinker ESP-S3-12K and LilyGO S3 Core have QSPI PSRAM onboard */
    case MakeFlashId(GIGADEVICE_ID, GIGADEVICE_GD25Q64):
    default:
      hw_info.model = SOFTRF_MODEL_PRIME_MK3;
#elif defined(CONFIG_IDF_TARGET_ESP32C5)
    case MakeFlashId(ST_ID, XMC_XM25QH64B):
    default:
      esp32_board   = ESP32_C5_DEVKIT;
#elif defined(CONFIG_IDF_TARGET_ESP32C61)
    default:
      esp32_board   = ESP32_C61_DEVKIT;
#elif defined(CONFIG_IDF_TARGET_ESP32P4)
    case MakeFlashId(GIGADEVICE_ID, GIGADEVICE_GD25Q128):
      esp32_board   = ESP32_LILYGO_TDISPLAY_P4;
      break;
    case MakeFlashId(ZBIT_ID, ZBIT_ZB25VQ128A): /* WT0132P4-A1 ESP32-P4NRW32 */
    default:
      esp32_board   = ESP32_P4_WT_DEVKIT;
#else
    default:
#endif
      break;
    }
  } else {
#if defined(CONFIG_IDF_TARGET_ESP32)
#if defined(ESP_IDF_VERSION_MAJOR) && ESP_IDF_VERSION_MAJOR >= 5
    /* TBD */
#else
    uint32_t chip_ver = REG_GET_FIELD(EFUSE_BLK0_RDATA3_REG, EFUSE_RD_CHIP_VER_PKG);
    uint32_t pkg_ver  = chip_ver & 0x7;
    if (pkg_ver == EFUSE_RD_CHIP_VER_PKG_ESP32PICOD4) {
      esp32_board = ESP32_TTGO_V2_OLED;

#if 0
      pinMode(SOC_GPIO_PIN_TBEAM_RF_RST_V05, INPUT_PULLDOWN);
      pinMode(SOC_GPIO_PIN_DIO0, INPUT_PULLUP);

      delay(50);

      if (digitalRead(SOC_GPIO_PIN_DIO0) == HIGH) {
        esp32_board = ESP32_LILYGO_T_ELRS;
      }

      pinMode(SOC_GPIO_PIN_DIO0, INPUT);
      pinMode(SOC_GPIO_PIN_TBEAM_RF_RST_V05, INPUT);
#endif

      if (esp32_board == ESP32_TTGO_V2_OLED) {
        lmic_pins.rst  = SOC_GPIO_PIN_TBEAM_RF_RST_V05;
        lmic_pins.busy = SOC_GPIO_PIN_TBEAM_RF_BUSY_V08;
      }
    }
#endif /* ESP_IDF_VERSION_MAJOR */
#elif defined(CONFIG_IDF_TARGET_ESP32S2)
    esp32_board      = ESP32_S2_T8_V1_1;
#elif defined(CONFIG_IDF_TARGET_ESP32S3) || defined(CONFIG_IDF_TARGET_ESP32S31)
    switch (flash_id)
    {
    case MakeFlashId(GIGADEVICE_ID, GIGADEVICE_GD25Q128):
    case MakeFlashId(TBD_ID, TBD_25Q128):
      /*
       * LilyGO T-TWR and T-Beam 1W have OPI PSRAM in the WROOM module.
       * ESP32 Arduino Core 2.0.x is unable to detect OPI PSRAM
       * unless we do a psram_type=opi custom build.
       */
      hw_info.model  = SOFTRF_MODEL_HAM;  /* allow psramFound() to fail */
      break;
    case MakeFlashId(GIGADEVICE_ID, GIGADEVICE_GD25Q64):
      /* Heltec Tracker has no PSRAM onboard */
      esp32_board    = ESP32_HELTEC_TRACKER;
      hw_info.model  = SOFTRF_MODEL_MIDI;
      break;
    case MakeFlashId(ZBIT_ID, ZBIT_ZB25VQ32B):
    case MakeFlashId(TBD_ID, TBD_25Q32):
    case MakeFlashId(ST_ID, XMC_XM25QH32B):
    case MakeFlashId(GIGADEVICE_ID, GIGADEVICE_GD25Q32):
      /*
       * Elecrow TinkNode M2 has OPI PSRAM in the WROOM module.
       * ESP32 Arduino Core 2.0.x is unable to detect OPI PSRAM
       * unless we do a psram_type=opi custom build.
       */
      esp32_board    = ESP32_ELECROW_TN_M5; /* allow psramFound() to fail */
      break;
    default:
      esp32_board    = ESP32_S3_DEVKIT;
      break;
    }
#elif defined(CONFIG_IDF_TARGET_ESP32C2)
    switch (flash_id)
    {
    case MakeFlashId(FMICRO_ID, FMICRO_FM25Q16): /* WT018684-S5 */
    default:
      esp32_board   = ESP32_C2_DEVKIT;
      break;
    }
#elif defined(CONFIG_IDF_TARGET_ESP32C3)
#if defined(ESP_IDF_VERSION_MAJOR) && ESP_IDF_VERSION_MAJOR >= 5
    /* TBD */
#else
    uint32_t part0 = REG_GET_FIELD(EFUSE_RD_MAC_SPI_SYS_3_REG, EFUSE_SYS_DATA_PART0_0);
    uint32_t flash_cap = (part0 >> 2) & 0x7;

    uint32_t chip_ver = REG_GET_FIELD(EFUSE_RD_MAC_SPI_SYS_3_REG, EFUSE_PKG_VERSION);
    uint32_t pkg_ver  = chip_ver & 0x7;

    uint32_t wafer = REG_GET_FIELD(EFUSE_RD_MAC_SPI_SYS_3_REG, EFUSE_WAFER_VERSION);
    uint32_t wafer_ver  = wafer & 0x7;

    uint32_t sys4 = REG_GET_FIELD(EFUSE_RD_MAC_SPI_SYS_4_REG, EFUSE_SYS_DATA_PART0_1);
    uint32_t flash_vendor  = sys4 & 0x7;

    uint32_t sys5 = REG_GET_FIELD(EFUSE_RD_MAC_SPI_SYS_5_REG, EFUSE_SYS_DATA_PART0_2);
    uint32_t major_chip_version  = (sys5 >> 24) & 0x03;
    uint32_t minor_chip_version  = (sys5 >> 23) & 0x01;
#endif /* ESP_IDF_VERSION_MAJOR */

    switch (flash_id)
    {
    case MakeFlashId(ZBIT_ID, ZBIT_ZB25VQ32B): /* C3FH4 or 4X with emb. flash */
      esp32_board   = ESP32_RADIOMASTER_XR1;
      break;
    case MakeFlashId(ST_ID,   XMC_XM25QH32B):
    /* https://github.com/lyusupov/SoftRF/issues/191 */
    case MakeFlashId(TBD_ID,  TBD_25Q32):
      if (wafer_ver == 4)
        esp32_board = ESP32_RADIOMASTER_XR1;
      else
        esp32_board = ESP32_C3_DEVKIT;  /* ESP-C3-12F  */
      break;
    case MakeFlashId(BOYA_ID, BOYA_BY25Q32AL): /* TTGO T-01C3 */
    default:
      esp32_board   = ESP32_C3_DEVKIT;
      break;
    }
#elif defined(CONFIG_IDF_TARGET_ESP32C5)
    switch (flash_id)
    {
    case MakeFlashId(ST_ID, XMC_XM25QH64B):
    default:
      esp32_board   = ESP32_C5_DEVKIT;
      break;
    }
#elif defined(CONFIG_IDF_TARGET_ESP32C6)
    uint32_t pkg_ver = REG_GET_FIELD(EFUSE_RD_MAC_SPI_SYS_3_REG,
                                     EFUSE_PKG_VERSION);
    switch (flash_id)
    {
    case MakeFlashId(ST_ID, XMC_XM25QH32B):
      esp32_board   = (pkg_ver == 1) /* QFN32 */ ?
                      ESP32_LILYGO_T3C6 /* ESP32-C6-MINI-1U */ :
                      ESP32_C6_DEVKIT;
      break;
    case MakeFlashId(ZBIT_ID, ZBIT_ZB25VQ32B): /* WT0132C6-S5 (C6 QFN40) */
    default:
      esp32_board   = ESP32_C6_DEVKIT;
      break;
    }
#elif defined(CONFIG_IDF_TARGET_ESP32C61)
    switch (flash_id)
    {
    default:
      esp32_board   = ESP32_C61_DEVKIT;
      break;
    }
#elif defined(CONFIG_IDF_TARGET_ESP32H2)
    switch (flash_id)
    {
    default:
      esp32_board   = ESP32_H2_DEVKIT;
      break;
    }
#elif defined(CONFIG_IDF_TARGET_ESP32H4)
    switch (flash_id)
    {
    default:
      esp32_board   = ESP32_H4_DEVKIT;
      break;
    }
#endif /* CONFIG_IDF_TARGET_ESP32 */
  }

  if (SOC_GPIO_PIN_BUZZER != SOC_UNUSED_PIN) {
#if !defined(ESP_IDF_VERSION_MAJOR) || ESP_IDF_VERSION_MAJOR < 5
    ledcAttachPin(SOC_GPIO_PIN_BUZZER, LEDC_CHANNEL_BUZZER);
    ledcSetup(LEDC_CHANNEL_BUZZER, 0, LEDC_RESOLUTION_BUZZER);
#endif /* ESP_IDF_VERSION_MAJOR */
  }

  if (hw_info.model == SOFTRF_MODEL_SKYWATCH) {
    esp32_board   = ESP32_TTGO_T_WATCH;
    hw_info.rtc   = RTC_PCF8563;
    hw_info.imu   = ACC_BMA423;
    hw_info.touch = TOUCH_FT5206;

#if defined(CONFIG_IDF_TARGET_ESP32)
    Wire1.begin(SOC_GPIO_PIN_TWATCH_SEN_SDA , SOC_GPIO_PIN_TWATCH_SEN_SCL);
    Wire1.beginTransmission(AXP202_SLAVE_ADDRESS);
    bool has_axp202 = (Wire1.endTransmission() == 0);
    if (has_axp202) {

      hw_info.pmu = PMU_AXP202;

      axp_xxx.begin(Wire1, AXP202_SLAVE_ADDRESS);

      axp_xxx.enableIRQ(AXP202_ALL_IRQ, AXP202_OFF);
      axp_xxx.adc1Enable(0xFF, AXP202_OFF);

      axp_xxx.setChgLEDMode(AXP20X_LED_LOW_LEVEL);

      axp_xxx.setPowerOutPut(AXP202_LDO2, AXP202_ON); // BL
      axp_xxx.setPowerOutPut(AXP202_LDO3, AXP202_ON); // S76G (MCU + LoRa)
      axp_xxx.setLDO4Voltage(AXP202_LDO4_1800MV);
      axp_xxx.setPowerOutPut(AXP202_LDO4, AXP202_ON); // S76G (Sony GNSS)

      pinMode(SOC_GPIO_PIN_TWATCH_PMU_IRQ, INPUT_PULLUP);

      attachInterrupt(digitalPinToInterrupt(SOC_GPIO_PIN_TWATCH_PMU_IRQ),
                      ESP32_PMU_Interrupt_handler, FALLING);

      axp_xxx.adc1Enable(AXP202_BATT_VOL_ADC1, AXP202_ON);
      axp_xxx.enableIRQ(AXP202_PEK_LONGPRESS_IRQ | AXP202_PEK_SHORTPRESS_IRQ, true);
      axp_xxx.clearIRQ();
    } else {
      WIRE_FINI(Wire1);
    }
  } else if (esp32_board == ESP32_LILYGO_T_ELRS) {
    hw_info.model    = SOFTRF_MODEL_NANO;
    hw_info.revision = 2;

    lmic_pins.nss  = SOC_GPIO_PIN_ELRS_SS;
    lmic_pins.rst  = SOC_GPIO_PIN_ELRS_RST;
    lmic_pins.busy = SOC_GPIO_PIN_ELRS_BUSY;
    // lmic_pins.txe  = SOC_GPIO_PIN_ELRS_HF_TX; /* 1+ GHz only */
    // lmic_pins.rxe  = SOC_GPIO_PIN_ELRS_HF_RX; /* 1+ GHz only */
#if defined(USE_RADIOLIB) || defined(USE_RADIOHEAD)
    lmic_pins.dio[0] = SOC_GPIO_PIN_ELRS_DIO9;
#endif /* USE_RADIOLIB || USE_RADIOHEAD */
#endif /* CONFIG_IDF_TARGET_ESP32 */
  } else if (hw_info.model == SOFTRF_MODEL_PRIME_MK2) {
    esp32_board = ESP32_TTGO_T_BEAM;

#if defined(CONFIG_IDF_TARGET_ESP32)
    Wire1.begin(TTGO_V2_OLED_PIN_SDA , TTGO_V2_OLED_PIN_SCL);
    Wire1.beginTransmission(AXP192_SLAVE_ADDRESS);
    bool has_axp = (Wire1.endTransmission() == 0);

    bool has_axp192 = has_axp &&
                      (axp_xxx.begin(Wire1, AXP192_SLAVE_ADDRESS) == AXP_PASS);

    if (has_axp192) {

      hw_info.revision = 8;
      hw_info.pmu = PMU_AXP192;

      axp_xxx.setChgLEDMode(AXP20X_LED_LOW_LEVEL);

      axp_xxx.setPowerOutPut(AXP192_LDO2,  AXP202_ON);
      axp_xxx.setPowerOutPut(AXP192_LDO3,  AXP202_ON);
      axp_xxx.setPowerOutPut(AXP192_DCDC1, AXP202_ON);
      axp_xxx.setPowerOutPut(AXP192_DCDC2, AXP202_ON); // NC
      axp_xxx.setPowerOutPut(AXP192_EXTEN, AXP202_ON);

      axp_xxx.setDCDC1Voltage(3300); //       AXP192 power-on value: 3300
      axp_xxx.setLDO2Voltage (3300); // LoRa, AXP192 power-on value: 3300
      axp_xxx.setLDO3Voltage (3000); // GPS,  AXP192 power-on value: 2800

      pinMode(SOC_GPIO_PIN_TBEAM_V08_PMU_IRQ, INPUT /* INPUT_PULLUP */);

      attachInterrupt(digitalPinToInterrupt(SOC_GPIO_PIN_TBEAM_V08_PMU_IRQ),
                      ESP32_PMU_Interrupt_handler, FALLING);

      axp_xxx.enableIRQ(AXP202_PEK_LONGPRESS_IRQ | AXP202_PEK_SHORTPRESS_IRQ, true);
      axp_xxx.clearIRQ();
    } else {
      bool has_axp2101 = has_axp && axp_2xxx.begin(Wire1,
                                                   AXP2101_SLAVE_ADDRESS,
                                                   TTGO_V2_OLED_PIN_SDA,
                                                   TTGO_V2_OLED_PIN_SCL);
      if (has_axp2101) {

        // Set the minimum common working voltage of the PMU VBUS input,
        // below this value will turn off the PMU
        axp_2xxx.setVbusVoltageLimit(XPOWERS_AXP2101_VBUS_VOL_LIM_4V36);

        // Set the maximum current of the PMU VBUS input,
        // higher than this value will turn off the PMU
        axp_2xxx.setVbusCurrentLimit(XPOWERS_AXP2101_VBUS_CUR_LIM_1500MA);

        // DCDC1 1500~3400mV, IMAX=2A
        axp_2xxx.setDC1Voltage(3300); // ESP32,  AXP2101 power-on value: 3300

        // ALDO 500~3500V, 100mV/step, IMAX=300mA
        axp_2xxx.setButtonBatteryChargeVoltage(3100); // GNSS battery

        axp_2xxx.setALDO2Voltage(3300); // LoRa, AXP2101 power-on value: 2800
        axp_2xxx.setALDO3Voltage(3300); // GPS,  AXP2101 power-on value: 3300

        // axp_2xxx.enableDC1();
        axp_2xxx.enableButtonBatteryCharge();

        axp_2xxx.enableALDO2();
        axp_2xxx.enableALDO3();

        axp_2xxx.setChargingLedMode(XPOWERS_CHG_LED_ON);

        pinMode(SOC_GPIO_PIN_TBEAM_V08_PMU_IRQ, INPUT /* INPUT_PULLUP */);

        attachInterrupt(digitalPinToInterrupt(SOC_GPIO_PIN_TBEAM_V08_PMU_IRQ),
                        ESP32_PMU_Interrupt_handler, FALLING);

        axp_2xxx.disableIRQ(XPOWERS_AXP2101_ALL_IRQ);
        axp_2xxx.clearIrqStatus();

        axp_2xxx.setChargerConstantCurr(XPOWERS_AXP2101_CHG_CUR_500MA);
        axp_2xxx.disableTSPinMeasure();
        axp_2xxx.enableBattVoltageMeasure();

        axp_2xxx.enableIRQ(XPOWERS_AXP2101_PKEY_LONG_IRQ |
                           XPOWERS_AXP2101_PKEY_SHORT_IRQ);

        hw_info.revision = 12;
        hw_info.pmu = PMU_AXP2101;
      } else {
        WIRE_FINI(Wire1);
        hw_info.revision = 2;
      }
    }
#endif /* CONFIG_IDF_TARGET_ESP32 */
    lmic_pins.rst  = SOC_GPIO_PIN_TBEAM_RF_RST_V05;
    lmic_pins.busy = SOC_GPIO_PIN_TBEAM_RF_BUSY_V08;
#if defined(USE_RADIOLIB)
    /* reserved for DIO 11 of LilyGO LR2021 module */
    lmic_pins.dio[0] = SOC_GPIO_PIN_TBEAM_RF_DIO1_V08;
#endif /* USE_RADIOLIB */
  } else if (esp32_board == ESP32_DEVKIT) {
#if defined(USE_RADIOLIB)
    /* reserved for DIO 11 of LilyGO LR2021 module */
    lmic_pins.dio[0] = SOC_GPIO_PIN_CE;
#endif /* USE_RADIOLIB */
#if defined(CONFIG_IDF_TARGET_ESP32S2)
  } else if (esp32_board == ESP32_S2_T8_V1_1) {
    lmic_pins.nss  = SOC_GPIO_PIN_T8_S2_LORA_SS;
    lmic_pins.rst  = SOC_GPIO_PIN_T8_S2_LORA_RST;
    lmic_pins.busy = LMIC_UNUSED_PIN;

    pinMode(SOC_GPIO_PIN_T8_S2_PWR_EN, INPUT_PULLUP);

#if defined(USE_USB_HOST)
    Serial.end();
    Serial.begin(SERIAL_OUT_BR, SERIAL_IN_BITS,
                 SOC_GPIO_PIN_T8_S2_CONS_RX, SOC_GPIO_PIN_T8_S2_CONS_TX);
#endif /* USE_USB_HOST */

#endif /* CONFIG_IDF_TARGET_ESP32S2 */

#if defined(CONFIG_IDF_TARGET_ESP32S3) || defined(CONFIG_IDF_TARGET_ESP32S31)
  } else if (hw_info.model == SOFTRF_MODEL_PRIME_MK3 ||
             esp32_board   == ESP32_S3_DEVKIT) {
    Wire1.begin(SOC_GPIO_PIN_S3_PMU_SDA , SOC_GPIO_PIN_S3_PMU_SCL);
    Wire1.beginTransmission(AXP2101_SLAVE_ADDRESS);
    bool has_axp2101 = (Wire1.endTransmission() == 0) &&
                       axp_2xxx.begin(Wire1, AXP2101_SLAVE_ADDRESS,
                                      SOC_GPIO_PIN_S3_PMU_SDA,
                                      SOC_GPIO_PIN_S3_PMU_SCL);
    if (has_axp2101) {
      esp32_board   = ESP32_TTGO_T_BEAM_SUPREME;
      hw_info.model = SOFTRF_MODEL_PRIME_MK3; /* allow psramFound() to fail */
      hw_info.pmu   = PMU_AXP2101;

      /* inactivate tinyUF2 LED output setting */
      pinMode(SOC_GPIO_PIN_S3_GNSS_PPS, INPUT);

      // Set the minimum common working voltage of the PMU VBUS input,
      // below this value will turn off the PMU
      axp_2xxx.setVbusVoltageLimit(XPOWERS_AXP2101_VBUS_VOL_LIM_4V36);

      // Set the maximum current of the PMU VBUS input,
      // higher than this value will turn off the PMU
      axp_2xxx.setVbusCurrentLimit(XPOWERS_AXP2101_VBUS_CUR_LIM_1500MA);

      // DCDC1 1500~3400mV, IMAX=2A
      axp_2xxx.setDC1Voltage(3300);

#if defined(USE_USB_HOST)
      // DCDC5 1400~3700mV, 100mV/step, 24 steps, IMAX=1A
      axp_2xxx.setDC5Voltage(3700);
#endif /* USE_USB_HOST */

      // ALDO 500~3500V, 100mV/step, IMAX=300mA
      axp_2xxx.setALDO3Voltage(3300); // LoRa, AXP2101 power-on value: 3300
      axp_2xxx.setALDO4Voltage(3300); // GNSS, AXP2101 power-on value: 2900

      axp_2xxx.setALDO2Voltage(3300); // RTC
      axp_2xxx.setALDO1Voltage(3300); // sensors, OLED
      axp_2xxx.setBLDO1Voltage(3300); // uSD

      // axp_2xxx.enableDC1();

#if defined(USE_USB_HOST)
      axp_2xxx.enableDC5();
#endif /* USE_USB_HOST */

      axp_2xxx.enableALDO3();
      axp_2xxx.enableALDO4();

      axp_2xxx.enableALDO2();
      axp_2xxx.enableALDO1();
      axp_2xxx.enableBLDO1();

      axp_2xxx.setChargingLedMode(XPOWERS_CHG_LED_ON);

      pinMode(SOC_GPIO_PIN_S3_PMU_IRQ, INPUT /* INPUT_PULLUP */);

      attachInterrupt(digitalPinToInterrupt(SOC_GPIO_PIN_S3_PMU_IRQ),
                      ESP32_PMU_Interrupt_handler, FALLING);

      axp_2xxx.disableIRQ(XPOWERS_AXP2101_ALL_IRQ);
      axp_2xxx.clearIrqStatus();

      axp_2xxx.setChargerConstantCurr(XPOWERS_AXP2101_CHG_CUR_500MA);
      axp_2xxx.disableTSPinMeasure();
      axp_2xxx.enableBattVoltageMeasure();

      axp_2xxx.enableIRQ(XPOWERS_AXP2101_PKEY_LONG_IRQ |
                         XPOWERS_AXP2101_PKEY_SHORT_IRQ);

      /* Wake up Quectel L76K GNSS */
      digitalWrite(SOC_GPIO_PIN_S3_GNSS_WAKE, HIGH);
      pinMode(SOC_GPIO_PIN_S3_GNSS_WAKE, OUTPUT);

      Wire1.beginTransmission(PCF8563_SLAVE_ADDRESS);
      bool esp32_has_rtc = (Wire1.endTransmission() == 0);
      if (!esp32_has_rtc) {
        delay(200);
        Wire1.beginTransmission(PCF8563_SLAVE_ADDRESS);
        esp32_has_rtc = (Wire1.endTransmission() == 0);
        if (!esp32_has_rtc) {
          delay(200);
          Wire1.beginTransmission(PCF8563_SLAVE_ADDRESS);
          esp32_has_rtc = (Wire1.endTransmission() == 0);
        }
      }

      i2c = new I2CBus(Wire1);

      if (esp32_has_rtc && (i2c != nullptr)) {
        rtc = new PCF8563_Class(*i2c);

        pinMode(SOC_GPIO_PIN_S3_RTC_IRQ, INPUT);
        hw_info.rtc = RTC_PCF8563;
      }

      /* wait until every LDO voltage will settle down */
      delay(200);

#if !defined(EXCLUDE_MAG)
      bool esp32_has_qmc10_u = false;
      bool esp32_has_qmc10_n = false;
#if SENSORLIB_VERSION >= SENSORLIB_VERSION_VAL(0, 4, 1)
      bool esp32_has_qmc9    = false;
#endif /* (0, 4, 1) */

      esp32_has_qmc10_u = mag_qmc6310.begin(Wire, QMC6310U_SLAVE_ADDRESS,
                                            SOC_GPIO_PIN_S3_SDA,
                                            SOC_GPIO_PIN_S3_SCL);
      if (esp32_has_qmc10_u) {
        hw_info.mag = MAG_QMC6310U;
      } else {
        esp32_has_qmc10_n = mag_qmc6310.begin(Wire, QMC6310N_SLAVE_ADDRESS,
                                              SOC_GPIO_PIN_S3_SDA,
                                              SOC_GPIO_PIN_S3_SCL);
        if (esp32_has_qmc10_n) {
          hw_info.mag = MAG_QMC6310N;
#if SENSORLIB_VERSION >= SENSORLIB_VERSION_VAL(0, 4, 1)
        } else {
          esp32_has_qmc9 = mag_qmc6309.begin(Wire, QMC6309_SLAVE_ADDRESS,
                                             SOC_GPIO_PIN_S3_SDA,
                                             SOC_GPIO_PIN_S3_SCL);
          if (esp32_has_qmc9) {
            hw_info.mag = MAG_QMC6309;
          }
#endif /* (0, 4, 1) */
        }
      }

      if (esp32_has_qmc10_u || esp32_has_qmc10_n) {
#if SENSORLIB_VERSION >= SENSORLIB_VERSION_VAL(0, 4, 1)
        mag_qmc6310.configMagnetometer(
            /*
            * Run Mode
            * MODE_SUSPEND
            * MODE_NORMAL
            * MODE_SINGLE
            * MODE_CONTINUOUS
            * * */
            OperationMode::NORMAL,
            /*
            * Full Range
            * RANGE_30G
            * RANGE_12G
            * RANGE_8G
            * RANGE_2G
            * * */
            MagFullScaleRange::FS_2G,
            /*
            * Output data rate
            * DATARATE_10HZ
            * DATARATE_50HZ
            * DATARATE_100HZ
            * DATARATE_200HZ
            * * */
            100.0f,
            /*
            * Over sample Ratio1
            * OSR_8
            * OSR_4
            * OSR_2
            * OSR_1
            * * * */
            MagOverSampleRatio::OSR_1,

            /*
            * Down sample Ratio1
            * DSR_8
            * DSR_4
            * DSR_2
            * DSR_1
            * * */
            MagDownSampleRatio::DSR_1);
#else
        mag_qmc6310.configMagnetometer(
            /*
            * Run Mode
            * MODE_SUSPEND
            * MODE_NORMAL
            * MODE_SINGLE
            * MODE_CONTINUOUS
            * * */
            SensorQMC6310::MODE_NORMAL,
            /*
            * Full Range
            * RANGE_30G
            * RANGE_12G
            * RANGE_8G
            * RANGE_2G
            * * */
            SensorQMC6310::RANGE_2G,
            /*
            * Output data rate
            * DATARATE_10HZ
            * DATARATE_50HZ
            * DATARATE_100HZ
            * DATARATE_200HZ
            * * */
            SensorQMC6310::DATARATE_100HZ,
            /*
            * Over sample Ratio1
            * OSR_8
            * OSR_4
            * OSR_2
            * OSR_1
            * * * */
            SensorQMC6310::OSR_1,

            /*
            * Down sample Ratio1
            * DSR_8
            * DSR_4
            * DSR_2
            * DSR_1
            * * */
            SensorQMC6310::DSR_1);
#endif /* (0, 4, 1) */
#if SENSORLIB_VERSION >= SENSORLIB_VERSION_VAL(0, 4, 1)
      } else if (esp32_has_qmc9) {
        mag_qmc6309.configMagnetometer(
            /*
            * Run Mode
            * MODE_SUSPEND
            * MODE_NORMAL
            * MODE_SINGLE
            * MODE_CONTINUOUS
            * * */
            OperationMode::NORMAL,
            /*
            * Full Range
            * RANGE_30G
            * RANGE_12G
            * RANGE_8G
            * RANGE_2G
            * * */
            MagFullScaleRange::FS_2G,
            /*
            * Output data rate
            * DATARATE_10HZ
            * DATARATE_50HZ
            * DATARATE_100HZ
            * DATARATE_200HZ
            * * */
            100.0f,
            /*
            * Over sample Ratio1
            * OSR_8
            * OSR_4
            * OSR_2
            * OSR_1
            * * * */
            MagOverSampleRatio::OSR_1,

            /*
            * Down sample Ratio1
            * DSR_8
            * DSR_4
            * DSR_2
            * DSR_1
            * * */
            MagDownSampleRatio::DSR_1);
#endif /* (0, 4, 1) */
      } else {
        WIRE_FINI(Wire);
      }

      MAG_Time_Marker = millis();
#endif /* EXCLUDE_MAG */

#if !defined(EXCLUDE_IMU)
      //imu_qmi8658.setSpiSetting(4000000, MSBFIRST, SPI_MODE0);
      bool has_qmi = imu_qmi8658.begin(uSD_SPI,
                                       SOC_GPIO_PIN_S3_IMU_SS,
                                       SOC_GPIO_PIN_S3_IMU_MOSI,
                                       SOC_GPIO_PIN_S3_IMU_MISO,
                                       SOC_GPIO_PIN_S3_IMU_SCK);
      if (has_qmi) {
        imu_qmi8658.configAccelerometer(
            /*
             * ACC_RANGE_2G
             * ACC_RANGE_4G
             * ACC_RANGE_8G
             * ACC_RANGE_16G
             * */
            SensorQMI8658::ACC_RANGE_4G,
            /*
             * ACC_ODR_1000H
             * ACC_ODR_500Hz
             * ACC_ODR_250Hz
             * ACC_ODR_125Hz
             * ACC_ODR_62_5Hz
             * ACC_ODR_31_25Hz
             * ACC_ODR_LOWPOWER_128Hz
             * ACC_ODR_LOWPOWER_21Hz
             * ACC_ODR_LOWPOWER_11Hz
             * ACC_ODR_LOWPOWER_3H
            * */
            SensorQMI8658::ACC_ODR_1000Hz,
            /*
            *  LPF_MODE_0     //2.66% of ODR
            *  LPF_MODE_1     //3.63% of ODR
            *  LPF_MODE_2     //5.39% of ODR
            *  LPF_MODE_3     //13.37% of ODR
            * */
            SensorQMI8658::LPF_MODE_0);

        imu_qmi8658.configGyroscope(
            /*
            * GYR_RANGE_16DPS
            * GYR_RANGE_32DPS
            * GYR_RANGE_64DPS
            * GYR_RANGE_128DPS
            * GYR_RANGE_256DPS
            * GYR_RANGE_512DPS
            * GYR_RANGE_1024DPS
            * */
            SensorQMI8658::GYR_RANGE_64DPS,
            /*
             * GYR_ODR_7174_4Hz
             * GYR_ODR_3587_2Hz
             * GYR_ODR_1793_6Hz
             * GYR_ODR_896_8Hz
             * GYR_ODR_448_4Hz
             * GYR_ODR_224_2Hz
             * GYR_ODR_112_1Hz
             * GYR_ODR_56_05Hz
             * GYR_ODR_28_025H
             * */
            SensorQMI8658::GYR_ODR_896_8Hz,
            /*
            *  LPF_MODE_0     //2.66% of ODR
            *  LPF_MODE_1     //3.63% of ODR
            *  LPF_MODE_2     //5.39% of ODR
            *  LPF_MODE_3     //13.37% of ODR
            * */
            SensorQMI8658::LPF_MODE_3);

        // In 3DOF mode,
        imu_qmi8658.enableAccelerometer();

        hw_info.imu = IMU_QMI8658;
      }

      IMU_Time_Marker = millis();

      if (hw_info.imu == IMU_NONE) {
        uSD_SPI.beginTransaction(SPISettings(1000000, MSBFIRST, SPI_MODE3));
        digitalWrite(SOC_GPIO_PIN_S3_IMU_SS, LOW);

        // reset device
        uSD_SPI.transfer(MPU6886_REG_PWR_MGMT_1);
        uSD_SPI.transfer(0x80);

        digitalWrite(SOC_GPIO_PIN_S3_IMU_SS, HIGH);
        uSD_SPI.endTransaction();

        delay(100);

        uSD_SPI.beginTransaction(SPISettings(1000000, MSBFIRST, SPI_MODE3));
        digitalWrite(SOC_GPIO_PIN_S3_IMU_SS, LOW);

        uSD_SPI.transfer(MPU6886_REG_WHOAMI | 0x80 /* read */);
        hw_info.imu = (uSD_SPI.transfer(0x00) ==  0x19) ? IMU_MPU6886 : IMU_NONE;

        digitalWrite(SOC_GPIO_PIN_S3_IMU_SS, HIGH);
        uSD_SPI.endTransaction();
      }

      uSD_SPI.end();
#endif /* EXCLUDE_IMU */
    } else {
      WIRE_FINI(Wire1);
      esp32_board      = ESP32_S3_DEVKIT;
      hw_info.model    = SOFTRF_MODEL_STANDALONE;
      hw_info.revision = STD_EDN_REV_S3_DEVKIT;

#if !defined(EXCLUDE_IMU)
#if 0
      uSD_SPI.begin(SOC_GPIO_PIN_S3_IMU_SCK,
                    SOC_GPIO_PIN_S3_IMU_MISO,
                    SOC_GPIO_PIN_S3_IMU_MOSI,
                    SOC_GPIO_PIN_S3_IMU_SS);
      uSD_SPI.setHwCs(false);

      pinMode(SOC_GPIO_PIN_S3_IMU_SS, OUTPUT);
      digitalWrite(SOC_GPIO_PIN_S3_IMU_SS, HIGH);

      delay(50);

      uSD_SPI.beginTransaction(SPISettings(1000000, MSBFIRST, SPI_MODE3));
      digitalWrite(SOC_GPIO_PIN_S3_IMU_SS, LOW);

      // reset device
      uSD_SPI.transfer(MPU9250_REG_PWR_MGMT_1);
      uSD_SPI.transfer(0x80);

      digitalWrite(SOC_GPIO_PIN_S3_IMU_SS, HIGH);
      uSD_SPI.endTransaction();

      delay(100);

      uSD_SPI.beginTransaction(SPISettings(1000000, MSBFIRST, SPI_MODE3));
      digitalWrite(SOC_GPIO_PIN_S3_IMU_SS, LOW);

      uSD_SPI.transfer(MPU9250_REG_WHOAMI | 0x80 /* read */);
      uint8_t whoami = uSD_SPI.transfer(0x00);
      hw_info.imu = (whoami == 0x71 || whoami == 0x73) ? IMU_MPU9250 : IMU_NONE;

      digitalWrite(SOC_GPIO_PIN_S3_IMU_SS, HIGH);
      uSD_SPI.endTransaction();

      uSD_SPI.end();

      hw_info.mag = (hw_info.imu == IMU_MPU9250) ? MAG_AK8963 : hw_info.mag;
#endif
#endif /* EXCLUDE_IMU */
    }

#if ARDUINO_USB_CDC_ON_BOOT
    SerialOutput.begin(SERIAL_OUT_BR, SERIAL_OUT_BITS,
                       SOC_GPIO_PIN_S3_CONS_RX,
                       SOC_GPIO_PIN_S3_CONS_TX);
#endif /* ARDUINO_USB_CDC_ON_BOOT */

    lmic_pins.nss  = SOC_GPIO_PIN_S3_SS;
    lmic_pins.rst  = SOC_GPIO_PIN_S3_RST;
    lmic_pins.busy = SOC_GPIO_PIN_S3_BUSY;

#if defined(USE_RADIOLIB)
    if (esp32_board == ESP32_TTGO_T_BEAM_SUPREME) {
      /* reserved for DIO 11 of HPD-16E */
      lmic_pins.dio[0] = SOC_GPIO_PIN_S3_DIO1;
    }
#endif /* USE_RADIOLIB */

    int uSD_SS_pin = (esp32_board == ESP32_S3_DEVKIT) ?
                     SOC_GPIO_PIN_S3_SD_SS_DK : SOC_GPIO_PIN_S3_SD_SS_TBEAM;

    /* uSD-SPI init */
    uSD_SPI.begin(SOC_GPIO_PIN_S3_SD_SCK,
                  SOC_GPIO_PIN_S3_SD_MISO,
                  SOC_GPIO_PIN_S3_SD_MOSI,
                  uSD_SS_pin);

    pinMode(uSD_SS_pin, OUTPUT);
    digitalWrite(uSD_SS_pin, HIGH);

    uSD_is_attached = uSD.cardBegin(SD_CONFIG);

  } else if (hw_info.model == SOFTRF_MODEL_HAM) {
    Wire.begin(SOC_GPIO_PIN_TWR2_SDA , SOC_GPIO_PIN_TWR2_SCL);
    Wire.beginTransmission(AXP2101_SLAVE_ADDRESS);
    bool has_axp2101 = (Wire.endTransmission() == 0) &&
                       axp_2xxx.begin(Wire, AXP2101_SLAVE_ADDRESS,
                                      SOC_GPIO_PIN_TWR2_SDA,
                                      SOC_GPIO_PIN_TWR2_SCL);
    if (has_axp2101) {
      esp32_board      = ESP32_LILYGO_T_TWR2;
      hw_info.revision = 0;
      hw_info.pmu      = PMU_AXP2101;

      // Set the minimum common working voltage of the PMU VBUS input,
      // below this value will turn off the PMU
      axp_2xxx.setVbusVoltageLimit(XPOWERS_AXP2101_VBUS_VOL_LIM_4V36);

      // Set the maximum current of the PMU VBUS input,
      // higher than this value will turn off the PMU
      axp_2xxx.setVbusCurrentLimit(XPOWERS_AXP2101_VBUS_CUR_LIM_1500MA);

      // DCDC1 1500~3400mV, IMAX=2A
      axp_2xxx.setDC1Voltage(3300); // WROOM, OLED

      // ALDO 500~3500V, 100mV/step, IMAX=300mA
      axp_2xxx.setALDO2Voltage(3300); // micro-SD
      axp_2xxx.setALDO4Voltage(3300); // GNSS, AXP2101 power-on value: 2900

      axp_2xxx.setBLDO1Voltage(3300); // Mic

      // axp_2xxx.enableDC1();

      axp_2xxx.enableALDO2();  // Rev2.x - micro-SD Card LDO
      axp_2xxx.enableALDO4();  // Rev2.x - GNSS LDO

      axp_2xxx.enableBLDO1();  // Rev2.x - Microphone LDO

      axp_2xxx.disableBLDO2(); // Rev2.1 - SA8x8 DC boost , Rev2.0 - user LDO
      axp_2xxx.disableALDO3(); // Rev2.1 - Audio amp. switch , Rev2.0 - user LDO
      axp_2xxx.disableDLDO1(); // Rev2.1 - Download switch control
      axp_2xxx.disableDC3();   // Rev2.0 - SA8x8 DC boost , Rev2.1 - user LDO

      // The following supply voltages can be controlled by the user
      axp_2xxx.disableALDO1();
      axp_2xxx.disableDC5();

      // The following power supplies are unavailable
      axp_2xxx.disableDC2();
      axp_2xxx.disableDC4();
      axp_2xxx.disableCPUSLDO();
      axp_2xxx.disableDLDO2();

      axp_2xxx.setChargingLedMode(XPOWERS_CHG_LED_ON);

      pinMode(SOC_GPIO_PIN_TWR2_PMU_IRQ, INPUT /* INPUT_PULLUP */);

      attachInterrupt(digitalPinToInterrupt(SOC_GPIO_PIN_TWR2_PMU_IRQ),
                      ESP32_PMU_Interrupt_handler, FALLING);

      axp_2xxx.disableIRQ(XPOWERS_AXP2101_ALL_IRQ);
      axp_2xxx.clearIrqStatus();

      axp_2xxx.setChargerConstantCurr(XPOWERS_AXP2101_CHG_CUR_500MA);
      axp_2xxx.disableTSPinMeasure();
      axp_2xxx.enableBattVoltageMeasure();

      axp_2xxx.enableIRQ(XPOWERS_AXP2101_PKEY_LONG_IRQ |
                         XPOWERS_AXP2101_PKEY_SHORT_IRQ);

      /* wait until every LDO voltage will settle down */
      delay(200);

      lmic_pins.nss  = SOC_GPIO_PIN_TWR2_SS;
      lmic_pins.rst  = SOC_UNUSED_PIN;
      lmic_pins.busy = SOC_UNUSED_PIN;

#if defined(USE_NEOPIXELBUS_LIBRARY)
      TWR2_Pixel.Begin();
      TWR2_Pixel.Show(); // Initialize all pixels to 'off'
#endif /* USE_NEOPIXELBUS_LIBRARY */
#if defined(USE_ADAFRUIT_NEO_LIBRARY)
      TWR2_Pixel.begin();
      TWR2_Pixel.show(); // Initialize all pixels to 'off'
#endif /* USE_ADAFRUIT_NEO_LIBRARY */

    } else {
      WIRE_FINI(Wire);

      esp32_board      = ESP32_TTGO_T_BEAM_1W;
      hw_info.model    = SOFTRF_MODEL_PRIME_MK4;
      hw_info.revision = 1; /* PCB 1.1 */

      lmic_pins.nss  = SOC_GPIO_PIN_1W_SS;
      lmic_pins.rst  = SOC_GPIO_PIN_1W_RST;
      lmic_pins.busy = SOC_GPIO_PIN_1W_BUSY;

      lmic_pins.rxe  = SOC_GPIO_PIN_1W_ANT_RX;
#if defined(USE_RADIOLIB)
      lmic_pins.dio[0] = SOC_GPIO_PIN_1W_DIO11;
#endif /* USE_RADIOLIB */
    }

#if ARDUINO_USB_CDC_ON_BOOT
    SerialOutput.begin(SERIAL_OUT_BR, SERIAL_OUT_BITS,
                       SOC_GPIO_PIN_TWR2_CONS_RX,
                       SOC_GPIO_PIN_TWR2_CONS_TX);
#endif /* ARDUINO_USB_CDC_ON_BOOT */

    if (esp32_board == ESP32_LILYGO_T_TWR2) {
      int uSD_SS_pin = SOC_GPIO_PIN_TWR2_SD_SS;

      /* uSD-SPI init */
      uSD_SPI.begin(SOC_GPIO_PIN_TWR2_SD_SCK,
                    SOC_GPIO_PIN_TWR2_SD_MISO,
                    SOC_GPIO_PIN_TWR2_SD_MOSI,
                    uSD_SS_pin);

      pinMode(uSD_SS_pin, OUTPUT);
      digitalWrite(uSD_SS_pin, HIGH);

      uSD_is_attached = uSD.cardBegin(SD_CONFIG);

#if defined(USE_SA8X8)
      uint64_t mac = ESP.getEfuseMac();
      if (mac == 0x7475ac188534ULL /* || mac == 0x58f8ab188534ULL */) {
        ESP32_R22_workaround = true;
      }
#endif /* USE_SA8X8 */

#if !defined(EXCLUDE_VOICE_MESSAGE)
      if (uSD_is_attached && uSD.card()->cardSize() > 0 && uSD.volumeBegin()) {
        Audio_Gen    = new AudioGeneratorWAV();
        Audio_Source = new AudioFileSourceSdFat(uSD);

        Audio_Sink   = new AudioOutputI2S(0, AudioOutputI2S::INTERNAL_PDM);
        Audio_Sink->SetPinout(I2S_PIN_NO_CHANGE,
                              I2S_PIN_NO_CHANGE,
                              SOC_GPIO_PIN_TWR2_PDM_OUT,
                              I2S_PIN_NO_CHANGE);
        Audio_Sink->SetOutputModeMono(true);
        Audio_Sink->SetChannels(1);
        Audio_Sink->SetGain(/* 0.0625 */ 0.125 /* 0.25 */);
        Audio_Sink->SetMclk(false);
        playback_inited = true;
      }
#endif /* EXCLUDE_VOICE_MESSAGE */
    } else if (esp32_board == ESP32_TTGO_T_BEAM_1W) {
      int uSD_SS_pin = SOC_GPIO_PIN_1W_SD_SS;

      /* uSD-SPI init */
      SPI.begin(SOC_GPIO_PIN_1W_SD_SCK, SOC_GPIO_PIN_1W_SD_MISO,
                SOC_GPIO_PIN_1W_SD_MOSI, uSD_SS_pin);

      pinMode(uSD_SS_pin, OUTPUT);
      digitalWrite(uSD_SS_pin, HIGH);

      uSD_is_attached = uSD.cardBegin(SdSpiConfig(uSD_SS_pin, SHARED_SPI,
                                                  SD_SCK_MHZ(8), &SPI));
    }
  } else if (hw_info.model == SOFTRF_MODEL_MIDI) {

#if defined(ESP_IDF_VERSION_MAJOR) && ESP_IDF_VERSION_MAJOR >= 5
    #define BOARD_F_XTAL_MHZ 26

    rtc_clk_xtal_freq_update((rtc_xtal_freq_t) BOARD_F_XTAL_MHZ);
    rtc_clk_cpu_freq_set_xtal();
#endif /* ESP_IDF_VERSION_MAJOR */

#if ARDUINO_USB_CDC_ON_BOOT
    SerialOutput.begin(SERIAL_OUT_BR, SERIAL_OUT_BITS,
                       SOC_GPIO_PIN_S3_CONS_RX,
                       SOC_GPIO_PIN_S3_CONS_TX);
#endif /* ARDUINO_USB_CDC_ON_BOOT */

    lmic_pins.nss  = SOC_GPIO_PIN_HELTRK_SS;
    lmic_pins.rst  = SOC_GPIO_PIN_HELTRK_RST;
    lmic_pins.busy = SOC_GPIO_PIN_HELTRK_BUSY;

  } else if (esp32_board == ESP32_LILYGO_T3S3_EPD) {

    pinMode(SOC_GPIO_PIN_EHUB_OLED_3V3, INPUT_PULLDOWN);
    pinMode(SOC_GPIO_PIN_EHUB_OLED_RST, INPUT_PULLDOWN);

    delay(150);

    Wire1.begin(SOC_GPIO_PIN_EHUB_OLED_SDA , SOC_GPIO_PIN_EHUB_OLED_SCL);
    Wire1.beginTransmission(SSD1306_OLED_I2C_ADDR);
    bool off_oled_is_active = (Wire1.endTransmission() == 0);

    pinMode(SOC_GPIO_PIN_EHUB_OLED_3V3, INPUT);
    pinMode(SOC_GPIO_PIN_EHUB_OLED_RST, INPUT);

    delay(150);

    Wire1.beginTransmission(SSD1306_OLED_I2C_ADDR);
    bool on_oled_is_active = (Wire1.endTransmission() == 0);

    WIRE_FINI(Wire1);

    if (off_oled_is_active == false && on_oled_is_active == true) {

      esp32_board      = ESP32_EBYTE_HUB_900TB;
      hw_info.model    = SOFTRF_MODEL_STANDALONE;
      hw_info.revision = STD_EDN_REV_EHUB; /* 10722-V1.1 */

#if ARDUINO_USB_CDC_ON_BOOT
      SerialOutput.begin(SERIAL_OUT_BR, SERIAL_OUT_BITS,
                         SOC_GPIO_PIN_EHUB_CONS_RX,
                         SOC_GPIO_PIN_EHUB_CONS_TX);
#endif /* ARDUINO_USB_CDC_ON_BOOT */

      lmic_pins.nss  = SOC_GPIO_PIN_EHUB_SS;
      lmic_pins.rst  = SOC_GPIO_PIN_EHUB_RST;
      lmic_pins.busy = SOC_GPIO_PIN_EHUB_BUSY;
#if defined(USE_RADIOLIB)
      lmic_pins.dio[0] = SOC_GPIO_PIN_EHUB_DIO9;
#endif /* USE_RADIOLIB */

    } else {

      if (off_oled_is_active) {
        esp32_board      = ESP32_LILYGO_T3S3_OLED;
        hw_info.model    = SOFTRF_MODEL_STANDALONE;
        hw_info.revision = STD_EDN_REV_T3S3_OLED; /* V1.2 V1.3 */
      } else {
        hw_info.model    = SOFTRF_MODEL_INK;
        hw_info.revision = 0; /* 2024-02-28 */
      }

#if ARDUINO_USB_CDC_ON_BOOT
      SerialOutput.begin(SERIAL_OUT_BR, SERIAL_OUT_BITS,
                         SOC_GPIO_PIN_T3S3_CONS_RX,
                         SOC_GPIO_PIN_T3S3_CONS_TX);
#endif /* ARDUINO_USB_CDC_ON_BOOT */

      lmic_pins.nss  = SOC_GPIO_PIN_T3S3_SS;
      lmic_pins.rst  = SOC_GPIO_PIN_T3S3_RST;
      lmic_pins.busy = SOC_GPIO_PIN_T3S3_BUSY;
   // lmic_pins.txe  = SOC_GPIO_PIN_T3S3_ANT_TX;
   // lmic_pins.rxe  = SOC_GPIO_PIN_T3S3_ANT_RX;
#if defined(USE_RADIOLIB)
      lmic_pins.dio[0] = SOC_GPIO_PIN_T3S3_DIO1;
#endif /* USE_RADIOLIB */

      int uSD_SS_pin = SOC_GPIO_PIN_T3S3_SD_SS;

      /* uSD-SPI init */
      uSD_SPI.begin(SOC_GPIO_PIN_T3S3_SD_SCK,
                    SOC_GPIO_PIN_T3S3_SD_MISO,
                    SOC_GPIO_PIN_T3S3_SD_MOSI,
                    uSD_SS_pin);

      pinMode(uSD_SS_pin, OUTPUT);
      digitalWrite(uSD_SS_pin, HIGH);

      uSD_is_attached = uSD.cardBegin(SD_CONFIG);
    }
  } else if (esp32_board == ESP32_BANANA_PICOW) {

    hw_info.model    = SOFTRF_MODEL_STANDALONE;
    hw_info.revision = STD_EDN_REV_BPICOW; /* 2022-08-22 */

#if ARDUINO_USB_CDC_ON_BOOT
    SerialOutput.begin(SERIAL_OUT_BR, SERIAL_OUT_BITS,
                       SOC_GPIO_PIN_BPIPW_CONS_RX,
                       SOC_GPIO_PIN_BPIPW_CONS_TX);
#endif /* ARDUINO_USB_CDC_ON_BOOT */

    lmic_pins.nss  = SOC_GPIO_PIN_BPIPW_SS;
    lmic_pins.rst  = SOC_GPIO_PIN_BPIPW_RST;
    lmic_pins.busy = SOC_GPIO_PIN_BPIPW_BUSY;
    // lmic_pins.rxe  = SOC_GPIO_PIN_BPIPW_ANT_RXTX; /* RXEN */
#if defined(USE_RADIOLIB)
    lmic_pins.dio[0] = SOC_GPIO_PIN_BPIPW_DIO1;
#endif /* USE_RADIOLIB */

  } else if (esp32_board == ESP32_ELECROW_TN_M5) {

    pinMode(SOC_GPIO_PIN_M2_VEXT_EN, INPUT_PULLUP); /* M2 OLED PWR */
    delay(150);
    Wire1.begin(SOC_GPIO_PIN_M2_OLED_SDA, SOC_GPIO_PIN_M2_OLED_SCL);
    Wire1.beginTransmission(SH1106_OLED_I2C_ADDR);
    bool has_oled = (Wire1.endTransmission() == 0);
    pinMode(SOC_GPIO_PIN_M2_VEXT_EN, INPUT);
    WIRE_FINI(Wire1);

    if (has_oled) {
      esp32_board      = ESP32_ELECROW_TN_M2;
      hw_info.model    = SOFTRF_MODEL_GIZMO;
      hw_info.revision = 0; /* TBD */

#if ARDUINO_USB_CDC_ON_BOOT
      SerialOutput.begin(SERIAL_OUT_BR, SERIAL_OUT_BITS,
                         SOC_GPIO_PIN_M2_CONS_RX,
                         SOC_GPIO_PIN_M2_CONS_TX);
#endif /* ARDUINO_USB_CDC_ON_BOOT */

      lmic_pins.nss  = SOC_GPIO_PIN_M2_SS;
      lmic_pins.rst  = SOC_GPIO_PIN_M2_RST;
      lmic_pins.busy = SOC_GPIO_PIN_M2_BUSY;
#if defined(USE_RADIOLIB)
      lmic_pins.dio[0] = SOC_GPIO_PIN_M2_DIO1;
#endif /* USE_RADIOLIB */
    } else {
      hw_info.model    = SOFTRF_MODEL_AIRVENTURE;
      hw_info.revision = 1; /* PCB 1.0 */

#if ARDUINO_USB_CDC_ON_BOOT
      SerialOutput.begin(SERIAL_OUT_BR, SERIAL_OUT_BITS,
                         SOC_GPIO_PIN_M5_CONS_RX,
                         SOC_GPIO_PIN_M5_CONS_TX);
#endif /* ARDUINO_USB_CDC_ON_BOOT */

      lmic_pins.nss  = SOC_GPIO_PIN_M5_SS;
      lmic_pins.rst  = SOC_GPIO_PIN_M5_RST;
      lmic_pins.busy = SOC_GPIO_PIN_M5_BUSY;
#if defined(USE_RADIOLIB)
      lmic_pins.dio[0] = SOC_GPIO_PIN_M5_DIO1;
#endif /* USE_RADIOLIB */

      /* EPD-SPI init */
      uSD_SPI.begin(SOC_GPIO_PIN_M5_EPD_SCK,
                    SOC_GPIO_PIN_M5_EPD_MISO,
                    SOC_GPIO_PIN_M5_EPD_MOSI,
                    SOC_GPIO_PIN_M5_EPD_SS);

      Wire1.begin(SOC_GPIO_PIN_M5_SDA2, SOC_GPIO_PIN_M5_SCL2);
      Wire1.beginTransmission(PCA9557_ADDRESS);
      ESP32_has_gpio_extension = (Wire1.endTransmission() == 0);

      if (ESP32_has_gpio_extension) {
        pca9557 = new PCA9557(PCA9557_ADDRESS, &Wire1);
      } else {
        WIRE_FINI(Wire1);
      }
    }
#endif /* CONFIG_IDF_TARGET_ESP32S3-S31 */

#if defined(CONFIG_IDF_TARGET_ESP32C2)
  } else if (esp32_board == ESP32_C2_DEVKIT) {

    lmic_pins.nss  = SOC_GPIO_PIN_C2_SS;
    lmic_pins.rst  = SOC_GPIO_PIN_C2_RST;
    lmic_pins.busy = SOC_GPIO_PIN_C2_TXE;

#endif /* CONFIG_IDF_TARGET_ESP32C2 */

#if defined(CONFIG_IDF_TARGET_ESP32C3)
  } else if (esp32_board == ESP32_C3_DEVKIT) {

#if ARDUINO_USB_CDC_ON_BOOT
    SerialOutput.begin(SERIAL_OUT_BR, SERIAL_OUT_BITS,
                       SOC_GPIO_PIN_C3_CONS_RX,
                       SOC_GPIO_PIN_C3_CONS_TX);
#endif /* ARDUINO_USB_CDC_ON_BOOT */

    lmic_pins.nss  = SOC_GPIO_PIN_C3_SS;
    lmic_pins.rst  = SOC_GPIO_PIN_C3_RST;
    lmic_pins.busy = SOC_GPIO_PIN_C3_TXE;
#if defined(USE_RADIOLIB) || defined(USE_RADIOHEAD)
    lmic_pins.dio[0] = SOC_GPIO_PIN_C3_CE;
#endif /* USE_RADIOLIB || USE_RADIOHEAD */

  } else if (esp32_board == ESP32_RADIOMASTER_XR1) {
    hw_info.model    = SOFTRF_MODEL_NANO;
    hw_info.revision = 1;

    lmic_pins.nss  = SOC_GPIO_PIN_ELRS_SS;
    lmic_pins.rst  = SOC_GPIO_PIN_ELRS_RST;
    lmic_pins.busy = SOC_GPIO_PIN_ELRS_BUSY;
#if defined(USE_RADIOLIB) || defined(USE_RADIOHEAD)
    lmic_pins.dio[0] = SOC_GPIO_PIN_ELRS_DIO9;
#endif /* USE_RADIOLIB || USE_RADIOHEAD */
#endif /* CONFIG_IDF_TARGET_ESP32C3 */

#if defined(CONFIG_IDF_TARGET_ESP32C5)
  } else if (esp32_board == ESP32_C5_DEVKIT) {

    hw_info.revision = STD_EDN_REV_C5_DEVKIT;

#if ARDUINO_USB_CDC_ON_BOOT
    SerialOutput.begin(SERIAL_OUT_BR, SERIAL_OUT_BITS,
                       SOC_GPIO_PIN_C5_CONS_RX,
                       SOC_GPIO_PIN_C5_CONS_TX);
    SerialOutput.setTxBufferSize(1024);
#endif /* ARDUINO_USB_CDC_ON_BOOT */

    lmic_pins.nss  = SOC_GPIO_PIN_C5_SS;
    lmic_pins.rst  = SOC_GPIO_PIN_C5_RST;
    lmic_pins.busy = SOC_GPIO_PIN_C5_BUSY;
#if defined(USE_RADIOLIB) || defined(USE_RADIOHEAD)
    lmic_pins.dio[0] = SOC_GPIO_PIN_C5_DIO;
#endif /* USE_RADIOLIB || USE_RADIOHEAD */
#endif /* CONFIG_IDF_TARGET_ESP32C5 */

#if defined(CONFIG_IDF_TARGET_ESP32C6)
  } else if (esp32_board == ESP32_C6_DEVKIT) {

#if ARDUINO_USB_CDC_ON_BOOT
    SerialOutput.begin(SERIAL_OUT_BR, SERIAL_OUT_BITS,
                       SOC_GPIO_PIN_C6_CONS_RX,
                       SOC_GPIO_PIN_C6_CONS_TX);
#endif /* ARDUINO_USB_CDC_ON_BOOT */

    lmic_pins.nss  = SOC_GPIO_PIN_C6_SS;
    lmic_pins.rst  = SOC_GPIO_PIN_C6_RST;
    lmic_pins.busy = SOC_GPIO_PIN_C6_TXE;
#if defined(USE_RADIOLIB) || defined(USE_RADIOHEAD)
    lmic_pins.dio[0] = SOC_GPIO_PIN_C6_CE;
#endif /* USE_RADIOLIB || USE_RADIOHEAD */

  } else if (esp32_board == ESP32_LILYGO_T3C6) {

    hw_info.model  = SOFTRF_MODEL_ECO;

#if ARDUINO_USB_CDC_ON_BOOT
    SerialOutput.begin(SERIAL_OUT_BR, SERIAL_OUT_BITS,
                       SOC_GPIO_PIN_T3C6_CONS_RX,
                       SOC_GPIO_PIN_T3C6_CONS_TX);
#endif /* ARDUINO_USB_CDC_ON_BOOT */

    lmic_pins.nss  = SOC_GPIO_PIN_T3C6_SS;
    lmic_pins.rst  = SOC_GPIO_PIN_T3C6_RST;
    lmic_pins.busy = SOC_GPIO_PIN_T3C6_BUSY;
    lmic_pins.txe  = SOC_GPIO_PIN_T3C6_ANT_TX;
    lmic_pins.rxe  = SOC_GPIO_PIN_T3C6_ANT_RX;
#endif /* CONFIG_IDF_TARGET_ESP32C6 */

#if defined(CONFIG_IDF_TARGET_ESP32P4)
  } else if (esp32_board == ESP32_P4_WT_DEVKIT) {

    hw_info.model    = SOFTRF_MODEL_STANDALONE;
    hw_info.revision = STD_EDN_REV_WT99P4C5;

#if 0
    pinMode(SOC_GPIO_PIN_P4_WS_RST,  OUTPUT);
    pinMode(SOC_GPIO_PIN_P4_WS_BUSY, INPUT);

    digitalWrite(SOC_GPIO_PIN_P4_WS_RST, LOW);

    delay(10);

    if (digitalRead(SOC_GPIO_PIN_P4_WS_BUSY) == HIGH) {
      digitalWrite(SOC_GPIO_PIN_P4_WS_RST, HIGH);

      delay(50);

      if (digitalRead(SOC_GPIO_PIN_P4_WS_BUSY) == LOW) {
        hw_info.revision = STD_EDN_REV_P4_EVB;
      }
    }

    pinMode(SOC_GPIO_PIN_P4_WS_RST, INPUT);
#endif

    switch (hw_info.revision)
    {
      case STD_EDN_REV_P4_EVB:
        lmic_pins.nss    = SOC_GPIO_PIN_P4_WS_SS;
        lmic_pins.rst    = SOC_GPIO_PIN_P4_WS_RST;
        lmic_pins.busy   = SOC_GPIO_PIN_P4_WS_BUSY;
        //if (SoC->getChipId() != 0xD3374780) {
        //  lmic_pins.tcxo = lmic_pins.rst; /* SX1262 with XTAL */
        //}
#if defined(USE_RADIOLIB) || defined(USE_RADIOHEAD)
        lmic_pins.dio[0] = SOC_GPIO_PIN_P4_WS_DIO;
#endif /* USE_RADIOLIB || USE_RADIOHEAD */
        break;

      case STD_EDN_REV_WT99P4C5:
      default:
        pinMode(SOC_GPIO_PIN_P4_485_RW,      OUTPUT);
        digitalWrite(SOC_GPIO_PIN_P4_485_RW, HIGH);

#if ARDUINO_USB_CDC_ON_BOOT
        SerialOutput.begin(SERIAL_OUT_BR, SERIAL_OUT_BITS,
                           SOC_GPIO_PIN_P4_CONS_RX,
                           SOC_GPIO_PIN_P4_CONS_TX);
#endif /* ARDUINO_USB_CDC_ON_BOOT */

        lmic_pins.nss  = SOC_GPIO_PIN_P4_SS;
        lmic_pins.rst  = SOC_GPIO_PIN_P4_RST;
        lmic_pins.busy = SOC_GPIO_PIN_P4_BUSY;
#if defined(USE_RADIOLIB) || defined(USE_RADIOHEAD)
        lmic_pins.dio[0] = SOC_GPIO_PIN_P4_DIO;
#endif /* USE_RADIOLIB || USE_RADIOHEAD */
        break;
    }

#if SOC_SDMMC_IO_POWER_EXTERNAL
    esp_ldo_channel_handle_t ldo_sdio = NULL;
    esp_ldo_channel_config_t ldo_sdio_config = {
        .chan_id = BOARD_SDMMC_POWER_CHANNEL,
        .voltage_mv = 3300,
    };
    esp_ldo_acquire_channel(&ldo_sdio_config, &ldo_sdio);
#endif /* SOC_SDMMC_IO_POWER_EXTERNAL */

    int uSD_SS_pin = SOC_GPIO_PIN_P4_SD_D3;

    /* uSD-SPI init */
    uSD_SPI.begin(SOC_GPIO_PIN_P4_SD_CLK,
                  SOC_GPIO_PIN_P4_SD_D0,
                  SOC_GPIO_PIN_P4_SD_CMD,
                  uSD_SS_pin);

    pinMode(uSD_SS_pin, OUTPUT);
    digitalWrite(uSD_SS_pin, HIGH);

    pinMode(SOC_GPIO_PIN_P4_SD_DET, INPUT);

    uSD_is_attached = uSD.cardBegin(SD_CONFIG);

#if !defined(EXCLUDE_VOICE_MESSAGE)
    if (uSD_is_attached && uSD.card()->cardSize() > 0 && uSD.volumeBegin()) {
      Audio_Gen    = new AudioGeneratorWAV();
      Audio_Source = new AudioFileSourceSdFat(uSD);

      Audio_Sink   = new AudioOutputI2S(0, AudioOutputI2S::EXTERNAL_I2S);
      Audio_Sink->SetPinout(SOC_GPIO_PIN_P4_I2S_BCK,
                            SOC_GPIO_PIN_P4_I2S_LRCK,
                            SOC_GPIO_PIN_P4_I2S_DOUT,
                            SOC_GPIO_PIN_P4_I2S_MCK);
      Audio_Sink->SetOutputModeMono(true);
      Audio_Sink->SetChannels(1);
      Audio_Sink->SetGain(1.0);
      Audio_Sink->SetMclk(true);

      Wire.begin(SOC_GPIO_PIN_P4_SDA, SOC_GPIO_PIN_P4_SCL);
      es8311_codec_init(0);

      playback_inited = true;
    }
#endif /* EXCLUDE_VOICE_MESSAGE */
  } else if (esp32_board == ESP32_LILYGO_TDISPLAY_P4) {
    hw_info.model = SOFTRF_MODEL_CONCORDE;

    TDP4_IIC_1.begin(SOC_GPIO_PIN_TDP4_SDA_1, SOC_GPIO_PIN_TDP4_SCL_1);
    TDP4_IIC_1.beginTransmission(BQ27220_SLAVE_ADDRESS);
    bool has_bq27220 = (TDP4_IIC_1.endTransmission() == 0);
    if (has_bq27220 && bq_27220.begin(TDP4_IIC_1,
                                      SOC_GPIO_PIN_TDP4_SDA_1,
                                      SOC_GPIO_PIN_TDP4_SCL_1)) {
      hw_info.pmu  = BMU_BQ27220;
    }

    lmic_pins.nss  = SOC_GPIO_PIN_TDP4_SS;
    lmic_pins.rst  = SOC_GPIO_PIN_TDP4_RST;
    lmic_pins.busy = SOC_GPIO_PIN_TDP4_BUSY;
#if defined(USE_RADIOLIB) || defined(USE_RADIOHEAD)
    lmic_pins.dio[0] = SOC_GPIO_PIN_TDP4_DIO;
#endif /* USE_RADIOLIB || USE_RADIOHEAD */

    pinMode(SOC_GPIO_PIN_TDP4_XL9_INT, INPUT);

    xl9535 = new ExtensionIOXL9555();
    ESP32_has_gpio_extension = xl9535->begin(TDP4_IIC_1, XL9535_ADDRESS,
                                             SOC_GPIO_PIN_TDP4_SDA_1,
                                             SOC_GPIO_PIN_TDP4_SCL_1);
    if (ESP32_has_gpio_extension) {
      /* make GNSS inactive prior to 3.3V power ON */
      xl9535->pinMode(ExtensionIOXL9555::SOC_EXPIO_TDP4_GNSS_WKE, OUTPUT);
      xl9535->digitalWrite(ExtensionIOXL9555::SOC_EXPIO_TDP4_GNSS_WKE, LOW);

      /* make ESP32-C6 inactive prior to 3.3V power ON */
      xl9535->pinMode(ExtensionIOXL9555::SOC_EXPIO_TDP4_SLAVE_EN, OUTPUT);
      xl9535->digitalWrite(ExtensionIOXL9555::SOC_EXPIO_TDP4_SLAVE_EN, LOW);

      /* USB PHY power */
      xl9535->pinMode(ExtensionIOXL9555::SOC_EXPIO_TDP4_VCCA_EN,  OUTPUT);
      xl9535->digitalWrite(ExtensionIOXL9555::SOC_EXPIO_TDP4_VCCA_EN,  LOW);


      xl9535->pinMode(ExtensionIOXL9555::SOC_EXPIO_TDP4_3V3_EN,   OUTPUT);
      xl9535->pinMode(ExtensionIOXL9555::SOC_EXPIO_TDP4_5V0_EN,   OUTPUT);
      /*
       * Turn ON power of
       * GNSS, TFT back light, ESP32-C6,
       * camera (SGM38121), haptic (AW86224), IMU (ICM20948),
       * ETH PHY and ES8311 digital circuits
       */
      xl9535->digitalWrite(ExtensionIOXL9555::SOC_EXPIO_TDP4_3V3_EN,   LOW);

      /* Power of NS4150 audio amp. and ES8311 analog circuits */
      xl9535->digitalWrite(ExtensionIOXL9555::SOC_EXPIO_TDP4_5V0_EN,   HIGH);

      /* Power of micro-SD */
      xl9535->pinMode(ExtensionIOXL9555::SOC_EXPIO_TDP4_SD_EN,    OUTPUT);
      xl9535->digitalWrite(ExtensionIOXL9555::SOC_EXPIO_TDP4_SD_EN,    LOW);
    }

#if SOC_SDMMC_IO_POWER_EXTERNAL
    esp_ldo_channel_handle_t ldo_sdio = NULL;
    esp_ldo_channel_config_t ldo_sdio_config = {
        .chan_id = BOARD_SDMMC_POWER_CHANNEL,
        .voltage_mv = 3300,
    };
    esp_ldo_acquire_channel(&ldo_sdio_config, &ldo_sdio);
#endif /* SOC_SDMMC_IO_POWER_EXTERNAL */

    int uSD_SS_pin = SOC_GPIO_PIN_TDP4_SD_D3;

    /* uSD-SPI init */
    uSD_SPI.begin(SOC_GPIO_PIN_TDP4_SD_CLK,
                  SOC_GPIO_PIN_TDP4_SD_D0,
                  SOC_GPIO_PIN_TDP4_SD_CMD,
                  uSD_SS_pin);

    pinMode(uSD_SS_pin, OUTPUT);
    digitalWrite(uSD_SS_pin, HIGH);

    uSD_is_attached = uSD.cardBegin(SD_CONFIG);

#if !defined(EXCLUDE_VOICE_MESSAGE)
    if (uSD_is_attached && uSD.card()->cardSize() > 0 && uSD.volumeBegin()) {
      Audio_Gen    = new AudioGeneratorWAV();
      Audio_Source = new AudioFileSourceSdFat(uSD);

      Audio_Sink   = new AudioOutputI2S(0, AudioOutputI2S::EXTERNAL_I2S);
      Audio_Sink->SetPinout(SOC_GPIO_PIN_TDP4_I2S_BCK,
                            SOC_GPIO_PIN_TDP4_I2S_LRCK,
                            SOC_GPIO_PIN_TDP4_I2S_DOUT,
                            SOC_GPIO_PIN_TDP4_I2S_MCK);
      Audio_Sink->SetOutputModeMono(true);
      Audio_Sink->SetChannels(1);
      Audio_Sink->SetGain(1.0);
      Audio_Sink->SetMclk(true);

      TDP4_IIC_2.begin(SOC_GPIO_PIN_TDP4_SDA_2, SOC_GPIO_PIN_TDP4_SCL_2);
      es8311_codec_init(TDP4_ES8311_IIC);

      playback_inited = true;
    }
#endif /* EXCLUDE_VOICE_MESSAGE */
#endif /* CONFIG_IDF_TARGET_ESP32P4 */
  }

#if defined(CONFIG_IDF_TARGET_ESP32S3)  || \
    defined(CONFIG_IDF_TARGET_ESP32S31) || \
    defined(CONFIG_IDF_TARGET_ESP32P4)
  ESP32_has_spiflash = SPIFlash->begin(possible_devices,
                                       EXTERNAL_FLASH_DEVICE_COUNT);
  if (ESP32_has_spiflash) {
    const esp_partition_t *fat_p;
    fat_p = esp_partition_find_first(ESP_PARTITION_TYPE_DATA,
                                     ESP_PARTITION_SUBTYPE_DATA_FAT,
                                     NULL);
    uint32_t capacity = ESP32_getFlashId() & 0xFF;

    if (fat_p && capacity >= 0x17) { /* equal or greater than 1UL << 23 (8 MiB) */
      hw_info.storage = STORAGE_FLASH;

#if CONFIG_TINYUSB_MSC_ENABLED
  #if defined(USE_ADAFRUIT_MSC)
      // Set disk vendor id, product id and revision
      // with string up to 8, 16, 4 characters respectively
      usb_msc.setID(ESP32SX_Device_Manufacturer, "Internal Flash", "1.0");

      // Set callback
      usb_msc.setReadWriteCallback(ESP32_msc_read_cb,
                                   ESP32_msc_write_cb,
                                   ESP32_msc_flush_cb);

      // Set disk size, block size should be 512 regardless of spi flash page size
      usb_msc.setCapacity(SPIFlash->size()/512, 512);

      // MSC is ready for read/write
      usb_msc.setUnitReady(true);

      usb_msc.begin();

  #else

      // Set disk vendor id, product id and revision
      // with string up to 8, 16, 4 characters respectively
      usb_msc.vendorID(ESP32SX_Device_Manufacturer);
      usb_msc.productID("Internal Flash");
      usb_msc.productRevision("1.0");

      // Set callback
      usb_msc.onRead(ESP32_msc_read_cb);
      usb_msc.onWrite(ESP32_msc_write_cb);

      // MSC is ready for read/write
      usb_msc.mediaPresent(true);

      // Set disk size, block size should be 512 regardless of spi flash page size
      usb_msc.begin(SPIFlash->size()/512, 512);
  #endif /* USE_ADAFRUIT_MSC */
#endif /* CONFIG_TINYUSB_MSC_ENABLED */

      FATFS_is_mounted = fatfs.begin(SPIFlash);
    }
  }

  if (uSD_is_attached && uSD.card()->cardSize() > 0) {
    hw_info.storage = (hw_info.storage == STORAGE_FLASH) ?
                      STORAGE_FLASH_AND_CARD : STORAGE_CARD;

    if (esp32_board == ESP32_LILYGO_TDISPLAY_P4 &&
        hw_info.storage == STORAGE_CARD) {
      if ( false           ||
#if !defined(EXCLUDE_VOICE_MESSAGE)
           playback_inited ||
#endif /* EXCLUDE_VOICE_MESSAGE */
           uSD.volumeBegin()) {
        FATFS_is_mounted = fatfs.begin(uSD.card());
      }
    }
  }
#endif /* CONFIG_IDF_TARGET_ESP32S3-P4 */

#if ARDUINO_USB_CDC_ON_BOOT && \
    (defined(CONFIG_IDF_TARGET_ESP32S2)  || \
     defined(CONFIG_IDF_TARGET_ESP32S3)  || \
     defined(CONFIG_IDF_TARGET_ESP32S31) || \
     defined(CONFIG_IDF_TARGET_ESP32P4))
#if CONFIG_TINYUSB_ENABLED
  if (USB.manufacturerName(ESP32SX_Device_Manufacturer)) {
    char usb_serial_number[16];
    uint16_t pid;

    pid = (esp32_board == ESP32_TTGO_T_BEAM_SUPREME) ? SOFTRF_USB_PID_PRIME_MK3  :
          (esp32_board == ESP32_S2_T8_V1_1         ) ? SOFTRF_USB_PID_WEBTOP     :
          (esp32_board == ESP32_S3_DEVKIT          ) ? SOFTRF_USB_PID_STANDALONE :
          (esp32_board == ESP32_LILYGO_T_TWR2      ) ? SOFTRF_USB_PID_HAM        :
          (esp32_board == ESP32_HELTEC_TRACKER     ) ? SOFTRF_USB_PID_MIDI       :
          (esp32_board == ESP32_LILYGO_T3S3_EPD    ) ? SOFTRF_USB_PID_INK        :
          (esp32_board == ESP32_BANANA_PICOW       ) ? SOFTRF_USB_PID_STANDALONE :
          (esp32_board == ESP32_ELECROW_TN_M2      ) ? SOFTRF_USB_PID_GIZMO      :
          (esp32_board == ESP32_ELECROW_TN_M5      ) ? SOFTRF_USB_PID_AIRVENTURE :
          (esp32_board == ESP32_EBYTE_HUB_900TB    ) ? SOFTRF_USB_PID_STANDALONE :
          (esp32_board == ESP32_P4_WT_DEVKIT       ) ? SOFTRF_USB_PID_STANDALONE :
          (esp32_board == ESP32_P4_WS_DEVKIT       ) ? SOFTRF_USB_PID_STANDALONE :
          (esp32_board == ESP32_LILYGO_TDISPLAY_P4 ) ? SOFTRF_USB_PID_CONCORDE   :
          (esp32_board == ESP32_TTGO_T_BEAM_1W     ) ? SOFTRF_USB_PID_PRIME_MK4  :
          USB_PID /* 0x1001 */ ;

    snprintf(usb_serial_number, sizeof(usb_serial_number),
             "%02X%02X%02X%02X%02X%02X",
             efuse_mac[0], efuse_mac[1], efuse_mac[2],
             efuse_mac[3], efuse_mac[4], efuse_mac[5]);

    USB.VID(USB_VID); // USB_ESPRESSIF_VID = 0x303A
    USB.PID(pid);
    USB.productName(esp32_board == ESP32_TTGO_T_BEAM_SUPREME ? ESP32S3_Model_Prime3  :
                    esp32_board == ESP32_LILYGO_T_TWR2       ? ESP32S3_Model_Ham     :
                    esp32_board == ESP32_HELTEC_TRACKER      ? ESP32S3_Model_Midi    :
                    esp32_board == ESP32_LILYGO_T3S3_EPD     ? ESP32S3_Model_Ink     :
                    esp32_board == ESP32_ELECROW_TN_M2       ? ESP32S3_Model_Gizmo   :
                    esp32_board == ESP32_ELECROW_TN_M5       ? ESP32S3_Model_AirVent :
                    esp32_board == ESP32_LILYGO_TDISPLAY_P4  ? ESP32P4_Model_Concord :
                    esp32_board == ESP32_TTGO_T_BEAM_1W      ? ESP32S3_Model_Prime4  :
                    ESP32SX_Model_Stand);
    USB.firmwareVersion(ESP32SX_Device_Version);
    USB.serialNumber(usb_serial_number);
    if (esp32_board != ESP32_ELECROW_TN_M5) {
      USB.begin();
    }
  }
#endif /* CONFIG_TINYUSB_ENABLED */

  Serial.begin(SERIAL_OUT_BR);

  for (int i=0; i < 20; i++) {if (Serial) break; else delay(100);}

#if 0 /* TBD */
  if (Serial.rebootEnabled()) {
    Serial.enableReboot(false);
  }
#endif /* TBD */

#elif ARDUINO_USB_CDC_ON_BOOT && \
      (defined(CONFIG_IDF_TARGET_ESP32C3)  || \
       defined(CONFIG_IDF_TARGET_ESP32C5)  || \
       defined(CONFIG_IDF_TARGET_ESP32C6)  || \
       defined(CONFIG_IDF_TARGET_ESP32C61) || \
       defined(CONFIG_IDF_TARGET_ESP32H2)  || \
       defined(CONFIG_IDF_TARGET_ESP32H4))

  Serial.begin(SERIAL_OUT_BR);

  for (int i=0; i < 20; i++) {if (Serial) break; else delay(100);}

#else
  Serial.begin(SERIAL_OUT_BR, SERIAL_OUT_BITS);
#endif /* ARDUINO_USB_CDC_ON_BOOT */

#if defined(CONFIG_IDF_TARGET_ESP32S3) || defined(CONFIG_IDF_TARGET_ESP32S31)
  ui = &ui_settings;

  if (esp32_board == ESP32_TTGO_T_BEAM_SUPREME)
  {
    rtc_clk_32k_enable(true);

    CALIBRATE_ONE(RTC_CAL_RTC_MUX);
    uint32_t cal_32k = CALIBRATE_ONE(RTC_CAL_32K_XTAL);

    if (cal_32k == 0) {
        DEBUG_X32K("32K XTAL OSC has not started up");
    } else {
        rtc_clk_slow_freq_set(RTC_SLOW_FREQ_32K_XTAL);
        DEBUG_X32K("Switching of RTC clock source onto 32768 Hz XTAL is successful.");
        CALIBRATE_ONE(RTC_CAL_RTC_MUX);
        CALIBRATE_ONE(RTC_CAL_32K_XTAL);
    }
    CALIBRATE_ONE(RTC_CAL_RTC_MUX);
    CALIBRATE_ONE(RTC_CAL_32K_XTAL);
    if (rtc_clk_slow_freq_get() != RTC_SLOW_FREQ_32K_XTAL) {
        DEBUG_X32K("Warning: Failed to switch RTC clock source onto 32768 Hz XTAL !");
    } else {
        ESP32_has_32k_xtal = true;
    }
#if !defined(EXCLUDE_IMU)
    if (hw_info.imu             == IMU_QMI8658 /* && */
     /* rtc_get_reset_reason(0) == POWERON_RESET */) {
      for (int i=0; i<50; i++) {
        if (imu_qmi8658.getDataReady()) {
          float a_x, a_y, a_z;
          if (imu_qmi8658.getAccelerometer(a_x, a_y, a_z)) {
            if (a_x > OLED_FLIP_THRESHOLD) {
#if defined(USE_OLED)
              OLED_flip = 1;
#endif /* USE_OLED */
            }
          }
          break;
        } else {
          delay(10);
        }
      }
    }
#endif /* EXCLUDE_IMU */
  } else if (esp32_board == ESP32_LILYGO_T_TWR2) {

    /* turn SA868 digital power off to make sure that SQL is inactive */
    digitalWrite(SOC_GPIO_PIN_TWR2_RADIO_PD, LOW);
    pinMode(SOC_GPIO_PIN_TWR2_RADIO_PD, OUTPUT);

    delay(200);

    bool probe_1 = false;
    bool probe_2 = false;

    pinMode(SOC_GPIO_PIN_TWR2_RADIO_SQL, INPUT_PULLDOWN);
    delay(20);

    probe_1 = digitalRead(SOC_GPIO_PIN_TWR2_RADIO_SQL);

    /* turn SA868 digital power on */
    digitalWrite(SOC_GPIO_PIN_TWR2_RADIO_PD, HIGH);

    delay(200);

    probe_2 = digitalRead(SOC_GPIO_PIN_TWR2_RADIO_SQL);

    if (probe_1 == LOW && probe_2 == HIGH) {
      hw_info.revision = 1;

      axp_2xxx.setBLDO2Voltage(3300); // V2.1 - SA868
      axp_2xxx.enableBLDO2();
      axp_2xxx.setALDO3Voltage(3300); // V2.1 - Amp. OE Ctrl

#if defined(USE_SA8X8)
      for (uint8_t addr = 1; addr < 127; addr++) {
          Wire.beginTransmission(addr);
          if (Wire.endTransmission() == 0) {
              switch (addr) {
              case SH1106_OLED_I2C_ADDR:
                  controller.setBand(Band::VHF);
                  addr = 127;
                  break;
              case SH1106_OLED_I2C_ADDR_ALT:
                  controller.setBand(Band::UHF);
                  addr = 127;
                  break;
              default:
                  break;
              }
          }
      }
#endif /* USE_SA8X8 */
    } else {
      axp_2xxx.setDC3Voltage  (3400); // V2.0 - SA868, NeoPixel
      axp_2xxx.enableDC3();

      pinMode(SOC_GPIO_PIN_TWR2_RADIO_HL, OUTPUT_OPEN_DRAIN);
      digitalWrite(SOC_GPIO_PIN_TWR2_RADIO_HL, LOW);
    }

    pinMode(SOC_GPIO_PIN_TWR2_RADIO_SQL, INPUT);

    digitalWrite(SOC_GPIO_PIN_TWR2_RADIO_PTT, HIGH);
    pinMode(SOC_GPIO_PIN_TWR2_RADIO_PTT,  INPUT_PULLUP);
    pinMode(SOC_GPIO_PIN_TWR2_MIC_CH_SEL, INPUT_PULLUP);

  } else if (esp32_board == ESP32_TTGO_T_BEAM_1W) {

    /* Wake up Quectel L76K GNSS */
    digitalWrite(SOC_GPIO_PIN_1W_GNSS_WAKE, HIGH);
    pinMode(SOC_GPIO_PIN_1W_GNSS_WAKE, OUTPUT);

    /* turn on the radio power */
    digitalWrite(SOC_GPIO_PIN_1W_PWR_EN, HIGH);
    pinMode(SOC_GPIO_PIN_1W_PWR_EN, OUTPUT);

    /* turn on radio cooling fan */
    digitalWrite(SOC_GPIO_PIN_1W_FAN, HIGH);
    pinMode(SOC_GPIO_PIN_1W_FAN, OUTPUT);

    pinMode(SOC_GPIO_PIN_1W_BUTTON_2, INPUT);

    /* enforce discharge of C15 and C16 capacitors when battery is NC */
    pinMode(SOC_GPIO_PIN_1W_BATTERY, OUTPUT);
    digitalWrite(SOC_GPIO_PIN_1W_BATTERY, LOW);
    delay(300);
    pinMode(SOC_GPIO_PIN_1W_BATTERY, INPUT);

  } else if (esp32_board == ESP32_HELTEC_TRACKER) {

    rtc_clk_32k_enable(true);

    CALIBRATE_ONE(RTC_CAL_RTC_MUX);
    uint32_t cal_32k = CALIBRATE_ONE(RTC_CAL_32K_XTAL);

    if (cal_32k == 0) {
        DEBUG_X32K("32K XTAL OSC has not started up");
    } else {
        rtc_clk_slow_freq_set(RTC_SLOW_FREQ_32K_XTAL);
        DEBUG_X32K("Switching of RTC clock source onto 32768 Hz XTAL is successful.");
        CALIBRATE_ONE(RTC_CAL_RTC_MUX);
        CALIBRATE_ONE(RTC_CAL_32K_XTAL);
    }
    CALIBRATE_ONE(RTC_CAL_RTC_MUX);
    CALIBRATE_ONE(RTC_CAL_32K_XTAL);
    if (rtc_clk_slow_freq_get() != RTC_SLOW_FREQ_32K_XTAL) {
        DEBUG_X32K("Warning: Failed to switch RTC clock source onto 32768 Hz XTAL !");
        rtc_clk_32k_enable(false);
    } else {
        ESP32_has_32k_xtal = true;
    }

    hw_info.revision = ESP32_has_32k_xtal ? 5 : 3;

    bool ESP32_has_SubGHzFE = false;

    if (ESP32_has_32k_xtal) {
      pinMode(SOC_GPIO_PIN_HELTRK_VFEM_EN, INPUT_PULLDOWN);
      pinMode(SOC_GPIO_PIN_HELTRK_PA_CSD,  INPUT_PULLUP);
      pinMode(SOC_GPIO_PIN_HELTRK_PA_CTX,  INPUT_PULLUP);

      delay(1);

      if (digitalRead(SOC_GPIO_PIN_HELTRK_PA_CSD) == LOW &&
          digitalRead(SOC_GPIO_PIN_HELTRK_PA_CTX) == LOW) {
        ESP32_has_SubGHzFE = true;
        hw_info.revision = 23; /* V2.3 PCB marking */
      }

      pinMode(SOC_GPIO_PIN_HELTRK_PA_CSD,  INPUT);
      pinMode(SOC_GPIO_PIN_HELTRK_PA_CTX,  INPUT);
      pinMode(SOC_GPIO_PIN_HELTRK_VFEM_EN, INPUT);
    }

    switch (hw_info.revision) {
      case 3:
        digitalWrite(SOC_GPIO_PIN_HELTRK_GNSS_EN, LOW);
        digitalWrite(SOC_GPIO_PIN_HELTRK_TFT_EN,  LOW);
        digitalWrite(SOC_GPIO_PIN_HELTRK_VEXT_EN, LOW);

        pinMode(SOC_GPIO_PIN_HELTRK_GNSS_EN, INPUT_PULLDOWN);
        delay(300);
        pinMode(SOC_GPIO_PIN_HELTRK_GNSS_EN, OUTPUT);
        pinMode(SOC_GPIO_PIN_HELTRK_TFT_EN,  OUTPUT);
        break;

      case 23:
        digitalWrite(SOC_GPIO_PIN_HELTRK_VEXT_EN, HIGH);

        pinMode(SOC_GPIO_PIN_HELTRK_VFEM_EN, INPUT_PULLUP);
        delay(1);
        pinMode(SOC_GPIO_PIN_HELTRK_PA_CSD,  OUTPUT);
        digitalWrite(SOC_GPIO_PIN_HELTRK_PA_CSD, HIGH);

        pinMode(SOC_GPIO_PIN_HELTRK_PA_CTX,  OUTPUT);
        digitalWrite(SOC_GPIO_PIN_HELTRK_PA_CTX, HIGH); // Receive Bypass Mode
        break;

      case 5:
      default:
        digitalWrite(SOC_GPIO_PIN_HELTRK_VEXT_EN, HIGH);
        break;
    }

    pinMode(SOC_GPIO_PIN_HELTRK_VEXT_EN,   OUTPUT);

    if (rtc_get_reset_reason(0) == POWERON_RESET) {
      digitalWrite(SOC_GPIO_PIN_HELTRK_GNSS_RST, LOW);
      pinMode(SOC_GPIO_PIN_HELTRK_GNSS_RST,      OUTPUT);
      delay(100);
      digitalWrite(SOC_GPIO_PIN_HELTRK_GNSS_RST, HIGH);
    }

    pinMode(SOC_GPIO_PIN_HELTRK_ADC_EN,    INPUT_PULLUP);

    digitalWrite(SOC_GPIO_PIN_HELTRK_LED,  LOW);
    pinMode(SOC_GPIO_PIN_HELTRK_LED,       OUTPUT);

  } else if (esp32_board == ESP32_LILYGO_T3S3_EPD ||
             esp32_board == ESP32_LILYGO_T3S3_OLED) {

    gpio_deep_sleep_hold_dis();
    gpio_hold_dis(GPIO_NUM_35);
    pinMode(SOC_GPIO_PIN_T3S3_3V3EN,       INPUT_PULLUP);

    digitalWrite(SOC_GPIO_PIN_T3S3_LED,    LOW);
    pinMode(SOC_GPIO_PIN_T3S3_LED,         OUTPUT);

  } else if (esp32_board == ESP32_BANANA_PICOW) {

    digitalWrite(SOC_GPIO_PIN_BPIPW_STATUS, LOW);
    pinMode(SOC_GPIO_PIN_BPIPW_STATUS,     OUTPUT);

  } else if (esp32_board == ESP32_ELECROW_TN_M2) {

    gpio_hold_dis((gpio_num_t) SOC_GPIO_PIN_M2_SS);

    pinMode(SOC_GPIO_PIN_M2_LED_PWR,       INPUT_PULLUP); /* status LED */
    digitalWrite(SOC_GPIO_PIN_M2_LED,      LOW);
    pinMode(SOC_GPIO_PIN_M2_LED,           OUTPUT);

    pinMode(SOC_GPIO_PIN_M2_VEXT_EN,       INPUT_PULLUP); /* OLED */
    /* sub-1 GHz radio */
#if 1
    pinMode(SOC_GPIO_PIN_M2_PWR_EN,        INPUT_PULLUP);
#else
    digitalWrite(SOC_GPIO_PIN_M2_PWR_EN,   HIGH);
    pinMode(SOC_GPIO_PIN_M2_PWR_EN,        OUTPUT);
#endif

  } else if (esp32_board == ESP32_ELECROW_TN_M5) {

    gpio_hold_dis((gpio_num_t) SOC_GPIO_PIN_M5_SS);
    gpio_hold_dis((gpio_num_t) SOC_GPIO_PIN_M5_GNSS_WKE);

    if (ESP32_has_gpio_extension) {
      pca9557->pinMode(SOC_EXPIO_LED_M5_RED_PWR,      OUTPUT); /* status LED */
      pca9557->digitalWrite(SOC_EXPIO_LED_M5_RED_PWR, HIGH);
      pca9557->pinMode(SOC_EXPIO_LED_M5_RED,          OUTPUT);
      pca9557->digitalWrite(SOC_EXPIO_LED_M5_RED,     LOW);

      pca9557->pinMode(SOC_EXPIO_LED_M5_BLUE,         OUTPUT);
      pca9557->digitalWrite(SOC_EXPIO_LED_M5_BLUE,    HIGH);

      pca9557->pinMode(SOC_EXPIO_PIN_M5_IO_EN,        OUTPUT);
      pca9557->pinMode(SOC_EXPIO_PIN_M5_EPD_EN,       OUTPUT);
      pca9557->digitalWrite(SOC_EXPIO_PIN_M5_IO_EN,   HIGH);
      pca9557->digitalWrite(SOC_EXPIO_PIN_M5_EPD_EN,  HIGH);
    }

    /* Wake up Quectel L76K GNSS */
    digitalWrite(SOC_GPIO_PIN_M5_GNSS_RST,            HIGH);
    pinMode(SOC_GPIO_PIN_M5_GNSS_RST,                 OUTPUT);
    digitalWrite(SOC_GPIO_PIN_M5_GNSS_WKE,            HIGH);
    pinMode(SOC_GPIO_PIN_M5_GNSS_WKE,                 OUTPUT);

    Wire.begin(SOC_GPIO_PIN_M5_SDA, SOC_GPIO_PIN_M5_SCL);
    Wire.beginTransmission(PCF8563_SLAVE_ADDRESS);
    bool esp32_has_rtc = (Wire.endTransmission() == 0);
    if (!esp32_has_rtc) {
      delay(200);
      Wire.beginTransmission(PCF8563_SLAVE_ADDRESS);
      esp32_has_rtc = (Wire.endTransmission() == 0);
      if (!esp32_has_rtc) {
        delay(200);
        Wire.beginTransmission(PCF8563_SLAVE_ADDRESS);
        esp32_has_rtc = (Wire.endTransmission() == 0);
      }
    }

    i2c = new I2CBus(Wire);

    if (esp32_has_rtc && (i2c != nullptr)) {
      rtc = new PCF8563_Class(*i2c);

      pinMode(SOC_GPIO_PIN_M5_RTC_INT, INPUT);
      hw_info.rtc = RTC_PCF8563;
    }

    /* TBD */
    // digitalWrite(SOC_GPIO_PIN_M5_DIO3,           HIGH);
    // pinMode(SOC_GPIO_PIN_M5_DIO3,                OUTPUT);

  } else if (esp32_board == ESP32_EBYTE_HUB_900TB) {

    digitalWrite(SOC_GPIO_PIN_EHUB_LED,    LOW);
    pinMode(SOC_GPIO_PIN_EHUB_LED,         OUTPUT);

    pinMode(SOC_GPIO_PIN_EHUB_OLED_3V3,    INPUT_PULLUP); /* OLED */
    pinMode(SOC_GPIO_PIN_EHUB_OLED_RST,    INPUT_PULLUP);

    digitalWrite(SOC_GPIO_PIN_EHUB_VBAT_EN, LOW);
    pinMode(SOC_GPIO_PIN_EHUB_VBAT_EN,     OUTPUT);

    rtc_clk_32k_enable(true);

    CALIBRATE_ONE(RTC_CAL_RTC_MUX);
    uint32_t cal_32k = CALIBRATE_ONE(RTC_CAL_32K_XTAL);

    if (cal_32k == 0) {
        DEBUG_X32K("32K XTAL OSC has not started up");
    } else {
        rtc_clk_slow_freq_set(RTC_SLOW_FREQ_32K_XTAL);
        DEBUG_X32K("Switching of RTC clock source onto 32768 Hz XTAL is successful.");
        CALIBRATE_ONE(RTC_CAL_RTC_MUX);
        CALIBRATE_ONE(RTC_CAL_32K_XTAL);
    }
    CALIBRATE_ONE(RTC_CAL_RTC_MUX);
    CALIBRATE_ONE(RTC_CAL_32K_XTAL);
    if (rtc_clk_slow_freq_get() != RTC_SLOW_FREQ_32K_XTAL) {
        DEBUG_X32K("Warning: Failed to switch RTC clock source onto 32768 Hz XTAL !");
        rtc_clk_32k_enable(false);
    } else {
        ESP32_has_32k_xtal = true;
    }
  } else {
#if !defined(EXCLUDE_IMU)
    Wire.begin(SOC_GPIO_PIN_S3_SDA, SOC_GPIO_PIN_S3_SCL);
    Wire.beginTransmission(MPU9250_ADDRESS);
    bool has_mpu = (Wire.endTransmission() == 0);

    if (has_mpu && imu_mpu9250.setup(MPU9250_ADDRESS)) {
      imu_mpu9250.verbose(false);
      if (imu_mpu9250.isSleeping()) {
        imu_mpu9250.sleep(false);
      }
      hw_info.imu = IMU_MPU9250;
      IMU_Time_Marker = millis();
    } else {
      WIRE_FINI(Wire);
    }

    hw_info.mag = (hw_info.imu == IMU_MPU9250) ? MAG_AK8963 : hw_info.mag;
#endif /* EXCLUDE_IMU */
  }
#endif /* CONFIG_IDF_TARGET_ESP32S3-S31 */

#if defined(CONFIG_IDF_TARGET_ESP32C3) || defined(CONFIG_IDF_TARGET_ESP32)
  if (esp32_board == ESP32_RADIOMASTER_XR1 ||
      esp32_board == ESP32_LILYGO_T_ELRS) {
#if SOC_GPIO_PIN_ELRS_LED != SOC_UNUSED_PIN
    digitalWrite(SOC_GPIO_PIN_ELRS_LED, LED_STATE_ON);
    pinMode(SOC_GPIO_PIN_ELRS_LED,      OUTPUT);
#endif /* SOC_GPIO_PIN_ELRS_LED */

#if defined(USE_NEOPIXELBUS_LIBRARY)
    XR1_Pixel.Begin();
    XR1_Pixel.Show(); // Initialize all pixels to 'off'
    XR1_Pixel.SetPixelColor(0, LED_COLOR_GREEN);
    XR1_Pixel.Show();
#endif /* USE_NEOPIXELBUS_LIBRARY */
#if defined(USE_ADAFRUIT_NEO_LIBRARY)
    XR1_Pixel.begin();
    XR1_Pixel.show(); // Initialize all pixels to 'off'
    XR1_Pixel.setPixelColor(0, LED_COLOR_GREEN);
    XR1_Pixel.show();
#endif /* USE_ADAFRUIT_NEO_LIBRARY */
  }
#endif /* CONFIG_IDF_TARGET_ESP32C3 */

#if defined(CONFIG_IDF_TARGET_ESP32P4)
  ui = &ui_settings;

  if (esp32_board == ESP32_P4_WT_DEVKIT) {
    pinMode(SOC_GPIO_PIN_P4_PAMP_CTRL,      OUTPUT);
    digitalWrite(SOC_GPIO_PIN_P4_PAMP_CTRL, HIGH);

#if !defined(EXCLUDE_ETHERNET)
    Ethernet_setup();

    ETH.begin(ETH_PHY_TYPE,
              ETH_PHY_ADDR,
              SOC_GPIO_PIN_P4_ETH_PHY_MDC,
              SOC_GPIO_PIN_P4_ETH_PHY_MDIO,
              SOC_GPIO_PIN_P4_ETH_PHY_POWER,
              ETH_CLK_MODE);
#endif /* EXCLUDE_ETHERNET */

    Wire.begin(SOC_GPIO_PIN_P4_SDA, SOC_GPIO_PIN_P4_SCL);
    Wire.beginTransmission(ES8311_ADDRRES_0);
    if (Wire.endTransmission() == 0) {
      hw_info.audio = AUDIO_ES8311;
    }

    Wire.beginTransmission(GT911_SLAVE_ADDRESS_L);
    if (Wire.endTransmission() == 0) {
      hw_info.touch = TOUCH_GT911;
    }

    Wire.beginTransmission(OV5647_ADDRESS);
    if (Wire.endTransmission() == 0) {
#if defined(USE_CAMERA)
      esp32p4_cam_config_t cfg = esp32p4_cam_config_board(ESP32P4_BOARD_CUSTOM);
      cfg.wire = &Wire;
      cfg.sda = SOC_GPIO_PIN_P4_SDA;
      cfg.scl = SOC_GPIO_PIN_P4_SCL;
      cfg.pixel_format = ESP32P4_PIXFORMAT_RGB565;
      cfg.sensor = ESP32P4_SENSOR_OV5647;
      cfg.frame_size = ESP32P4_FRAMESIZE_VGA;

      if (cam.begin(cfg)) {
        hw_info.camera = CAMERA_OV5647;
      } else {
        Serial.println("ERROR: OV5647 camera init failure");
      }
#else
      hw_info.camera = CAMERA_OV5647;
#endif /* USE_CAMERA */
    }
  } else if (esp32_board == ESP32_LILYGO_TDISPLAY_P4) {

    if (ESP32_has_gpio_extension) {
      /* Wake up Quectel L76K GNSS */
      xl9535->digitalWrite(ExtensionIOXL9555::SOC_EXPIO_TDP4_GNSS_WKE, HIGH);

      xl9535->pinMode(ExtensionIOXL9555::SOC_EXPIO_TDP4_DSI_RST,   OUTPUT);
      xl9535->pinMode(ExtensionIOXL9555::SOC_EXPIO_TDP4_TP_RST,    OUTPUT);
      xl9535->digitalWrite(ExtensionIOXL9555::SOC_EXPIO_TDP4_DSI_RST,  HIGH);
      xl9535->digitalWrite(ExtensionIOXL9555::SOC_EXPIO_TDP4_TP_RST,   HIGH);

      delay(200);

      xl9535->digitalWrite(ExtensionIOXL9555::SOC_EXPIO_TDP4_SLAVE_EN, HIGH);

      xl9535->pinMode(ExtensionIOXL9555::SOC_EXPIO_TDP4_TP_INT,    INPUT);
      xl9535->pinMode(ExtensionIOXL9555::SOC_EXPIO_TDP4_SENS_INT,  INPUT);
      xl9535->pinMode(ExtensionIOXL9555::SOC_EXPIO_TDP4_RADIO_DIO, INPUT);

      /* Select antenna input ( SKY13453 ) */
      xl9535->pinMode(ExtensionIOXL9555::SOC_EXPIO_TDP4_RFSW_VCTL, OUTPUT);
      // RF1 (internal)
//    xl9535->digitalWrite(ExtensionIOXL9555::SOC_EXPIO_TDP4_RFSW_VCTL, HIGH);
      // RF2 (external)
      xl9535->digitalWrite(ExtensionIOXL9555::SOC_EXPIO_TDP4_RFSW_VCTL, LOW);
    }

    TDP4_IIC_1.begin(SOC_GPIO_PIN_TDP4_SDA_1, SOC_GPIO_PIN_TDP4_SCL_1);
    TDP4_IIC_1.beginTransmission(PCF8563_SLAVE_ADDRESS);
    bool esp32_has_rtc = (TDP4_IIC_1.endTransmission() == 0);
    if (!esp32_has_rtc) {
      delay(200);
      TDP4_IIC_1.beginTransmission(PCF8563_SLAVE_ADDRESS);
      esp32_has_rtc = (TDP4_IIC_1.endTransmission() == 0);
      if (!esp32_has_rtc) {
        delay(200);
        TDP4_IIC_1.beginTransmission(PCF8563_SLAVE_ADDRESS);
        esp32_has_rtc = (TDP4_IIC_1.endTransmission() == 0);
      }
    }

    i2c = new I2CBus(TDP4_IIC_1);

    if (esp32_has_rtc && (i2c != nullptr)) {
      rtc = new PCF8563_Class(*i2c);

      if (ESP32_has_gpio_extension) {
        xl9535->pinMode(ExtensionIOXL9555::SOC_EXPIO_TDP4_RTC_INT, INPUT);
      }
      hw_info.rtc = RTC_PCF8563;
    }

#if !defined(EXCLUDE_IMU)
    TDP4_IIC_2.begin(SOC_GPIO_PIN_TDP4_SDA_2, SOC_GPIO_PIN_TDP4_SCL_2);

    bool ad0 = (ICM20948_ADDRESS == 0x69) ? true : false;
    int t;
    for (t=0; t<3; t++) {
      if (imu_icm20948.begin(TDP4_IIC_2, ad0) == ICM_20948_Stat_Ok) {
        hw_info.imu = IMU_ICM20948;
        hw_info.mag = MAG_AK09916;
        IMU_Time_Marker = millis();

        break;
      }
      delay(IMU_UPDATE_INTERVAL);
    }

    if (t == 4) {
      WIRE_FINI(TDP4_IIC_2);
    }
#endif /* EXCLUDE_IMU */

#if !defined(EXCLUDE_ETHERNET)
    Ethernet_setup();

    ETH.begin(ETH_PHY_TYPE_TDP4,
              ETH_PHY_ADDR,
              SOC_GPIO_PIN_TDP4_ETH_PHY_MDC,
              SOC_GPIO_PIN_TDP4_ETH_PHY_MDIO,
              SOC_GPIO_PIN_TDP4_ETH_PHY_RST,
              ETH_CLK_MODE);
#endif /* EXCLUDE_ETHERNET */

    TDP4_IIC_1.beginTransmission(GT9895_ADDRESS);
    if (TDP4_IIC_1.endTransmission() == 0) {
      hw_info.revision = 1;
      hw_info.touch    = TOUCH_GT9895;
    }
#if 1 /* TODO */
    else {
      hw_info.revision = 0;
      hw_info.touch    = TOUCH_JD9365TG;
    }
#else
    TDP4_IIC_1.beginTransmission(HI8561_ADDRESS);
    if (TDP4_IIC_1.endTransmission() == 0) {
      hw_info.revision = 0;
      hw_info.touch    = TOUCH_JD9365TG;
    }
#endif

    TDP4_IIC_2.beginTransmission(ES8311_ADDRRES_0);
    if (TDP4_IIC_2.endTransmission() == 0) {
      hw_info.audio    = AUDIO_ES8311;
    }
    TDP4_IIC_2.beginTransmission(AW86224_ADDRESS);
    if (TDP4_IIC_2.endTransmission() == 0) {
#if SENSORLIB_VERSION >= SENSORLIB_VERSION_VAL(0, 4, 1)
      ESP32_has_vibra = vibra.begin(TDP4_IIC_2, AW8624_SLAVE_ADDRESS,
                                    SOC_GPIO_PIN_TDP4_SDA_2,
                                    SOC_GPIO_PIN_TDP4_SCL_2);
      if (ESP32_has_vibra)
#endif /* (0, 4, 1) */
      {
        hw_info.haptic = HAPTIC_AW86224;
      }
    }

    uint8_t sgm38121_chip_rev = 0;
    sgm38121_read_reg(&TDP4_IIC_2, SGM38121_REG_CHIP_REV, &sgm38121_chip_rev);

    if (sgm38121_chip_rev == 0x80) {
      int dvdd1_actual_mv = 0;
      int avdd1_actual_mv = 0;
      int avdd2_actual_mv = 0;
      uint8_t dvdd1_reg = sgm38121_encode_dvdd_mv_rounded(1500, &dvdd1_actual_mv);
      uint8_t avdd1_reg = sgm38121_encode_avdd_mv_rounded(1700, &avdd1_actual_mv);
      uint8_t avdd2_reg = sgm38121_encode_avdd_mv_rounded(3000, &avdd2_actual_mv);
      uint8_t enable_mask = 0;

      sgm38121_write_reg(&TDP4_IIC_2, SGM38121_REG_DVDD1_VOUT, dvdd1_reg);
      enable_mask |= SGM38121_ENABLE_DVDD1_BIT;
      sgm38121_write_reg(&TDP4_IIC_2, SGM38121_REG_AVDD1_VOUT, avdd1_reg);
      enable_mask |= SGM38121_ENABLE_AVDD1_BIT;
      sgm38121_write_reg(&TDP4_IIC_2, SGM38121_REG_AVDD2_VOUT, avdd2_reg);
      enable_mask |= SGM38121_ENABLE_AVDD2_BIT;
      sgm38121_write_reg(&TDP4_IIC_2, SGM38121_REG_ENABLE, enable_mask);

      uint8_t discharge  = 0;
      uint8_t dvdd1_vout = 0;
      uint8_t dvdd2_vout = 0;
      uint8_t avdd1_vout = 0;
      uint8_t avdd2_vout = 0;
      uint8_t function   = 0;
      uint8_t seq_dvdd   = 0;
      uint8_t seq_avdd   = 0;
      uint8_t enable     = 0;
      uint8_t seq_ctrl   = 0;

      sgm38121_read_reg(&TDP4_IIC_2, SGM38121_REG_DISCH,      &discharge);
      sgm38121_read_reg(&TDP4_IIC_2, SGM38121_REG_DVDD1_VOUT, &dvdd1_vout);
      sgm38121_read_reg(&TDP4_IIC_2, SGM38121_REG_DVDD2_VOUT, &dvdd2_vout);
      sgm38121_read_reg(&TDP4_IIC_2, SGM38121_REG_AVDD1_VOUT, &avdd1_vout);
      sgm38121_read_reg(&TDP4_IIC_2, SGM38121_REG_AVDD2_VOUT, &avdd2_vout);
      sgm38121_read_reg(&TDP4_IIC_2, SGM38121_REG_FUNCTION,   &function);
      sgm38121_read_reg(&TDP4_IIC_2, SGM38121_REG_SEQ_DVDD,   &seq_dvdd);
      sgm38121_read_reg(&TDP4_IIC_2, SGM38121_REG_SEQ_AVDD,   &seq_avdd);
      sgm38121_read_reg(&TDP4_IIC_2, SGM38121_REG_ENABLE,     &enable);
      sgm38121_read_reg(&TDP4_IIC_2, SGM38121_REG_SEQ_CTRL,   &seq_ctrl);

#if 0
      Serial.printf(
             "CHIP_REV=0x%02X DISCH=0x%02X FUNC=0x%02X SEQ_DV=0x%02X SEQ_AV=0x%02X EN=0x%02X SEQ_CTRL=0x%02X\r\n",
             sgm38121_chip_rev,
             discharge,
             function,
             seq_dvdd,
             seq_avdd,
             enable,
             seq_ctrl);

      Serial.printf(
             "DVDD1 reg=0x%02X (%d mV, %s), DVDD2 reg=0x%02X (%d mV, %s)\r\n",
             dvdd1_vout,
             sgm38121_decode_dvdd_mv(dvdd1_vout),
             (enable & SGM38121_ENABLE_DVDD1_BIT) ? "enabled" : "disabled",
             dvdd2_vout,
             sgm38121_decode_dvdd_mv(dvdd2_vout),
             (enable & SGM38121_ENABLE_DVDD2_BIT) ? "enabled" : "disabled");

      Serial.printf(
             "AVDD1 reg=0x%02X (%d mV, %s), AVDD2 reg=0x%02X (%d mV, %s)\r\n",
             avdd1_vout,
             sgm38121_decode_avdd_mv(avdd1_vout),
             (enable & SGM38121_ENABLE_AVDD1_BIT) ? "enabled" : "disabled",
             avdd2_vout,
             sgm38121_decode_avdd_mv(avdd2_vout),
             (enable & SGM38121_ENABLE_AVDD2_BIT) ? "enabled" : "disabled");
#endif

      delay(200);

      TDP4_IIC_2.beginTransmission(OV2710_ADDRESS);
      if (TDP4_IIC_2.endTransmission() == 0) {
#if defined(USE_CAMERA)
        esp32p4_cam_config_t cfg = esp32p4_cam_config_board(ESP32P4_BOARD_CUSTOM);
        cfg.wire = &TDP4_IIC_2;
        cfg.sda = SOC_GPIO_PIN_TDP4_SDA_2;
        cfg.scl = SOC_GPIO_PIN_TDP4_SCL_2;
        cfg.pixel_format = ESP32P4_PIXFORMAT_RGB565;
        cfg.sensor = ESP32P4_SENSOR_OV2710;
        cfg.frame_size = ESP32P4_FRAMESIZE_VGA;

        if (cam.begin(cfg)) {
          hw_info.camera = CAMERA_OV2710;
        } else {
          Serial.println("ERROR: OV2710 camera init failure");
        }
#else
        hw_info.camera = CAMERA_OV2710;
#endif /* USE_CAMERA */
      }
    }
  }
#endif /* CONFIG_IDF_TARGET_ESP32P4 */

#if !defined(EXCLUDE_LED_RING)
  if (hw_info.model == SOFTRF_MODEL_STANDALONE)
  {
#if defined(USE_ADAFRUIT_NEO_LIBRARY)
    int16_t pixels_pin = esp32_board == ESP32_BANANA_PICOW ?
                         SOC_GPIO_PIN_BPIPW_LED : SOC_GPIO_PIN_LED;

    // Parameter 1 = number of pixels in strip
    // Parameter 2 = Arduino pin number (most are valid)
    // Parameter 3 = pixel type flags, add together as needed:
    //   NEO_KHZ800  800 KHz bitstream (most NeoPixel products w/WS2812 LEDs)
    //   NEO_KHZ400  400 KHz (classic 'v1' (not v2) FLORA pixels, WS2811 drivers)
    //   NEO_GRB     Pixels are wired for GRB bitstream (most NeoPixel products)
    //   NEO_RGB     Pixels are wired for RGB bitstream (v1 FLORA pixels, not v2)

    strip = new Adafruit_NeoPixel(PIX_NUM, pixels_pin, NEO_GRB + NEO_KHZ800);
#endif /* USE_ADAFRUIT_NEO_LIBRARY */
  }
#endif /* EXCLUDE_LED_RING */

}

static void ESP32_post_init()
{
#if defined(CONFIG_IDF_TARGET_ESP32S3)  || \
    defined(CONFIG_IDF_TARGET_ESP32S31) || \
    defined(CONFIG_IDF_TARGET_ESP32P4)
  if (hw_info.model == SOFTRF_MODEL_PRIME_MK3 ||
      hw_info.model == SOFTRF_MODEL_CONCORDE)
  {
    Serial.println();
    Serial.println(F("Power-on Self Test"));
    Serial.println();
    Serial.flush();

    Serial.println(F("Built-in components:"));

    Serial.print(F("RADIO    : "));
    Serial.println(hw_info.rf      == RF_IC_SX1262 ||
                   hw_info.rf      == RF_IC_SX1276 ||
                   hw_info.rf      == RF_IC_LR1121     ? F("PASS") : F("FAIL"));
    Serial.flush();
    Serial.print(F("GNSS     : "));
    Serial.println(hw_info.gnss    != GNSS_MODULE_NONE ? F("PASS") : F("FAIL"));
    Serial.flush();
    Serial.print(F("DISPLAY  : "));
    Serial.println(hw_info.display != DISPLAY_NONE     ? F("PASS") : F("FAIL"));
    Serial.flush();
    Serial.print(F("RTC      : "));
    Serial.println(hw_info.rtc     == RTC_PCF8563      ? F("PASS") : F("FAIL"));
    Serial.flush();
#if !defined(EXCLUDE_IMU)
    Serial.print(F("IMU      : "));
    Serial.println(hw_info.imu     != IMU_NONE         ? F("PASS") : F("FAIL"));
    Serial.flush();
#endif /* EXCLUDE_IMU */
#if !defined(EXCLUDE_MAG)
    Serial.print(F("MAG      : "));
    Serial.println(hw_info.mag     != MAG_NONE         ? F("PASS") : F("FAIL"));
    Serial.flush();
#endif /* EXCLUDE_MAG */
    if (hw_info.model == SOFTRF_MODEL_PRIME_MK3) {
      Serial.print(F("32K XTAL : "));
      Serial.println(ESP32_has_32k_xtal                ? F("PASS") : F("FAIL"));
      Serial.flush();
      Serial.print(F("BARO     : "));
      Serial.println(hw_info.baro == BARO_MODULE_BMP280 ? F("PASS") : F("N/A"));
      Serial.flush();
    } else {
      Serial.print(F("AUDIO    : "));
      Serial.println(hw_info.audio   == AUDIO_ES8311   ? F("PASS") : F("FAIL"));
      Serial.flush();
      Serial.print(F("TOUCH    : "));
      Serial.println(hw_info.touch   != TOUCH_NONE     ? F("PASS") : F("FAIL"));
      Serial.flush();
      Serial.print(F("HAPTIC   : "));
      Serial.println(hw_info.haptic  == HAPTIC_AW86224 ? F("PASS") : F("FAIL"));
      Serial.flush();
      Serial.print(F("CAMERA   : "));
      Serial.println(hw_info.camera  == CAMERA_OV2710  ? F("PASS") : F("FAIL"));
      Serial.flush();
    }

    Serial.println();
    Serial.println(F("External components:"));
    Serial.print(F("CARD     : "));
    Serial.println(hw_info.storage == STORAGE_CARD ||
                   hw_info.storage == STORAGE_FLASH_AND_CARD
                                                       ? F("PASS") : F("N/A"));
    Serial.flush();

    Serial.println();
    Serial.println(F("Power-on Self Test is complete."));
    Serial.flush();
  }

  if (esp32_board == ESP32_TTGO_T_BEAM_SUPREME ||
      esp32_board == ESP32_TTGO_T_BEAM_1W      ||
      esp32_board == ESP32_LILYGO_T_TWR2       ||
      esp32_board == ESP32_P4_WT_DEVKIT        ||
      esp32_board == ESP32_LILYGO_TDISPLAY_P4)
  {
    Serial.println();

    if (!uSD_is_attached) {
      Serial.println(F("WARNING: unable to attach micro-SD card."));
    } else {
      // The number of 512 byte sectors in the card
      // or zero if an error occurs.
      size_t cardSize = uSD.card()->cardSize();

      if (cardSize == 0) {
        Serial.println(F("WARNING: invalid micro-SD card size."));
      } else {
        uint8_t cardType = uSD.card()->type();

        Serial.print(F("SD Card Type: "));
        if(cardType == SD_CARD_TYPE_SD1){
            Serial.println(F("V1"));
        } else if(cardType == SD_CARD_TYPE_SD2){
            Serial.println(F("V2"));
        } else if(cardType == SD_CARD_TYPE_SDHC){
            Serial.println(F("SDHC"));
        } else {
            Serial.println(F("UNKNOWN"));
        }

        Serial.print("SD Card Size: ");
        Serial.print(cardSize / (2 * 1024));
        Serial.println(" MB");
      }
    }
  }
#endif /* CONFIG_IDF_TARGET_ESP32S3-P4 */

#if defined(CONFIG_IDF_TARGET_ESP32S3) || defined(CONFIG_IDF_TARGET_ESP32S31)
#if !defined(EXCLUDE_VOICE_MESSAGE)
  if (esp32_board == ESP32_LILYGO_T_TWR2 && hw_info.revision == 1 && uSD_is_attached)
  {
    char filename[MAX_FILENAME_LEN];
    strcpy(filename, WAV_FILE_PREFIX);
    strcat(filename, "POST");
    strcat(filename, WAV_FILE_SUFFIX);
    if (uSD.exists(filename)) {
      axp_2xxx.enableALDO3();
      Audio_Sink->SetPinout(I2S_PIN_NO_CHANGE,
                            I2S_PIN_NO_CHANGE,
                            SOC_GPIO_PIN_TWR2_PDM_AUX,
                            I2S_PIN_NO_CHANGE);
      Audio_Sink->SetGain(/* 0.25 */ 0.5 /* 1 */);

      play_file(filename, NULL);

      axp_2xxx.disableALDO3();
      I2S_Init((i2s_mode_t) (I2S_MODE_TX | I2S_MODE_PDM),
                I2S_BITS_PER_SAMPLE_16BIT);
      Audio_Sink->SetPinout(I2S_PIN_NO_CHANGE,
                            I2S_PIN_NO_CHANGE,
                            SOC_GPIO_PIN_TWR2_PDM_OUT,
                            I2S_PIN_NO_CHANGE);
      Audio_Sink->SetGain(/* 0.0625 */ 0.125 /* 0.25 */);
    }
  }
#endif /* EXCLUDE_VOICE_MESSAGE */
#endif /* CONFIG_IDF_TARGET_ESP32S3 */

  Stream *Diag;
  if (esp32_board == ESP32_RADIOMASTER_XR1) { Diag = &Serial_GNSS_Out; } else if
     (esp32_board == ESP32_ELECROW_TN_M2 || esp32_board == ESP32_ELECROW_TN_M5)
    { Diag = &SerialOutput; } else { Diag = &Serial; }

  Diag->println();
  Diag->println(F("Data output device(s):"));

  if (settings->mode == SOFTRF_MODE_UAV) {
    Diag->println(F("MAV V1 - UART"));
  } else {

    Diag->print(F("NMEA   - "));
    switch (settings->nmea_out)
    {
      case NMEA_UART       :  Diag->println(F("UART"));      break;
      case NMEA_USB        :  Diag->println(F("USB CDC"));   break;
      case NMEA_UDP        :  Diag->println(F("UDP"));       break;
      case NMEA_TCP        :  Diag->println(F("TCP"));       break;
      case NMEA_BLUETOOTH  :  Diag->println(F("Bluetooth")); break;
      case NMEA_OFF        :
      default              :  Diag->println(F("NULL"));      break;
    }

    Diag->print(F("GDL90  - "));
    switch (settings->gdl90)
    {
      case GDL90_UART      :  Diag->println(F("UART"));      break;
      case GDL90_USB       :  Diag->println(F("USB CDC"));   break;
      case GDL90_UDP       :  Diag->println(F("UDP"));       break;
      case GDL90_BLUETOOTH :  Diag->println(F("Bluetooth")); break;
      case GDL90_OFF       :
      default              :  Diag->println(F("NULL"));      break;
    }

    Diag->print(F("D1090  - "));
    switch (settings->d1090)
    {
      case D1090_UART      :  Diag->println(F("UART"));      break;
      case D1090_USB       :  Diag->println(F("USB CDC"));   break;
      case D1090_BLUETOOTH :  Diag->println(F("Bluetooth")); break;
      case D1090_OFF       :
      default              :  Diag->println(F("NULL"));      break;
    }
  }

  Diag->println();
  Diag->flush();

  switch (hw_info.display)
  {
#if defined(USE_OLED)
  case DISPLAY_OLED_TTGO:
  case DISPLAY_OLED_HELTEC:
  case DISPLAY_OLED_1_3:
    OLED_info1();

#if defined(CONFIG_IDF_TARGET_ESP32S3)  || \
    defined(CONFIG_IDF_TARGET_ESP32S31) || \
    defined(CONFIG_IDF_TARGET_ESP32P4)
    if (esp32_board == ESP32_TTGO_T_BEAM_SUPREME ||
        esp32_board == ESP32_P4_WT_DEVKIT)
    {
      char key[8];
      char out[64];
      uint8_t tokens[3] = { 0 };
      cdbResult rt;
      int c, i = 0, token_cnt = 0;

      int acfts;
      char *reg, *mam, *cn;
      reg = mam = cn = NULL;

      if (esp32_board == ESP32_TTGO_T_BEAM_SUPREME) {
        OLED_info2();
      }

      if (ADB_is_open) {
        acfts = ucdb.recordsNumber();

        snprintf(key, sizeof(key),"%06X", ThisAircraft.addr);

        rt = ucdb.findKey(key, strlen(key));

        switch (rt) {
          case KEY_FOUND:
            while ((c = ucdb.readValue()) != -1 && i < (sizeof(out) - 1)) {
              if (c == '|') {
                if (token_cnt < (sizeof(tokens) - 1)) {
                  token_cnt++;
                  tokens[token_cnt] = i+1;
                }
                c = 0;
              }
              out[i++] = (char) c;
            }
            out[i] = 0;

            reg = out + tokens[1];
            mam = out + tokens[0];
            cn  = out + tokens[2];

            break;

          case KEY_NOT_FOUND:
          default:
            break;
        }

        reg = (reg != NULL) && strlen(reg) ? reg : (char *) "REG: N/A";
        mam = (mam != NULL) && strlen(mam) ? mam : (char *) "M&M: N/A";
        cn  = (cn  != NULL) && strlen(cn)  ? cn  : (char *) " CN: N/A";

      } else {
        acfts = -1;
      }

      OLED_info3(acfts, reg, mam, cn);
    }
#endif /* CONFIG_IDF_TARGET_ESP32S3-P4 */

    break;
#endif /* USE_OLED */

#if defined(USE_EPAPER)
  case DISPLAY_EPD_1_54:
  case DISPLAY_EPD_2_13:
    if (hw_info.model == SOFTRF_MODEL_INK ||
        hw_info.model == SOFTRF_MODEL_AIRVENTURE) {
      EPD_info1();
    }

    if (hw_info.model == SOFTRF_MODEL_INK) {
      char key[8];
      char out[64];
      uint8_t tokens[3] = { 0 };
      cdbResult rt;
      int c, i = 0, token_cnt = 0;

      int acfts;
      char *reg, *mam, *cn;
      reg = mam = cn = NULL;

      if (ADB_is_open) {
        acfts = ucdb.recordsNumber();

        snprintf(key, sizeof(key),"%06X", ThisAircraft.addr);

        rt = ucdb.findKey(key, strlen(key));

        switch (rt) {
          case KEY_FOUND:
            while ((c = ucdb.readValue()) != -1 && i < (sizeof(out) - 1)) {
              if (c == '|') {
                if (token_cnt < (sizeof(tokens) - 1)) {
                  token_cnt++;
                  tokens[token_cnt] = i+1;
                }
                c = 0;
              }
              out[i++] = (char) c;
            }
            out[i] = 0;

            reg = out + tokens[1];
            mam = out + tokens[0];
            cn  = out + tokens[2];

            break;

          case KEY_NOT_FOUND:
          default:
            break;
        }

        reg = (reg != NULL) && strlen(reg) ? reg : (char *) "REG: N/A";
        mam = (mam != NULL) && strlen(mam) ? mam : (char *) "M&M: N/A";
        cn  = (cn  != NULL) && strlen(cn)  ? cn  : (char *) "N/A";

      } else {
        acfts = -1;
      }

      EPD_info2(acfts, reg, mam, cn);
    }

    break;
#endif /* USE_EPAPER */

#if defined(USE_DSI)
  case DISPLAY_TFT_WIRELESSTAG_7:
  case DISPLAY_TFT_LILYGO_4_05:
  case DISPLAY_AMOLED_LILYGO_4_1:
    if (hw_info.model == SOFTRF_MODEL_CONCORDE) {
      DSI_info1();

      char key[8];
      char out[64];
      uint8_t tokens[3] = { 0 };
      cdbResult rt;
      int c, i = 0, token_cnt = 0;

      int acfts;
      char *reg, *mam, *cn;
      reg = mam = cn = NULL;

      if (ADB_is_open) {
        acfts = ucdb.recordsNumber();

        snprintf(key, sizeof(key),"%06X", ThisAircraft.addr);

        rt = ucdb.findKey(key, strlen(key));

        switch (rt) {
          case KEY_FOUND:
            while ((c = ucdb.readValue()) != -1 && i < (sizeof(out) - 1)) {
              if (c == '|') {
                if (token_cnt < (sizeof(tokens) - 1)) {
                  token_cnt++;
                  tokens[token_cnt] = i+1;
                }
                c = 0;
              }
              out[i++] = (char) c;
            }
            out[i] = 0;

            reg = out + tokens[1];
            mam = out + tokens[0];
            cn  = out + tokens[2];

            break;

          case KEY_NOT_FOUND:
          default:
            break;
        }

        reg = (reg != NULL) && strlen(reg) ? reg : (char *) "REG: N/A";
        mam = (mam != NULL) && strlen(mam) ? mam : (char *) "M&M: N/A";
        cn  = (cn  != NULL) && strlen(cn)  ? cn  : (char *) "N/A";

      } else {
        acfts = -1;
      }

      DSI_info2(acfts, reg, mam, cn);
    }

    break;
#endif /* USE_DSI */

  case DISPLAY_NONE:
  default:
    break;
  }

#if defined(CONFIG_IDF_TARGET_ESP32P4)
  if (esp32_board == ESP32_P4_WT_DEVKIT ||
      esp32_board == ESP32_LILYGO_TDISPLAY_P4) {
#if defined(USE_CAMERA)
    if (hw_info.camera != CAMERA_NONE) {
      stream.begin(&cam, 8080, 35);
    }
#endif /* USE_CAMERA */
  }
#endif /* CONFIG_IDF_TARGET_ESP32P4 */
}

static void ESP32_loop()
{
  bool is_irq = false;
  bool down = false;

  switch (hw_info.pmu)
  {
#if defined(CONFIG_IDF_TARGET_ESP32)
  case PMU_AXP192:
  case PMU_AXP202:

    portENTER_CRITICAL_ISR(&PMU_mutex);
    is_irq = PMU_Irq;
    portEXIT_CRITICAL_ISR(&PMU_mutex);

    if (is_irq) {

      if (axp_xxx.readIRQ() == AXP_PASS) {

        if (axp_xxx.isPEKLongtPressIRQ()) {
          down = true;
#if 0
          Serial.println(F("Long press IRQ"));
          Serial.flush();
#endif
        }
        if (axp_xxx.isPEKShortPressIRQ()) {
#if 0
          Serial.println(F("Short press IRQ"));
          Serial.flush();
#endif
#if defined(USE_OLED)
          OLED_Next_Page();
#endif
        }

        axp_xxx.clearIRQ();
      }

      portENTER_CRITICAL_ISR(&PMU_mutex);
      PMU_Irq = false;
      portEXIT_CRITICAL_ISR(&PMU_mutex);

      if (down) {
        shutdown(SOFTRF_SHUTDOWN_BUTTON);
      }
    }

    if (isTimeToBattery()) {
      if (Battery_voltage() > Battery_threshold()) {
        axp_xxx.setChgLEDMode(AXP20X_LED_LOW_LEVEL);
      } else {
        axp_xxx.setChgLEDMode(AXP20X_LED_BLINK_1HZ);
      }
    }
    break;
#endif /* CONFIG_IDF_TARGET_ESP32 */

  case PMU_AXP2101:
    portENTER_CRITICAL_ISR(&PMU_mutex);
    is_irq = PMU_Irq;
    portEXIT_CRITICAL_ISR(&PMU_mutex);

    if (is_irq) {

      axp_2xxx.getIrqStatus();

      if (axp_2xxx.isPekeyLongPressIrq()) {
        down = true;
      }
      if (axp_2xxx.isPekeyShortPressIrq()) {
#if defined(USE_OLED)
        OLED_Next_Page();
#endif
      }

      axp_2xxx.clearIrqStatus();

      portENTER_CRITICAL_ISR(&PMU_mutex);
      PMU_Irq = false;
      portEXIT_CRITICAL_ISR(&PMU_mutex);

      if (down) {
        shutdown(SOFTRF_SHUTDOWN_BUTTON);
      }
    }

    if (isTimeToBattery()) {
      if (Battery_voltage() > Battery_threshold()) {
        axp_2xxx.setChargingLedMode(XPOWERS_CHG_LED_ON);
      } else {
        axp_2xxx.setChargingLedMode(XPOWERS_CHG_LED_BLINK_1HZ);
      }
    }
    break;

  case PMU_NONE:
  default:
    break;
  }
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
