lyusupov/SoftRF/software/firmware/source/SoftRF/src/platform/nRF52.cpp

/*
 * Platform_nRF52.cpp
 * Copyright (C) 2020-2026 Linar Yusupov
 *
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
 * You should have received a copy of the GNU General Public License
 * along with this program.  If not, see <http://www.gnu.org/licenses/>.
 */

#if defined(ARDUINO_ARCH_NRF52)  || defined(ARDUINO_ARCH_NRF52840) || \
   (defined(ARDUINO_ARCH_ZEPHYR) && defined(NRF52840_XXAA))

#include <SPI.h>
#include <Wire.h>
#if !defined(ARDUINO_ARCH_MBED) && !defined(ARDUINO_ARCH_ZEPHYR)
#include <pcf8563.h>
//#include <RTC_RX8900_U.h>
#include <Adafruit_SPIFlash.h>
#include "Adafruit_TinyUSB.h"
#include <Adafruit_SleepyDog.h>
#endif /* ARDUINO_ARCH_MBED */
#if !defined(ARDUINO_ARCH_ZEPHYR)
#include <ArduinoJson.h>

#include "nrf_wdt.h"
#endif /* ARDUINO_ARCH_ZEPHYR */

#include "../system/SoC.h"
#include "../driver/RF.h"
#include "../driver/EEPROM.h"
#include "../driver/GNSS.h"
#include "../driver/Baro.h"
#include "../driver/LED.h"
#include "../driver/Bluetooth.h"
#include "../driver/EPD.h"
#include "../driver/Battery.h"
#include "../driver/Sound.h"
#include "../protocol/data/NMEA.h"
#include "../protocol/data/GDL90.h"
#include "../protocol/data/D1090.h"
#if !defined(ARDUINO_ARCH_ZEPHYR)
#include "../protocol/data/JSON.h"
#endif /* ARDUINO_ARCH_ZEPHYR */
#include "../system/Time.h"

#include "uCDB.hpp"

#if defined(USE_BLE_MIDI)
#include <bluefruit.h>
#endif /* USE_BLE_MIDI */

#if defined(USE_BLE_MIDI) || defined(USE_USB_MIDI)
#include <MIDI.h>
#endif /* USE_BLE_MIDI || USE_USB_MIDI */

#if defined(ENABLE_REMOTE_ID)
#include "../protocol/radio/RemoteID.h"
#endif /* ENABLE_REMOTE_ID */

#if defined(USE_TFT)
#include <TFT_eSPI.h>
#endif /* USE_TFT */

#if defined(USE_OLED)
#include "../driver/OLED.h"

extern U8X8 u8x8_i2c;
#endif /* USE_OLED */

typedef volatile uint32_t REG32;
#define pREG32 (REG32 *)

#define DEVICE_ID_HIGH    (*(pREG32 (0x10000060)))
#define DEVICE_ID_LOW     (*(pREG32 (0x10000064)))

#define EPD_STACK_SZ      (256*3)

// RFM95W pin mapping
lmic_pinmap lmic_pins = {
    .nss = SOC_GPIO_PIN_SS,
    .txe = LMIC_UNUSED_PIN,
    .rxe = LMIC_UNUSED_PIN,
    .rst = SOC_GPIO_PIN_PCA10059_RST,
    .dio = {LMIC_UNUSED_PIN, LMIC_UNUSED_PIN, LMIC_UNUSED_PIN},
    .busy = SOC_GPIO_PIN_BUSY,
    .tcxo = LMIC_UNUSED_PIN,
};

#if !defined(EXCLUDE_LED_RING)
// Parameter 1 = number of pixels in strip
// Parameter 2 = Arduino pin number (most are valid)
// Parameter 3 = pixel type flags, add together as needed:
//   NEO_KHZ800  800 KHz bitstream (most NeoPixel products w/WS2812 LEDs)
//   NEO_KHZ400  400 KHz (classic 'v1' (not v2) FLORA pixels, WS2811 drivers)
//   NEO_GRB     Pixels are wired for GRB bitstream (most NeoPixel products)
//   NEO_RGB     Pixels are wired for RGB bitstream (v1 FLORA pixels, not v2)
Adafruit_NeoPixel strip = Adafruit_NeoPixel(PIX_NUM, SOC_GPIO_PIN_LED,
                                            NEO_GRB + NEO_KHZ800);
#endif /* EXCLUDE_LED_RING */

#if defined(EXCLUDE_WIFI)
char UDPpacketBuffer[256]; // Dummy definition to satisfy build sequence
#else
#if defined(USING_WIFI101_GENERIC) || defined(WiFiNINA_h)
#include <SoftSPI.h>
SoftSPI WiFiSPI(_PINNUM(1, 7), _PINNUM(1, 6), _PINNUM(0, 8));
#endif /* USING_WIFI101_GENERIC || WiFiNINA_h */
#endif /* EXCLUDE_WIFI */

static uint32_t prev_tx_packets_counter = 0;
static uint32_t prev_rx_packets_counter = 0;

static struct rst_info reset_info = {
  .reason = REASON_DEFAULT_RST,
};

static uint32_t bootCount __attribute__ ((section (".noinit")));

static nRF52_board_id nRF52_board = NRF52_LILYGO_TECHO_REV_2; /* default */
static nRF52_display_id nRF52_display = EP_UNKNOWN;

const char *nRF5x_Device_Manufacturer = SOFTRF_IDENT;
const char *nRF5x_Device_Model = "Badge Edition";
const uint16_t nRF52_Device_Version = SOFTRF_USB_FW_VERSION;
static uint16_t nRF52_USB_VID = 0x239A; /* Adafruit Industries */
static uint16_t nRF52_USB_PID = 0x8029; /* Feather nRF52840 Express */

const char *Hardware_Rev[] = {
  [0] = "2020-8-6",
  [1] = "2020-12-12",
  [2] = "2021-3-26",
  [3] = "Unknown"
};

const prototype_entry_t techo_prototype_boards[] = {
  { 0x684f99bd2d5c7fae, NRF52_LILYGO_TECHO_REV_0, EP_GDEP015OC1,  0 }, /* orange */
  { 0xf353e11726ea8220, NRF52_LILYGO_TECHO_REV_0, EP_GDEH0154D67, 0 }, /* blue   */
  { 0xf4e0f04ded1892da, NRF52_LILYGO_TECHO_REV_1, EP_GDEH0154D67, 0 }, /* green  */
  { 0x65ab5994ea2c9094, NRF52_LILYGO_TECHO_REV_1, EP_GDEH0154D67, 0 }, /* blue   */
  { 0x6460429ea6fb7e39, NRF52_NORDIC_PCA10059,    EP_UNKNOWN,     0 },
/*{ 0x0b0e14e96a3beb79, NRF52_ELECROW_TN_M1,      EP_GDEH0154D67, 0 },*/
};

#if !defined(ARDUINO_ARCH_MBED) && !defined(ARDUINO_ARCH_ZEPHYR)
I2CBus        *i2c   = nullptr;
PCF8563_Class *rtc   = nullptr;
//RTC_RX8900_U  *rtc_2 = nullptr;
#endif /* ARDUINO_ARCH_MBED */

static bool nRF52_has_rtc      = false;
static bool nRF52_has_spiflash = false;
static bool RTC_sync           = false;
static bool FATFS_is_mounted   = false;
static bool ADB_is_open        = false;
static bool screen_saver       = false;
static bool nRF52_has_vff      = false; /* very first fix */

#if !defined(ARDUINO_ARCH_MBED) && !defined(ARDUINO_ARCH_ZEPHYR)
RTC_Date fw_build_date_time = RTC_Date(__DATE__, __TIME__);

static TaskHandle_t EPD_Task_Handle = NULL;
#else
#define ledOn(x)  {} /* TBD */
#define ledOff(x) {} /* TBD */

#define PIN_LED1  0 /* TBD */
#define PIN_LED2  0 /* TBD */
#define PIN_LED3  0 /* TBD */
#define PIN_LED4  0 /* TBD */
#endif /* ARDUINO_ARCH_MBED */

#if !defined(ARDUINO_NRF52840_PCA10056) && \
    !defined(ARDUINO_ARCH_MBED)         && \
    !defined(ARDUINO_ARCH_ZEPHYR)
#error "This nRF52 build variant is not supported!"
#endif

#if SPI_32MHZ_INTERFACE == 0
#define _SPI_DEV    NRF_SPIM3 // 32 Mhz
#define _SPI1_DEV   NRF_SPIM2
#elif SPI_32MHZ_INTERFACE == 1
#define _SPI_DEV    NRF_SPIM2
#define _SPI1_DEV   NRF_SPIM3 // 32 Mhz
#else
  #error "not supported yet"
#endif

#if defined(USE_EPAPER)

#if SPI_INTERFACES_COUNT == 1
SPIClass SPI1(_SPI1_DEV,
              SOC_GPIO_PIN_EPD_MISO,
              SOC_GPIO_PIN_EPD_SCK,
              SOC_GPIO_PIN_EPD_MOSI);
#endif

GxEPD2_GFX *display = NULL;
#endif /* USE_EPAPER */

#if defined(USE_TFT)
static TFT_eSPI *tft = NULL;

#if !defined(USE_OLED)
static const char SoftRF_text1[]  = "SoftRF";
static const char ID_text[]       = "ID";
static const char PROTOCOL_text[] = "PROTOCOL";
static const char RX_text[]       = "RX";
static const char TX_text[]       = "TX";
#endif /* USE_OLED */

static bool TFT_display_frontpage = false;

static void TFT_off()
{
    tft->writecommand(TFT_DISPOFF);
    tft->writecommand(TFT_SLPIN);
}

static void TFT_backlight_adjust(uint32_t pin, uint8_t level)
{
    analogWrite(pin, 255 - level);
}
#endif /* USE_TFT */

#if !defined(ARDUINO_ARCH_MBED) && !defined(ARDUINO_ARCH_ZEPHYR)
static Adafruit_FlashTransport_QSPI *FlashTrans = NULL;
static Adafruit_SPIFlash            *SPIFlash   = NULL;

#define SFLASH_CMD_READ_CONFIG  0x15

static uint32_t spiflash_id = 0;
static uint8_t mx25_status_config[3] = {0x00, 0x00, 0x00};

/// Flash device list count
enum {
  MX25R1635F_INDEX,
  ZD25WQ16B_INDEX,

  ZD25WQ32C_INDEX,
  ZD25Q32D_INDEX,

  GD25Q64C_INDEX,
#if !defined(EXCLUDE_WIP)
  P25Q16H_INDEX,
#endif /* EXCLUDE_WIP */
  EXTERNAL_FLASH_DEVICE_COUNT
};

/// List of all possible flash devices used by nRF52840 boards
static SPIFlash_Device_t possible_devices[] = {
  // LilyGO T-Echo, Elecrow ThinkNode M1
  [MX25R1635F_INDEX] = MX25R1635F,
  // LilyGO T-Echo
  [ZD25WQ16B_INDEX]  = ZD25WQ16B,

  // LilyGO T-Impulse Plus, T-Echo Card
  [ZD25WQ32C_INDEX]  = ZD25WQ32C,
  [ZD25Q32D_INDEX]   = ZD25Q32D,

  // Seeed T1000-E, X1
  [GD25Q64C_INDEX]   = GD25Q64C,
#if !defined(EXCLUDE_WIP)
  // Seeed Wio L1
  [P25Q16H_INDEX]    = P25Q16H,
#endif /* EXCLUDE_WIP */
};

// USB Mass Storage object
Adafruit_USBD_MSC usb_msc;

// file system object from SdFat
FatVolume fatfs;
#endif /* ARDUINO_ARCH_MBED */

#define NRF52_JSON_BUFFER_SIZE  1024

#if !defined(ARDUINO_ARCH_ZEPHYR)
StaticJsonBuffer<NRF52_JSON_BUFFER_SIZE> nRF52_jsonBuffer;
#endif /* ARDUINO_ARCH_ZEPHYR */

#if defined(USE_WEBUSB_SERIAL) || defined(USE_WEBUSB_SETTINGS)
// USB WebUSB object
Adafruit_USBD_WebUSB usb_web;
#endif

#if defined(USE_WEBUSB_SERIAL)
// Landing Page: scheme (0: http, 1: https), url
WEBUSB_URL_DEF(landingPage, 1 /*https*/, "adafruit.github.io/Adafruit_TinyUSB_Arduino/examples/webusb-serial/index.html");
#endif /* USE_WEBUSB_SERIAL */

#if defined(USE_WEBUSB_SETTINGS)
// Landing Page: scheme (0: http, 1: https), url
WEBUSB_URL_DEF(landingPage, 1 /*https*/, "lyusupov.github.io/SoftRF/settings.html");
#endif /* USE_WEBUSB_SETTINGS */

#if defined(USE_USB_MIDI)
// USB MIDI object
Adafruit_USBD_MIDI usb_midi;

// Create a new instance of the Arduino MIDI Library,
// and attach usb_midi as the transport.
MIDI_CREATE_INSTANCE(Adafruit_USBD_MIDI, usb_midi, MIDI_USB);
#endif /* USE_USB_MIDI */

ui_settings_t ui_settings = {
#if !defined(ARDUINO_ARCH_MBED) && !defined(ARDUINO_ARCH_ZEPHYR)
    .units        = UNITS_METRIC,
    .zoom         = ZOOM_MEDIUM,
    .protocol     = PROTOCOL_NMEA,
    .rotate       = ROTATE_0,
    .orientation  = DIRECTION_TRACK_UP,
    .adb          = DB_OGN,
    .idpref       = ID_TYPE,
    .vmode        = VIEW_MODE_STATUS,
    .voice        = VOICE_OFF,
    .aghost       = ANTI_GHOSTING_OFF,
    .filter       = TRAFFIC_FILTER_OFF,
    .team         = 0
#endif /* ARDUINO_ARCH_MBED */
};

ui_settings_t *ui;

#include <SensorLib_Version.h>
#if !defined(EXCLUDE_IMU)
#define IMU_UPDATE_INTERVAL 500 /* ms */

#include <MPU9250.h>
#include <ICM_20948.h>
#include <QMA6100P.h>
#include <Adafruit_LIS3DH.h>
#if !defined(EXCLUDE_BHI260)
#include <SensorBHI260AP.hpp>
#include <bosch/BoschSensorDataHelper.hpp>

#if defined(USE_BHI260_RAM_FW)
#if SENSORLIB_VERSION == SENSORLIB_VERSION_VAL(0, 3, 1)
#include "bosch/firmware/bosch_app30_shuttle_bhi260.h"
#endif /* (0, 3, 1) */
#if SENSORLIB_VERSION >= SENSORLIB_VERSION_VAL(0, 4, 0)
#include "bosch/firmware/bhi260/bosch_app30_shuttle_bhi260.h"
#endif /* (0, 4, 0) */
#endif /* USE_BHI260_RAM_FW */
#endif /* EXCLUDE_BHI260 */

MPU9250         imu_1;
ICM_20948_I2C   imu_2;
QMA6100P        imu_3;
#if !defined(EXCLUDE_BHI260)
SensorBHI260AP  imu_4;
#endif /* EXCLUDE_BHI260 */
Adafruit_LIS3DH imu_5;

#if !defined(EXCLUDE_BHI260)
#if SENSORLIB_VERSION == SENSORLIB_VERSION_VAL(0, 3, 1)
SensorXYZ bhi_accel(SensorBHI260AP::ACCEL_PASSTHROUGH, imu_4);
// SensorXYZ bhi_gyro(SensorBHI260AP::GYRO_PASSTHROUGH, imu_4);
#endif /* (0, 3, 1) */
#if SENSORLIB_VERSION >= SENSORLIB_VERSION_VAL(0, 4, 0)
SensorXYZ bhi_accel(BoschSensorID::ACCEL_PASSTHROUGH, imu_4);
#endif /* (0, 4, 0) */
#endif /* EXCLUDE_BHI260 */

static bool nRF52_has_imu = false;
static unsigned long IMU_Time_Marker = 0;

extern float   IMU_g;
#if defined(USE_OLED)
extern int32_t IMU_g_x10;
#endif /* USE_OLED */
#endif /* EXCLUDE_IMU */

#if SENSORLIB_VERSION == SENSORLIB_VERSION_VAL(0, 3, 1)
#include <SensorDRV2605.hpp>
SensorDRV2605 vibra;
#endif /* (0, 3, 1) */
#if SENSORLIB_VERSION >= SENSORLIB_VERSION_VAL(0, 4, 1)
#include <HapticDrivers.hpp>
HapticDriver_DRV2605 vibra;
#endif /* (0, 4, 1) */

static bool nRF52_has_vibra = false;

#include <AHT20.h>
AHT20 aht20;

#if WIRE_INTERFACES_COUNT == 1
#if defined __has_include
#if __has_include(<FlexWire.h>)
#include <FlexWire.h>
FlexWire Wire1;
#else
TwoWire Wire1(NRF_TWIM1, NRF_TWIS1, SPIM1_SPIS1_TWIM1_TWIS1_SPI1_TWI1_IRQn,
              SOC_GPIO_PIN_TIP_SDA, SOC_GPIO_PIN_TIP_SCL);
extern "C"
{
  void SPIM1_SPIS1_TWIM1_TWIS1_SPI1_TWI1_IRQHandler(void)
  {
    #if CFG_SYSVIEW
    SEGGER_SYSVIEW_RecordEnterISR();
    #endif

    Wire1.onService();

    #if CFG_SYSVIEW
    SEGGER_SYSVIEW_RecordExitISR();
    #endif
  }
}
#endif /* FlexWire.h */
#endif /* __has_include */
#endif /* WIRE_INTERFACES_COUNT */

#if !defined(ARDUINO_ARCH_MBED) && !defined(ARDUINO_ARCH_ZEPHYR)
uCDB<FatVolume, File32> ucdb(fatfs);

// Callback invoked when received READ10 command.
// Copy disk's data to buffer (up to bufsize) and
// return number of copied bytes (must be multiple of block size)
static int32_t nRF52_msc_read_cb (uint32_t lba, void* buffer, uint32_t bufsize)
{
  // Note: SPIFLash Bock API: readBlocks/writeBlocks/syncBlocks
  // already include 4K sector caching internally. We don't need to cache it, yahhhh!!
  return SPIFlash->readBlocks(lba, (uint8_t*) buffer, bufsize/512) ? bufsize : -1;
}

// Callback invoked when received WRITE10 command.
// Process data in buffer to disk's storage and
// return number of written bytes (must be multiple of block size)
static int32_t nRF52_msc_write_cb (uint32_t lba, uint8_t* buffer, uint32_t bufsize)
{
  if (SOC_GPIO_LED_USBMSC != SOC_UNUSED_PIN) {
      digitalWrite(SOC_GPIO_LED_USBMSC, LED_STATE_ON);
  }

  // Note: SPIFLash Bock API: readBlocks/writeBlocks/syncBlocks
  // already include 4K sector caching internally. We don't need to cache it, yahhhh!!
  return SPIFlash->writeBlocks(lba, buffer, bufsize/512) ? bufsize : -1;
}

// Callback invoked when WRITE10 command is completed (status received and accepted by host).
// used to flush any pending cache.
static void nRF52_msc_flush_cb (void)
{
  // sync with flash
  SPIFlash->syncBlocks();

  // clear file system's cache to force refresh
  fatfs.cacheClear();

  if (SOC_GPIO_LED_USBMSC != SOC_UNUSED_PIN) {
      digitalWrite(SOC_GPIO_LED_USBMSC, 1-LED_STATE_ON);
  }
}
#endif /* ARDUINO_ARCH_MBED */

#if defined(USE_EXT_I2S_DAC)

#define CCCC(c1, c2, c3, c4)  ((c4 << 24) | (c3 << 16) | (c2 << 8) | c1)

#define MAX_FILENAME_LEN      64
#define WAV_FILE_PREFIX       "/Audio/"
#define WAV_FILE_SUFFIX       ".wav"

#define I2S_DATA_BLOCK_WORDS  8192

/* these are data structures to process wav file */
typedef enum headerState_e {
    HEADER_RIFF,
    HEADER_FMT,
    HEADER_DATA,
    DATA
} headerState_t;

typedef struct wavRiff_s {
    uint32_t chunkID;
    uint32_t chunkSize;
    uint32_t format;
} wavRiff_t;

typedef struct wavProperties_s {
    uint32_t chunkID;
    uint32_t chunkSize;
    uint16_t audioFormat;
    uint16_t numChannels;
    uint32_t sampleRate;
    uint32_t byteRate;
    uint16_t blockAlign;
    uint16_t bitsPerSample;
} wavProperties_t;

static uint32_t i2s_buffer[I2S_DATA_BLOCK_WORDS];

void I2S_begin(uint8_t pinSDOUT, uint8_t pinSCK, uint8_t pinLRCK, int8_t pinMCK) {
  // Enable transmission
  NRF_I2S->CONFIG.TXEN     = (I2S_CONFIG_TXEN_TXEN_ENABLE << I2S_CONFIG_TXEN_TXEN_Pos);
  // Enable MCK generator
  // NRF_I2S->CONFIG.MCKEN    = (I2S_CONFIG_MCKEN_MCKEN_ENABLE << I2S_CONFIG_MCKEN_MCKEN_Pos);
  // NRF_I2S->CONFIG.MCKFREQ  = I2S_CONFIG_MCKFREQ_MCKFREQ_32MDIV11 << I2S_CONFIG_MCKFREQ_MCKFREQ_Pos;
  // NRF_I2S->CONFIG.RATIO    = I2S_CONFIG_RATIO_RATIO_64X << I2S_CONFIG_RATIO_RATIO_Pos;
  // Master mode, 16Bit, left aligned
  NRF_I2S->CONFIG.MODE     = I2S_CONFIG_MODE_MODE_MASTER << I2S_CONFIG_MODE_MODE_Pos;
  NRF_I2S->CONFIG.SWIDTH   = I2S_CONFIG_SWIDTH_SWIDTH_16BIT << I2S_CONFIG_SWIDTH_SWIDTH_Pos;
  NRF_I2S->CONFIG.ALIGN    = I2S_CONFIG_ALIGN_ALIGN_LEFT << I2S_CONFIG_ALIGN_ALIGN_Pos;
  // Format = I2S
  NRF_I2S->CONFIG.FORMAT   = I2S_CONFIG_FORMAT_FORMAT_I2S << I2S_CONFIG_FORMAT_FORMAT_Pos;
  // Use left
  NRF_I2S->CONFIG.CHANNELS = I2S_CONFIG_CHANNELS_CHANNELS_LEFT << I2S_CONFIG_CHANNELS_CHANNELS_Pos;

  // Configure pins
  NRF_I2S->PSEL.SCK   = (pinSCK   << I2S_PSEL_SCK_PIN_Pos);
  NRF_I2S->PSEL.LRCK  = (pinLRCK  << I2S_PSEL_LRCK_PIN_Pos);
  NRF_I2S->PSEL.SDOUT = (pinSDOUT << I2S_PSEL_SDOUT_PIN_Pos);
  // NRF_I2S->PSEL.MCK   = (pinMCK   << I2S_PSEL_MCK_PIN_Pos);
}

void I2S_stop()
{
  // Erratta 55 workaround (part 1)
  volatile uint32_t tmp = NRF_I2S->INTEN;
  NRF_I2S->INTEN = 0;

  NRF_I2S->TASKS_STOP = 1;

  // Errata 194 workaround
  *((volatile uint32_t *)0x40025038) = 1;
  *((volatile uint32_t *)0x4002503C) = 1;
  while (NRF_I2S->EVENTS_STOPPED == 0);
  NRF_I2S->EVENTS_STOPPED = 0;
  (void)NRF_I2S->EVENTS_STOPPED;

  // Errata 55 workaround (part 2)
  NRF_I2S->EVENTS_RXPTRUPD = 0;
  NRF_I2S->EVENTS_TXPTRUPD = 0;
  NRF_I2S->EVENTS_STOPPED  = 0;
  NRF_I2S->INTEN = tmp;
}

/*
 *  @brief Mapping Frequency constants to available frequencies
 */
struct I2S_freq_info {
  int id;
  float freq; // in mhz
};

static const I2S_freq_info freq_table[] = {
  { I2S_CONFIG_MCKFREQ_MCKFREQ_32MDIV8,   32.0 /   8 },
  { I2S_CONFIG_MCKFREQ_MCKFREQ_32MDIV10,  32.0 /  10 },
  { I2S_CONFIG_MCKFREQ_MCKFREQ_32MDIV11,  32.0 /  11 },
  { I2S_CONFIG_MCKFREQ_MCKFREQ_32MDIV15,  32.0 /  15 },
  { I2S_CONFIG_MCKFREQ_MCKFREQ_32MDIV16,  32.0 /  16 },
  { I2S_CONFIG_MCKFREQ_MCKFREQ_32MDIV21,  32.0 /  21 },
  { I2S_CONFIG_MCKFREQ_MCKFREQ_32MDIV23,  32.0 /  23 },
  { I2S_CONFIG_MCKFREQ_MCKFREQ_32MDIV30,  32.0 /  30 },
  { I2S_CONFIG_MCKFREQ_MCKFREQ_32MDIV31,  32.0 /  31 },
  { I2S_CONFIG_MCKFREQ_MCKFREQ_32MDIV32,  32.0 /  32 },
  { I2S_CONFIG_MCKFREQ_MCKFREQ_32MDIV42,  32.0 /  42 },
  { I2S_CONFIG_MCKFREQ_MCKFREQ_32MDIV63,  32.0 /  63 },
  { I2S_CONFIG_MCKFREQ_MCKFREQ_32MDIV125, 32.0 / 125 }
};

/*
 *  @brief Mapping from Ratio Constants to frequency ratios
 */
struct I2S_ratio_info {
  int id;
  float ratio;
};

static const I2S_ratio_info ratio_table[] = {
  { I2S_CONFIG_RATIO_RATIO_32X,   32.0 },
  { I2S_CONFIG_RATIO_RATIO_48X,   48.0 },
  { I2S_CONFIG_RATIO_RATIO_64X,   64.0 },
  { I2S_CONFIG_RATIO_RATIO_96X,   96.0 },
  { I2S_CONFIG_RATIO_RATIO_128X, 128.0 },
  { I2S_CONFIG_RATIO_RATIO_192X, 192.0 },
  { I2S_CONFIG_RATIO_RATIO_256X, 256.0 },
  { I2S_CONFIG_RATIO_RATIO_384X, 384.0 },
  { I2S_CONFIG_RATIO_RATIO_512X, 512.0 }
};

void I2S_setSampleRate(uint16_t sampleRate)
{
  // find closest frequency for requested sample_rate
  float freq_requested = sampleRate;
  float selected_freq = 0;
  for (auto freq : freq_table) {
    for (auto div : ratio_table) {
        float freq_value = freq.freq * 1000000 / div.ratio;
        if (abs(freq_value-freq_requested) < abs(selected_freq-freq_requested)){
          // MCKFREQ
          NRF_I2S->CONFIG.MCKFREQ = freq.id << I2S_CONFIG_MCKFREQ_MCKFREQ_Pos;
          // Ratio
          NRF_I2S->CONFIG.RATIO   = div.id  << I2S_CONFIG_RATIO_RATIO_Pos;
          selected_freq = freq_value;
          // Serial.printf("frequency requested %f vs %f\r\n", freq_requested, selected_freq);
        }
     }
  }
  // Serial.printf("Frequency req. %f vs eff. %f\r\n", freq_requested, selected_freq);
}

wavProperties_t wavProps;

static bool play_file(char *filename)
{
  bool rval = false;

#if !defined(EXCLUDE_AUDIO)
  headerState_t state = HEADER_RIFF;

  File wavfile = fatfs.open(filename, FILE_READ);

  if (wavfile) {
    int c = 0;
    int n;

    while (wavfile.available()) {
      switch(state){
        case HEADER_RIFF:
        {
          wavRiff_t wavRiff;

          n = wavfile.read((uint8_t *) &wavRiff, sizeof(wavRiff_t));
          if (n == sizeof(wavRiff_t)) {
            if (wavRiff.chunkID == CCCC('R', 'I', 'F', 'F') &&
                wavRiff.format  == CCCC('W', 'A', 'V', 'E')) {
              state = HEADER_FMT;
              // Serial.println("HEADER_RIFF");
            }
          }
        }
        break;
        case HEADER_FMT:
        {
          n = wavfile.read((uint8_t *) &wavProps, sizeof(wavProperties_t));
          if (n == sizeof(wavProperties_t)) {
            state = HEADER_DATA;
          }
        }
        break;
        case HEADER_DATA:
        {
          uint32_t chunkId, chunkSize;
          n = wavfile.read((uint8_t *) &chunkId, sizeof(chunkId));
          if (n == 4) {
            if(chunkId == CCCC('d', 'a', 't', 'a')) {
              // Serial.println("HEADER_DATA");
            }
          }
          n = wavfile.read((uint8_t *) &chunkSize, sizeof(chunkSize));
          if (n == 4) {
            state = DATA;
          }

          I2S_begin(SOC_GPIO_PIN_I2S_TEC_DOUT,
                    SOC_GPIO_PIN_I2S_TEC_BCK,
                    SOC_GPIO_PIN_I2S_TEC_LRCK,
                    SOC_GPIO_PIN_I2S_TEC_MCK);
          I2S_setSampleRate(wavProps.sampleRate);
        }
        break;
        /* after processing wav header, it is time to process music data */
        case DATA:
        while ((n = wavfile.read((uint8_t *) i2s_buffer, sizeof(i2s_buffer))) > 0) {

          NRF_I2S->RXTXD.MAXCNT = n >> 2;
          NRF_I2S->TXD.PTR =  (uint32_t) i2s_buffer;
          NRF_I2S->ENABLE  = 1;
          NRF_I2S->TASKS_START = 1;

          NRF_I2S->EVENTS_RXPTRUPD = 0;
          NRF_I2S->EVENTS_TXPTRUPD = 0;
          NRF_I2S->EVENTS_STOPPED  = 0;

          while (NRF_I2S->EVENTS_TXPTRUPD == 0);
        }

        if (n == 0) {
          NRF_I2S->TASKS_START = 0;
          NRF_I2S->ENABLE = 0;
        }
        break;
      }
    }
    wavfile.close();
    rval = true;
  } else {
    Serial.println(F("error opening WAV file"));
  }
  if (state == DATA) {
    I2S_stop();
  }
#endif /* EXCLUDE_AUDIO */

  return rval;
}
#endif /* USE_EXT_I2S_DAC */

#if defined(ENABLE_RECORDER)
#define SD_CONFIG SdSpiConfig(uSD_SS_pin, SHARED_SPI, SD_SCK_MHZ(8), &SPI)

SdFat uSD;

static bool uSD_is_attached = false;
#endif /* ENABLE_RECORDER */

#if !defined(EXCLUDE_LED_RING)
Adafruit_NeoPixel nRF52_Pixel = Adafruit_NeoPixel(0, SOC_UNUSED_PIN,
                                                  NEO_GRB + NEO_KHZ800);
#endif /* EXCLUDE_LED_RING */

#if !defined(ARDUINO_ARCH_MBED) && !defined(ARDUINO_ARCH_ZEPHYR)
#include <SenseCAP.h>
#endif /* ARDUINO_ARCH_MBED */
#include <SGM41562.h>

#if defined(ENABLE_NFC)
#include <NFC.h>

extern "C" int nfcpins_enable(void);

void nfc_func(void *context, nfc_t2t_event_t event,
              const uint8_t *data, size_t dataLength)
{
    (void) context;

    switch (event)
    {
        case NFC_T2T_EVENT_FIELD_ON:
#if 0
            Serial.println("******NFC_T2T_EVENT_FIELD_ON******");
#endif
            break;

        case NFC_T2T_EVENT_FIELD_OFF:
#if 0
            Serial.println("------NFC_T2T_EVENT_FIELD_OFF------");
#endif
            break;

        default:
            break;
    }
}
#endif /* ENABLE_NFC */

static bool nRF52_bl_check(const char* signature)
{
  int  i, j;
  bool match    = false;
  int str_len   = strlen(signature);
  uint8_t* data = (uint8_t*) 0x000F4000UL;
  int length    = 0xFE000 - 0xF4000 - 2048 ; /* 38 KB */
  int offset    = 0x07000 ;

  data   += offset;
  length -= offset;

  for (i = 0; i < length - str_len; i++) {
    if (data[i] == signature[0]) {
      match = true;
      for (j = 1; j < str_len; j++) {
        if (data[i + j] != signature[j]) {
            match = false;
            break;
        }
      }
      if (match) {
        return true;
      }
    }
  }
  return false;
}

static void nRF52_system_off()
{
#if !defined(ARDUINO_ARCH_MBED) && !defined(ARDUINO_ARCH_ZEPHYR)
  uint8_t sd_en;
  (void) sd_softdevice_is_enabled(&sd_en);

  // Enter System OFF state
  if ( sd_en ) {
    sd_power_system_off();
  } else {
    NRF_POWER->SYSTEMOFF = 1;
  }
#else
  NRF_POWER->SYSTEMOFF = 1;
#endif /* ARDUINO_ARCH_MBED */
}

static void nRF52_setup()
{
  ui = &ui_settings;

#if !defined(ARDUINO_ARCH_MBED) && !defined(ARDUINO_ARCH_ZEPHYR)
  uint32_t reset_reason = readResetReason();
#else
  uint32_t reset_reason = 0; /* TBD */
#endif /* ARDUINO_ARCH_MBED */

  if      (reset_reason & POWER_RESETREAS_RESETPIN_Msk)
  {
      reset_info.reason = REASON_EXT_SYS_RST;
  }
  else if (reset_reason & POWER_RESETREAS_DOG_Msk)
  {
      reset_info.reason = REASON_WDT_RST;
  }
  else if (reset_reason & POWER_RESETREAS_SREQ_Msk)
  {
      reset_info.reason = REASON_SOFT_RESTART;
  }
  else if (reset_reason & POWER_RESETREAS_LOCKUP_Msk)
  {
      reset_info.reason = REASON_SOFT_WDT_RST;
  }
  else if (reset_reason & POWER_RESETREAS_OFF_Msk)
  {
      reset_info.reason = REASON_DEEP_SLEEP_AWAKE;
  }
  else if (reset_reason & POWER_RESETREAS_LPCOMP_Msk)
  {
      reset_info.reason = REASON_DEEP_SLEEP_AWAKE;
  }
  else if (reset_reason & POWER_RESETREAS_DIF_Msk)
  {
      reset_info.reason = REASON_DEEP_SLEEP_AWAKE;
  }
  else if (reset_reason & POWER_RESETREAS_NFC_Msk)
  {
      reset_info.reason = REASON_DEEP_SLEEP_AWAKE;
  }
  else if (reset_reason & POWER_RESETREAS_VBUS_Msk)
  {
      reset_info.reason = REASON_DEEP_SLEEP_AWAKE;
  }

  /* inactivate initVariant() of PCA10056 */
  pinMode(PIN_LED1, INPUT);
  pinMode(PIN_LED2, INPUT);
  pinMode(PIN_LED3, INPUT);
  pinMode(PIN_LED4, INPUT);

  nRF52_board = nRF52_bl_check("TECHOBOOT")      ? NRF52_LILYGO_TECHO_REV_2   :
                nRF52_bl_check("T1000-E")        ? NRF52_SEEED_T1000E         :
                nRF52_bl_check("HT-n5262")       ? NRF52_HELTEC_T114          :
                nRF52_bl_check("ThinkNodeM3")    ? NRF52_ELECROW_TN_M3        :
                nRF52_bl_check("ThinkNodeM6")    ? NRF52_ELECROW_TN_M6        :
                nRF52_bl_check("ThinkNodeM8")    ? NRF52_ELECROW_TN_M8        :
                nRF52_bl_check("ELECROWBOOT")    ? NRF52_ELECROW_TN_M1        :
                nRF52_bl_check("T-Impulse-Plus") ? NRF52_LILYGO_TIMPULSE_PLUS :
                nRF52_bl_check("T-Echo-Card")    ? NRF52_LILYGO_TECHO_CARD    :
                nRF52_bl_check("MeshTracker-X1") ? NRF52_SEEED_X1             :
#if !defined(EXCLUDE_WIP)
                nRF52_bl_check("T2000")          ? NRF52_SEEED_T2000          :
                nRF52_bl_check("TRACKER L1")     ? NRF52_SEEED_WIO_L1         :
#endif /* EXCLUDE_WIP */
                nRF52_board;

  for (int i=0; i < sizeof(techo_prototype_boards) / sizeof(prototype_entry_t); i++) {
    if (techo_prototype_boards[i].id == ((uint64_t) DEVICE_ID_HIGH << 32 | (uint64_t) DEVICE_ID_LOW)) {
      nRF52_board   = techo_prototype_boards[i].rev;
      nRF52_display = techo_prototype_boards[i].panel;
      break;
    }
  }

  switch (nRF52_board)
  {
    case NRF52_SEEED_T1000E:
      hw_info.model      = SOFTRF_MODEL_CARD;
      nRF5x_Device_Model = "Card Edition";
      nRF52_USB_VID      = 0x2886; /* Seeed Technology */
      nRF52_USB_PID      = 0x0057; /* SenseCAP T1000-E */

      if (reset_reason & POWER_RESETREAS_VBUS_Msk ||
          reset_reason & POWER_RESETREAS_RESETPIN_Msk) {
        NRF_POWER->GPREGRET = DFU_MAGIC_SKIP;
#if !defined(ARDUINO_ARCH_MBED) && !defined(ARDUINO_ARCH_ZEPHYR)
        pinMode(SOC_GPIO_PIN_T1000_BUTTON, INPUT_PULLDOWN_SENSE /* INPUT_SENSE_HIGH */);
#endif /* ARDUINO_ARCH_MBED */
        nRF52_system_off();
      }

      digitalWrite(SOC_GPIO_PIN_SFL_T1000_EN, HIGH);
      pinMode(SOC_GPIO_PIN_SFL_T1000_EN, OUTPUT);

      // digitalWrite(SOC_GPIO_LED_T1000_RED, HIGH);
      // pinMode(SOC_GPIO_LED_T1000_RED, OUTPUT);
      break;

    case NRF52_SEEED_X1:
      hw_info.model      = SOFTRF_MODEL_CARD_MK3;
      nRF5x_Device_Model = "Card Edition Mk3";
      nRF52_USB_VID      = 0x2886; /* Seeed Technology */
      nRF52_USB_PID      = 0x0057;

      if (reset_reason & POWER_RESETREAS_VBUS_Msk ||
          reset_reason & POWER_RESETREAS_RESETPIN_Msk) {
        NRF_POWER->GPREGRET = DFU_MAGIC_SKIP;
#if !defined(ARDUINO_ARCH_MBED) && !defined(ARDUINO_ARCH_ZEPHYR)
        pinMode(SOC_GPIO_PIN_X1_BUTTON, INPUT_PULLDOWN_SENSE /* INPUT_SENSE_HIGH */);
#endif /* ARDUINO_ARCH_MBED */
        nRF52_system_off();
      }

      digitalWrite(SOC_GPIO_PIN_X1_3V3_EN, HIGH);
      pinMode(SOC_GPIO_PIN_X1_3V3_EN, OUTPUT);
      digitalWrite(SOC_GPIO_PIN_SFL_X1_EN, HIGH);
      pinMode(SOC_GPIO_PIN_SFL_X1_EN, OUTPUT);
      digitalWrite(SOC_GPIO_PIN_X1_HAPTIC_EN, HIGH);
      pinMode(SOC_GPIO_PIN_X1_HAPTIC_EN, OUTPUT);
      digitalWrite(SOC_GPIO_PIN_X1_RTC_EN, HIGH);
      pinMode(SOC_GPIO_PIN_X1_RTC_EN, OUTPUT);
      delay(30);

      break;

#if !defined(EXCLUDE_WIP)
    case NRF52_SEEED_WIO_L1:
      hw_info.model      = SOFTRF_MODEL_DECENT;
      nRF5x_Device_Model = "Decent Edition";
      nRF52_USB_VID      = 0x2886; /* Seeed Technology */
      nRF52_USB_PID      = 0x1668; /* Wio Tracker L1 */

      if (reset_reason & POWER_RESETREAS_VBUS_Msk) {
        NRF_POWER->GPREGRET = DFU_MAGIC_SKIP;
#if !defined(ARDUINO_ARCH_MBED) && !defined(ARDUINO_ARCH_ZEPHYR)
        pinMode(SOC_GPIO_PIN_L1_BUTTON, INPUT_PULLUP_SENSE);
#endif /* ARDUINO_ARCH_MBED */
        nRF52_system_off();
      }

      break;

    case NRF52_SEEED_T2000:
      hw_info.model      = SOFTRF_MODEL_RUGGED;
      nRF5x_Device_Model = "Rugged Edition";
      nRF52_USB_VID      = 0x2886; /* Seeed Technology */
      nRF52_USB_PID      = 0x1668; /* TBD */

      if (reset_reason & POWER_RESETREAS_VBUS_Msk) {
        NRF_POWER->GPREGRET = DFU_MAGIC_SKIP;
#if !defined(ARDUINO_ARCH_MBED) && !defined(ARDUINO_ARCH_ZEPHYR)
        pinMode(SOC_GPIO_PIN_T2000_BUTTON, INPUT_PULLUP_SENSE);
#endif /* ARDUINO_ARCH_MBED */
        nRF52_system_off();
      }

      break;
#endif /* EXCLUDE_WIP */

    case NRF52_HELTEC_T114:
      hw_info.model      = SOFTRF_MODEL_COZY;
      nRF5x_Device_Model = "Cozy Edition";

      if (reset_reason & POWER_RESETREAS_VBUS_Msk) {
        NRF_POWER->GPREGRET = DFU_MAGIC_SKIP;
#if !defined(ARDUINO_ARCH_MBED) && !defined(ARDUINO_ARCH_ZEPHYR)
        pinMode(SOC_GPIO_PIN_T114_BUTTON, INPUT_PULLUP_SENSE);
#endif /* ARDUINO_ARCH_MBED */
        nRF52_system_off();
      }

      break;

    case NRF52_ELECROW_TN_M1: /* "ELECROWBOOT" */
    case NRF52_ELECROW_TN_M3: /* "ELECROWBOOT" , "ThinkNodeM3" */
      pinMode(SOC_GPIO_PIN_M3_EEPROM_EN,  INPUT_PULLUP);
      pinMode(SOC_GPIO_PIN_M3_TEMP_EN,    INPUT_PULLUP);
      delay(5);

#if !defined(ARDUINO_ARCH_MBED) && !defined(ARDUINO_ARCH_ZEPHYR)
      Wire.setPins(SOC_GPIO_PIN_M3_SDA, SOC_GPIO_PIN_M3_SCL);
#endif /* ARDUINO_ARCH_MBED */
      Wire.begin();
      Wire.beginTransmission(AHT20_ADDRESS);
      if (Wire.endTransmission() == 0) {
        nRF52_board        = NRF52_ELECROW_TN_M3;
        hw_info.model      = SOFTRF_MODEL_POCKET;
        nRF5x_Device_Model = "Pocket Edition";
      } else {
        hw_info.model      = SOFTRF_MODEL_HANDHELD;
        nRF5x_Device_Model = "Handheld Edition";
      }
      Wire.end();
      pinMode(SOC_GPIO_PIN_M3_TEMP_EN,    INPUT);
      pinMode(SOC_GPIO_PIN_M3_EEPROM_EN,  INPUT);

      if (reset_reason & POWER_RESETREAS_VBUS_Msk) {
        NRF_POWER->GPREGRET = DFU_MAGIC_SKIP;
#if !defined(ARDUINO_ARCH_MBED) && !defined(ARDUINO_ARCH_ZEPHYR)
        pinMode(nRF52_board == NRF52_ELECROW_TN_M1 ?
                SOC_GPIO_PIN_M1_BUTTON1 : SOC_GPIO_PIN_M3_BUTTON,
                INPUT_PULLUP_SENSE);
#endif /* ARDUINO_ARCH_MBED */
        nRF52_system_off();
      }

      break;

    case NRF52_ELECROW_TN_M6: /* "ThinkNodeM6" */
      hw_info.model      = SOFTRF_MODEL_SOLARIS;
      nRF5x_Device_Model = "Solaris Edition";

      if (reset_reason & POWER_RESETREAS_VBUS_Msk ||
          reset_reason & POWER_RESETREAS_RESETPIN_Msk) {
        NRF_POWER->GPREGRET = DFU_MAGIC_SKIP;
#if !defined(ARDUINO_ARCH_MBED) && !defined(ARDUINO_ARCH_ZEPHYR)
        pinMode(SOC_GPIO_PIN_M6_BUTTON, INPUT_PULLUP_SENSE);
#endif /* ARDUINO_ARCH_MBED */
        nRF52_system_off();
      }

      pinMode(SOC_GPIO_PIN_SFL_M6_EN, INPUT_PULLUP);

      break;

    case NRF52_LILYGO_TIMPULSE_PLUS:
      hw_info.model      = SOFTRF_MODEL_STYLUS;
      nRF5x_Device_Model = "Stylus Edition";

      if (reset_reason & POWER_RESETREAS_VBUS_Msk ||
          reset_reason & POWER_RESETREAS_RESETPIN_Msk) {
        NRF_POWER->GPREGRET = DFU_MAGIC_SKIP;
#if !defined(ARDUINO_ARCH_MBED) && !defined(ARDUINO_ARCH_ZEPHYR)
        pinMode(SOC_GPIO_PIN_TIP_PAD, INPUT_PULLUP_SENSE); /* TBD */
#endif /* ARDUINO_ARCH_MBED */
        nRF52_system_off();
      }

      digitalWrite(SOC_GPIO_PIN_TIP_3V3_EN, HIGH);
      pinMode(SOC_GPIO_PIN_TIP_3V3_EN, OUTPUT);
      delay(30);

      break;

    case NRF52_LILYGO_TECHO_CARD:
      hw_info.model      = SOFTRF_MODEL_CARD_MK2;
      nRF5x_Device_Model = "Card Edition Mk2";

      if (reset_reason & POWER_RESETREAS_VBUS_Msk ||
          reset_reason & POWER_RESETREAS_RESETPIN_Msk) {
        NRF_POWER->GPREGRET = DFU_MAGIC_SKIP;
#if !defined(ARDUINO_ARCH_MBED) && !defined(ARDUINO_ARCH_ZEPHYR)
        pinMode(SOC_GPIO_PIN_TEC_BUTTON, INPUT_PULLUP_SENSE); /* TBD */
#endif /* ARDUINO_ARCH_MBED */
        nRF52_system_off();
      }

      digitalWrite(SOC_GPIO_PIN_TEC_3V3_EN, HIGH);
      pinMode(SOC_GPIO_PIN_TEC_3V3_EN, OUTPUT);
      delay(30);

      break;

    case NRF52_LILYGO_TECHO_REV_0:
    case NRF52_LILYGO_TECHO_REV_1:
    case NRF52_LILYGO_TECHO_REV_2:
    case NRF52_LILYGO_TECHO_PLUS:
    case NRF52_NORDIC_PCA10059:
    default:
      pinMode(SOC_GPIO_PIN_3V3_PWR, INPUT);
      pinMode(SOC_GPIO_PIN_IO_PWR,  INPUT_PULLUP);
      if (nRF52_board == NRF52_LILYGO_TECHO_REV_1) {
        pinMode(SOC_GPIO_PIN_TECHO_REV_1_3V3_PWR,  INPUT_PULLUP);
      }
      break;
  }

#if !defined(ARDUINO_ARCH_MBED) && !defined(ARDUINO_ARCH_ZEPHYR)
  USBDevice.setID(nRF52_USB_VID, nRF52_USB_PID);
  USBDevice.setManufacturerDescriptor(nRF5x_Device_Manufacturer);
  USBDevice.setProductDescriptor(nRF5x_Device_Model);
  USBDevice.setDeviceVersion(nRF52_Device_Version);
#endif /* ARDUINO_ARCH_MBED */

#if !defined(ARDUINO_ARCH_MBED) && !defined(ARDUINO_ARCH_ZEPHYR)
  switch (nRF52_board)
  {
#if !defined(EXCLUDE_WIP)
    case NRF52_SEEED_WIO_L1:
      Wire.setPins(SOC_GPIO_PIN_L1_OLED_SDA, SOC_GPIO_PIN_L1_OLED_SCL); /* TBD */
      break;
    case NRF52_SEEED_T2000:
      Wire.setPins(SOC_GPIO_PIN_T2000_SDA, SOC_GPIO_PIN_T2000_SCL);
      break;
    case NRF52_HELTEC_T1:
      Wire.setPins(SOC_GPIO_PIN_T1_SDA, SOC_GPIO_PIN_T1_SCL);
      break;
    case NRF52_ELECROW_TN_M8:
      Wire.setPins(SOC_GPIO_PIN_M8_SDA, SOC_GPIO_PIN_M8_SCL);
      digitalWrite(SOC_GPIO_PIN_M8_IIC_EN, HIGH);
      pinMode(SOC_GPIO_PIN_M8_IIC_EN, OUTPUT);
      break;
#endif /* EXCLUDE_WIP */
    case NRF52_SEEED_T1000E:
      Wire.setPins(SOC_GPIO_PIN_T1000_SDA, SOC_GPIO_PIN_T1000_SCL);
#if !defined(EXCLUDE_IMU)
      pinMode(SOC_GPIO_PIN_T1000_ACC_EN, INPUT_PULLUP);
      delay(100);
      Wire.begin();
      Wire.beginTransmission(QMA6100P_ADDRESS);
      nRF52_has_imu = (Wire.endTransmission() == 0);
      Wire.end();
#endif /* EXCLUDE_IMU */
      break;
    case NRF52_ELECROW_TN_M3:
      Wire.setPins(SOC_GPIO_PIN_M3_SDA, SOC_GPIO_PIN_M3_SCL);

#if !defined(EXCLUDE_IMU)
      pinMode(SOC_GPIO_PIN_M3_ACC_EN,       INPUT_PULLUP);
#endif /* EXCLUDE_IMU */

      pinMode(SOC_GPIO_PIN_M3_TEMP_EN,      INPUT_PULLUP);
      pinMode(SOC_GPIO_PIN_M3_EEPROM_EN,    INPUT_PULLUP);
      break;
    case NRF52_ELECROW_TN_M6:
      Wire.setPins(SOC_GPIO_PIN_M6_SDA, SOC_GPIO_PIN_M6_SCL);
      digitalWrite(SOC_GPIO_PIN_IO_M6_PWR, HIGH);
      pinMode(SOC_GPIO_PIN_IO_M6_PWR, OUTPUT);
      break;
    case NRF52_LILYGO_TIMPULSE_PLUS:
      Wire.setPins (SOC_GPIO_PIN_TIP_OLED_SDA, SOC_GPIO_PIN_TIP_OLED_SCL);
      Wire1.setPins(SOC_GPIO_PIN_TIP_SDA,      SOC_GPIO_PIN_TIP_SCL);
#if !defined(EXCLUDE_IMU)
      Wire1.begin();
      Wire1.beginTransmission(ICM20948_ADDRESS_ALT);
      nRF52_has_imu = (Wire1.endTransmission() == 0);
      Wire1.end();
#endif /* EXCLUDE_IMU */
      break;
    case NRF52_LILYGO_TECHO_CARD:
      Wire.setPins (SOC_GPIO_PIN_TEC_SDA, SOC_GPIO_PIN_TEC_SCL);
      break;
    case NRF52_SEEED_X1:
      Wire.setPins (SOC_GPIO_PIN_X1_SDA,     SOC_GPIO_PIN_X1_SCL);
      Wire1.setPins(SOC_GPIO_PIN_X1_RTC_SDA, SOC_GPIO_PIN_X1_RTC_SCL);
      break;
    case NRF52_HELTEC_T114:
      /* external bus */
      Wire.setPins(SOC_GPIO_PIN_T114_SDA_EXT, SOC_GPIO_PIN_T114_SCL_EXT);
      break;
    case NRF52_LILYGO_TECHO_REV_0:
    case NRF52_LILYGO_TECHO_REV_1:
    case NRF52_LILYGO_TECHO_REV_2:
    case NRF52_LILYGO_TECHO_PLUS:
    case NRF52_ELECROW_TN_M1:
    case NRF52_NORDIC_PCA10059:
      digitalWrite(SOC_GPIO_PIN_IO_PWR, HIGH);
      pinMode(SOC_GPIO_PIN_IO_PWR, OUTPUT); /* VDD_POWR is ON */
    default:
      Wire.setPins(SOC_GPIO_PIN_SDA, SOC_GPIO_PIN_SCL);
      break;
  }
#endif /* ARDUINO_ARCH_MBED */

  if (nRF52_board == NRF52_SEEED_X1) {
    Wire1.begin();
    Wire1.beginTransmission(YSN8900_ADDRESS);
    nRF52_has_rtc = (Wire1.endTransmission() == 0);
    Wire1.end();
  } else {
    Wire.begin();

    Wire.beginTransmission(PCF8563_SLAVE_ADDRESS);
    nRF52_has_rtc = (Wire.endTransmission() == 0);
    if (!nRF52_has_rtc) {
      delay(5);
      Wire.beginTransmission(PCF8563_SLAVE_ADDRESS);
      nRF52_has_rtc = (Wire.endTransmission() == 0);
      if (!nRF52_has_rtc) {
        delay(5);
        Wire.beginTransmission(PCF8563_SLAVE_ADDRESS);
        nRF52_has_rtc = (Wire.endTransmission() == 0);
      }
    }

#if !defined(EXCLUDE_IMU)
    if (nRF52_board == NRF52_LILYGO_TECHO_REV_2 ||
        nRF52_board == NRF52_LILYGO_TECHO_CARD) { /* T-Echo, T114 or M1 */
      /* MPU9250 or ICM20948 start-up time for register R/W is 11-100 ms */
      delay(90);

      Wire.beginTransmission(MPU9250_ADDRESS);
      nRF52_has_imu = (Wire.endTransmission() == 0);
      if (nRF52_has_imu == false) {
        Wire.beginTransmission(ICM20948_ADDRESS);
        nRF52_has_imu = (Wire.endTransmission() == 0);
        if (nRF52_has_imu == false) {
          Wire.beginTransmission(BHI260AP_ADDRESS_L);
          nRF52_has_imu = (Wire.endTransmission() == 0);

          if (nRF52_has_imu) {
            Wire.beginTransmission(DRV2605_ADDRESS);
            if (Wire.endTransmission() == 0) {
              nRF52_board = NRF52_LILYGO_TECHO_PLUS;
            }
          }
        }
      }
    } else if (nRF52_board == NRF52_ELECROW_TN_M3 ||
               nRF52_board == NRF52_ELECROW_TN_M8) {
      Wire.beginTransmission(SC7A20H_ADDRESS_H);
      nRF52_has_imu = (Wire.endTransmission() == 0);
    }
#endif /* EXCLUDE_IMU */

    Wire.end();
  }

#if !defined(ARDUINO_ARCH_MBED) && !defined(ARDUINO_ARCH_ZEPHYR)
  /* (Q)SPI flash init */

  switch (nRF52_board)
  {
    case NRF52_LILYGO_TECHO_REV_0:
      possible_devices[MX25R1635F_INDEX].max_clock_speed_mhz  = 33;
      possible_devices[MX25R1635F_INDEX].supports_qspi        = false;
      possible_devices[MX25R1635F_INDEX].supports_qspi_writes = false;
    case NRF52_LILYGO_TECHO_REV_1:
    case NRF52_LILYGO_TECHO_REV_2:
    case NRF52_LILYGO_TECHO_PLUS:
    case NRF52_HELTEC_T114:
    case NRF52_ELECROW_TN_M1:
    case NRF52_ELECROW_TN_M8:
      FlashTrans = new Adafruit_FlashTransport_QSPI(SOC_GPIO_PIN_SFL_SCK,
                                                    SOC_GPIO_PIN_SFL_SS,
                                                    SOC_GPIO_PIN_SFL_MOSI,
                                                    SOC_GPIO_PIN_SFL_MISO,
                                                    SOC_GPIO_PIN_SFL_WP,
                                                    SOC_GPIO_PIN_SFL_HOLD);
      break;
    case NRF52_SEEED_T1000E:
    case NRF52_SEEED_X1:
      FlashTrans = new Adafruit_FlashTransport_QSPI(SOC_GPIO_PIN_SFL_T1000_SCK,
                                                    SOC_GPIO_PIN_SFL_T1000_SS,
                                                    SOC_GPIO_PIN_SFL_T1000_MOSI,
                                                    SOC_GPIO_PIN_SFL_T1000_MISO,
                                                    SOC_GPIO_PIN_SFL_T1000_WP,
                                                    SOC_GPIO_PIN_SFL_T1000_HOLD);
      break;
    case NRF52_ELECROW_TN_M6:
      FlashTrans = new Adafruit_FlashTransport_QSPI(SOC_GPIO_PIN_SFL_M6_SCK,
                                                    SOC_GPIO_PIN_SFL_M6_SS,
                                                    SOC_GPIO_PIN_SFL_M6_MOSI,
                                                    SOC_GPIO_PIN_SFL_M6_MISO,
                                                    SOC_GPIO_PIN_SFL_M6_WP,
                                                    SOC_GPIO_PIN_SFL_M6_HOLD);
      break;
    case NRF52_LILYGO_TIMPULSE_PLUS:
      FlashTrans = new Adafruit_FlashTransport_QSPI(SOC_GPIO_PIN_SFL_TIP_SCK,
                                                    SOC_GPIO_PIN_SFL_TIP_SS,
                                                    SOC_GPIO_PIN_SFL_TIP_MOSI,
                                                    SOC_GPIO_PIN_SFL_TIP_MISO,
                                                    SOC_GPIO_PIN_SFL_TIP_WP,
                                                    SOC_GPIO_PIN_SFL_TIP_HOLD);
      break;
    case NRF52_LILYGO_TECHO_CARD:
      FlashTrans = new Adafruit_FlashTransport_QSPI(SOC_GPIO_PIN_SFL_TEC_SCK,
                                                    SOC_GPIO_PIN_SFL_TEC_SS,
                                                    SOC_GPIO_PIN_SFL_TEC_MOSI,
                                                    SOC_GPIO_PIN_SFL_TEC_MISO,
                                                    SOC_GPIO_PIN_SFL_TEC_WP,
                                                    SOC_GPIO_PIN_SFL_TEC_HOLD);
      break;
#if !defined(EXCLUDE_WIP)
    case NRF52_SEEED_WIO_L1:
      FlashTrans = new Adafruit_FlashTransport_QSPI(SOC_GPIO_PIN_SFL_L1_SCK,
                                                    SOC_GPIO_PIN_SFL_L1_SS,
                                                    SOC_GPIO_PIN_SFL_L1_MOSI,
                                                    SOC_GPIO_PIN_SFL_L1_MISO,
                                                    SOC_GPIO_PIN_SFL_L1_WP,
                                                    SOC_GPIO_PIN_SFL_L1_HOLD);
      break;
    case NRF52_SEEED_T2000:
      FlashTrans = new Adafruit_FlashTransport_QSPI(SOC_GPIO_PIN_SFL_T2000_SCK,
                                                    SOC_GPIO_PIN_SFL_T2000_SS,
                                                    SOC_GPIO_PIN_SFL_T2000_MOSI,
                                                    SOC_GPIO_PIN_SFL_T2000_MISO,
                                                    SOC_GPIO_PIN_SFL_T2000_WP,
                                                    SOC_GPIO_PIN_SFL_T2000_HOLD);
      break;
#endif /* EXCLUDE_WIP */
    case NRF52_NORDIC_PCA10059:
    case NRF52_ELECROW_TN_M3:
    default:
      break;
  }

  if (FlashTrans != NULL) {
    FlashTrans->begin();
    FlashTrans->runCommand(0xAB); /* RDP/RES */
    FlashTrans->end();

    SPIFlash = new Adafruit_SPIFlash(FlashTrans);
    nRF52_has_spiflash = SPIFlash->begin(possible_devices,
                                         EXTERNAL_FLASH_DEVICE_COUNT);
  }
#endif /* ARDUINO_ARCH_MBED */

  hw_info.storage = nRF52_has_spiflash ? STORAGE_FLASH : STORAGE_NONE;

#if defined(USE_TINYUSB)
  switch (nRF52_board)
  {
#if !defined(EXCLUDE_WIP)
    case NRF52_SEEED_T2000:
      Serial1.setPins(SOC_GPIO_PIN_CONS_T2000_RX, SOC_GPIO_PIN_CONS_T2000_TX);
#if defined(EXCLUDE_WIFI)
      Serial1.begin(SERIAL_OUT_BR, SERIAL_OUT_BITS);
#endif /* EXCLUDE_WIFI */
      break;
    case NRF52_HELTEC_T1:
      /* TBD */
      break;
#endif /* EXCLUDE_WIP */
    case NRF52_SEEED_T1000E:
    case NRF52_SEEED_X1:
      Serial1.setPins(SOC_GPIO_PIN_CONS_T1000_RX, SOC_GPIO_PIN_CONS_T1000_TX);
#if defined(EXCLUDE_WIFI)
      Serial1.begin(SERIAL_OUT_BR, SERIAL_OUT_BITS);
#endif /* EXCLUDE_WIFI */
      break;
    case NRF52_ELECROW_TN_M6:
      Serial1.setPins(SOC_GPIO_PIN_CONS_M6_RX, SOC_GPIO_PIN_CONS_M6_TX);
#if defined(EXCLUDE_WIFI)
      Serial1.begin(SERIAL_OUT_BR, SERIAL_OUT_BITS);
#endif /* EXCLUDE_WIFI */
      break;
    case NRF52_HELTEC_T114:
    case NRF52_ELECROW_TN_M1:
    case NRF52_ELECROW_TN_M3:
    case NRF52_ELECROW_TN_M8:
    case NRF52_SEEED_WIO_L1:
    case NRF52_LILYGO_TECHO_PLUS:
    case NRF52_LILYGO_TECHO_CARD:
    case NRF52_LILYGO_TIMPULSE_PLUS:
      Serial1.setPins(SOC_GPIO_PIN_CONS_T114_RX, SOC_GPIO_PIN_CONS_T114_TX);
#if defined(EXCLUDE_WIFI)
      Serial1.begin(SERIAL_OUT_BR, SERIAL_OUT_BITS);
#endif /* EXCLUDE_WIFI */
      break;
    case NRF52_LILYGO_TECHO_REV_0:
    case NRF52_LILYGO_TECHO_REV_1:
    case NRF52_LILYGO_TECHO_REV_2:
    case NRF52_NORDIC_PCA10059:
    default:
      Serial1.setPins(SOC_GPIO_PIN_CONS_RX, SOC_GPIO_PIN_CONS_TX);
#if defined(EXCLUDE_WIFI)
      Serial1.begin(SERIAL_OUT_BR, SERIAL_OUT_BITS);
#endif /* EXCLUDE_WIFI */
      break;
  }
#endif /* USE_TINYUSB */

  switch (nRF52_board)
  {
#if !defined(EXCLUDE_WIP)
    case NRF52_SEEED_WIO_L1:
      digitalWrite(SOC_GPIO_PIN_L1_VBAT_EN, HIGH);
      pinMode(SOC_GPIO_PIN_L1_VBAT_EN, OUTPUT);
      /* TBD */
      break;
    case NRF52_SEEED_T2000:
      digitalWrite(SOC_GPIO_PIN_T2000_VBAT_EN, HIGH);
      pinMode(SOC_GPIO_PIN_T2000_VBAT_EN, OUTPUT);
      /* TBD */
      break;
    case NRF52_HELTEC_T1:
      digitalWrite(SOC_GPIO_PIN_T1_ADC_EN, HIGH);
      pinMode(SOC_GPIO_PIN_T1_ADC_EN, OUTPUT);
      /* TBD */
      break;
    case NRF52_ELECROW_TN_M8:
      digitalWrite(SOC_GPIO_PIN_M8_ADC_EN, HIGH);
      pinMode(SOC_GPIO_PIN_M8_ADC_EN, OUTPUT);
      digitalWrite(SOC_GPIO_PIN_EPD_M8_EN, HIGH);
      pinMode(SOC_GPIO_PIN_EPD_M8_EN, OUTPUT);
      /* TBD */
      break;
#endif /* EXCLUDE_WIP */

    case NRF52_SEEED_T1000E:
      digitalWrite(SOC_GPIO_PIN_T1000_3V3_EN, HIGH);
      pinMode(SOC_GPIO_PIN_T1000_3V3_EN, OUTPUT);

      digitalWrite(SOC_GPIO_PIN_T1000_BUZZER_EN, HIGH);
      pinMode(SOC_GPIO_PIN_T1000_BUZZER_EN, OUTPUT);
      break;

    case NRF52_HELTEC_T114:
      digitalWrite(SOC_GPIO_PIN_T114_VEXT_EN, HIGH);
      pinMode(SOC_GPIO_PIN_T114_VEXT_EN, OUTPUT);

      delay(200);

      digitalWrite(SOC_GPIO_PIN_T114_TFT_EN, LOW);
      pinMode(SOC_GPIO_PIN_T114_TFT_EN, OUTPUT);
      digitalWrite(SOC_GPIO_PIN_T114_TFT_BLGT, LOW);
      pinMode(SOC_GPIO_PIN_T114_TFT_BLGT, OUTPUT);

      digitalWrite(SOC_GPIO_PIN_T114_ADC_EN, HIGH);
      pinMode(SOC_GPIO_PIN_T114_ADC_EN, OUTPUT);
      break;

    case NRF52_ELECROW_TN_M1:
      /* TBD */
      // digitalWrite(SOC_GPIO_PIN_M1_DIO3, HIGH);
      // pinMode(SOC_GPIO_PIN_M1_DIO3, OUTPUT);
      break;

    case NRF52_ELECROW_TN_M3:
      digitalWrite(SOC_GPIO_PIN_M3_ADC_EN, HIGH);
      pinMode(SOC_GPIO_PIN_M3_ADC_EN, OUTPUT);

      digitalWrite(SOC_GPIO_PIN_M3_EN1, HIGH);
      pinMode(SOC_GPIO_PIN_M3_EN1, OUTPUT);
      digitalWrite(SOC_GPIO_PIN_M3_EN2, HIGH);
      pinMode(SOC_GPIO_PIN_M3_EN2, OUTPUT);

      pinMode(SOC_GPIO_PIN_M3_BUT_EN, INPUT_PULLUP);
      break;

    case NRF52_ELECROW_TN_M6:
      digitalWrite(SOC_GPIO_PIN_M6_ADC_EN, HIGH);
      pinMode(SOC_GPIO_PIN_M6_ADC_EN, OUTPUT);
      /* TBD */
      break;

    case NRF52_LILYGO_TIMPULSE_PLUS:
      digitalWrite(SOC_GPIO_PIN_TIP_VBAT_EN, HIGH);
      pinMode(SOC_GPIO_PIN_TIP_VBAT_EN, OUTPUT);
      /* TBD */
      break;

    case NRF52_LILYGO_TECHO_CARD:
      digitalWrite(SOC_GPIO_PIN_TEC_VBAT_EN, HIGH);
      pinMode(SOC_GPIO_PIN_TEC_VBAT_EN, OUTPUT);

      digitalWrite(SOC_GPIO_PIN_I2S_TEC_EN, HIGH);
      pinMode(SOC_GPIO_PIN_I2S_TEC_EN, OUTPUT);

      digitalWrite(SOC_GPIO_PIN_I2S_TEC_PWR, HIGH);
      pinMode(SOC_GPIO_PIN_I2S_TEC_PWR, OUTPUT);
      /* TBD */
      break;

    case NRF52_SEEED_X1:
      digitalWrite(SOC_GPIO_PIN_X1_VBAT_EN, HIGH);
      pinMode(SOC_GPIO_PIN_X1_VBAT_EN, OUTPUT);
      /* TBD */
      break;

    case NRF52_LILYGO_TECHO_REV_0:
    case NRF52_LILYGO_TECHO_REV_1:
    case NRF52_LILYGO_TECHO_REV_2:
    case NRF52_LILYGO_TECHO_PLUS:
    case NRF52_NORDIC_PCA10059:
    default:
      break;
  }

  /* GPIO pins init */
  switch (nRF52_board)
  {
    case NRF52_LILYGO_TECHO_REV_0:
      /* Wake up Air530 GNSS */
      digitalWrite(SOC_GPIO_PIN_GNSS_WKE, HIGH);
      pinMode(SOC_GPIO_PIN_GNSS_WKE, OUTPUT);

      pinMode(SOC_GPIO_LED_TECHO_REV_0_GREEN, OUTPUT);
      pinMode(SOC_GPIO_LED_TECHO_REV_0_RED,   OUTPUT);
      pinMode(SOC_GPIO_LED_TECHO_REV_0_BLUE,  OUTPUT);

      ledOn (SOC_GPIO_LED_TECHO_REV_0_GREEN);
      ledOff(SOC_GPIO_LED_TECHO_REV_0_RED);
      ledOff(SOC_GPIO_LED_TECHO_REV_0_BLUE);

      lmic_pins.rst = SOC_GPIO_PIN_TECHO_REV_0_RST;

      hw_info.revision = 0;
      hw_info.touch    = TOUCH_TTP223;
      break;

    case NRF52_LILYGO_TECHO_REV_1:
      /* Wake up Air530 GNSS */
      digitalWrite(SOC_GPIO_PIN_GNSS_WKE, HIGH);
      pinMode(SOC_GPIO_PIN_GNSS_WKE, OUTPUT);

      pinMode(SOC_GPIO_LED_TECHO_REV_1_GREEN, OUTPUT);
      pinMode(SOC_GPIO_LED_TECHO_REV_1_RED,   OUTPUT);
      pinMode(SOC_GPIO_LED_TECHO_REV_1_BLUE,  OUTPUT);

      ledOn (SOC_GPIO_LED_TECHO_REV_1_GREEN);
      ledOff(SOC_GPIO_LED_TECHO_REV_1_RED);
      ledOff(SOC_GPIO_LED_TECHO_REV_1_BLUE);

      lmic_pins.rst = SOC_GPIO_PIN_TECHO_REV_1_RST;

      hw_info.revision = 1;
      hw_info.touch    = TOUCH_TTP223;
      break;

    case NRF52_LILYGO_TECHO_REV_2:
    case NRF52_LILYGO_TECHO_PLUS:
      /* Wake up Quectel L76K GNSS */
      digitalWrite(SOC_GPIO_PIN_GNSS_RST, HIGH);
      pinMode(SOC_GPIO_PIN_GNSS_RST, OUTPUT);
      digitalWrite(SOC_GPIO_PIN_GNSS_WKE, HIGH);
      pinMode(SOC_GPIO_PIN_GNSS_WKE, OUTPUT);

      pinMode(SOC_GPIO_LED_TECHO_REV_2_GREEN, OUTPUT);
      pinMode(SOC_GPIO_LED_TECHO_REV_2_RED,   OUTPUT);
      pinMode(SOC_GPIO_LED_TECHO_REV_2_BLUE,  OUTPUT);

      ledOn (SOC_GPIO_LED_TECHO_REV_2_GREEN);
      ledOff(SOC_GPIO_LED_TECHO_REV_2_RED);
      ledOff(SOC_GPIO_LED_TECHO_REV_2_BLUE);

      lmic_pins.rst = SOC_GPIO_PIN_TECHO_REV_2_RST;
#if defined(USE_RADIOLIB)
      lmic_pins.dio[0] = SOC_GPIO_PIN_DIO1; /* reserved for DIO11 of HPD-16E */
#endif /* USE_RADIOLIB */

      hw_info.revision = 2;
      hw_info.touch    = TOUCH_TTP223;
      break;

#if !defined(EXCLUDE_WIP)
    case NRF52_SEEED_WIO_L1:
      /* Wake up Quectel L76K GNSS */
      digitalWrite(SOC_GPIO_PIN_GNSS_L1_WKE, HIGH);
      pinMode(SOC_GPIO_PIN_GNSS_L1_WKE, OUTPUT);

      pinMode(SOC_GPIO_LED_L1_GREEN, OUTPUT);
      // pinMode(SOC_GPIO_LED_L1_BLUE,  OUTPUT);

      digitalWrite(SOC_GPIO_LED_L1_GREEN, LED_STATE_ON);
      // digitalWrite(SOC_GPIO_LED_L1_BLUE,  LED_STATE_ON);

      lmic_pins.nss  = SOC_GPIO_PIN_L1_SS;
      lmic_pins.rst  = SOC_GPIO_PIN_L1_RST;
      lmic_pins.busy = SOC_GPIO_PIN_L1_BUSY;

      hw_info.revision = 3; /* Unknown */
      break;

    case NRF52_SEEED_T2000:
      /* Wake up Quectel L76K GNSS */
      digitalWrite(SOC_GPIO_PIN_GNSS_T2000_WKE, HIGH);
      pinMode(SOC_GPIO_PIN_GNSS_T2000_WKE, OUTPUT);

      pinMode(SOC_GPIO_LED_T2000_GREEN, OUTPUT);
      // pinMode(SOC_GPIO_LED_T2000_BLUE,  OUTPUT);

      digitalWrite(SOC_GPIO_LED_T2000_GREEN, LED_STATE_ON);
      // digitalWrite(SOC_GPIO_LED_T2000_BLUE,  LED_STATE_ON);

      lmic_pins.nss  = SOC_GPIO_PIN_T2000_SS;
      lmic_pins.rst  = SOC_GPIO_PIN_T2000_RST;
      lmic_pins.busy = SOC_GPIO_PIN_T2000_BUSY;

      hw_info.revision = 3; /* Unknown */
      break;

    case NRF52_HELTEC_T1:
      /* Power on up UC6580 GNSS */
      digitalWrite(SOC_GPIO_PIN_GNSS_T1_EN, LOW);
      pinMode(SOC_GPIO_PIN_GNSS_T1_EN, OUTPUT);

      pinMode(SOC_GPIO_LED_T1_WHITE, OUTPUT);
      digitalWrite(SOC_GPIO_LED_T1_WHITE, LED_STATE_ON);

      lmic_pins.nss  = SOC_GPIO_PIN_T1_SS;
      lmic_pins.rst  = SOC_GPIO_PIN_T1_RST;
      lmic_pins.busy = SOC_GPIO_PIN_T1_BUSY;

      pinMode(SOC_GPIO_PIN_T1_SENS_INT1, INPUT);
      pinMode(SOC_GPIO_PIN_T1_SENS_INT2, INPUT);

      hw_info.revision = 3; /* Unknown */
      break;

    case NRF52_ELECROW_TN_M8:
      digitalWrite(SOC_GPIO_PIN_GNSS_M8_EN, HIGH);
      pinMode(SOC_GPIO_PIN_GNSS_M8_EN, OUTPUT);

      /* Wake up Quectel L76K GNSS */
      digitalWrite(SOC_GPIO_PIN_GNSS_M8_RST, LOW);
      pinMode(SOC_GPIO_PIN_GNSS_M8_RST, OUTPUT);
      digitalWrite(SOC_GPIO_PIN_GNSS_M8_WKE, HIGH);
      pinMode(SOC_GPIO_PIN_GNSS_M8_WKE, OUTPUT);

      lmic_pins.nss  = SOC_GPIO_PIN_M8_SS;
      lmic_pins.rst  = SOC_GPIO_PIN_M8_RST;
      lmic_pins.busy = SOC_GPIO_PIN_M8_BUSY;

      pinMode(SOC_GPIO_PIN_M8_ANT_SW,   INPUT_PULLUP);

      hw_info.revision = 3; /* Unknown */
      hw_info.audio    = AUDIO_PWM;
      break;
#endif /* EXCLUDE_WIP */

    case NRF52_SEEED_T1000E:
      digitalWrite(SOC_GPIO_PIN_GNSS_T1000_EN, HIGH);
      pinMode(SOC_GPIO_PIN_GNSS_T1000_EN, OUTPUT);

      digitalWrite(SOC_GPIO_PIN_GNSS_T1000_VRTC, HIGH);
      pinMode(SOC_GPIO_PIN_GNSS_T1000_VRTC, OUTPUT);

      digitalWrite(SOC_GPIO_PIN_GNSS_T1000_RST, LOW);
      pinMode(SOC_GPIO_PIN_GNSS_T1000_RST, OUTPUT);

      digitalWrite(SOC_GPIO_PIN_GNSS_T1000_SINT, HIGH);
      pinMode(SOC_GPIO_PIN_GNSS_T1000_SINT, OUTPUT);

      digitalWrite(SOC_GPIO_PIN_GNSS_T1000_RINT, LOW);
      pinMode(SOC_GPIO_PIN_GNSS_T1000_RINT, OUTPUT);

      digitalWrite(SOC_GPIO_LED_T1000_GREEN, LED_STATE_ON);
      pinMode(SOC_GPIO_LED_T1000_GREEN, OUTPUT);

      lmic_pins.nss  = SOC_GPIO_PIN_T1000_SS;
      lmic_pins.rst  = SOC_GPIO_PIN_T1000_RST;
      lmic_pins.busy = SOC_GPIO_PIN_T1000_BUSY;
#if defined(USE_RADIOLIB)
      lmic_pins.dio[0] = SOC_GPIO_PIN_T1000_DIO9; /* LR1110 */
#endif /* USE_RADIOLIB */

      hw_info.revision = 3; /* Unknown */
      hw_info.audio    = AUDIO_PWM;
      break;

    case NRF52_HELTEC_T114:
      digitalWrite(SOC_GPIO_PIN_GNSS_T114_RST, HIGH); /* RESET - LOW */
      pinMode(SOC_GPIO_PIN_GNSS_T114_RST, OUTPUT);
      digitalWrite(SOC_GPIO_PIN_GNSS_T114_WKE, HIGH); /* SLEEP - LOW */
      pinMode(SOC_GPIO_PIN_GNSS_T114_WKE, OUTPUT);

      pinMode(SOC_GPIO_LED_T114_GREEN, OUTPUT);
      ledOn(SOC_GPIO_LED_T114_GREEN);

#if !defined(EXCLUDE_LED_RING)
      nRF52_Pixel.updateLength(2);
      nRF52_Pixel.setPin(SOC_GPIO_PIN_T114_LED);
      nRF52_Pixel.begin();
      nRF52_Pixel.show(); // Initialize all pixels to 'off'
#endif /* EXCLUDE_LED_RING */

      lmic_pins.nss  = SOC_GPIO_PIN_T114_SS;
      lmic_pins.rst  = SOC_GPIO_PIN_T114_RST;
      lmic_pins.busy = SOC_GPIO_PIN_T114_BUSY;

      hw_info.revision = 3; /* Unknown */
      break;

    case NRF52_ELECROW_TN_M1:
      /* Wake up Quectel L76K GNSS */
      digitalWrite(SOC_GPIO_PIN_GNSS_M1_RST, HIGH);
      pinMode(SOC_GPIO_PIN_GNSS_M1_RST, OUTPUT);
      digitalWrite(SOC_GPIO_PIN_GNSS_M1_WKE, HIGH);
      pinMode(SOC_GPIO_PIN_GNSS_M1_WKE, OUTPUT);

      digitalWrite(SOC_GPIO_LED_M1_RED_PWR, HIGH);
      pinMode(SOC_GPIO_LED_M1_RED_PWR,      OUTPUT);

      pinMode(SOC_GPIO_LED_M1_RED,  OUTPUT);
      pinMode(SOC_GPIO_LED_M1_BLUE, OUTPUT);

      digitalWrite(SOC_GPIO_LED_M1_RED,    LED_STATE_ON);
      digitalWrite(SOC_GPIO_LED_M1_BLUE, 1-LED_STATE_ON);

      lmic_pins.nss  = SOC_GPIO_PIN_M1_SS;
      lmic_pins.rst  = SOC_GPIO_PIN_M1_RST;
      lmic_pins.busy = SOC_GPIO_PIN_M1_BUSY;

      hw_info.revision = 3; /* Unknown */
      hw_info.audio    = AUDIO_PWM;
      break;

    case NRF52_ELECROW_TN_M3:
      digitalWrite(SOC_GPIO_PIN_GNSS_M3_EN, HIGH);
      pinMode(SOC_GPIO_PIN_GNSS_M3_EN, OUTPUT);
      digitalWrite(SOC_GPIO_PIN_GNSS_M3_RST, LOW);
      pinMode(SOC_GPIO_PIN_GNSS_M3_RST, OUTPUT);
      digitalWrite(SOC_GPIO_PIN_GNSS_M3_WKE, HIGH);
      pinMode(SOC_GPIO_PIN_GNSS_M3_WKE, OUTPUT);

      digitalWrite(SOC_GPIO_LED_M3_RGB_PWR, HIGH);
      pinMode(SOC_GPIO_LED_M3_RGB_PWR,      OUTPUT);

      pinMode(SOC_GPIO_LED_M3_RED,   OUTPUT);
      pinMode(SOC_GPIO_LED_M3_GREEN, OUTPUT);
      pinMode(SOC_GPIO_LED_M3_BLUE,  OUTPUT);

      digitalWrite(SOC_GPIO_LED_M3_RED,   1-LED_STATE_ON);
      digitalWrite(SOC_GPIO_LED_M3_GREEN, LED_STATE_ON);
      digitalWrite(SOC_GPIO_LED_M3_BLUE,  1-LED_STATE_ON);

      lmic_pins.nss  = SOC_GPIO_PIN_M3_SS;
      lmic_pins.rst  = SOC_GPIO_PIN_M3_RST;
      lmic_pins.busy = SOC_GPIO_PIN_M3_BUSY;
#if defined(USE_RADIOLIB)
      lmic_pins.dio[0] = SOC_GPIO_PIN_M3_DIO9; /* LR1110 */
#endif /* USE_RADIOLIB */

      hw_info.revision = 3; /* Unknown */
      hw_info.audio    = AUDIO_PWM;
      break;

    case NRF52_ELECROW_TN_M6:
      digitalWrite(SOC_GPIO_PIN_GNSS_M6_EN, HIGH);
      pinMode(SOC_GPIO_PIN_GNSS_M6_EN, OUTPUT);

      /* Wake up Quectel L76K GNSS */
      digitalWrite(SOC_GPIO_PIN_GNSS_M6_RST, LOW);
      pinMode(SOC_GPIO_PIN_GNSS_M6_RST, OUTPUT);
      digitalWrite(SOC_GPIO_PIN_GNSS_M6_WKE, HIGH);
      pinMode(SOC_GPIO_PIN_GNSS_M6_WKE, OUTPUT);

      pinMode(SOC_GPIO_LED_M6_RED,  OUTPUT);
      pinMode(SOC_GPIO_LED_M6_BLUE, OUTPUT);

      digitalWrite(SOC_GPIO_LED_M6_RED,    LED_STATE_ON);
      digitalWrite(SOC_GPIO_LED_M6_BLUE, 1-LED_STATE_ON);

      lmic_pins.nss  = SOC_GPIO_PIN_M6_SS;
      lmic_pins.rst  = SOC_GPIO_PIN_M6_RST;
      lmic_pins.busy = SOC_GPIO_PIN_M6_BUSY;

      hw_info.revision = 3; /* Unknown */
      break;

    case NRF52_LILYGO_TIMPULSE_PLUS:
      /* Power on u-blox MIA-M10Q GNSS */
      digitalWrite(SOC_GPIO_PIN_GNSS_TIP_PWR, LOW);
      pinMode(SOC_GPIO_PIN_GNSS_TIP_PWR, OUTPUT);

      lmic_pins.nss  = SOC_GPIO_PIN_TIP_SS;
      lmic_pins.rst  = SOC_GPIO_PIN_TIP_RST;
      lmic_pins.busy = SOC_GPIO_PIN_TIP_BUSY;

      lmic_pins.txe  = SOC_GPIO_PIN_TIP_TX_EN;
      lmic_pins.rxe  = SOC_GPIO_PIN_TIP_RX_EN;

      pinMode(SOC_GPIO_PIN_TIP_INT1, INPUT);
      pinMode(SOC_GPIO_PIN_TIP_INT2, INPUT);

      hw_info.revision = 3; /* Unknown */
      hw_info.touch    = TOUCH_TTP223;
      break;

    case NRF52_LILYGO_TECHO_CARD:
      digitalWrite(SOC_GPIO_PIN_GNSS_TEC_PWR, LOW);
      pinMode(SOC_GPIO_PIN_GNSS_TEC_PWR, OUTPUT);

      /* Wake up Quectel L76K GNSS */
      digitalWrite(SOC_GPIO_PIN_GNSS_TEC_WKE, HIGH);
      pinMode(SOC_GPIO_PIN_GNSS_TEC_WKE, OUTPUT);
      digitalWrite(SOC_GPIO_PIN_GNSS_TEC_SW, HIGH);
      pinMode(SOC_GPIO_PIN_GNSS_TEC_SW, OUTPUT);

#if !defined(EXCLUDE_LED_RING)
      nRF52_Pixel.updateLength(1);
      nRF52_Pixel.setPin(SOC_GPIO_LED_TEC_LED3);
      nRF52_Pixel.begin();
      nRF52_Pixel.setPixelColor(0, LED_COLOR_GREEN);
      nRF52_Pixel.show();
#endif /* EXCLUDE_LED_RING */

      lmic_pins.nss  = SOC_GPIO_PIN_TEC_SS;
      lmic_pins.rst  = SOC_GPIO_PIN_TEC_RST;
      lmic_pins.busy = SOC_GPIO_PIN_TEC_BUSY;

      lmic_pins.txe  = SOC_GPIO_PIN_TEC_TX_EN;
      lmic_pins.rxe  = SOC_GPIO_PIN_TEC_RX_EN;

      pinMode(SOC_GPIO_PIN_TEC_INT, INPUT);

      hw_info.revision = 3; /* Unknown */
      break;

    case NRF52_SEEED_X1:
      digitalWrite(SOC_GPIO_PIN_GNSS_X1_EN, HIGH);
      pinMode(SOC_GPIO_PIN_GNSS_X1_EN, OUTPUT);

      digitalWrite(SOC_GPIO_PIN_GNSS_X1_VRTC, HIGH);
      pinMode(SOC_GPIO_PIN_GNSS_X1_VRTC, OUTPUT);

      digitalWrite(SOC_GPIO_PIN_GNSS_X1_RST, LOW);
      pinMode(SOC_GPIO_PIN_GNSS_X1_RST, OUTPUT);

      digitalWrite(SOC_GPIO_PIN_GNSS_X1_SINT, HIGH);
      pinMode(SOC_GPIO_PIN_GNSS_X1_SINT, OUTPUT);

      digitalWrite(SOC_GPIO_PIN_GNSS_X1_RINT, LOW);
      pinMode(SOC_GPIO_PIN_GNSS_X1_RINT, OUTPUT);

      digitalWrite(SOC_GPIO_LED_X1_RED,  1-LED_STATE_ON);
      digitalWrite(SOC_GPIO_LED_X1_GREEN,  LED_STATE_ON);
      digitalWrite(SOC_GPIO_LED_X1_BLUE, 1-LED_STATE_ON);

      pinMode(SOC_GPIO_LED_X1_RED,   OUTPUT);
      pinMode(SOC_GPIO_LED_X1_GREEN, OUTPUT);
      pinMode(SOC_GPIO_LED_X1_BLUE,  OUTPUT);

      lmic_pins.nss  = SOC_GPIO_PIN_X1_SS;
      lmic_pins.rst  = SOC_GPIO_PIN_X1_RST;
      lmic_pins.busy = SOC_GPIO_PIN_X1_BUSY;
#if defined(USE_RADIOLIB)
      lmic_pins.dio[0] = SOC_GPIO_PIN_X1_DIO8; /* LR2021 */
#endif /* USE_RADIOLIB */

      hw_info.revision = 3; /* Unknown */
      hw_info.audio    = AUDIO_PWM;
      break;

    case NRF52_NORDIC_PCA10059:
    default:
      pinMode(SOC_GPIO_LED_PCA10059_STATUS, OUTPUT);
      pinMode(SOC_GPIO_LED_PCA10059_GREEN,  OUTPUT);
      pinMode(SOC_GPIO_LED_PCA10059_RED,    OUTPUT);
      pinMode(SOC_GPIO_LED_PCA10059_BLUE,   OUTPUT);

      ledOn (SOC_GPIO_LED_PCA10059_GREEN);
      ledOff(SOC_GPIO_LED_PCA10059_RED);
      ledOff(SOC_GPIO_LED_PCA10059_BLUE);
      ledOff(SOC_GPIO_LED_PCA10059_STATUS);

      hw_info.revision = 3; /* Unknown */
      break;
  }

#if !defined(ARDUINO_ARCH_MBED) && !defined(ARDUINO_ARCH_ZEPHYR)
  if (nRF52_board == NRF52_SEEED_X1) {
    i2c = new I2CBus(Wire1);

    if (nRF52_has_rtc && (i2c != nullptr)) {
//    rtc_2 = new RTC_RX8900_U(&Wire1);
//    if (rtc_2->begin())
      {
        pinMode(SOC_GPIO_PIN_X1_RTC_INT,INPUT);
        hw_info.rtc = RTC_YSN8900;
      }
    }
  } else {
    i2c = new I2CBus(Wire);

    if (nRF52_has_rtc && (i2c != nullptr)) {
      rtc = new PCF8563_Class(*i2c);

      switch (nRF52_board)
      {
        case NRF52_HELTEC_T114:
          pinMode(SOC_GPIO_PIN_T114_R_INT, INPUT);
          break;
        case NRF52_ELECROW_TN_M3:
          // pinMode(SOC_GPIO_PIN_RTC_M3_INT, INPUT);
          break;
        case NRF52_ELECROW_TN_M6:
          pinMode(SOC_GPIO_PIN_RTC_M6_INT, INPUT);
          break;
        case NRF52_ELECROW_TN_M8:
          /* TBD */
          break;
        case NRF52_LILYGO_TECHO_REV_0:
        case NRF52_LILYGO_TECHO_REV_1:
        case NRF52_LILYGO_TECHO_REV_2:
        case NRF52_LILYGO_TECHO_PLUS:
        case NRF52_ELECROW_TN_M1:
        case NRF52_NORDIC_PCA10059:
        default:
          pinMode(SOC_GPIO_PIN_R_INT, INPUT);
          break;
      }

      hw_info.rtc = RTC_PCF8563;
    }
  }
#endif /* ARDUINO_ARCH_MBED */

#if !defined(EXCLUDE_IMU)
  if (nRF52_has_imu) {
    switch (nRF52_board)
    {
      case NRF52_LILYGO_TECHO_REV_2:
      case NRF52_LILYGO_TECHO_PLUS:
        Wire.begin();

        if (imu_1.setup(MPU9250_ADDRESS)) {
          imu_1.verbose(false);
          if (imu_1.isSleeping()) {
            imu_1.sleep(false);
          }
          hw_info.imu = IMU_MPU9250;
          hw_info.mag = MAG_AK8963;
          IMU_Time_Marker = millis();
#if !defined(EXCLUDE_BHI260)
        } else if (
#if defined(USE_BHI260_RAM_FW)
                   imu_4.setFirmware(bosch_firmware_image,
                                     bosch_firmware_size,
                                     bosch_firmware_type),
#endif /* USE_BHI260_RAM_FW */
                   imu_4.begin(Wire, BHI260AP_ADDRESS_L,
                                     SOC_GPIO_PIN_SDA, SOC_GPIO_PIN_SCL)) {
          float sample_rate = 12.5;
          uint32_t report_latency_ms = 0; /* Report immediately */

          // Enable acceleration
          bhi_accel.enable(sample_rate, report_latency_ms);
          // Enable gyroscope
          // bhi_gyro.enable(sample_rate, report_latency_ms);

          hw_info.imu = IMU_BHI260AP;
          IMU_Time_Marker = millis();
#endif /* EXCLUDE_BHI260 */
        } else {
          bool ad0 = (ICM20948_ADDRESS == 0x69) ? true : false;

          for (int t=0; t<3; t++) {
            if (imu_2.begin(Wire, ad0) == ICM_20948_Stat_Ok) {
              hw_info.imu = IMU_ICM20948;
              hw_info.mag = MAG_AK09916;
              IMU_Time_Marker = millis();

              break;
            }
            delay(IMU_UPDATE_INTERVAL);
          }
        }
        break;

      case NRF52_LILYGO_TECHO_CARD:
        Wire.begin();
        {
          bool ad0 = (ICM20948_ADDRESS == 0x69) ? true : false;

          for (int t=0; t<3; t++) {
            if (imu_2.begin(Wire, ad0) == ICM_20948_Stat_Ok) {
              hw_info.imu = IMU_ICM20948;
              hw_info.mag = MAG_AK09916;
              IMU_Time_Marker = millis();

              break;
            }
          }
        }
        break;

#if !defined(EXCLUDE_WIP)
      case NRF52_HELTEC_T1:
        /* TBD */
        break;
#endif /* EXCLUDE_WIP */

      case NRF52_SEEED_T1000E:
        Wire.begin();

        if (imu_3.begin()) {
          imu_3.softwareReset();
          delay(5);
          imu_3.setRange(SFE_QMA6100P_RANGE4G);
          imu_3.enableAccel(true);
          imu_3.calibrateOffsets();
          // imu_3.setOffset();

          hw_info.imu     = ACC_QMA6100P;
          IMU_Time_Marker = millis();
        }
        break;

      case NRF52_ELECROW_TN_M3:
      case NRF52_ELECROW_TN_M8:
        Wire.begin();
        imu_5 = Adafruit_LIS3DH(&Wire);
        if (imu_5.begin(SC7A20H_ADDRESS_H, 0x11)) {
          imu_5.setRange(LIS3DH_RANGE_4_G);

          hw_info.imu     = ACC_SC7A20H;
          IMU_Time_Marker = millis();
        }
        break;

      case NRF52_LILYGO_TIMPULSE_PLUS:
        Wire1.begin();
        {
          bool ad0 = (ICM20948_ADDRESS_ALT == 0x69) ? true : false;

          for (int t=0; t<3; t++) {
            if (imu_2.begin(Wire1, ad0) == ICM_20948_Stat_Ok) {
              hw_info.imu = IMU_ICM20948;
              hw_info.mag = MAG_AK09916;
              IMU_Time_Marker = millis();

              break;
            }
            delay(IMU_UPDATE_INTERVAL);
          }
        }
        break;

      default:
        break;
    }
  }
#endif /* EXCLUDE_IMU */

#if !defined(ARDUINO_ARCH_MBED) && !defined(ARDUINO_ARCH_ZEPHYR)
  if (nRF52_has_spiflash) {
    spiflash_id = SPIFlash->getJEDECID();

    //mx25_status_config[0] = SPIFlash->readStatus();
    //HWFlashTransport.readCommand(SFLASH_CMD_READ_CONFIG,   mx25_status_config + 1, 2);
    //mx25_status_config[2] |= 0x2;       /* High performance mode */
    //SPIFlash->writeEnable();
    //HWFlashTransport.writeCommand(SFLASH_CMD_WRITE_STATUS, mx25_status_config,     3);
    //SPIFlash->writeDisable();
    //SPIFlash->waitUntilReady();

    //uint32_t const wr_speed = min(80 * 1000000U, (uint32_t)F_CPU);
    //uint32_t rd_speed = wr_speed;
    //HWFlashTransport.setClockSpeed(wr_speed, rd_speed);

    // Set disk vendor id, product id and revision with string up to 8, 16, 4 characters respectively
    usb_msc.setID(nRF5x_Device_Manufacturer, "External Flash", "1.0");

    // Set callback
    usb_msc.setReadWriteCallback(nRF52_msc_read_cb,
                                 nRF52_msc_write_cb,
                                 nRF52_msc_flush_cb);

    // Set disk size, block size should be 512 regardless of spi flash page size
    usb_msc.setCapacity(SPIFlash->size()/512, 512);

    // MSC is ready for read/write
    usb_msc.setUnitReady(true);

    usb_msc.begin();

    FATFS_is_mounted = fatfs.begin(SPIFlash);
  }
#endif /* ARDUINO_ARCH_MBED */

#if defined(USE_USB_MIDI)
  // Initialize MIDI with no any input channels
  // This will also call usb_midi's begin()
  MIDI_USB.begin(MIDI_CHANNEL_OFF);
#endif /* USE_USB_MIDI */

  Serial.begin(SERIAL_OUT_BR, SERIAL_OUT_BITS);

#if defined(USE_TINYUSB) && defined(USBCON)
  for (int i=0; i < 20; i++) {if (Serial) break; else delay(100);}
#endif

#if !defined(EXCLUDE_WIFI)
  switch (nRF52_board)
  {
    case NRF52_LILYGO_TECHO_REV_0:
    case NRF52_LILYGO_TECHO_REV_1:
    case NRF52_LILYGO_TECHO_REV_2:
    case NRF52_LILYGO_TECHO_PLUS:
    case NRF52_NORDIC_PCA10059:
    default:
#if defined(_WIFI_ESP_AT_H_)
      Serial1.begin(115200);
      WiFi.init(&Serial1);
#endif /* _WIFI_ESP_AT_H_ */

#if defined(WiFiNINA_h)
      WiFi.setPins(SPIWIFI_SS, SPIWIFI_ACK, ESP32_RESETN, ESP32_GPIO0, &SPIWIFI);
#endif /* WiFiNINA_h */
      break;
  }
#endif /* EXCLUDE_WIFI */

#if defined(ENABLE_NFC)
  if (nRF52_board == NRF52_LILYGO_TECHO_REV_0 ||
      nRF52_board == NRF52_LILYGO_TECHO_REV_1 ||
      nRF52_board == NRF52_LILYGO_TECHO_REV_2) {
    if ((NRF_UICR->NFCPINS & UICR_NFCPINS_PROTECT_Msk) != (UICR_NFCPINS_PROTECT_NFC << UICR_NFCPINS_PROTECT_Pos)) {
      Serial.println("*** NFC pins are disabled ***");
      // nfcpins_enable();
    }
  }
#endif /* ENABLE_NFC */

  if (nRF52_board == NRF52_LILYGO_TECHO_PLUS) {
#if SENSORLIB_VERSION == SENSORLIB_VERSION_VAL(0, 3, 1)
    nRF52_has_vibra = vibra.begin(Wire);
#endif /* (0, 3, 1) */
#if SENSORLIB_VERSION >= SENSORLIB_VERSION_VAL(0, 4, 1)
    nRF52_has_vibra = vibra.begin(Wire, DRV2605_SLAVE_ADDRESS);
#endif /* (0, 4, 1) */

    if (nRF52_has_vibra) {
      vibra.selectLibrary(1);
#if SENSORLIB_VERSION == SENSORLIB_VERSION_VAL(0, 3, 1)
      vibra.setMode(SensorDRV2605::MODE_INTTRIG);
#endif /* (0, 3, 1) */
#if SENSORLIB_VERSION >= SENSORLIB_VERSION_VAL(0, 4, 1)
      vibra.setMode(HapticMode::INTERNAL_TRIGGER);
#endif /* (0, 4, 1) */

      digitalWrite(SOC_GPIO_PIN_MOTOR_EN, HIGH);
      pinMode(SOC_GPIO_PIN_MOTOR_EN, OUTPUT);
      hw_info.haptic = HAPTIC_DRV2605;
    }
    hw_info.audio = AUDIO_PWM;
  }

  if (nRF52_board == NRF52_SEEED_X1) {
#if SENSORLIB_VERSION == SENSORLIB_VERSION_VAL(0, 3, 1)
    nRF52_has_vibra = vibra.begin(Wire);
#endif /* (0, 3, 1) */
#if SENSORLIB_VERSION >= SENSORLIB_VERSION_VAL(0, 4, 1)
    nRF52_has_vibra = vibra.begin(Wire, DRV2605_SLAVE_ADDRESS);
#endif /* (0, 4, 1) */

    if (nRF52_has_vibra) {
      vibra.selectLibrary(1);
#if SENSORLIB_VERSION == SENSORLIB_VERSION_VAL(0, 3, 1)
      vibra.setMode(SensorDRV2605::MODE_INTTRIG);
#endif /* (0, 3, 1) */
#if SENSORLIB_VERSION >= SENSORLIB_VERSION_VAL(0, 4, 1)
      vibra.setMode(HapticMode::INTERNAL_TRIGGER);
#endif /* (0, 4, 1) */

      hw_info.haptic = HAPTIC_DRV2605;
    }

    pinMode(SOC_GPIO_PIN_X1_BUZZER, INPUT_PULLDOWN);

    Wire.beginTransmission(BMM350_ADDRESS);
    if (Wire.endTransmission() == 0) {
      hw_info.mag = MAG_BMM350;
    }
  }

  if (nRF52_board == NRF52_LILYGO_TIMPULSE_PLUS) {
#if !defined(EXCLUDE_IMU)
    if (nRF52_has_imu == false)
#endif
    {
      Wire1.begin();
    }
    if (initSGM41562(Wire1)) {
      hw_info.pmu = BMU_SGM41562;
    }
  }
}

static void nRF52_post_init()
{
  uint32_t variant = NRF_FICR->INFO.VARIANT;
  char bc_high     = (variant >> 8) & 0xFF;
  char bc_low      = (variant     ) & 0xFF;
  const char *rev  = "UNKNOWN";

  switch (bc_high)
  {
    case 'A': rev = "Engineering A"; break;
    case 'B': rev = "Engineering B"; break;
    case 'C':
      if (bc_low == 'A')
              rev = "Engineering C";
      else
              rev = "1";
      break;
    case 'D':
      if (bc_low == 'A')
              rev = "Engineering D";
      else
              rev = "2";
      break;
    case 'F': rev = "3";             break;
    default:                         break;
  }

#if 0
  Serial.println();
  Serial.print  (F("MCU Revision: "));
  Serial.println(rev);
#endif

  if (nRF52_board == NRF52_LILYGO_TECHO_REV_0 ||
      nRF52_board == NRF52_LILYGO_TECHO_REV_1 ||
      nRF52_board == NRF52_LILYGO_TECHO_REV_2 ||
      nRF52_board == NRF52_LILYGO_TECHO_PLUS  ||
      nRF52_board == NRF52_LILYGO_TECHO_CARD  ||
      nRF52_board == NRF52_ELECROW_TN_M1      ||
      nRF52_board == NRF52_LILYGO_TIMPULSE_PLUS) {

#if 0
    char strbuf[32];
    Serial.println();
    Serial.print  (F("64-bit Device ID: "));
    snprintf(strbuf, sizeof(strbuf),"0x%08x%08x", DEVICE_ID_HIGH, DEVICE_ID_LOW);
    Serial.println(strbuf);
#endif

#if 0
    Serial.println();
    Serial.print  (F("SPI FLASH JEDEC ID: "));
    Serial.print  (spiflash_id, HEX);           Serial.print(" ");
    Serial.print  (F("STATUS/CONFIG: "));
    Serial.print  (mx25_status_config[0], HEX); Serial.print(" ");
    Serial.print  (mx25_status_config[1], HEX); Serial.print(" ");
    Serial.print  (mx25_status_config[2], HEX); Serial.println();
#endif

    Serial.println();
    Serial.print  (nRF52_board == NRF52_ELECROW_TN_M1  ? F("Elecrow ") : F("LilyGO T-"));
    Serial.print  (nRF52_board == NRF52_ELECROW_TN_M1  ? F("TN-M1") :
                   nRF52_board == NRF52_LILYGO_TIMPULSE_PLUS ? F("Impulse Plus") :
                   F("Echo"));
    Serial.print  (F(" ("));
    Serial.print  (nRF52_board == NRF52_LILYGO_TECHO_CARD ? "Card" :
                   hw_info.revision > 2 ?
                   Hardware_Rev[3] : Hardware_Rev[hw_info.revision]);
    Serial.println(F(") Power-on Self Test"));
    Serial.println();
    Serial.flush();

    Serial.println(F("Built-in components:"));

    Serial.print(F("RADIO   : "));
    Serial.println(hw_info.rf      == RF_IC_SX1262 ||
                   hw_info.rf      == RF_IC_SX1276 ||
                   hw_info.rf      == RF_IC_LR1110 ||
                   hw_info.rf      == RF_IC_LR1121     ? F("PASS") : F("FAIL"));
    Serial.flush();
    Serial.print(F("GNSS    : "));
    if (nRF52_board == NRF52_LILYGO_TIMPULSE_PLUS) {
      Serial.println(hw_info.gnss  == GNSS_MODULE_U10  ? F("PASS") : F("FAIL"));
    } else if (nRF52_board == NRF52_LILYGO_TECHO_REV_0 ||
               nRF52_board == NRF52_LILYGO_TECHO_REV_1) {
      Serial.println(hw_info.gnss  == GNSS_MODULE_GOKE ? F("PASS") : F("FAIL"));
    } else {
      Serial.println(hw_info.gnss  == GNSS_MODULE_AT65 ? F("PASS") : F("FAIL"));
    }
    Serial.flush();
    Serial.print(F("DISPLAY : "));
    Serial.println(hw_info.display == DISPLAY_EPD_1_54  ||
                   hw_info.display == DISPLAY_OLED_0_49 ||
                   hw_info.display == DISPLAY_EPD_3_71 ? F("PASS") : F("FAIL"));
    Serial.flush();
    if (nRF52_board == NRF52_LILYGO_TIMPULSE_PLUS ||
        nRF52_board == NRF52_LILYGO_TECHO_CARD) {
      Serial.print(F("IMU     : "));
      Serial.println(hw_info.imu   == IMU_ICM20948     ? F("PASS") : F("FAIL"));
     if (nRF52_board == NRF52_LILYGO_TIMPULSE_PLUS) {
      Serial.print(F("BMU     : "));
      Serial.println(hw_info.pmu   == BMU_SGM41562     ? F("PASS") : F("FAIL"));
      Serial.flush();
     }
    } else {
      Serial.print(F("RTC     : "));
      Serial.println(hw_info.rtc   == RTC_PCF8563      ? F("PASS") : F("FAIL"));
      Serial.flush();
    }

    Serial.print(F("FLASH   : "));
    Serial.println(hw_info.storage == STORAGE_FLASH_AND_CARD ||
                   hw_info.storage == STORAGE_FLASH    ? F("PASS") : F("FAIL"));
    Serial.flush();

    if (nRF52_board == NRF52_LILYGO_TECHO_REV_1 ||
        nRF52_board == NRF52_LILYGO_TECHO_REV_2 ||
        nRF52_board == NRF52_LILYGO_TECHO_PLUS) {
      Serial.print(F("BMx280  : "));
      Serial.println(hw_info.baro == BARO_MODULE_BMP280 ? F("PASS") : F("N/A"));
      Serial.flush();
#if !defined(EXCLUDE_IMU)
      Serial.println();
      Serial.println(F("External components:"));
      Serial.print(F("IMU     : "));
      Serial.println(hw_info.imu  == IMU_MPU9250  ||
                     hw_info.imu  == IMU_ICM20948 ||
                     hw_info.imu  == IMU_BHI260AP       ? F("PASS") : F("N/A"));
      Serial.flush();
#endif /* EXCLUDE_IMU */
    }

    Serial.println();
    Serial.println(F("Power-on Self Test is complete."));
    Serial.println();
    Serial.flush();

#if 0
    if (nRF52_board == NRF52_LILYGO_TECHO_CARD) {
#if defined(USE_EXT_I2S_DAC)
      char filename[MAX_FILENAME_LEN];
      strcpy(filename, WAV_FILE_PREFIX);
      strcat(filename, "POST");
      strcat(filename, WAV_FILE_SUFFIX);
      if (FATFS_is_mounted && fatfs.exists(filename)) {
        play_file(filename);
      }
#endif /* USE_EXT_I2S_DAC */
    }
#endif

#if defined(ENABLE_NFC) && defined(EXCLUDE_BLUETOOTH)
    if ((NRF_UICR->NFCPINS & UICR_NFCPINS_PROTECT_Msk) == (UICR_NFCPINS_PROTECT_NFC << UICR_NFCPINS_PROTECT_Pos)) {
      String NFC_name = SOFTRF_IDENT;
      char id_06x[8];
      snprintf(id_06x, sizeof(id_06x),"%06x", SoC->getChipId() & 0x00FFFFFFU);
      NFC_name += "-";
      NFC_name += String(id_06x);

      NFC.setTXTmessage((NFC_name+"-NFC").c_str(), "en");
      NFC.start();
      NFC.registerCallback(nfc_func);
    }
#endif /* ENABLE_NFC */

#if 0
    if (nRF52_board == NRF52_LILYGO_TECHO_PLUS) {
      BoschSensorInfo info = imu_4.getSensorInfo();
      info.printInfo(Serial);
      Serial.flush();
    }
#endif
  } else if (nRF52_board == NRF52_HELTEC_T114) {
    Serial.println();
    Serial.println(F("Heltec T114 Power-on Self Test"));
    Serial.println();
    Serial.flush();

    Serial.println(F("Built-in components:"));

    Serial.print(F("RADIO   : "));
    Serial.println(hw_info.rf      == RF_IC_SX1262     ? F("PASS") : F("FAIL"));
    Serial.flush();

    Serial.println();
    Serial.println(F("External components:"));

    Serial.print(F("DISPLAY : "));
    Serial.println(hw_info.display == DISPLAY_TFT_TTGO_135
                                                       ? F("PASS") : F("N/A"));
    Serial.flush();
    Serial.print(F("GNSS    : "));
    Serial.println(hw_info.gnss    != GNSS_MODULE_NONE ? F("PASS") : F("N/A"));
    Serial.flush();
    Serial.print(F("BARO    : "));
    Serial.println(hw_info.baro    != BARO_MODULE_NONE ? F("PASS") : F("N/A"));
    Serial.flush();

    Serial.println();
    Serial.println(F("Power-on Self Test is complete."));
    Serial.println();
    Serial.flush();

  } else if (nRF52_board == NRF52_SEEED_T1000E ||
             nRF52_board == NRF52_SEEED_X1) {
#if 0
    Serial.println();
    Serial.print  (F("SPI FLASH JEDEC ID: "));
    Serial.print  (spiflash_id, HEX);           Serial.print(" ");
#endif

    Serial.println();
    Serial.print  (F("Seeed "));
    Serial.print  (nRF52_board == NRF52_SEEED_X1 ? F("X1") : F("T1000-E"));
    Serial.println(F(" Power-on Self Test"));
    Serial.println();
    Serial.flush();

    Serial.println(F("Built-in components:"));

    Serial.print(F("RADIO   : "));
    Serial.println(hw_info.rf    == RF_IC_LR1110 ||
                   hw_info.rf    == RF_IC_LR2021     ? F("PASS") : F("FAIL"));
    Serial.flush();
    Serial.print(F("GNSS    : "));
    Serial.println(hw_info.gnss  == GNSS_MODULE_AG33 ? F("PASS") : F("FAIL"));
    Serial.flush();
    Serial.print(F("FLASH   : "));
    Serial.println(hw_info.storage == STORAGE_FLASH  ? F("PASS") : F("FAIL"));
    Serial.flush();

    if (nRF52_board == NRF52_SEEED_T1000E) {
#if !defined(EXCLUDE_IMU)
      Serial.print(F("IMU     : "));
      Serial.println(hw_info.imu   == ACC_QMA6100P   ? F("PASS") : F("FAIL"));
      Serial.flush();
#endif /* EXCLUDE_IMU */

#if !defined(ARDUINO_ARCH_MBED) && !defined(ARDUINO_ARCH_ZEPHYR)
      analogReference(AR_INTERNAL_3_0);
      analogReadResolution(10);
      delay(1);

      Serial.print(F("TEMP    : "));
      Serial.print((float) t1000e_ntc_sample() / 10.0f);
      Serial.println(F(" Celsius"));
      Serial.print(F("LIGHT   : "));
      Serial.print(t1000e_lux_sample());
      Serial.println(F(" %"));
      Serial.print(F("BATTERY : "));
      Serial.print(t1000e_bat_sample());
      Serial.println(F(" %"));
      Serial.flush();
#endif /* !MBED && !ZEPHYR */
    } else {
      Serial.print(F("RTC     : "));
      Serial.println(hw_info.rtc    == RTC_YSN8900       ? F("PASS") : F("FAIL"));
      Serial.print(F("BARO    : "));
      Serial.println(hw_info.baro   == BARO_MODULE_SPA06 ? F("PASS") : F("FAIL"));
      Serial.print(F("HAPTIC  : "));
      Serial.println(hw_info.haptic == HAPTIC_DRV2605    ? F("PASS") : F("FAIL"));
      Serial.flush();
    }

    Serial.println();
    Serial.println(F("Power-on Self Test is complete."));
    Serial.println();
    Serial.flush();

  } else if (nRF52_board == NRF52_ELECROW_TN_M3) {

    Serial.println();
    Serial.println(F("Elecrow ThinkNode-M3 Power-on Self Test"));
    Serial.println();
    Serial.flush();

    Serial.println(F("Built-in components:"));

    Serial.print(F("RADIO   : "));
    Serial.println(hw_info.rf    == RF_IC_LR1110     ? F("PASS") : F("FAIL"));
    Serial.flush();
    Serial.print(F("GNSS    : "));
    Serial.println(hw_info.gnss  == GNSS_MODULE_AT65 ? F("PASS") : F("FAIL"));
    Serial.flush();
    Serial.print(F("RTC     : "));
    Serial.println(hw_info.rtc   == RTC_PCF8563      ? F("PASS") : F("FAIL"));
    Serial.flush();

#if !defined(EXCLUDE_IMU)
    Serial.print(F("IMU     : "));
    Serial.println(hw_info.imu   == ACC_SC7A20H      ? F("PASS") : F("FAIL"));
    Serial.flush();
#endif /* EXCLUDE_IMU */

    aht20.begin();
    float humidity, temperature;

    if (aht20.getSensor(&humidity, &temperature)) {
      Serial.print(F("TEMP    : "));
      Serial.print(temperature);
      Serial.println(F(" degrees Celsius"));
      Serial.print(F("HUMID   : "));
      Serial.print(humidity*100);
      Serial.println(F(" % rH"));
      Serial.flush();
    }

    Serial.println();
    Serial.println(F("Power-on Self Test is complete."));
    Serial.println();
    Serial.flush();

  } else if (nRF52_board == NRF52_ELECROW_TN_M6) {
#if 0
    Serial.println();
    Serial.print  (F("SPI FLASH JEDEC ID: "));
    Serial.print  (spiflash_id, HEX);           Serial.print(" ");
#endif

    Serial.println();
    Serial.println(F("Elecrow ThinkNode-M6 Power-on Self Test"));
    Serial.println();
    Serial.flush();

    Serial.println(F("Built-in components:"));

    Serial.print(F("RADIO   : "));
    Serial.println(hw_info.rf    == RF_IC_SX1262     ? F("PASS") : F("FAIL"));
    Serial.flush();
    Serial.print(F("GNSS    : "));
    Serial.println(hw_info.gnss  == GNSS_MODULE_AT65 ? F("PASS") : F("FAIL"));
    Serial.flush();
    Serial.print(F("RTC     : "));
    Serial.println(hw_info.rtc   == RTC_PCF8563      ? F("PASS") : F("FAIL"));
    Serial.flush();
    Serial.print(F("FLASH   : "));
    Serial.println(hw_info.storage == STORAGE_FLASH  ? F("PASS") : F("N/A"));
    Serial.flush();

    Serial.println();
    Serial.println(F("External components:"));

#if defined(USE_OLED)
    Serial.print(F("DISPLAY : "));
    Serial.println(hw_info.display != DISPLAY_NONE   ? F("PASS") : F("N/A"));
    Serial.flush();
#endif /* USE_OLED */

    Serial.print(F("BARO    : "));
    Serial.println(hw_info.baro  != BARO_MODULE_NONE ? F("PASS") : F("N/A"));
    Serial.flush();

    Serial.println();
    Serial.println(F("Power-on Self Test is complete."));
    Serial.println();
    Serial.flush();

  } else if (nRF52_board == NRF52_NORDIC_PCA10059) {
    Serial.println();
    Serial.println(F("Board: Nordic PCA10059 USB Dongle"));
    Serial.println();
    Serial.flush();
  }

  Serial.println(F("Data output device(s):"));

  Serial.print(F("NMEA   - "));
  switch (settings->nmea_out)
  {
    case NMEA_UART       :  Serial.println(F("UART"));          break;
    case NMEA_USB        :  Serial.println(F("USB CDC"));       break;
    case NMEA_BLUETOOTH  :  Serial.println(F("Bluetooth LE"));  break;
    case NMEA_OFF        :
    default              :  Serial.println(F("NULL"));          break;
  }

  Serial.print(F("GDL90  - "));
  switch (settings->gdl90)
  {
    case GDL90_UART      :  Serial.println(F("UART"));          break;
    case GDL90_USB       :  Serial.println(F("USB CDC"));       break;
    case GDL90_BLUETOOTH :  Serial.println(F("Bluetooth LE"));  break;
    case GDL90_OFF       :
    default              :  Serial.println(F("NULL"));          break;
  }

  Serial.print(F("D1090  - "));
  switch (settings->d1090)
  {
    case D1090_UART      :  Serial.println(F("UART"));          break;
    case D1090_USB       :  Serial.println(F("USB CDC"));       break;
    case D1090_BLUETOOTH :  Serial.println(F("Bluetooth LE"));  break;
    case D1090_OFF       :
    default              :  Serial.println(F("NULL"));          break;
  }

  Serial.println();
  Serial.flush();

#if defined(USE_EPAPER)
  if (nRF52_board == NRF52_LILYGO_TECHO_REV_0 ||
      nRF52_board == NRF52_LILYGO_TECHO_REV_1 ||
      nRF52_board == NRF52_LILYGO_TECHO_REV_2 ||
      nRF52_board == NRF52_LILYGO_TECHO_PLUS  ||
      nRF52_board == NRF52_ELECROW_TN_M1      ||
      nRF52_board == NRF52_ELECROW_TN_M8) {
    /* EPD back light on */
    uint8_t bl_state = digitalRead(SOC_GPIO_PIN_EPD_BLGT);
    if (bl_state == LOW) digitalWrite(SOC_GPIO_PIN_EPD_BLGT, HIGH);

    EPD_info1();

    /* EPD back light off */
    if (bl_state == LOW) digitalWrite(SOC_GPIO_PIN_EPD_BLGT, LOW);

    char key[8];
    char out[64];
    uint8_t tokens[3] = { 0 };
    cdbResult rt;
    int c, i = 0, token_cnt = 0;

    int acfts;
    char *reg, *mam, *cn;
    reg = mam = cn = NULL;

    if (ADB_is_open) {
      acfts = ucdb.recordsNumber();

      snprintf(key, sizeof(key),"%06X", ThisAircraft.addr);

      rt = ucdb.findKey(key, strlen(key));

      switch (rt) {
        case KEY_FOUND:
          while ((c = ucdb.readValue()) != -1 && i < (sizeof(out) - 1)) {
            if (c == '|') {
              if (token_cnt < (sizeof(tokens) - 1)) {
                token_cnt++;
                tokens[token_cnt] = i+1;
              }
              c = 0;
            }
            out[i++] = (char) c;
          }
          out[i] = 0;

          reg = out + tokens[1];
          mam = out + tokens[0];
          cn  = out + tokens[2];

          break;

        case KEY_NOT_FOUND:
        default:
          break;
      }

      reg = (reg != NULL) && strlen(reg) ? reg : (char *) "REG: N/A";
      mam = (mam != NULL) && strlen(mam) ? mam : (char *) "M&M: N/A";
      cn  = (cn  != NULL) && strlen(cn)  ? cn  : (char *) "N/A";

    } else {
      acfts = -1;
    }

    EPD_info2(acfts, reg, mam, cn);
  }
#endif /* USE_EPAPER */

#if defined(USE_OLED)
  if (hw_info.display == DISPLAY_OLED_1_3  ||
#if !defined(EXCLUDE_OLED_049)
      hw_info.display == DISPLAY_OLED_0_49 ||
#endif /* EXCLUDE_OLED_049 */
      hw_info.display == DISPLAY_OLED_TTGO) {
    OLED_info1();
  }
#endif /* USE_OLED */
}

static void nRF52_loop()
{
#if !defined(ARDUINO_ARCH_MBED) && !defined(ARDUINO_ARCH_ZEPHYR)
  // Reload the watchdog
  if (nrf_wdt_started(NRF_WDT)) {
    Watchdog.reset();
  }

  if (!RTC_sync) {
    if (rtc &&
        gnss.date.isValid()                         &&
        gnss.time.isValid()                         &&
        gnss.date.year() >= fw_build_date_time.year &&
        gnss.date.year() <  fw_build_date_time.year + 15 ) {
      rtc->setDateTime(gnss.date.year(),   gnss.date.month(),
                       gnss.date.day(),    gnss.time.hour(),
                       gnss.time.minute(), gnss.time.second());
      RTC_sync = true;
    }
  }
#endif /* ARDUINO_ARCH_MBED */

#if defined(USE_WEBUSB_SETTINGS) && !defined(USE_WEBUSB_SERIAL)

  if (USBDevice.mounted() && usb_web.connected() && usb_web.available()) {

    JsonObject &root = nRF52_jsonBuffer.parseObject(usb_web);

    if (root.success()) {
      JsonVariant msg_class = root["class"];

      if (msg_class.success()) {
        const char *msg_class_s = msg_class.as<char*>();

        if (!strcmp(msg_class_s,"SOFTRF")) {
          parseSettings  (root);
          parseUISettings(root);

          SoC->WDT_fini();
          if (SoC->Bluetooth_ops) { SoC->Bluetooth_ops->fini(); }
          Serial.println();
          Serial.println(F("Restart is in progress. Please, wait..."));
          Serial.println();
          Serial.flush();
#if !defined(EXCLUDE_EEPROM)
          EEPROM_store();
#endif /* EXCLUDE_EEPROM */
          RF_Shutdown();
          SoC->reset();
        }
      }
    }
  }

#endif /* USE_WEBUSB_SETTINGS */

#if !defined(EXCLUDE_IMU)
  if ((millis() - IMU_Time_Marker) > IMU_UPDATE_INTERVAL) {
    float a_x = 0;
    float a_y = 0;
    float a_z = 0;

    switch (hw_info.imu)
    {
      case IMU_MPU9250:
        if (imu_1.update()) {
          a_x = imu_1.getAccX();
          a_y = imu_1.getAccY();
          a_z = imu_1.getAccZ();
        }
        break;

      case IMU_ICM20948:
        if (imu_2.dataReady()) {
          imu_2.getAGMT();

          // milli g's
          a_x = imu_2.accX() / 1000;
          a_y = imu_2.accY() / 1000;
          a_z = imu_2.accZ() / 1000;
        }
        break;

      case ACC_QMA6100P:
        {
          outputData data;

          imu_3.getAccelData(&data);
          imu_3.offsetValues(data.xData, data.yData, data.zData);

          a_x = data.xData;
          a_y = data.yData;
          a_z = data.zData;
        }
        break;

#if 0 /* TODO */ // !defined(EXCLUDE_BHI260)
      case IMU_BHI260AP:
        imu_4.update();

        if (bhi_accel.hasUpdated()) {
          a_x = bhi_accel.getX(); /* TBD */
          a_y = bhi_accel.getY(); /* TBD */
          a_z = bhi_accel.getZ(); /* TBD */
        }
        break;
#endif /* EXCLUDE_BHI260 */

      case ACC_SC7A20H:
        imu_5.read();
        a_x = imu_5.x_g;
        a_y = imu_5.y_g;
        a_z = imu_5.z_g;
        break;

      default:
        break;
    }

#if 0
    Serial.print("{ACCEL: ");
    Serial.print(a_x);
    Serial.print(",");
    Serial.print(a_y);
    Serial.print(",");
    Serial.print(a_z);
    Serial.println("}");
#endif

    IMU_g = sqrtf(a_x*a_x + a_y*a_y + a_z*a_z);

#if 0
    Serial.print("G load: ");
    Serial.print(IMU_g);
    Serial.println();
#endif

#if defined(USE_OLED)
    IMU_g_x10 = (int32_t) (IMU_g * 10);
#endif /* USE_OLED */

    IMU_Time_Marker = millis();
  }
#endif /* EXCLUDE_IMU */

  if ((nRF52_board     == NRF52_SEEED_T1000E      ||
       nRF52_board     == NRF52_SEEED_X1          ||
       nRF52_board     == NRF52_ELECROW_TN_M1     ||
       nRF52_board     == NRF52_ELECROW_TN_M3     ||
       nRF52_board     == NRF52_ELECROW_TN_M8     ||
       nRF52_board     == NRF52_LILYGO_TECHO_PLUS ||
       nRF52_board     == NRF52_LILYGO_TECHO_CARD ||
       nRF52_board     == NRF52_SEEED_WIO_L1)     &&
      settings->volume != BUZZER_OFF              &&
      settings->mode   == SOFTRF_MODE_NORMAL      &&
      nRF52_has_vff    == false                   &&
      isValidFix()     == true) {
    uint8_t v = settings->volume;

    SoC->Sound_tone(1046, v); delay(200); SoC->Sound_tone(0, v);
    SoC->Sound_tone(1175, v); delay(200); SoC->Sound_tone(0, v);
    SoC->Sound_tone(1318, v); delay(200); SoC->Sound_tone(0, v);
    SoC->Sound_tone(1397, v); delay(400); SoC->Sound_tone(0, v);
                              delay(200);
    SoC->Sound_tone(1046, v); delay(200); SoC->Sound_tone(0, v);
    SoC->Sound_tone(1397, v); delay(400); SoC->Sound_tone(0, v);

    nRF52_has_vff = true;
  }
}

static void nRF52_fini(int reason)
{
#if !defined(ARDUINO_ARCH_MBED) && !defined(ARDUINO_ARCH_ZEPHYR)
  if (nRF52_has_spiflash) {
    usb_msc.setUnitReady(false);
//  usb_msc.end(); /* N/A */
  }

  if (SPIFlash != NULL) {
    FlashTrans->runCommand(0xB9); /* DP */
    SPIFlash->end();
  }
#endif /* ARDUINO_ARCH_MBED */

#if !defined(EXCLUDE_IMU)
  switch (hw_info.imu)
  {
    case IMU_MPU9250:
      imu_1.sleep(true);
      break;
    case IMU_ICM20948:
      imu_2.sleep(true);
      break;
    case ACC_QMA6100P:
      imu_3.enableAccel(false);
      break;
#if 0 /* TODO */ // !defined(EXCLUDE_BHI260)
    case IMU_BHI260AP:
      /* TBD */
      // imu_4.deinit();
      break;
#endif /* EXCLUDE_BHI260 */
    case ACC_SC7A20H:
      /* TBD */
      break;
    default:
      break;
  }
#endif /* EXCLUDE_IMU */

  switch (nRF52_board)
  {
    case NRF52_LILYGO_TECHO_REV_0:
#if 0
      /* Air530 GNSS ultra-low power tracking mode */
      digitalWrite(SOC_GPIO_PIN_GNSS_WKE, LOW);
      pinMode(SOC_GPIO_PIN_GNSS_WKE, OUTPUT);

    // Serial_GNSS_Out.write("$PGKC105,4*33\r\n");
#else
      pinMode(SOC_GPIO_PIN_GNSS_WKE, INPUT);

      // Serial_GNSS_Out.write("$PGKC051,0*37\r\n");
      // Serial_GNSS_Out.write("$PGKC051,1*36\r\n");
#endif
      // Serial_GNSS_Out.flush(); delay(250);

      ledOff(SOC_GPIO_LED_TECHO_REV_0_GREEN);
      ledOff(SOC_GPIO_LED_TECHO_REV_0_RED);
      ledOff(SOC_GPIO_LED_TECHO_REV_0_BLUE);

      pinMode(SOC_GPIO_LED_TECHO_REV_0_GREEN, INPUT);
      pinMode(SOC_GPIO_LED_TECHO_REV_0_RED,   INPUT);
      pinMode(SOC_GPIO_LED_TECHO_REV_0_BLUE,  INPUT);

      pinMode(SOC_GPIO_PIN_IO_PWR, INPUT);
      pinMode(SOC_GPIO_PIN_SFL_SS, INPUT);
      break;

    case NRF52_LILYGO_TECHO_REV_1:
#if 0
      /* Air530 GNSS ultra-low power tracking mode */
      digitalWrite(SOC_GPIO_PIN_GNSS_WKE, LOW);
      pinMode(SOC_GPIO_PIN_GNSS_WKE, OUTPUT);

    // Serial_GNSS_Out.write("$PGKC105,4*33\r\n");
#else
      pinMode(SOC_GPIO_PIN_GNSS_WKE, INPUT);

      // Serial_GNSS_Out.write("$PGKC051,0*37\r\n");
      // Serial_GNSS_Out.write("$PGKC051,1*36\r\n");
#endif
      // Serial_GNSS_Out.flush(); delay(250);

      ledOff(SOC_GPIO_LED_TECHO_REV_1_GREEN);
      ledOff(SOC_GPIO_LED_TECHO_REV_1_RED);
      ledOff(SOC_GPIO_LED_TECHO_REV_1_BLUE);

      pinMode(SOC_GPIO_LED_TECHO_REV_1_GREEN, INPUT);
      pinMode(SOC_GPIO_LED_TECHO_REV_1_RED,   INPUT);
      pinMode(SOC_GPIO_LED_TECHO_REV_1_BLUE,  INPUT);

      pinMode(SOC_GPIO_PIN_SFL_WP,    INPUT);
      pinMode(SOC_GPIO_PIN_SFL_HOLD,  INPUT);
      pinMode(SOC_GPIO_PIN_SFL_SS,    INPUT);
      pinMode(SOC_GPIO_PIN_IO_PWR,    INPUT);
      /* Cut 3.3V power off on modded REV_1 board */
      pinMode(SOC_GPIO_PIN_TECHO_REV_1_3V3_PWR, INPUT_PULLDOWN);
      break;

    case NRF52_LILYGO_TECHO_REV_2:
    case NRF52_LILYGO_TECHO_PLUS:
      digitalWrite(SOC_GPIO_PIN_GNSS_WKE, LOW);

      ledOff(SOC_GPIO_LED_TECHO_REV_2_GREEN);
      ledOff(SOC_GPIO_LED_TECHO_REV_2_RED);
      ledOff(SOC_GPIO_LED_TECHO_REV_2_BLUE);

      pinMode(SOC_GPIO_LED_TECHO_REV_2_GREEN, INPUT_PULLUP);
      pinMode(SOC_GPIO_LED_TECHO_REV_2_RED,   INPUT_PULLUP);
      pinMode(SOC_GPIO_LED_TECHO_REV_2_BLUE,  INPUT_PULLUP);

      if (nRF52_board == NRF52_LILYGO_TECHO_PLUS &&
          nRF52_has_vibra == true) {
        vibra.stop();
#if SENSORLIB_VERSION == SENSORLIB_VERSION_VAL(0, 3, 1)
        vibra.setMode(1<<6); /* Standby */
#endif /* (0, 3, 1) */
#if SENSORLIB_VERSION >= SENSORLIB_VERSION_VAL(0, 4, 1)
        vibra.setMode(HapticMode::STANDBY);
#endif /* (0, 4, 1) */

        pinMode(SOC_GPIO_PIN_MOTOR_EN, INPUT);
      }

      pinMode(SOC_GPIO_PIN_SFL_HOLD,  INPUT);
      pinMode(SOC_GPIO_PIN_SFL_WP,    INPUT);
      pinMode(SOC_GPIO_PIN_SFL_SS,    INPUT);
      pinMode(SOC_GPIO_PIN_GNSS_RST,  INPUT);
      pinMode(SOC_GPIO_PIN_IO_PWR,    INPUT);
      /* Cut 3.3V power off on REV_2 board */
      // pinMode(SOC_GPIO_PIN_3V3_PWR,   INPUT_PULLDOWN);
      break;

    case NRF52_HELTEC_T114:
      pinMode(SOC_GPIO_PIN_GNSS_T114_RST, INPUT);
      digitalWrite(SOC_GPIO_PIN_GNSS_T114_WKE, LOW);

      ledOff(SOC_GPIO_LED_T114_GREEN);
      pinMode(SOC_GPIO_LED_T114_GREEN, INPUT);

      pinMode(SOC_GPIO_PIN_T114_ADC_EN,   INPUT);
      pinMode(SOC_GPIO_PIN_T114_TFT_BLGT, INPUT);
      pinMode(SOC_GPIO_PIN_T114_TFT_EN,   INPUT);
      pinMode(SOC_GPIO_PIN_T114_VEXT_EN,  INPUT);

      pinMode(SOC_GPIO_PIN_SFL_HOLD,  INPUT);
      pinMode(SOC_GPIO_PIN_SFL_WP,    INPUT);
      pinMode(SOC_GPIO_PIN_SFL_SS,    INPUT);
      break;

#if !defined(EXCLUDE_WIP)
    case NRF52_SEEED_WIO_L1:
      digitalWrite(SOC_GPIO_PIN_GNSS_L1_WKE, LOW);

      digitalWrite(SOC_GPIO_LED_L1_GREEN, 1-LED_STATE_ON);
      // digitalWrite(SOC_GPIO_LED_L1_BLUE,  1-LED_STATE_ON);

      pinMode(SOC_GPIO_LED_L1_GREEN,     INPUT);
      // pinMode(SOC_GPIO_LED_L1_BLUE,      INPUT);

      pinMode(SOC_GPIO_PIN_SFL_L1_HOLD,  INPUT);
      pinMode(SOC_GPIO_PIN_SFL_L1_WP,    INPUT);
      pinMode(SOC_GPIO_PIN_SFL_L1_SS,    INPUT);

      pinMode(SOC_GPIO_PIN_L1_VBAT_EN,   INPUT);
      break;

    case NRF52_SEEED_T2000:
      digitalWrite(SOC_GPIO_PIN_GNSS_T2000_WKE, LOW);

      digitalWrite(SOC_GPIO_LED_T2000_GREEN, 1-LED_STATE_ON);
      // digitalWrite(SOC_GPIO_LED_T2000_BLUE,  1-LED_STATE_ON);

      pinMode(SOC_GPIO_LED_T2000_GREEN,  INPUT);
      // pinMode(SOC_GPIO_LED_T2000_BLUE,   INPUT);

      pinMode(SOC_GPIO_PIN_SFL_T2000_HOLD,  INPUT);
      pinMode(SOC_GPIO_PIN_SFL_T2000_WP,    INPUT);
      pinMode(SOC_GPIO_PIN_SFL_T2000_SS,    INPUT);

      pinMode(SOC_GPIO_PIN_T2000_VBAT_EN,   INPUT);
      break;
#endif /* EXCLUDE_WIP */

    case NRF52_SEEED_T1000E:
      pinMode(SOC_GPIO_PIN_GNSS_T1000_RINT, INPUT_PULLDOWN);
      pinMode(SOC_GPIO_PIN_GNSS_T1000_SINT, INPUT_PULLDOWN);
      pinMode(SOC_GPIO_PIN_GNSS_T1000_RST,  INPUT_PULLDOWN);
      pinMode(SOC_GPIO_PIN_GNSS_T1000_VRTC, INPUT_PULLUP);
      pinMode(SOC_GPIO_PIN_GNSS_T1000_EN,   INPUT_PULLDOWN);

#if !defined(EXCLUDE_IMU)
      pinMode(SOC_GPIO_PIN_T1000_ACC_EN,    INPUT_PULLDOWN);
#endif /* EXCLUDE_IMU */
      pinMode(SOC_GPIO_PIN_T1000_BUZZER_EN, INPUT_PULLDOWN);
      pinMode(SOC_GPIO_PIN_T1000_3V3_EN,    INPUT_PULLDOWN);

      pinMode(SOC_GPIO_PIN_T1000_SS,        INPUT_PULLUP);

      digitalWrite(SOC_GPIO_LED_T1000_GREEN, 1-LED_STATE_ON);
      pinMode(SOC_GPIO_LED_T1000_GREEN,     INPUT);

      pinMode(SOC_GPIO_PIN_SFL_T1000_EN,    INPUT);
      break;

    case NRF52_ELECROW_TN_M1:
      digitalWrite(SOC_GPIO_PIN_GNSS_M1_WKE, LOW);

      digitalWrite(SOC_GPIO_LED_M1_RED,  1-LED_STATE_ON);
      digitalWrite(SOC_GPIO_LED_M1_BLUE, 1-LED_STATE_ON);

      pinMode(SOC_GPIO_LED_M1_RED,       INPUT);
      pinMode(SOC_GPIO_LED_M1_BLUE,      INPUT);
      pinMode(SOC_GPIO_LED_M1_RED_PWR,   INPUT);

      pinMode(SOC_GPIO_PIN_IO_M1_PWR,    INPUT);
      pinMode(SOC_GPIO_PIN_SFL_M1_HOLD,  INPUT);
      pinMode(SOC_GPIO_PIN_SFL_M1_WP,    INPUT);
      pinMode(SOC_GPIO_PIN_SFL_M1_SS,    INPUT);
      pinMode(SOC_GPIO_PIN_GNSS_M1_RST,  INPUT);
      break;

    case NRF52_ELECROW_TN_M3:
      digitalWrite(SOC_GPIO_PIN_GNSS_M3_WKE, LOW);
      digitalWrite(SOC_GPIO_LED_M3_RGB_PWR,  LOW);

      digitalWrite(SOC_GPIO_LED_M3_RED,  1-LED_STATE_ON);
      digitalWrite(SOC_GPIO_LED_M3_GREEN,1-LED_STATE_ON);
      digitalWrite(SOC_GPIO_LED_M3_BLUE, 1-LED_STATE_ON);

      pinMode(SOC_GPIO_LED_M3_RED,       INPUT);
      pinMode(SOC_GPIO_LED_M3_GREEN,     INPUT);
      pinMode(SOC_GPIO_LED_M3_BLUE,      INPUT);
      pinMode(SOC_GPIO_LED_M3_RGB_PWR,   INPUT);

//      pinMode(SOC_GPIO_PIN_GNSS_M3_WKE,  INPUT);
      pinMode(SOC_GPIO_PIN_GNSS_M3_RST,  INPUT);
      pinMode(SOC_GPIO_PIN_GNSS_M3_EN,   INPUT);
      pinMode(SOC_GPIO_PIN_M3_EEPROM_EN, INPUT);
      pinMode(SOC_GPIO_PIN_M3_EN1,       INPUT);
      pinMode(SOC_GPIO_PIN_M3_EN2,       INPUT);
      pinMode(SOC_GPIO_PIN_M3_ADC_EN,    INPUT);
      pinMode(SOC_GPIO_PIN_M3_ACC_EN,    INPUT);
      pinMode(SOC_GPIO_PIN_M3_TEMP_EN,   INPUT);
      break;

    case NRF52_ELECROW_TN_M6:
      digitalWrite(SOC_GPIO_PIN_GNSS_M6_WKE, LOW);

      digitalWrite(SOC_GPIO_LED_M6_RED,  1-LED_STATE_ON);
      digitalWrite(SOC_GPIO_LED_M6_BLUE, 1-LED_STATE_ON);

      pinMode(SOC_GPIO_LED_M6_RED,       INPUT);
      pinMode(SOC_GPIO_LED_M6_BLUE,      INPUT);

//      pinMode(SOC_GPIO_PIN_GNSS_M6_WKE,  INPUT);
      pinMode(SOC_GPIO_PIN_GNSS_M6_RST,  INPUT);
      pinMode(SOC_GPIO_PIN_GNSS_M6_EN,   INPUT);
      pinMode(SOC_GPIO_PIN_M6_ADC_EN,    INPUT);
      pinMode(SOC_GPIO_PIN_SFL_M6_EN,    INPUT);
      pinMode(SOC_GPIO_PIN_IO_M6_PWR,    INPUT);
      break;

    case NRF52_LILYGO_TIMPULSE_PLUS:
      pinMode(SOC_GPIO_PIN_GNSS_TIP_PWR, INPUT);

      pinMode(SOC_GPIO_PIN_SFL_TIP_HOLD, INPUT);
      pinMode(SOC_GPIO_PIN_SFL_TIP_WP,   INPUT);
      pinMode(SOC_GPIO_PIN_SFL_TIP_SS,   INPUT);

      pinMode(SOC_GPIO_PIN_TIP_RX_EN,    INPUT);
      pinMode(SOC_GPIO_PIN_TIP_TX_EN,    INPUT);

      pinMode(SOC_GPIO_PIN_TIP_MOTOR,    INPUT);
      pinMode(SOC_GPIO_PIN_TIP_VBAT_EN,  INPUT);
      pinMode(SOC_GPIO_PIN_TIP_3V3_EN,   INPUT_PULLDOWN); /* LOW ? */

#if !defined(EXCLUDE_IMU)
      if (nRF52_has_imu || hw_info.pmu == BMU_SGM41562) {
#else
      if (hw_info.pmu == BMU_SGM41562) {
#endif
        Wire1.end();
      }
      break;

    case NRF52_LILYGO_TECHO_CARD:
//      pinMode(SOC_GPIO_PIN_GNSS_TEC_WKE,  INPUT);
      pinMode(SOC_GPIO_PIN_GNSS_TEC_PWR, INPUT);
      pinMode(SOC_GPIO_PIN_GNSS_TEC_SW,  INPUT);

#if !defined(EXCLUDE_LED_RING)
      nRF52_Pixel.setPixelColor(0, LED_COLOR_BLACK);
      nRF52_Pixel.show();
#endif /* EXCLUDE_LED_RING */

      pinMode(SOC_GPIO_PIN_SFL_TEC_HOLD, INPUT);
      pinMode(SOC_GPIO_PIN_SFL_TEC_WP,   INPUT);
      pinMode(SOC_GPIO_PIN_SFL_TEC_SS,   INPUT);

      pinMode(SOC_GPIO_PIN_TEC_RX_EN,    INPUT);
      pinMode(SOC_GPIO_PIN_TEC_TX_EN,    INPUT);

      pinMode(SOC_GPIO_PIN_I2S_TEC_EN,   INPUT);
      pinMode(SOC_GPIO_PIN_I2S_TEC_PWR,  INPUT);

      pinMode(SOC_GPIO_PIN_TEC_VBAT_EN,  INPUT);
      pinMode(SOC_GPIO_PIN_TEC_3V3_EN,   INPUT_PULLDOWN); /* LOW ? */
      break;

    case NRF52_SEEED_X1:
      if (nRF52_has_vibra == true) {
        vibra.stop();
#if SENSORLIB_VERSION == SENSORLIB_VERSION_VAL(0, 3, 1)
        vibra.setMode(1<<6); /* Standby */
#endif /* (0, 3, 1) */
#if SENSORLIB_VERSION >= SENSORLIB_VERSION_VAL(0, 4, 1)
        vibra.setMode(HapticMode::STANDBY);
#endif /* (0, 4, 1) */
      }

      pinMode(SOC_GPIO_PIN_GNSS_X1_RINT,    INPUT_PULLDOWN);
      pinMode(SOC_GPIO_PIN_GNSS_X1_SINT,    INPUT_PULLDOWN);
      pinMode(SOC_GPIO_PIN_GNSS_X1_RST,     INPUT_PULLDOWN);
      pinMode(SOC_GPIO_PIN_GNSS_X1_VRTC,    INPUT_PULLUP);
      pinMode(SOC_GPIO_PIN_GNSS_X1_EN,      INPUT_PULLDOWN);

      pinMode(SOC_GPIO_PIN_X1_3V3_EN,       INPUT_PULLDOWN);

      pinMode(SOC_GPIO_PIN_X1_SS,           INPUT_PULLUP);

      pinMode(SOC_GPIO_PIN_X1_BUZZER,       INPUT_PULLDOWN);

      digitalWrite(SOC_GPIO_LED_X1_RED,     1-LED_STATE_ON);
      pinMode(SOC_GPIO_LED_X1_RED,          INPUT);
      digitalWrite(SOC_GPIO_LED_X1_GREEN,   1-LED_STATE_ON);
      pinMode(SOC_GPIO_LED_X1_GREEN,        INPUT);
      digitalWrite(SOC_GPIO_LED_X1_BLUE,    1-LED_STATE_ON);
      pinMode(SOC_GPIO_LED_X1_BLUE,         INPUT);

      pinMode(SOC_GPIO_PIN_X1_VBAT_EN,      INPUT);
      pinMode(SOC_GPIO_PIN_SFL_X1_EN,       INPUT);
      pinMode(SOC_GPIO_PIN_X1_HAPTIC_EN,    INPUT);
      pinMode(SOC_GPIO_PIN_X1_RTC_EN,       INPUT);
      break;

    case NRF52_NORDIC_PCA10059:
    default:
//      ledOff(SOC_GPIO_LED_PCA10059_GREEN);
      ledOff(SOC_GPIO_LED_PCA10059_RED);
      ledOff(SOC_GPIO_LED_PCA10059_BLUE);
      ledOff(SOC_GPIO_LED_PCA10059_STATUS);

//      pinMode(SOC_GPIO_LED_PCA10059_GREEN,  INPUT);
      pinMode(SOC_GPIO_LED_PCA10059_RED,    INPUT);
      pinMode(SOC_GPIO_LED_PCA10059_BLUE,   INPUT);
      pinMode(SOC_GPIO_LED_PCA10059_STATUS, INPUT);
      break;
  }

  Serial_GNSS_In.end();

  // pinMode(SOC_GPIO_PIN_GNSS_RX, INPUT);
  // pinMode(SOC_GPIO_PIN_GNSS_TX, INPUT);

  // pinMode(SOC_GPIO_PIN_BATTERY, INPUT);

#if !defined(ARDUINO_ARCH_MBED) && !defined(ARDUINO_ARCH_ZEPHYR)
  if (i2c != nullptr) Wire.end();
#endif /* ARDUINO_ARCH_MBED */

  switch (nRF52_board)
  {
    case NRF52_HELTEC_T114:
      pinMode(SOC_GPIO_PIN_T114_SDA_EXT, INPUT);
      pinMode(SOC_GPIO_PIN_T114_SCL_EXT, INPUT);
      break;

#if !defined(EXCLUDE_WIP)
    case NRF52_SEEED_WIO_L1:
      pinMode(SOC_GPIO_PIN_L1_OLED_SDA, INPUT);
      pinMode(SOC_GPIO_PIN_L1_OLED_SCL, INPUT);
      break;

    case NRF52_SEEED_T2000:
      pinMode(SOC_GPIO_PIN_T2000_SDA, INPUT);
      pinMode(SOC_GPIO_PIN_T2000_SCL, INPUT);
      break;

    case NRF52_HELTEC_T1:
      pinMode(SOC_GPIO_PIN_T1_SDA, INPUT);
      pinMode(SOC_GPIO_PIN_T1_SCL, INPUT);
      break;

    case NRF52_ELECROW_TN_M8:
      pinMode(SOC_GPIO_PIN_M8_SDA, INPUT);
      pinMode(SOC_GPIO_PIN_M8_SCL, INPUT);
      break;
#endif /* EXCLUDE_WIP */

    case NRF52_SEEED_T1000E:
      pinMode(SOC_GPIO_PIN_T1000_SDA, INPUT);
      pinMode(SOC_GPIO_PIN_T1000_SCL, INPUT);
      break;

    case NRF52_ELECROW_TN_M3:
      pinMode(SOC_GPIO_PIN_M3_SDA, INPUT);
      pinMode(SOC_GPIO_PIN_M3_SCL, INPUT);
      break;

    case NRF52_ELECROW_TN_M6:
      pinMode(SOC_GPIO_PIN_M6_SDA, INPUT);
      pinMode(SOC_GPIO_PIN_M6_SCL, INPUT);
      break;

    case NRF52_LILYGO_TIMPULSE_PLUS:
      pinMode(SOC_GPIO_PIN_TIP_OLED_SDA, INPUT);
      pinMode(SOC_GPIO_PIN_TIP_OLED_SCL, INPUT);
      pinMode(SOC_GPIO_PIN_TIP_SDA,      INPUT);
      pinMode(SOC_GPIO_PIN_TIP_SCL,      INPUT);
      break;

    case NRF52_LILYGO_TECHO_CARD:
      pinMode(SOC_GPIO_PIN_TEC_SDA, INPUT);
      pinMode(SOC_GPIO_PIN_TEC_SCL, INPUT);
      break;

    case NRF52_SEEED_X1:
      pinMode(SOC_GPIO_PIN_X1_SDA,     INPUT);
      pinMode(SOC_GPIO_PIN_X1_SCL,     INPUT);
      pinMode(SOC_GPIO_PIN_X1_RTC_SDA, INPUT);
      pinMode(SOC_GPIO_PIN_X1_RTC_SCL, INPUT);
      break;

    case NRF52_LILYGO_TECHO_REV_0:
    case NRF52_LILYGO_TECHO_REV_1:
    case NRF52_LILYGO_TECHO_REV_2:
    case NRF52_LILYGO_TECHO_PLUS:
    case NRF52_ELECROW_TN_M1:
    case NRF52_NORDIC_PCA10059:
    default:
      pinMode(SOC_GPIO_PIN_SDA, INPUT);
      pinMode(SOC_GPIO_PIN_SCL, INPUT);
      break;
  }

  // pinMode(SOC_GPIO_PIN_MOSI, INPUT);
  // pinMode(SOC_GPIO_PIN_MISO, INPUT);
  // pinMode(SOC_GPIO_PIN_SCK,  INPUT);
  pinMode(lmic_pins.nss,        INPUT_PULLUP);
  // pinMode(lmic_pins.busy,       INPUT);
  pinMode(lmic_pins.rst,        INPUT);

  int mode_button_pin;

  switch (nRF52_board)
  {
#if !defined(EXCLUDE_WIP)
    case NRF52_SEEED_WIO_L1:
      mode_button_pin = SOC_GPIO_PIN_L1_BUTTON;
      break;

    case NRF52_SEEED_T2000:
      mode_button_pin = SOC_GPIO_PIN_T2000_BUTTON;
      break;

    case NRF52_HELTEC_T1:
      mode_button_pin = SOC_GPIO_PIN_T1_BUTTON1;
      break;
#endif /* EXCLUDE_WIP */

    case NRF52_SEEED_T1000E:
    case NRF52_SEEED_X1:
      mode_button_pin = SOC_GPIO_PIN_T1000_BUTTON;
      break;

    case NRF52_HELTEC_T114:
      mode_button_pin = SOC_GPIO_PIN_T114_BUTTON;
      break;

    case NRF52_ELECROW_TN_M1:
      mode_button_pin = SOC_GPIO_PIN_M1_BUTTON1;
      break;

    case NRF52_ELECROW_TN_M3:
      mode_button_pin = SOC_GPIO_PIN_M3_BUTTON;
      break;

    case NRF52_ELECROW_TN_M6:
      mode_button_pin = SOC_GPIO_PIN_M6_BUTTON;
      break;

    case NRF52_ELECROW_TN_M8:
      mode_button_pin = SOC_GPIO_PIN_M8_ENC_BTN;
      break;

    case NRF52_LILYGO_TIMPULSE_PLUS:
      mode_button_pin = SOC_GPIO_PIN_TIP_PAD;
      break;

    case NRF52_LILYGO_TECHO_CARD:
      mode_button_pin = SOC_GPIO_PIN_TEC_BUTTON;
      break;

    case NRF52_NORDIC_PCA10059:
      mode_button_pin = SOC_GPIO_PIN_PCA10059_BUTTON;
      break;

    case NRF52_LILYGO_TECHO_REV_0:
    case NRF52_LILYGO_TECHO_REV_1:
    case NRF52_LILYGO_TECHO_REV_2:
    case NRF52_LILYGO_TECHO_PLUS:
    default:
      mode_button_pin = SOC_GPIO_PIN_TECHO_REV_2_BUTTON;
      break;
  }

  // pinMode(SOC_GPIO_PIN_PAD,    INPUT);
  pinMode(mode_button_pin, nRF52_board == NRF52_LILYGO_TECHO_REV_1 ? INPUT_PULLUP   :
                           nRF52_board == NRF52_SEEED_T1000E       ? INPUT_PULLDOWN :
                           nRF52_board == NRF52_SEEED_X1           ? INPUT_PULLDOWN :
                           nRF52_board == NRF52_ELECROW_TN_M6      ? INPUT_PULLUP   :
                           INPUT);
  while (digitalRead(mode_button_pin) == (nRF52_board == NRF52_SEEED_T1000E ||
                                          nRF52_board == NRF52_SEEED_X1     ?
                                          HIGH : LOW));
  delay(100);

#if defined(USE_TINYUSB)
  Serial1.end();

  // pinMode(SOC_GPIO_PIN_CONS_RX, INPUT);
  // pinMode(SOC_GPIO_PIN_CONS_TX, INPUT);
#endif

  // setup wake-up pins
  switch (reason)
  {
  case SOFTRF_SHUTDOWN_BUTTON:
  case SOFTRF_SHUTDOWN_LOWBAT:
    NRF_POWER->GPREGRET = DFU_MAGIC_SKIP;
#if !defined(ARDUINO_ARCH_MBED) && !defined(ARDUINO_ARCH_ZEPHYR)
    pinMode(mode_button_pin, nRF52_board == NRF52_SEEED_T1000E ||
                             nRF52_board == NRF52_SEEED_X1     ?
                             INPUT_PULLDOWN_SENSE /* INPUT_SENSE_HIGH */ :
                             INPUT_PULLUP_SENSE   /* INPUT_SENSE_LOW  */);
#endif /* ARDUINO_ARCH_MBED */
    break;
#if defined(USE_SERIAL_DEEP_SLEEP)
  case SOFTRF_SHUTDOWN_NMEA:
#if !defined(ARDUINO_ARCH_MBED) && !defined(ARDUINO_ARCH_ZEPHYR)
    pinMode(SOC_GPIO_PIN_CONS_RX, INPUT_PULLUP_SENSE /* INPUT_SENSE_LOW */);
#endif /* ARDUINO_ARCH_MBED */
    break;
#endif
  default:
    break;
  }

  Serial.end();

  nRF52_system_off();
}

static void nRF52_reset()
{
#if !defined(ARDUINO_ARCH_MBED) && !defined(ARDUINO_ARCH_ZEPHYR)
  if (nrf_wdt_started(NRF_WDT)) {
    // When WDT is active - CRV, RREN and CONFIG are blocked
    // There is no way to stop/disable watchdog using source code
    // It can only be reset by WDT timeout, Pin reset, Power reset

    switch (hw_info.display)
    {
#if defined(USE_EPAPER)
    case DISPLAY_EPD_1_54:
#if defined(USE_EPD_TASK)
      while (EPD_update_in_progress != EPD_UPDATE_NONE) { delay(100); }
//    while (!SoC->Display_lock()) { delay(10); }
#endif

      EPD_Message("PLEASE,", "WAIT..");
      break;
#endif /* USE_EPAPER */

#if defined(USE_TFT)
    case DISPLAY_TFT_TTGO_135:
      if (tft) {
        const char *msg = "WAIT";

        tft->fillScreen(TFT_NAVY);
        tft->setTextFont(4);
        tft->setTextSize(2);

        tft->setTextColor(TFT_WHITE, TFT_NAVY);

        uint16_t tbw = tft->textWidth(msg);
        uint16_t tbh = tft->fontHeight();

        tft->setCursor((tft->width() - tbw)/2, (tft->height() - tbh)/2);
        tft->print(msg);
      }
      break;
#endif /* USE_TFT */

#if defined(USE_OLED)
#if !defined(EXCLUDE_OLED_049)
    case DISPLAY_OLED_0_49:
      if (u8x8) {
        u8x8->clear();
        u8x8->draw2x2String(4, 5, "WAIT");
      }
      break;
#endif /* EXCLUDE_OLED_049 */
#endif /* USE_OLED */

    case DISPLAY_NONE:
    default:
      break;
    }

    while (true) { delay(100); }
  } else {
    NVIC_SystemReset();
  }
#else
  /* TBD */
#endif /* ARDUINO_ARCH_MBED */
}

static uint32_t nRF52_getChipId()
{
#if !defined(SOFTRF_ADDRESS)
  uint32_t id = DEVICE_ID_LOW;

  return DevID_Mapper(id);
#else
  return (SOFTRF_ADDRESS & 0xFFFFFFFFU );
#endif
}

static void* nRF52_getResetInfoPtr()
{
  return (void *) &reset_info;
}

static String nRF52_getResetInfo()
{
  switch (reset_info.reason)
  {
    default                     : return F("No reset information available");
  }
}

static String nRF52_getResetReason()
{
  switch (reset_info.reason)
  {
    case REASON_DEFAULT_RST       : return F("DEFAULT");
    case REASON_WDT_RST           : return F("WDT");
    case REASON_EXCEPTION_RST     : return F("EXCEPTION");
    case REASON_SOFT_WDT_RST      : return F("SOFT_WDT");
    case REASON_SOFT_RESTART      : return F("SOFT_RESTART");
    case REASON_DEEP_SLEEP_AWAKE  : return F("DEEP_SLEEP_AWAKE");
    case REASON_EXT_SYS_RST       : return F("EXT_SYS");
    default                       : return F("NO_MEAN");
  }
}

static uint32_t nRF52_getFreeHeap()
{
#if !defined(ARDUINO_ARCH_MBED) && !defined(ARDUINO_ARCH_ZEPHYR)
  return dbgHeapTotal() - dbgHeapUsed();
#else
  return 0; /* TBD */
#endif /* ARDUINO_ARCH_MBED */
}

static long nRF52_random(long howsmall, long howBig)
{
  return random(howsmall, howBig);
}

#if defined(USE_USB_MIDI)
byte note_sequence[] = {62,65,69,65,67,67,65,64,69,69,67,67,62,62};
#endif /* USE_USB_MIDI */

static void nRF52_Sound_test(int var)
{
#if defined(USE_USB_MIDI)
  if (USBDevice.mounted() && settings->volume != BUZZER_OFF) {
    unsigned int position = 0;
    unsigned int current  = 0;

    for (; position <= sizeof(note_sequence); position++) {
      // Setup variables for the current and previous
      // positions in the note sequence.
      current = position;
      // If we currently are at position 0, set the
      // previous position to the last note in the sequence.
      unsigned int previous = (current == 0) ? (sizeof(note_sequence)-1) : current - 1;

      // Send Note On for current position at full velocity (127) on channel 1.
      MIDI_USB.sendNoteOn(note_sequence[current], 127, MIDI_CHANNEL_TRAFFIC);

      // Send Note Off for previous note.
      MIDI_USB.sendNoteOff(note_sequence[previous], 0, MIDI_CHANNEL_TRAFFIC);

      delay(286);
    }

    MIDI_USB.sendNoteOff(note_sequence[current], 0, MIDI_CHANNEL_TRAFFIC);
  }
#endif /* USE_USB_MIDI */

  if ((nRF52_board == NRF52_LILYGO_TECHO_PLUS ||
       nRF52_board == NRF52_SEEED_X1)         &&
       nRF52_has_vibra == true) {
    vibra.setWaveform(0, 75); /* Transition Ramp Down Short Smooth 2 - 100 to 0% */
    vibra.setWaveform(1, 0);
    vibra.run();
  }

#if defined(USE_PWM_SOUND)
  if (SOC_GPIO_PIN_BUZZER != SOC_UNUSED_PIN && settings->volume != BUZZER_OFF) {
    tone(SOC_GPIO_PIN_BUZZER, 440,  500); delay(500);
    tone(SOC_GPIO_PIN_BUZZER, 640,  500); delay(500);
    tone(SOC_GPIO_PIN_BUZZER, 840,  500); delay(500);
    tone(SOC_GPIO_PIN_BUZZER, 1040, 500); delay(600);

    noTone(SOC_GPIO_PIN_BUZZER);
    pinMode(SOC_GPIO_PIN_BUZZER, nRF52_board == NRF52_SEEED_X1 ?
                                 INPUT_PULLDOWN : INPUT);
  }
#endif /* USE_PWM_SOUND */
}

#if defined(USE_BLE_MIDI)
extern BLEMidi blemidi;
extern midi::MidiInterface<BLEMidi> MIDI_BLE;
#endif /* USE_BLE_MIDI */

static void nRF52_Sound_tone(int hz, uint8_t volume)
{
#if defined(USE_PWM_SOUND)
  if (SOC_GPIO_PIN_BUZZER != SOC_UNUSED_PIN && volume != BUZZER_OFF) {
    if (hz > 0) {
      tone(SOC_GPIO_PIN_BUZZER, hz, ALARM_TONE_MS);
    } else {
      noTone(SOC_GPIO_PIN_BUZZER);
      pinMode(SOC_GPIO_PIN_BUZZER, nRF52_board == NRF52_SEEED_X1 ?
                                   INPUT_PULLDOWN : INPUT);
    }
  }
#endif /* USE_PWM_SOUND */

#if defined(USE_USB_MIDI)
  if (USBDevice.mounted() && volume != BUZZER_OFF) {
    if (hz > 0) {
      MIDI_USB.sendNoteOn (60, 127, MIDI_CHANNEL_TRAFFIC); // 60 == middle C
    } else {
      MIDI_USB.sendNoteOff(60,   0, MIDI_CHANNEL_TRAFFIC);
    }
  }
#endif /* USE_USB_MIDI */

#if defined(USE_BLE_MIDI)
  if (volume != BUZZER_OFF  &&
      Bluefruit.connected() &&
      blemidi.notifyEnabled()) {
    if (hz > 0) {
      MIDI_BLE.sendNoteOn (60, 127, MIDI_CHANNEL_TRAFFIC); // 60 == middle C
    } else {
      MIDI_BLE.sendNoteOff(60,   0, MIDI_CHANNEL_TRAFFIC);
    }
  }
#endif /* USE_BLE_MIDI */
}

static void nRF52_WiFi_set_param(int ndx, int value)
{
  /* NONE */
}

static void nRF52_WiFi_transmit_UDP(int port, byte *buf, size_t size)
{
  /* NONE */
}

static bool nRF52_EEPROM_begin(size_t size)
{
#if !defined(EXCLUDE_EEPROM)
  if (size > EEPROM.length()) {
    return false;
  }

  EEPROM.begin();
#endif /* EXCLUDE_EEPROM */

  return true;
}

static void nRF52_EEPROM_extension(int cmd)
{
  uint8_t *raw = (uint8_t *) ui;

  switch (cmd)
  {
    case EEPROM_EXT_STORE:
#if !defined(EXCLUDE_EEPROM)
      for (int i=0; i<sizeof(ui_settings_t); i++) {
        EEPROM.write(sizeof(eeprom_t) + i, raw[i]);
      }
#endif /* EXCLUDE_EEPROM */
      return;
    case EEPROM_EXT_DEFAULTS:
      ui->adapter      = 0;
      ui->connection   = 0;
      ui->units        = UNITS_METRIC;
      ui->zoom         = ZOOM_MEDIUM;
      ui->protocol     = PROTOCOL_NMEA;
      ui->baudrate     = 0;
      strcpy(ui->server, "");
      strcpy(ui->key,    "");
      ui->rotate       = ROTATE_0;
      ui->orientation  = DIRECTION_TRACK_UP;
      ui->adb          = DB_OGN;
      ui->idpref       = ID_TYPE;
      ui->vmode        = VIEW_MODE_STATUS;
      ui->voice        = VOICE_OFF;
      ui->aghost       = ANTI_GHOSTING_OFF;
      ui->filter       = TRAFFIC_FILTER_OFF;
      ui->power_save   = 0;
      ui->team         = 0;

#if defined(USE_PWM_SOUND)
      if (nRF52_board == NRF52_LILYGO_TECHO_PLUS) {
        settings->volume = BUZZER_VOLUME_FULL;
      }
#endif /* USE_PWM_SOUND */
      break;
    case EEPROM_EXT_LOAD:
    default:
#if !defined(EXCLUDE_EEPROM)
      for (int i=0; i<sizeof(ui_settings_t); i++) {
        raw[i] = EEPROM.read(sizeof(eeprom_t) + i);
      }
#endif /* EXCLUDE_EEPROM */
#if !defined(ARDUINO_ARCH_MBED) && !defined(ARDUINO_ARCH_ZEPHYR)
      if ( nRF52_has_spiflash && FATFS_is_mounted ) {
        File32 file = fatfs.open(SETTINGS_JSON_PATH, FILE_READ);

        if (file) {
          // StaticJsonBuffer<NRF52_JSON_BUFFER_SIZE> nRF52_jsonBuffer;

          JsonObject &root = nRF52_jsonBuffer.parseObject(file);

          if (root.success()) {
            JsonVariant msg_class = root["class"];

            if (msg_class.success()) {
              const char *msg_class_s = msg_class.as<char*>();

              if (!strcmp(msg_class_s,"SOFTRF")) {
                parseSettings  (root);
                parseUISettings(root);

                JsonVariant adb = root["adb"];
                if (adb.success()) {
                  const char * adb_s = adb.as<char*>();
                  if (!strcmp(adb_s,"NONE")) {
                    ui_settings.adb = DB_NONE;
                  } else if (!strcmp(adb_s,"FLN")) {
                    ui_settings.adb = DB_FLN;
                  } else if (!strcmp(adb_s,"OGN")) {
                    ui_settings.adb = DB_OGN;
                  }
                }

#if defined(ENABLE_PROL)
                JsonVariant fromcall = root["fromcall"];
                if (fromcall.success()) {
                  const char * fromcall_s = fromcall.as<char*>();
                  if (strlen(fromcall_s) < sizeof(APRS_FromCall)) {
                    strncpy(APRS_FromCall, fromcall_s, sizeof(APRS_FromCall));
                  }
                }
                JsonVariant tocall = root["tocall"];
                if (tocall.success()) {
                  const char * tocall_s = tocall.as<char*>();
                  if (strlen(tocall_s) < sizeof(APRS_ToCall)) {
                    strncpy(APRS_ToCall, tocall_s, sizeof(APRS_ToCall));
                  }
                }
                JsonVariant path = root["path"];
                if (path.success()) {
                  const char * path_s = path.as<char*>();
                  if (strlen(path_s) < sizeof(APRS_Path)) {
                    strncpy(APRS_Path, path_s, sizeof(APRS_Path));
                  }
                }
#endif /* ENABLE_PROL */
#if defined(ENABLE_REMOTE_ID)
                JsonVariant opid = root["uas_opid"];
                if (opid.success()) {
                  const char * opid_s = opid.as<char*>();
                  if (strlen(opid_s) < sizeof(RID_Operator_ID)) {
                    strncpy(RID_Operator_ID, opid_s, sizeof(RID_Operator_ID));
                  }
                }
                JsonVariant drid = root["uas_drid"];
                if (drid.success()) {
                  const char * drid_s = drid.as<char*>();
                  if (strlen(drid_s) < sizeof(RID_Drone_ID)) {
                    strncpy(RID_Drone_ID, drid_s, sizeof(RID_Drone_ID));
                  }
                }
#endif /* ENABLE_REMOTE_ID */
              }
            }
          }
          file.close();
        }
      }
#endif /* ARDUINO_ARCH_MBED */

#if defined(USE_WEBUSB_SETTINGS) && !defined(USE_WEBUSB_SERIAL)

      usb_web.setLandingPage(&landingPage);
      usb_web.begin();

#endif /* USE_WEBUSB_SETTINGS */

      if (settings->mode != SOFTRF_MODE_NORMAL
#if !defined(EXCLUDE_TEST_MODE)
          &&
          settings->mode != SOFTRF_MODE_TXRX_TEST
#endif /* EXCLUDE_TEST_MODE */
          ) {
        settings->mode = SOFTRF_MODE_NORMAL;
      }

      if (settings->nmea_out == NMEA_UDP  ||
          settings->nmea_out == NMEA_TCP ) {
        settings->nmea_out = NMEA_BLUETOOTH;
      }
      if (settings->gdl90 == GDL90_UDP) {
        settings->gdl90 = GDL90_BLUETOOTH;
      }
      if (settings->d1090 == D1090_UDP) {
        settings->d1090 = D1090_BLUETOOTH;
      }

      /* AUTO and UK RF bands are deprecated since Release v1.3 */
      if (settings->band == RF_BAND_AUTO || settings->band == RF_BAND_UK) {
        settings->band = RF_BAND_EU;
      }

#if defined(USE_TINYUSB)
      switch (nRF52_board)
      {
        /* Serial-Out pins are not exposed on these models */
        case NRF52_ELECROW_TN_M1:
        case NRF52_ELECROW_TN_M3:
        case NRF52_LILYGO_TECHO_PLUS:
        case NRF52_LILYGO_TECHO_CARD:
        case NRF52_LILYGO_TIMPULSE_PLUS:
        case NRF52_SEEED_T1000E:
        case NRF52_SEEED_X1:
          if (settings->nmea_out == NMEA_UART) {
            settings->nmea_out = NMEA_BLUETOOTH;
          }
          if (settings->gdl90 == GDL90_UART) {
            settings->gdl90 = GDL90_BLUETOOTH;
          }
          if (settings->d1090 == D1090_UART) {
            settings->d1090 = D1090_BLUETOOTH;
          }
          break;

        case NRF52_LILYGO_TECHO_REV_0:
        case NRF52_LILYGO_TECHO_REV_1:
        case NRF52_LILYGO_TECHO_REV_2:
        case NRF52_HELTEC_T114:
        case NRF52_ELECROW_TN_M6:
        case NRF52_NORDIC_PCA10059:
        default:
          break;
      }
#endif /* USE_TINYUSB */
      break;
  }
}
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
