lyusupov/SoftRF/software/firmware/source/SoftRF/src/platform/nRF52.h

/*
 * Platform_nRF52.h
 * Copyright (C) 2020-2026 Linar Yusupov
 *
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
 * You should have received a copy of the GNU General Public License
 * along with this program.  If not, see <http://www.gnu.org/licenses/>.
 */

#if defined(ARDUINO_ARCH_NRF52)  || defined(ARDUINO_ARCH_NRF52840) || \
   (defined(ARDUINO_ARCH_ZEPHYR) && defined(NRF52840_XXAA))

#ifndef PLATFORM_NRF52_H
#define PLATFORM_NRF52_H

#include <avr/dtostrf.h>

/* Maximum of tracked flying objects is now SoC-specific constant */
#define MAX_TRACKING_OBJECTS    8

#define DEFAULT_SOFTRF_MODEL    SOFTRF_MODEL_BADGE

#define isValidFix()            isValidGNSSFix()

#define uni_begin()             strip.begin()
#define uni_show()              strip.show()
#define uni_setPixelColor(i, c) strip.setPixelColor(i, c)
#define uni_numPixels()         strip.numPixels()
#define uni_Color(r,g,b)        strip.Color(r,g,b)
#define color_t                 uint32_t

#define snprintf_P              snprintf
#define EEPROM_commit()         {}

// State when LED is litted
#if defined(LED_STATE_ON)
#undef  LED_STATE_ON
#define LED_STATE_ON            (hw_info.model == SOFTRF_MODEL_CARD     || \
                                 hw_info.model == SOFTRF_MODEL_CARD_MK3 || \
                                 hw_info.model == SOFTRF_MODEL_HANDHELD || \
                                 hw_info.model == SOFTRF_MODEL_SOLARIS  || \
                                 hw_info.model == SOFTRF_MODEL_DECENT    ? \
                                 HIGH : LOW)
#else
#define LED_STATE_ON            LOW
#endif /* LED_STATE_ON */

#define SerialOutput            Serial1
#define USBSerial               Serial
#if !defined(ARDUINO_ARCH_ZEPHYR)
#define Serial_GNSS_In          Serial2
#else
#define Serial_GNSS_In          Serial1 /* TBD */
#endif /* ARDUINO_ARCH_ZEPHYR */
#define Serial_GNSS_Out         Serial_GNSS_In
#define UATSerial               Serial1

enum rst_reason {
  REASON_DEFAULT_RST      = 0,  /* normal startup by power on */
  REASON_WDT_RST          = 1,  /* hardware watch dog reset */
  REASON_EXCEPTION_RST    = 2,  /* exception reset, GPIO status won't change */
  REASON_SOFT_WDT_RST     = 3,  /* software watch dog reset, GPIO status won't change */
  REASON_SOFT_RESTART     = 4,  /* software restart ,system_restart , GPIO status won't change */
  REASON_DEEP_SLEEP_AWAKE = 5,  /* wake up from deep-sleep */
  REASON_EXT_SYS_RST      = 6   /* external system reset */
};
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
